computergeek1507/PB_16/Pi_Zero_24_Diff_SMD/README.md

# Copyright and Disclaimer
Copyright: Scott Hanson

This documentation describes Open Hardware and is licensed under the CERN Open Hardware Licence Version 2 - Strongly Reciprocal. (CERN-OHL-S)

You may redistribute and modify this documentation under the terms of the CERN OHL-S-v2 (https://ohwr.org/cern_ohl_s_v2.txt). This documentation is distributed WITHOUT ANY EXPRESS OR IMPLIED WARRANTY, INCLUDING OF MERCHANTABILITY, SATISFACTORY QUALITY AND FITNESS FOR A PARTICULAR PURPOSE. Please see the CERN OHL v2-S for applicable conditions

**Under CERN OHL-S-v2, derivative work must be publicy released as defined in subsection 3.3**

# Pi Zero 24 Diff

**Never Built or tested**

The Pi Zero 24 Diff is a surface mount(SMD) controller with 6 remote receiver port. A total of 24 pixel outputs. All the design files are open source and available on github.

## [Interactive BOM](https://computergeek1507.github.io/PB_16/Pi_Zero_24_Diff_SMD/bom/ibom)

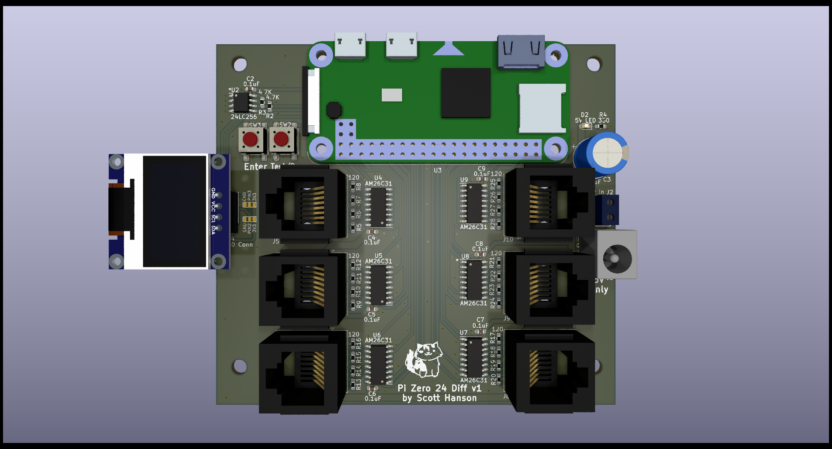
[picture p17: Pi_Zero_24_Diff_SMD/Pi_Zero_24_Diff.png]
Image of Pi Zero 24 Diff
