computergeek1507/PB_16/Pi_CM4_16_SMD/README.md

# Copyright and Disclaimer
Copyright: Scott Hanson

This documentation describes Open Hardware and is licensed under the CERN Open Hardware Licence Version 2 - Strongly Reciprocal. (CERN-OHL-S)

You may redistribute and modify this documentation under the terms of the CERN OHL-S-v2 (https://ohwr.org/cern_ohl_s_v2.txt). This documentation is distributed WITHOUT ANY EXPRESS OR IMPLIED WARRANTY, INCLUDING OF MERCHANTABILITY, SATISFACTORY QUALITY AND FITNESS FOR A PARTICULAR PURPOSE. Please see the CERN OHL v2-S for applicable conditions

**Under CERN OHL-S-v2, derivative work must be publicy released as defined in subsection 3.3**

# Pi CM4 16

**Never Built or tested**

The Pi CM4 16 is a surface mount(SMD) controller with 16 local pixel ports and one remote receiver port(4 remote ports). A total of 20 pixel outputs. All the design files are open source and available on github.

## [Interactive BOM](https://computergeek1507.github.io/PB_16/Pi_CM4_16_SMD/bom/ibom)

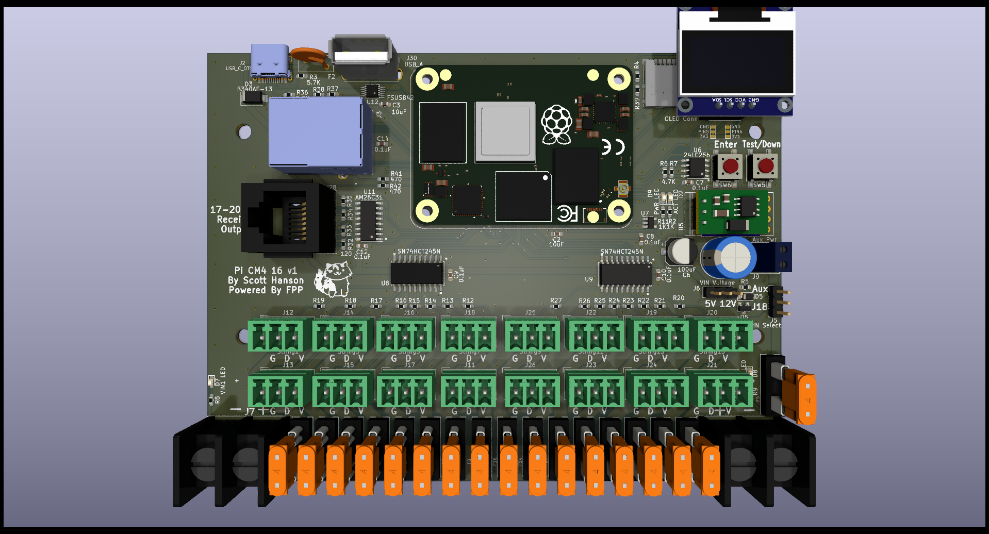
[picture p18: Pi_CM4_16_SMD/Pi_CM4_16.png]
Image of PB Pi Zero W 16
