computergeek1507/PB_16/Pi_Adapter/README.md

# Copyright and Disclaimer
Copyright: Scott Hanson

This documentation describes Open Hardware and is licensed under the CERN OHL v. 1.2.

You may redistribute and modify this documentation under the terms of the CERN OHL v.1.2. (http://ohwr.org/cernohl). This documentation is distributed WITHOUT ANY EXPRESS OR IMPLIED WARRANTY, INCLUDING OF MERCHANTABILITY, SATISFACTORY QUALITY AND FITNESS FOR A PARTICULAR PURPOSE. Please see the CERN OHL v.1.2 for applicable conditions

# Pi Expansion

Expansion breakout for a Raspberry Pi. Open source applications were used to create this PCB. [KiCad](http://kicad.org/) was used for the PCB design, and [LibreOffice](https://www.libreoffice.org/) for the documentation.

To order your own PCB upload the gerber.zip file to your favorite PCB manufacture of choice, I personally use [jlcpcb.com](https://jlcpcb.com/).

### Features
* 16 Port Expansion
* OLED Display header
* 2 pin GPIO Header for Push Button or Relay Support
* 5v Header

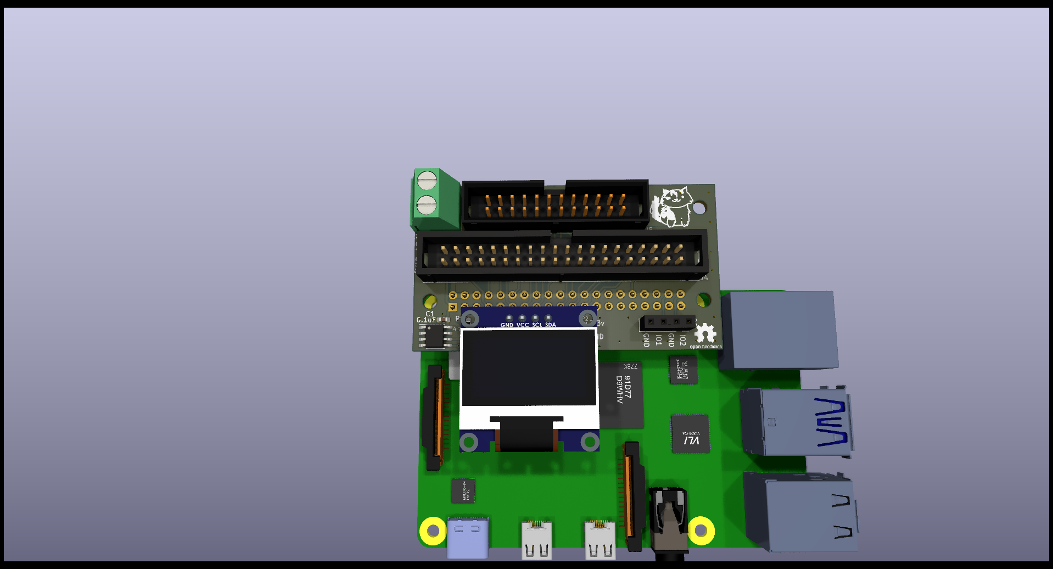
[picture p21: Pi_Adapter/Pi_Adapter.png]
Image of PI Adapter
