computergeek1507/PB_16/16_Expansion_SMD/README.md

# Copyright and Disclaimer
Copyright: Scott Hanson

This documentation describes Open Hardware and is licensed under the CERN Open Hardware License Version 2 - Strongly Reciprocal. (CERN-OHL-S)

You may redistribute and modify this documentation under the terms of the CERN OHL-S-v2 (https://ohwr.org/cern_ohl_s_v2.txt). This documentation is distributed WITHOUT ANY EXPRESS OR IMPLIED WARRANTY, INCLUDING OF MERCHANTABILITY, SATISFACTORY QUALITY AND FITNESS FOR A PARTICULAR PURPOSE. Please see the CERN OHL v2-S for applicable conditions

**Under CERN OHL-S-v2, derivative work must be publicly released as defined in subsection 3.3**

# 16 Expansion SMD

The "16 Expansion SMD" is a 16 port output board for the PB16.  All the design files are open source and available on github.

To order PCBs upload the "GERBER-PB_16.zip" file in the "jlcpcb\gerber" folder. Enable the SMD service, 'BOM-PB_16.csv' is the SMD BOM and 'POS-PB_16.csv' is the SMD CPL position file.

## [Part BOM](https://github.com/computergeek1507/PB_16/raw/master/16_Expansion_SMD/16_Expansion_BOM.ods)

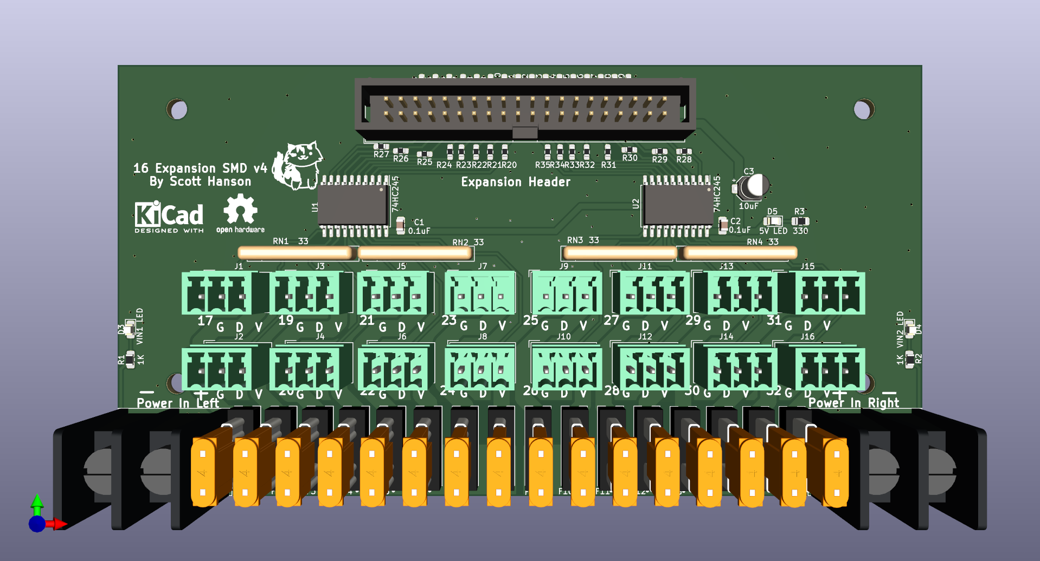
[picture p24: 16_Expansion_SMD/16_Expansion.png]
Image of 16 Expansion
