computergeek1507/PB_16/BBB_16_Expansion/README.md

# Copyright and Disclaimer
Copyright: Scott Hanson

This documentation describes Open Hardware and is licensed under the CERN Open Hardware License Version 2 - Strongly Reciprocal. (CERN-OHL-S)

You may redistribute and modify this documentation under the terms of the CERN OHL-S-v2 (https://ohwr.org/cern_ohl_s_v2.txt). This documentation is distributed WITHOUT ANY EXPRESS OR IMPLIED WARRANTY, INCLUDING OF MERCHANTABILITY, SATISFACTORY QUALITY AND FITNESS FOR A PARTICULAR PURPOSE. Please see the CERN OHL v2-S for applicable conditions

**Under CERN OHL-S-v2, derivative work must be publicly released as defined in subsection 3.3**

# BBB 16 Expansion

**This board is untested, use at your own risk**

The BBB16 Expansion is a version of the BBB16 for the Falcon v4 Expansion Boards. It can be used with three expansion boards, 48 outputs. The design is surface mount. All the design files are open source and available on github.

To order PCBs upload the "GERBER-BBB_16_Expansion.zip" file in the "jlcpcb\gerber" folder to jlcpcb.com. Enable the SMD service, 'BOM-BBB_16_Expansion.csv' is the SMD BOM and 'POS-BBB_16_Expansion.csv' is the SMD CPL position file.

## [Part BOM](https://github.com/computergeek1507/PB_16/raw/master/BBB_16_Expansion/BBB_16_Expansion_BOM.ods)

## [Interactive BOM](https://computergeek1507.github.io/PB_16/BBB_16_Expansion/bom/ibom)

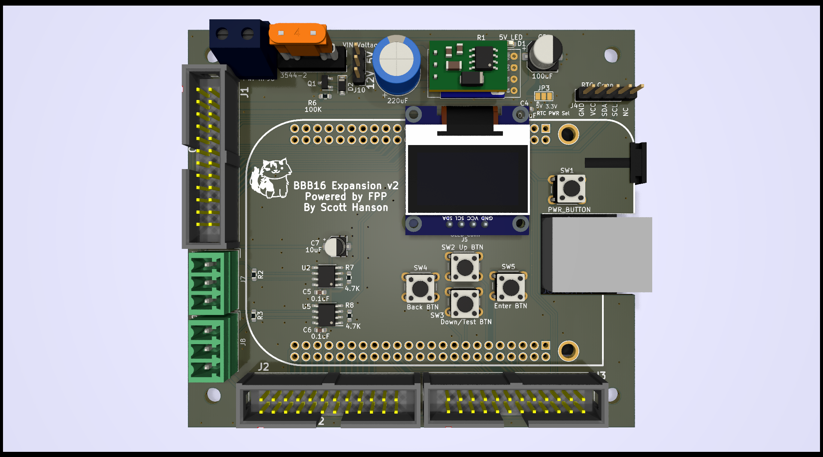
[picture p26: BBB_16_Expansion/BBB_16_Expansion.png]
Image of BBB16 Expansion Out
