computergeek1507/PB_16/BBB_16_Flex/README.md

# Copyright and Disclaimer
Copyright: Scott Hanson

This documentation describes Open Hardware and is licensed under the CERN Open Hardware License Version 2 - Strongly Reciprocal. (CERN-OHL-S)

You may redistribute and modify this documentation under the terms of the CERN OHL-S-v2 (https://ohwr.org/cern_ohl_s_v2.txt). This documentation is distributed WITHOUT ANY EXPRESS OR IMPLIED WARRANTY, INCLUDING OF MERCHANTABILITY, SATISFACTORY QUALITY AND FITNESS FOR A PARTICULAR PURPOSE. Please see the CERN OHL v2-S for applicable conditions

**Under CERN OHL-S-v2, derivative work must be publicly released as defined in subsection 3.3**

# BBB 16 Flex

The BBB16 Flex is a version of the BBB16 for the HolidayCoro Flex System. It can be used with all three flex boards, 48 outputs. The design is surface mount. All the design files are open source and available on github.

## [Part BOM](https://github.com/computergeek1507/PB_16/raw/master/BBB_16_Flex/BBB_16_Flex_BOM.ods)

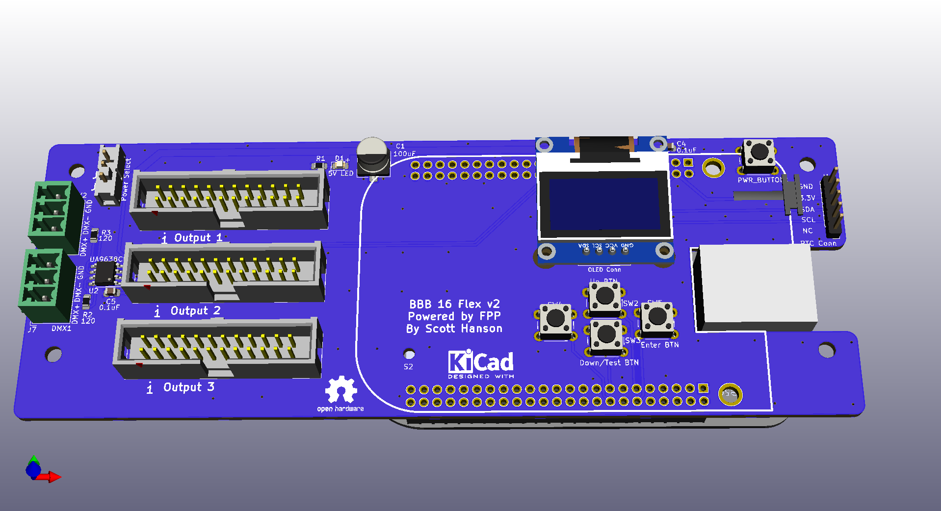
[picture p27: BBB_16_Flex/BBB_16_Flex.png]
Image of BBB16 Flex Out
