computergeek1507/PB_16/I2C_Breakout/README.md

# Copyright and Disclaimer
Copyright: Scott Hanson

This documentation describes Open Hardware and is licensed under the CERN Open Hardware License Version 2 - Strongly Reciprocal. (CERN-OHL-S)

You may redistribute and modify this documentation under the terms of the CERN OHL-S-v2 (https://ohwr.org/cern_ohl_s_v2.txt). This documentation is distributed WITHOUT ANY EXPRESS OR IMPLIED WARRANTY, INCLUDING OF MERCHANTABILITY, SATISFACTORY QUALITY AND FITNESS FOR A PARTICULAR PURPOSE. Please see the CERN OHL v2-S for applicable conditions

**Under CERN OHL-S-v2, derivative work must be publicly released as defined in subsection 3.3**

# PB 16 1.0e EEPROM Breakout

The PB16 EEPROM Breakout adds an EEPROM ship to the older PB16 version 1.0e controllers.  All the design files are open source and available on github.

## [Part BOM](https://github.com/computergeek1507/PB_16/raw/master/I2C_Breakout/I2C_Breakout_BOM.ods)

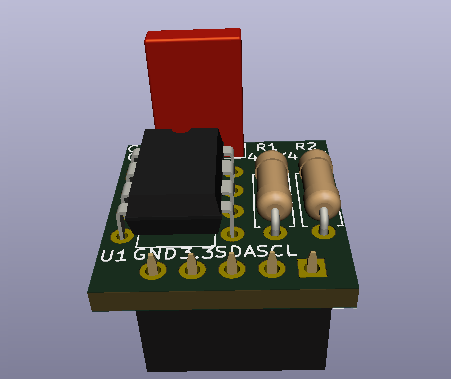
[picture p28: I2C_Breakout/I2C_Breakout.png]
Image of I2C Breakout
