computergeek1507/PB_16/PB_16_E682/README.md

# Copyright and Disclaimer
Copyright: Scott Hanson

This documentation describes Open Hardware and is licensed under the CERN Open Hardware License Version 2 - Strongly Reciprocal. (CERN-OHL-S)

You may redistribute and modify this documentation under the terms of the CERN OHL-S-v2 (https://ohwr.org/cern_ohl_s_v2.txt). This documentation is distributed WITHOUT ANY EXPRESS OR IMPLIED WARRANTY, INCLUDING OF MERCHANTABILITY, SATISFACTORY QUALITY AND FITNESS FOR A PARTICULAR PURPOSE. Please see the CERN OHL v2-S for applicable conditions

**Under CERN OHL-S-v2, derivative work must be publicly released as defined in subsection 3.3**

# PB 16 E682

**This is a proof of concept, not designed for extended use**

The PB16 E682 is an "Upgrade" for the Sandevice E682. The E682's Parallax Propeller microcontroller is replaced with a PocketBeagle runnig FPP. It runs a full Linux operating system with ethernet, WIFI and audio supported over the USB port. The PCB is powered by the Aux Power Connector J17 5V out from the E682. It can run in standalone, or be used with other controllers/devices. There is also an optional [serial breakout board](../PB_16_E682_Serial/README.md) for DMX capability. All the design files are open source and available on github.

## [Part BOM](https://github.com/computergeek1507/PB_16/raw/master/PB_16_E682/PB_16_E682_BOM.ods)

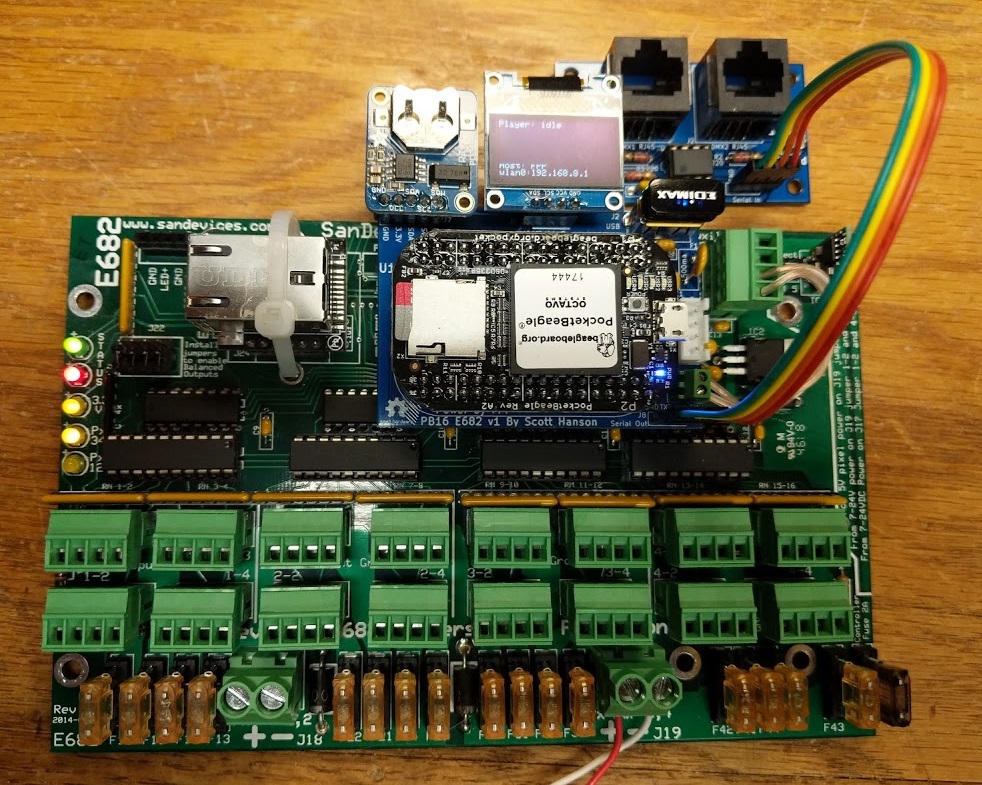
[picture p29: PB_16_E682/IMG_20190930_213630.jpg]
Image of E682 with PB16
