computergeek1507/PB_16/Pwr_Diff_Breakout/README.md

# Copyright and Disclaimer
Copyright: Scott Hanson

This documentation describes Open Hardware and is licensed under the CERN Open Hardware License Version 2 - Strongly Reciprocal. (CERN-OHL-S)

You may redistribute and modify this documentation under the terms of the CERN OHL-S-v2 (https://ohwr.org/cern_ohl_s_v2.txt). This documentation is distributed WITHOUT ANY EXPRESS OR IMPLIED WARRANTY, INCLUDING OF MERCHANTABILITY, SATISFACTORY QUALITY AND FITNESS FOR A PARTICULAR PURPOSE. Please see the CERN OHL v2-S for applicable conditions

**Under CERN OHL-S-v2, derivative work must be publicly released as defined in subsection 3.3**

# Pwr Diff Breakout

The "Pwr Diff Breakout" board has four single Differental Reciever outputs with power on two CAT5 pins. It pugs in to a 4 output differental output. It works with the "Single_Receiver_Out". All the design files are open source and available on github.

## [Part BOM](https://github.com/computergeek1507/PB_16/raw/master/Pwr_Diff_Breakout/Pwr_Diff_Breakout_BOM.ods)

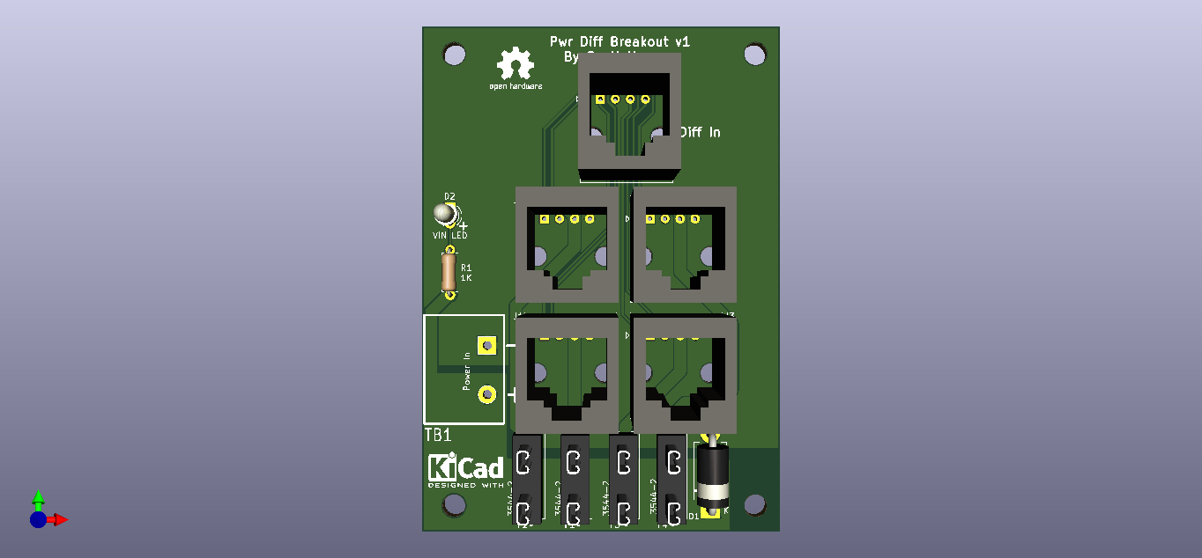
[picture p30: Pwr_Diff_Breakout/Pwr_Diff_Breakout.png]
Image of Pwr_Diff_Breakout
