computergeek1507/PB_16/SM_Receiver_Out_SMD/README.md

# Copyright and Disclaimer
Copyright: Scott Hanson

This documentation describes Open Hardware and is licensed under the CERN Open Hardware License Version 2 - Strongly Reciprocal. (CERN-OHL-S)

You may redistribute and modify this documentation under the terms of the CERN OHL-S-v2 (https://ohwr.org/cern_ohl_s_v2.txt). This documentation is distributed WITHOUT ANY EXPRESS OR IMPLIED WARRANTY, INCLUDING OF MERCHANTABILITY, SATISFACTORY QUALITY AND FITNESS FOR A PARTICULAR PURPOSE. Please see the CERN OHL v2-S for applicable conditions

**Under CERN OHL-S-v2, derivative work must be publicly released as defined in subsection 3.3**

# Receiver Out SMD

The "SM Receiver Out SMD" is a 4 port "Smart" Differential Receiver output board for the PB16. The Firmware is a work in progress and only works in "Dumb" mode. This design is surface mount based and is harder to solder. All the design files are open source and available on github.

**WIP** Work in progress, firmware and PCB may change.

<!---To order PCBs upload the gerber.zip file to jlcpcb.com. Enable the SMD service, 'Receiver_Out_SMD.csv' is the SMD BOM and 'Receiver_Out-all-pos.csv' is the SMD CPL position file.
--->
## [Part BOM](https://github.com/computergeek1507/PB_16/raw/master/SM_Receiver_Out_SMD/Receiver_Out_BOM.ods)

## [Interactive BOM](https://computergeek1507.github.io/PB_16/SM_Receiver_Out_SMD/bom/ibom)

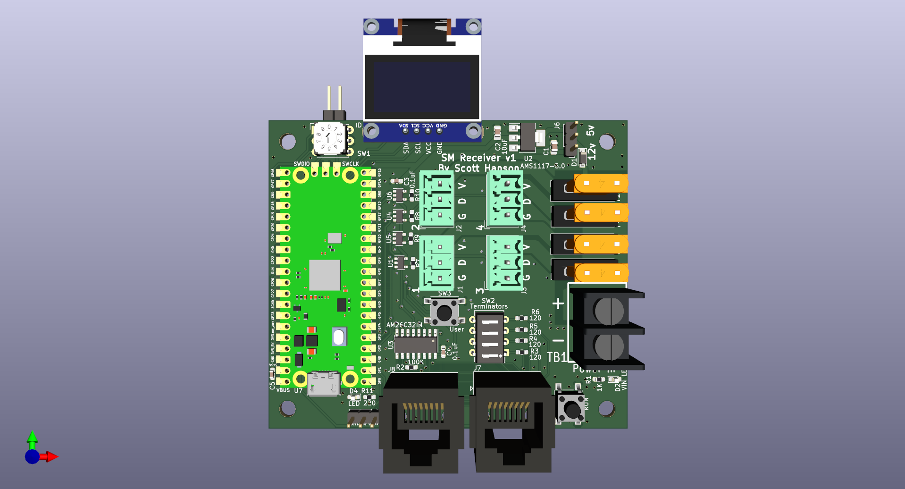
[picture p33: SM_Receiver_Out_SMD/Receiver_Out.png]
Image of Receiver Out
--->
