computergeek1507/PB_16/16_Expansion_24pin/README.md

# Copyright and Disclaimer
Copyright: Scott Hanson

This documentation describes Open Hardware and is licensed under the CERN Open Hardware License Version 2 - Strongly Reciprocal. (CERN-OHL-S)

You may redistribute and modify this documentation under the terms of the CERN OHL-S-v2 (https://ohwr.org/cern_ohl_s_v2.txt). This documentation is distributed WITHOUT ANY EXPRESS OR IMPLIED WARRANTY, INCLUDING OF MERCHANTABILITY, SATISFACTORY QUALITY AND FITNESS FOR A PARTICULAR PURPOSE. Please see the CERN OHL v2-S for applicable conditions

**Under CERN OHL-S-v2, derivative work must be publicly released as defined in subsection 3.3**

# 16 Expansion 24pin

The "16 Expansion 24pin" is a 16 port output board for the BBB16v2.  All the design files are open source and available on github.

## [Part BOM](https://github.com/computergeek1507/PB_16/raw/master/16_Expansion_24pin/16_Expansion_BOM.ods)

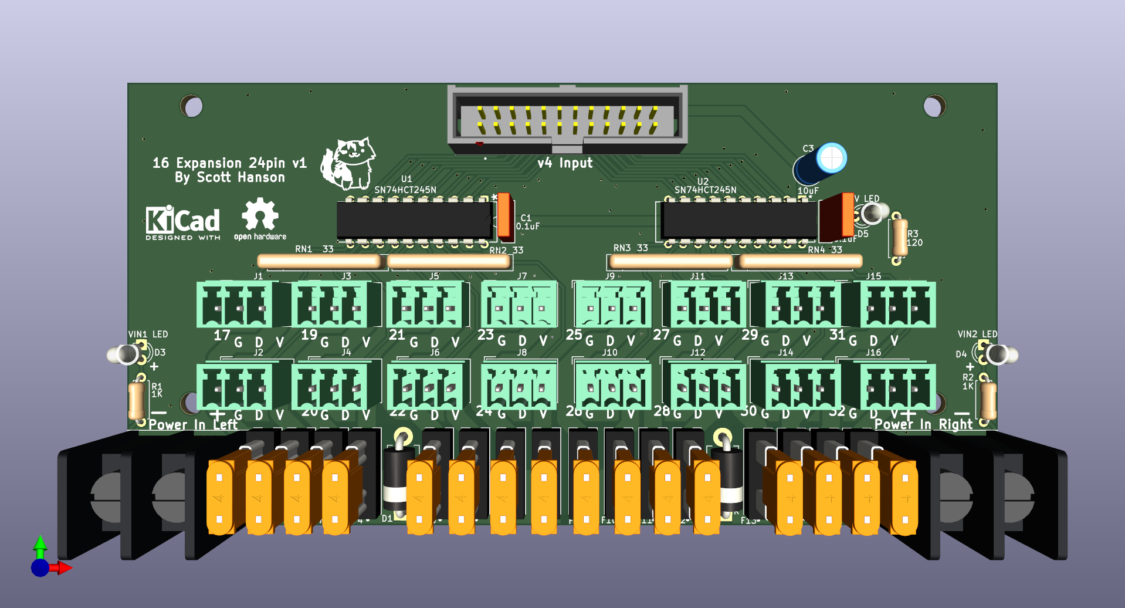
[picture p44: 16_Expansion_24pin/16_Expansion.png]
Image of 16 Expansion
