computergeek1507/PB_16/Multi_Expansion/README.md

# Copyright and Disclaimer
Copyright: Scott Hanson

This documentation describes Open Hardware and is licensed under the CERN Open Hardware License Version 2 - Strongly Reciprocal. (CERN-OHL-S)

You may redistribute and modify this documentation under the terms of the CERN OHL-S-v2 (https://ohwr.org/cern_ohl_s_v2.txt). This documentation is distributed WITHOUT ANY EXPRESS OR IMPLIED WARRANTY, INCLUDING OF MERCHANTABILITY, SATISFACTORY QUALITY AND FITNESS FOR A PARTICULAR PURPOSE. Please see the CERN OHL v2-S for applicable conditions

**Under CERN OHL-S-v2, derivative work must be publicly released as defined in subsection 3.3**

# Multi Expansion

The Multi Expansion is a dual Differental Reciever output board with eight local pixel outputs for the PB16. It works with Smart and Dumb Differental Recievers. All the design files are open source and available on github.

## [Part BOM](https://github.com/computergeek1507/PB_16/raw/master/Multi_Expansion/Multi_Expansion.ods)

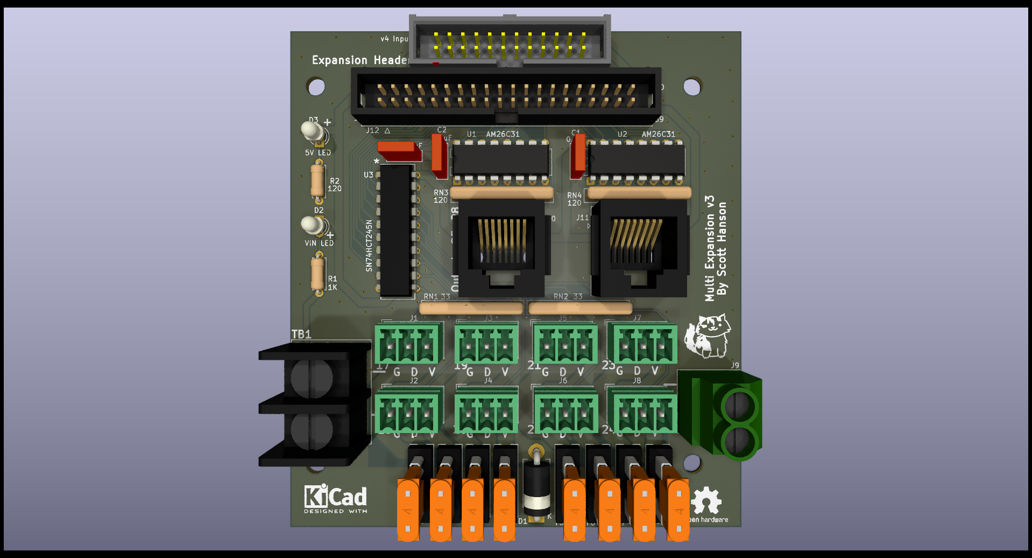
[picture p46: Multi_Expansion/Multi_Expansion.png]
Image of Multi Expansion


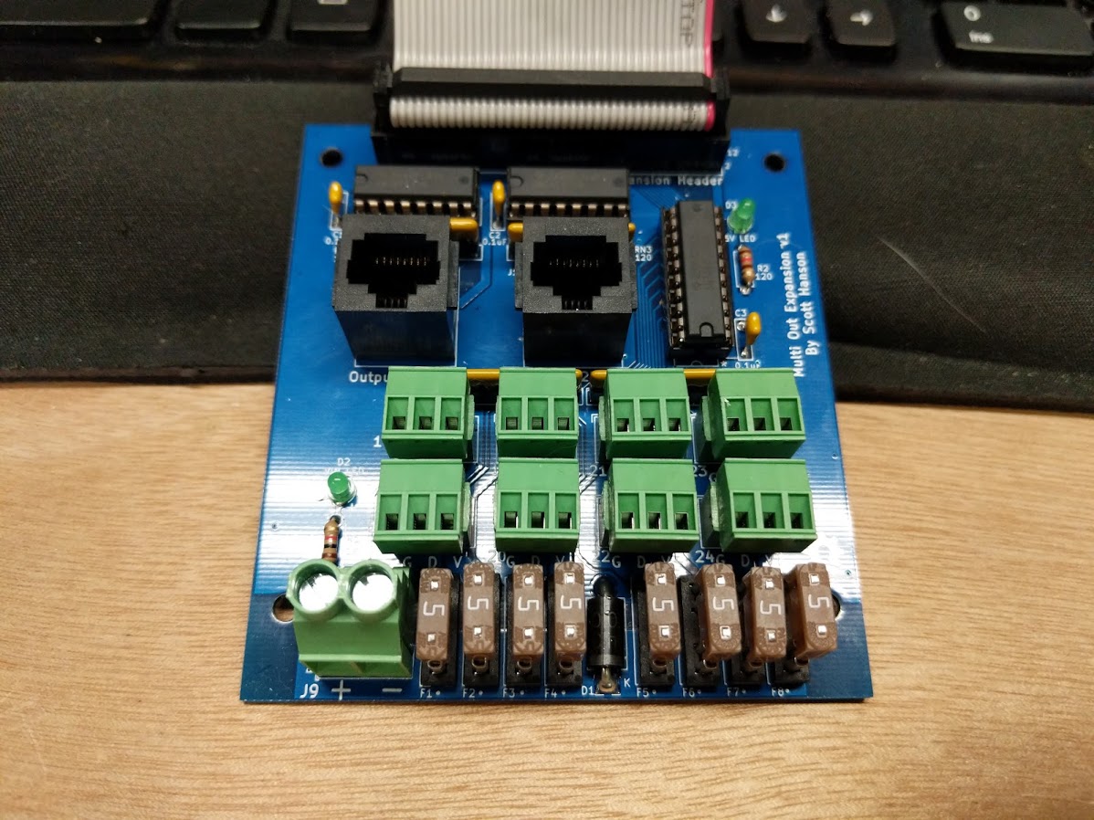
[picture p47: Multi_Expansion/IMG_20191203_202821.jpg]
Real Image of PMulti Expansion
