computergeek1507/PB_16/PB_16_E682_Serial/README.md

# Copyright and Disclaimer
Copyright: Scott Hanson

This documentation describes Open Hardware and is licensed under the CERN Open Hardware License Version 2 - Strongly Reciprocal. (CERN-OHL-S)

You may redistribute and modify this documentation under the terms of the CERN OHL-S-v2 (https://ohwr.org/cern_ohl_s_v2.txt). This documentation is distributed WITHOUT ANY EXPRESS OR IMPLIED WARRANTY, INCLUDING OF MERCHANTABILITY, SATISFACTORY QUALITY AND FITNESS FOR A PARTICULAR PURPOSE. Please see the CERN OHL v2-S for applicable conditions

**Under CERN OHL-S-v2, derivative work must be publicly released as defined in subsection 3.3**

# PB 16 E682 Serial

The PB16 E682 Serial is the Serial breakout for the PB16 E682. The serial breakout board supports DMX protocol with DMX, LOR, and Renard pinouts. All the design files are open source and available on github.

## [Part BOM](https://github.com/computergeek1507/PB_16/raw/master/PB_16_E682_Serial/PB_16_E682_Serial_BOM.ods)

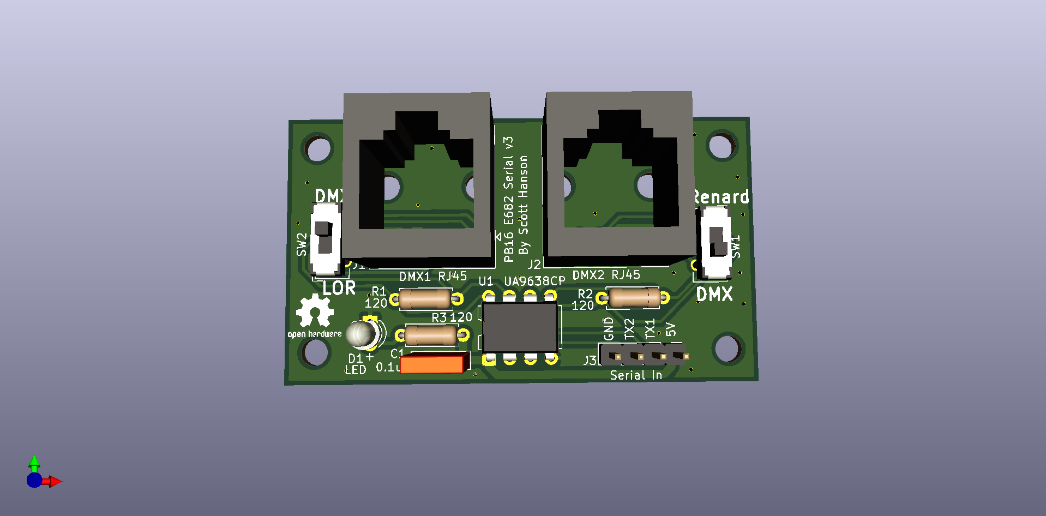
[picture p48: PB_16_E682_Serial/PB_16_E682_Serial.png]
Image of E682 with PB16
