computergeek1507/PB_16/Quad_Diff_Out/README.md

# Copyright and Disclaimer
Copyright: Scott Hanson

This documentation describes Open Hardware and is licensed under the CERN Open Hardware License Version 2 - Strongly Reciprocal. (CERN-OHL-S)

You may redistribute and modify this documentation under the terms of the CERN OHL-S-v2 (https://ohwr.org/cern_ohl_s_v2.txt). This documentation is distributed WITHOUT ANY EXPRESS OR IMPLIED WARRANTY, INCLUDING OF MERCHANTABILITY, SATISFACTORY QUALITY AND FITNESS FOR A PARTICULAR PURPOSE. Please see the CERN OHL v2-S for applicable conditions

**Under CERN OHL-S-v2, derivative work must be publicly released as defined in subsection 3.3**

# Quad Diff Out

The Quad Diff Out is a single Differental Reciever output board for the PB16. It works with Smart and Dumb Differental Recievers. All the design files are open source and available on github.

## [Part BOM](https://github.com/computergeek1507/PB_16/raw/master/Quad_Diff_Out/Quad_Diff_Out_BOM.ods)

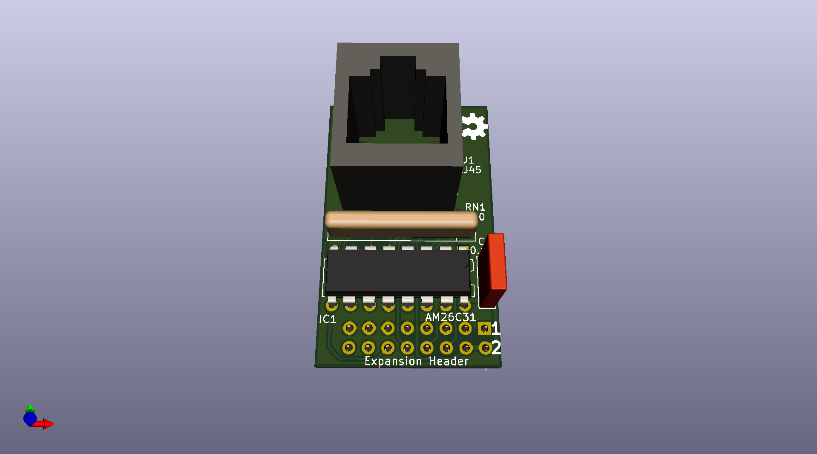
[picture p53: Quad_Diff_Out/Quad_Diff_Out.png]
Image of Quad Diff Out


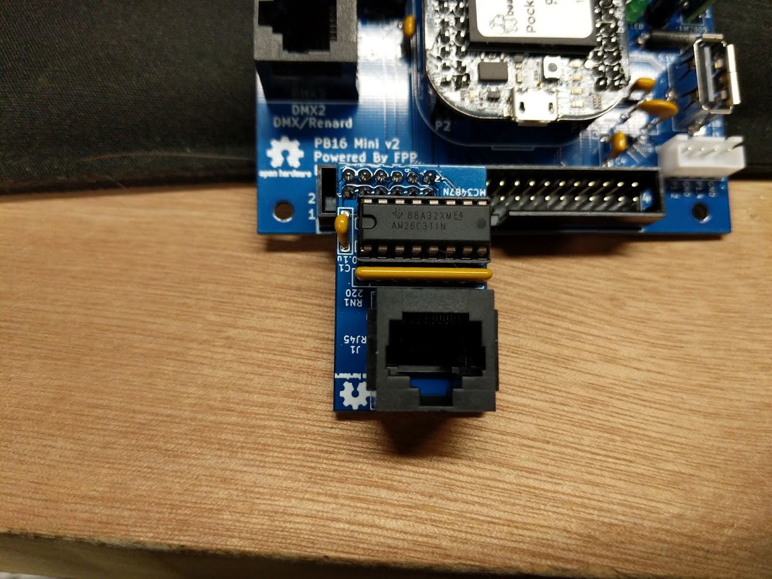
[picture p54: Quad_Diff_Out/IMG_20191203_205121.jpg]
Real Image of Quad Diff Out
