computergeek1507/PB_16/PB_16_E682/PB_16_E682.png

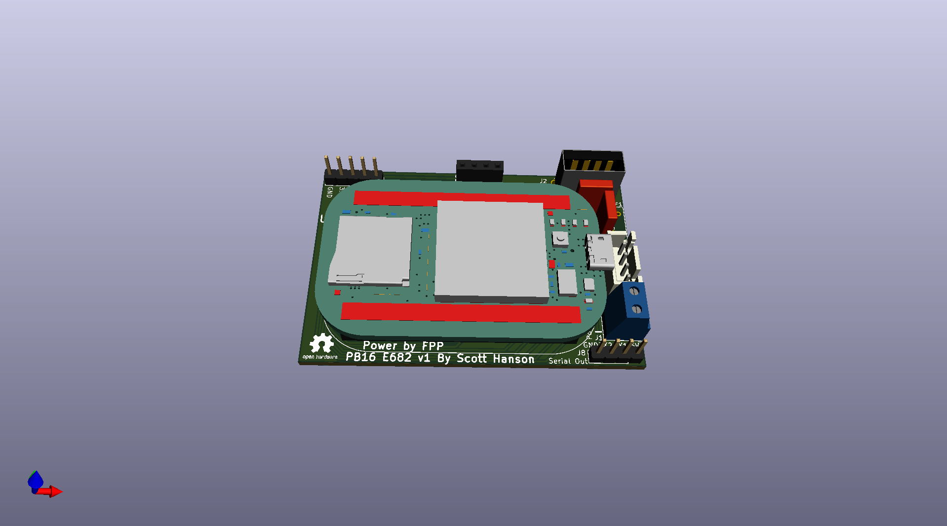
PB_16_E682/PB_16_E682.png
