computergeek1507/PB_16/PB_16v1/PB_16.png

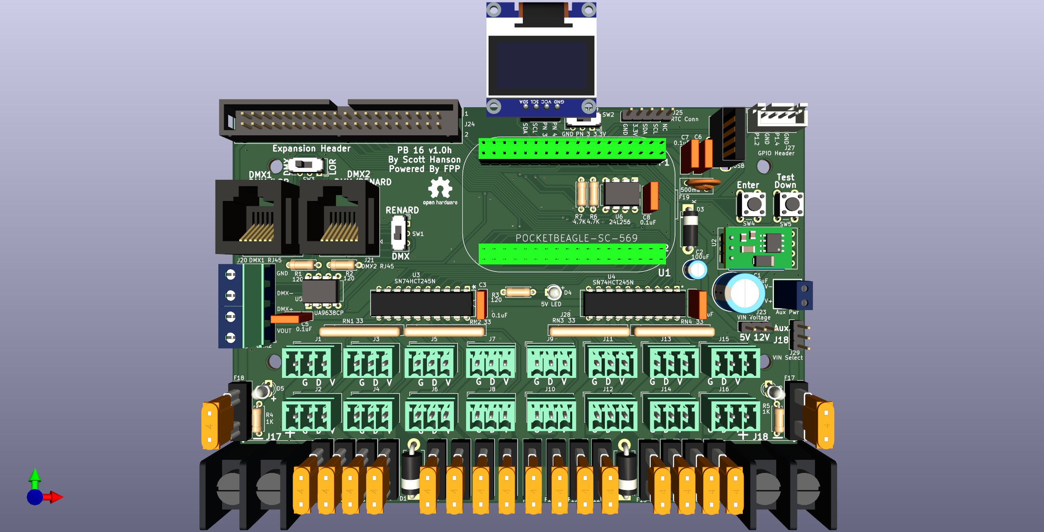
PB_16v1/PB_16.png
