computergeek1507/PB_16/PB_16v1/PB_16_labels.png

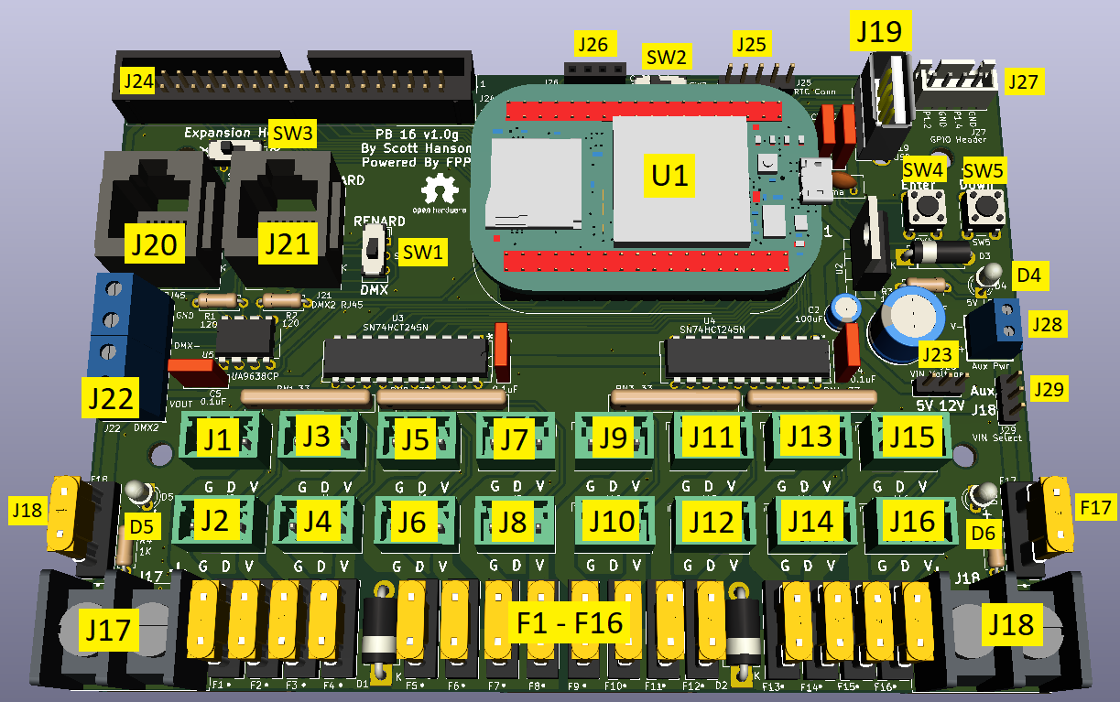
PB_16v1/PB_16_labels.png
