computergeek1507/PB_16/Receiver_Out_SMD/Receiver_Out.png

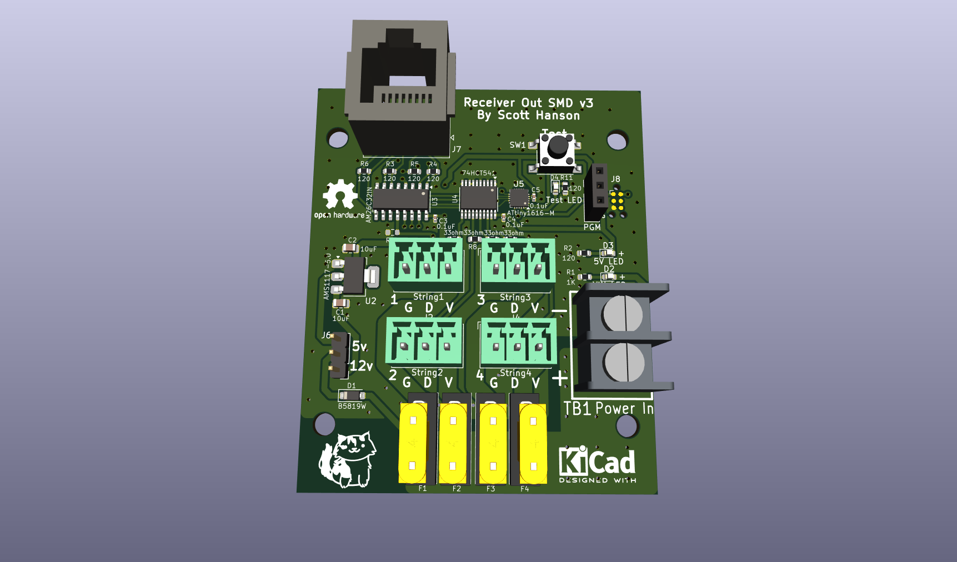
Receiver_Out_SMD/Receiver_Out.png
