computergeek1507/PB_16/WingsStation/WingsStation.png

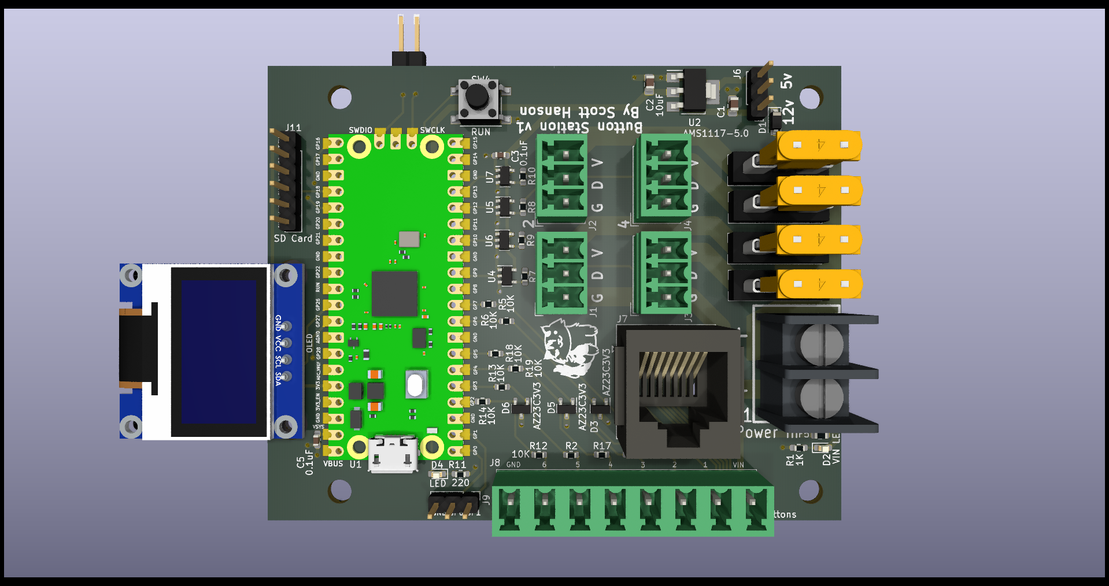
WingsStation/WingsStation.png
