computergeek1507/PB_16/Four_Out/Four_Out_BOM.ods

Qty | Reference(s) | Value | Digi-Key_PN | MPN
1 | C3 | 0.1uF | 478-7336-1-ND | SR215C104KARTR1
1 | D1 | SB5100-T | SB5100DICT-ND | SB5100-T
2 | D2, D3 | VIN LED, 5V LED | 754-1217-ND | WP3A8GD
4 | F1, F2, F3, F4 | 3544-2 | 36-3544-2-ND | 3544-2
4 | J1-J4 | String1-String8 | 277-5737-ND | 1843619
4 | J1-J4 Plugs | Pixel Plugs | ED10555-ND | OSTTJ0311530
1 | J5 | Power In | ED2675-ND | OSTT7020150
1 | J6 | Expansion Header | S9175-ND | SBH11-PBPC-D20-ST-BK
1 | J7 | V4 Expansion Header | ED10525-ND | 302-S241
1 | R1 | 1K | CF14JT1K00CT-ND | CF14JT1K00
1 | R2 | 120 | CF14JT120RCT-ND | CF14JT120R
1 | RN1 | 33 | 4608X-2-330LF-ND | 4608X-102-330LF
1 | RN1 Sockets | Socket 8POS 0.1 | 1212-1097-ND | 310-87-108-41-001101
1 | U1 | SN74AHC125N | 296-4531-5-ND | SN74AHC125N
1 | U1 Sockets | DIP Socket 14POS | AE9989-ND | A 14-LC-TT
4 | F1, F2, F3, F4 Fuses | Fuse 5A Blade Mini | F989-ND | 0297005.WXNV
1 | TP1 | Power In | A98472-ND | 4DB-P108-02
