computergeek1507/PB_16/Diff_Expansion/Diff_Expansion_BOM.ods

Qty | Reference(s) | Value | Digi-Key_PN | MPN
4 | C1, C2, C3, C4 | 0.1uF | 478-7336-1-ND | SR215C104KARTR1
1 | D1 | 5V LED | 754-1217-ND | WP3A8GD
4 | J1, J2, J3, J4 | RJ45 | AE10392-ND | A-2014-2-4-R
1 | J5 | Expansion Header | S9175-ND | SBH11-PBPC-D20-ST-BK
1 | J6 | V4 Expansion Header | ED10525-ND | 302-S241
1 | R1 | 120 | CF14JT120RCT-ND | CF14JT120R
4 | RN1, RN2, RN3, RN4 | 120 | 4608X-2-121LF-ND | 4608X-102-121LF
4 | RN1, RN2, RN3, RN4 Sockets | Socket 8POS 0.1 | 1212-1097-ND | 310-87-108-41-001101
4 | U1, U2, U3, U4 | AM26C31 | 296-6785-5-ND | AM26C31IN
4 | U1, U2, U3, U4 Sockets | DIP Socket 16POS | AE9992-ND | A 16-LC-TT
 |  |  |  |  | 1 | J9 | Power In | ED2675-ND | OSTT7020150 | 1 | J9 | Power In | ED2675-ND | OSTT7020150 | 1 | J9 | Power In | ED2675-ND | OSTT7020150 | 1 | J9 | Power In | ED2675-ND | OSTT7020150 | 1 | J9 | Power In | ED2675-ND | OSTT7020150 | 1 | J9 | Power In | ED2675-ND | OSTT7020150 | 1 | J9 | Power In | ED2675-ND | OSTT7020150
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
