computergeek1507/PB_16/BBB_16_Flex/BBB_16_Flex_BOM.ods

qty | Comment | Designator | Digi-Key_PN | MPN | LCSC
1 | 100uF | C1 | 493-2105-1-ND | UWX1C101MCL1GB | C3345
3 | 0.1uF | C3,C4,C5 | 1276-1007-1-ND | CL21F104ZBCNNNC | C49678
1 | 5V LED | D1 | 160-1423-1-ND | LTST-C171GKT | C2297
1 | Output 1 | J1 | ED10525-ND | 302-S241
1 | Output 2 | J2 | ED10525-ND | 302-S241
1 | Output 3 | J3 | ED10525-ND | 302-S241
1 | RTC Conn | J4 | 732-5318-ND | 61300511121
1 | OLED Conn | J5 | S7002-ND | PPTC041LFBN-RC
1 | DMX1 | J7 | 277-5737-ND | 1843619
1 | DMX2 | J8 | 277-5737-ND | 1843619
1 | Power Select | J9 | 732-5316-ND | 61300311121
1 | 1K | R1 | 311-1.00KCRCT-ND | RC0805FR-071KL | C17513
2 | 120 | R3,R2 | 311-120ARCT-ND | RC0805JR-07120RL | C17437
2 | 4.7K | R4,R5 | 311-4.7KARCT-ND | RC0805JR-074K7L | C17673
1 | PWR_BUTTON | SW1 | 450-1650-ND | 1825910-6
1 | Up BTN | SW2 | 450-1650-ND | 1825910-6
1 | Down/Test BTN | SW3 | 450-1650-ND | 1825910-6
1 | Left BTN | SW4 | 450-1650-ND | 1825910-6
1 | Right BTN | SW5 | 450-1650-ND | 1825910-6
2 | BEAGLEBONEBLACK | U1 | S2012EC-23-ND
1 | UA9638CP | U2 | 296-15058-1-ND | UA9638CDR | C435812
1 | 24LC256 | U3 | 24LC256T-I/SNCT-ND | 24LC256T-I/SN | C6482
