computergeek1507/PB_16/Smart_Reciever_Max_Exp_Pico/Smart_Reciever_Max_BOM.ods

Qty | Reference(s) | Value | Digi-Key_PN | MPN
1 | C1 | 100uF | 1189-1148-ND | 16ZLH100MEFC5X11
1 | C2 | 10uF | 493-1103-ND | UVR1H100MDD
6 | C3, C4, C5, C6, C7, C8 | 0.1uF | 478-7336-1-ND | SR215C104KARTR1
1 | D1, D2 | VIN LED, Stat LED | 754-1217-ND | WP3A8GD
1 | F1 | Fuse | RXEF050-2HFCT-ND | RXEF050-2
1 | J1 | Power In | 277-1236-ND | 1729018
1 | J2 | Expansion Header | S9175-ND | SBH11-PBPC-D20-ST-BK
1 | J3 | RJ45 | AE10392-ND | A-2014-2-4-R
1 | J4 | VIN_Voltage | 732-5316-ND | 61300311121
1 | R1 | 1K | CF14JT1K00CT-ND | CF14JT1K00
1 | R2 | 120 | CF14JT120RCT-ND | CF14JT120R
1 | RN1 | 120 | 4608X-2-121LF-ND | 4608X-102-121LF
1 | SW1 | USR | 450-1650-ND | 1825910-6
1 | SW2 | RUN | 450-1650-ND | 1825910-6
1 | U1 | L7805 | MC7805CTGOS-ND | MC7805CTG
1 | U2 | raspberrypi-pico-module | 2648-SC0915CT-ND | SC0915
4 | U3, U4, U5, U7 | 74LS125 | 296-4531-5-ND | SN74AHC125N
1 | U6 | AM26C32IN | 296-6789-5-ND | AM26C32IN
