computergeek1507/PB_16/Multi_Expansion/Multi_Expansion_BOM.ods

Qty | Reference(s) | Value | Digi-Key_PN | MPN
3 | C1, C2, C3 | 0.1uF | 478-7336-1-ND | SR215C104KARTR1
1 | D1 | SB5100-T | SB5100DICT-ND | SB5100-T
2 | D2, D3 | VIN LED, 5V LED | 754-1217-ND | WP3A8GD
8 | F1, F2, F3, F4, F5, F6, F7, F8 | 3544-2 | 36-3544-2-ND | 3544-2
8 | J1-J8 | String1-String8 | 277-5737-ND | 1843619
8 | J1-J8 Plugs | Pixel Plugs | ED10555-ND | OSTTJ0311530
1 | J9 | Power In | ED2675-ND | OSTT7020150
2 | J10, J11 | RJ45 | AE10392-ND | A-2014-2-4-R
1 | J12 | Expansion Header | S9175-ND | SBH11-PBPC-D20-ST-BK
1 | R1 | 1K | CF14JT1K00CT-ND | CF14JT1K00
1 | R2 | 120 | CF14JT120RCT-ND | CF14JT120R
2 | RN1, RN2 | 150 | 4608X-2-151LF-ND | 4608X-102-151LF
2 | RN3, RN4 | 33 | 4608X-2-330LF-ND | 4608X-102-330LF
4 | RN1, RN2, RN3, RN4 Sockets | Socket 8POS 0.1 | 1212-1097-ND | 310-87-108-41-001101
2 | U1, U2 | AM26C31 | 296-6785-5-ND | AM26C31IN
2 | U1, U2 Sockets | DIP Socket 16POS | AE9992-ND | A 16-LC-TT
1 | U3 | SN74HCT245N | 296-1612-5-ND | SN74HCT245N
1 | U3 Sockets | DIP Socket 20POS | AE9998-ND | A 20-LC-TT
8 | F1-F8 Fuses | Fuse 5A Blade Mini | F989-ND | 0297005.WXNV
1 | TP1 | Power In | ED2953-ND | OSTYK51102030 | 1 | J9 | Power In | ED2675-ND | OSTT7020150 | 1 | J9 | Power In | ED2675-ND | OSTT7020150 | 1 | J9 | Power In | ED2675-ND | OSTT7020150 | 1 | J9 | Power In | ED2675-ND | OSTT7020150 | 1 | J9 | Power In | ED2675-ND | OSTT7020150 | 1 | J9 | Power In | ED2675-ND | OSTT7020150 | 1 | J9 | Power In | ED2675-ND | OSTT7020150
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
