computergeek1507/PB_16/Single_Receiver_Out/Single_Receiver_Out_BOM.ods

Qty | Reference(s) | Value | Digi-Key_PN | MPN
1 | C1 | 10uF | 445-FK26X7R1E106K-ND | FK26X7R1E106K
3 | C2, C3, C4 | 0.1uF | 478-7336-1-ND | SR215C104KARTR1
1 | J1 | RJ45 | AE10392-ND | A-2014-2-4-R
1 | J2 | String1-String4 | 277-5737-ND | 1843619
1 | J2 | Pixel Plugs | ED10555-ND | OSTTJ0311530
1 | J3 | 5V JMP | 732-5315-ND | 61300211121
1 | R1 | 120 | CF14JT120RCT-ND | CF14JT120R
1 | R2 | 33 | CF14JT33R0CT-ND | CF14JT33R0
1 | U1 | SN75176AP | 296-1737-5-ND | SN75176AP
1 | U1 Sockets | DIP Socket 8POS | AE9986-ND | A 08-LC-TT
1 | U2 | L78L05_TO92 | MC78L05BP-APMSCT-ND | MC78L05BP-AP
