computergeek1507/PB_16/PB_16_Flex/PB_16_Flex_BOM.ods

Collated Components:
 | Qty | Reference(s) | Value | Digi-Key_PN | MPN
 | 1 | C1 | 100uF | 1189-1148-ND | 16ZLH100MEFC5X11
 | 4 | C2, C3, C4. C5 | 0.1uF | 478-7336-1-ND | SR215C104KARTR1
 | 1 | D1 | 5V LED | 754-1217-ND | WP3A8GD
 | 1 | F1 | 500ma | RXEF050-2HFCT-ND | RXEF050-2
 | 1 | J1 | USB | 380-1412-ND | SS-52100-001
 | 1 | J2 | OLED Conn | S7002-ND | PPTC041LFBN-RC
 | 1 | J3 | GPIO Header | 455-2249-ND | B4B-XH-A(LF)(SN)
 | 1 | J4 | RTC Conn | 732-5318-ND | 61300511121
 | 2 | J5/J6 | Output 1/Output 2 | ED10525-ND | 302-S241
 | 2 | J7, J8 | DMX1/DMX2 | 277-5737-ND | 1843619
 | 2 | J7, J8 Plugs | DMX1/DMX2 Plugs | ED10555-ND | OSTTJ0311530
 | 1 | J9 | Output Select | 732-5316-ND | 61300311121
 | 3 | R1, R2, R3 | 120 | CF14JT120RCT-ND | CF14JT120R
 | 2 | 4.7K | 4.7K | CF14JT4K70CT-ND | CF14JT4K70
 | 1 | SW1 | OLED Select | 401-2001-ND | JS202011CQN
 | 2 | SW2, SW2 | Enter BTN/Down BTN | 450-1650-ND | 1825910-6
 | 1 | U1 | POCKETBEAGLE-SC-569 | POCKETBEAGLE-SC-569-ND | POCKETBEAGLE-SC-569
 | 1 | U2 | UA9638CP | 296-15059-5-ND | UA9638CP
 | 1 | U3 | 24LC256 | 1219-1052-ND | FT24C256A-UDR-B
 | 2 | U1 P1 & P2 Headers | CONN HEADER VERT 36POS 2.54MM | 732-5309-ND | 61303621121
 | 2 | U1 P1 & P2 Sockets | CONN HDR 36POS 0.1 GOLD PCB | S7121-ND | PPPC182LFBN-RC
 | 2 | U2/U3 Socket | CONN IC DIP SOCKET 8POS TIN | AE9986-ND | A 08-LC-TT
 | 1 | J9 Power Jumper | CONN JUMPER SHORTING .100" GOLD | S9341-ND | NPC02SXON-RC
