computergeek1507/PB_16/Quad_Diff_Out/Quad_Diff_Out_BOM.ods

Individual Components:
 | Qty | Reference(s) | Value | Digikey PN
 | 1 | C1 | 0.1uF | 478-7336-1-ND
 | 1 | IC1 | AM26C31 | 296-6785-5-ND
 | 1 | J1 | RJ45 | AE10392-ND
 | 1 | J2 | Expansion Header | S7111-ND
 | 1 | RN1 | 120 | 4608X-2-121LF-ND
 | 1 | IC1 Socket | DIP SOCKET 16POS | AE9992-ND
 | 1 | RN1 Sockets | Socket 8POS 0.1 | 1212-1097-ND
