computergeek1507/PB_16/PB_16_E682/PB_16_E682_BOM.ods

Qty | Reference(s) | Value | Digi-Key_PN | MPN
3 | C1, C2, C3 | 0.1uF | 478-7336-1-ND | SR215C104KARTR1
1 | F1 | 500ma | RXEF050-2HFCT-ND | RXEF050-2
1 | J1 | Power In | 277-1947-ND | 1727010
1 | J2 | USB | WM8672-ND | 1050570001
2 | J3, J4 | E682 | 732-5329-ND | 61302011121
1 | J5 | OLED Conn | S7002-ND | PPTC041LFBN-RC
1 | J6 | GPIO Header | 455-2249-ND | B4B-XH-A(LF)(SN)
1 | J7 | RTC Conn | 732-5318-ND | 61300511121
1 | J8 | Serial Out | 732-5317-ND | 61300411121
1 | U1 | POCKETBEAGLE-SC-569 | POCKETBEAGLE-SC-569-ND | POCKETBEAGLE-SC-569
2 | R1, R2 | 4.7K | CF14JT4K70CT-ND | CF14JT4K70
1 | U2 | 24LC256 | 1219-1052-ND | FT24C256A-UDR-B
1 | U2 Socket | CONN IC DIP SOCKET 8POS TIN | AE9986-ND | A 08-LC-TT
2 | U1 P1 & P2 Headers | CONN HEADER VERT 36POS 2.54MM | 732-5309-ND | 61303621121
2 | U1 P1 & P2 Sockets | CONN HDR 36POS 0.1 GOLD PCB | S7121-ND | PPPC182LFBN-RC
