computergeek1507/PB_16/I2C_Breakout/I2C_Breakout_BOM.ods

Qty | Reference(s) | Value | Digi-Key_PN | MPN
1 | C1 | 0.1uF | 478-7336-1-ND | SR215C104KARTR1
2 | R1, R2 | 4.7K | CF14JT4K70CT-ND | CF14JT4K70
1 | U1 | 24LC256 | 1219-1052-ND | FT24C256A-UDR-B
1 | U1 Socket | CONN IC DIP SOCKET 8POS TIN | AE9986-ND | A 08-LC-TT
