computergeek1507/PB_16/Exp_Filter/jlcpcb/assembly/BOM-Exp_Filter.csv

Comment | Designator | Footprint | LCSC
10K | R1,R10,R11,R12,R13,R14,R15,R16,R2,R3,R4,R5,R6,R7,R8,R9 | R_0603_1608Metric_Pad0.98x0.95mm_HandSolder | C25804
Expansion Header | J1 | PinSocket_2x20_P2.54mm_Vertical | C50982
