computergeek1507/PB_16/PB_16_E682_Serial/PB_16_E682_Serial_BOM.ods

Collated Components:
 | Qty | Reference(s) | Value | Digi-Key_PN | MPN
 | 1 | C1 | 0.1uF | 478-7336-1-ND | SR215C104KARTR1
 | 1 | D1 | LED | 732-5008-ND | 151031VS06000
 | 2 | J1, J2 | DMX1/DMX2 RJ45 | AE10392-ND | A-2014-2-4-R
 | 1 | J3 | Serial In | 732-5317-ND | 61300411121
 | 3 | R1, R2, R3 | 120 | CF14JT120RCT-ND | CF14JT120R
 | 2 | SW1, SW2 | LOR DMX Renard Select | 401-2001-ND | JS202011CQN
 | 1 | U1 | UA9638CP | 296-15059-5-ND | UA9638CP
