computergeek1507/PB_16/Wally_Tree_SMD/Wally_Tree.pdf

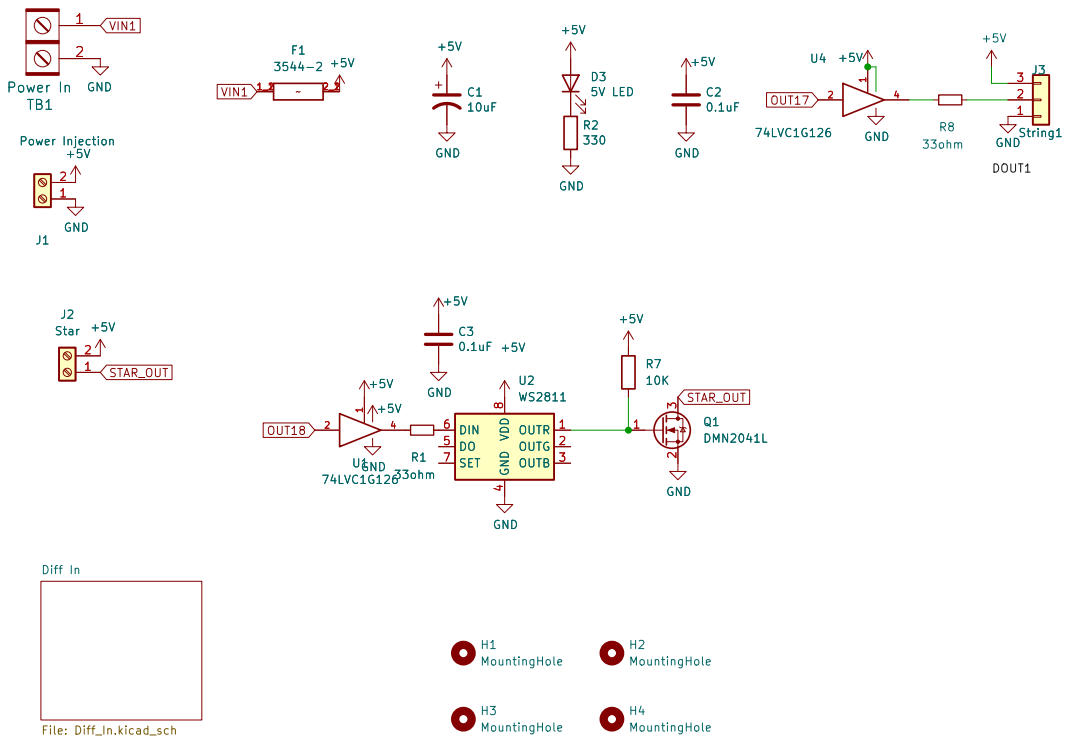
[picture p110: page 1]

4 DO 5 DIN 6 SET 7 VDD

Id: 1/2 Title: Wally Tree Driver

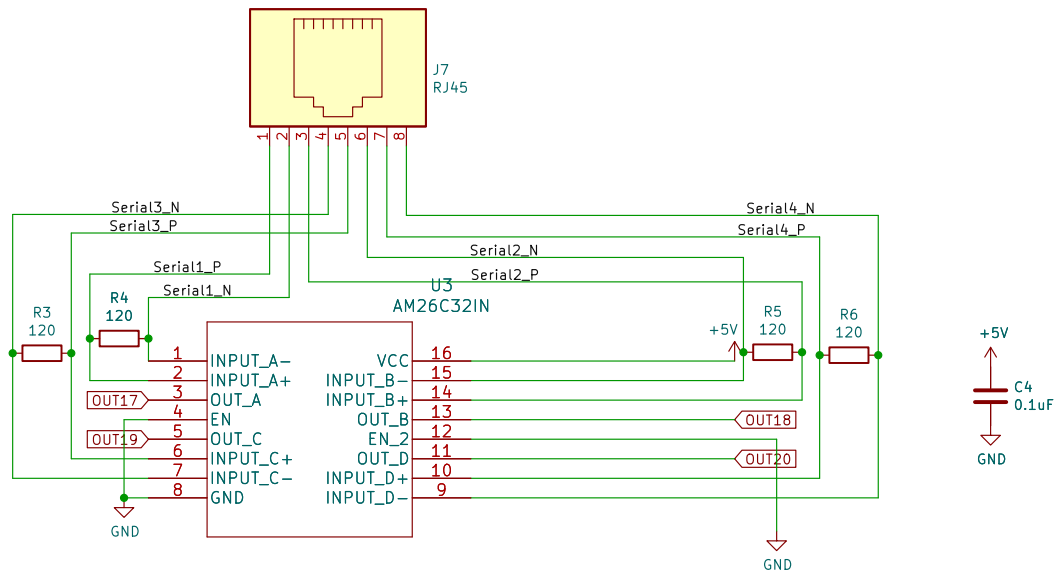
[picture p111: page 2]

File: Diff_In.kicad_sch Sheet: /Diff In/ Scott Hanson R5

Serial3_P | Serial4_P

Serial1_P

Id: 2/2 Title: Wally Tree Driver
