computergeek1507/PB_16/Input_Adapter/Input_Adapter.pdf

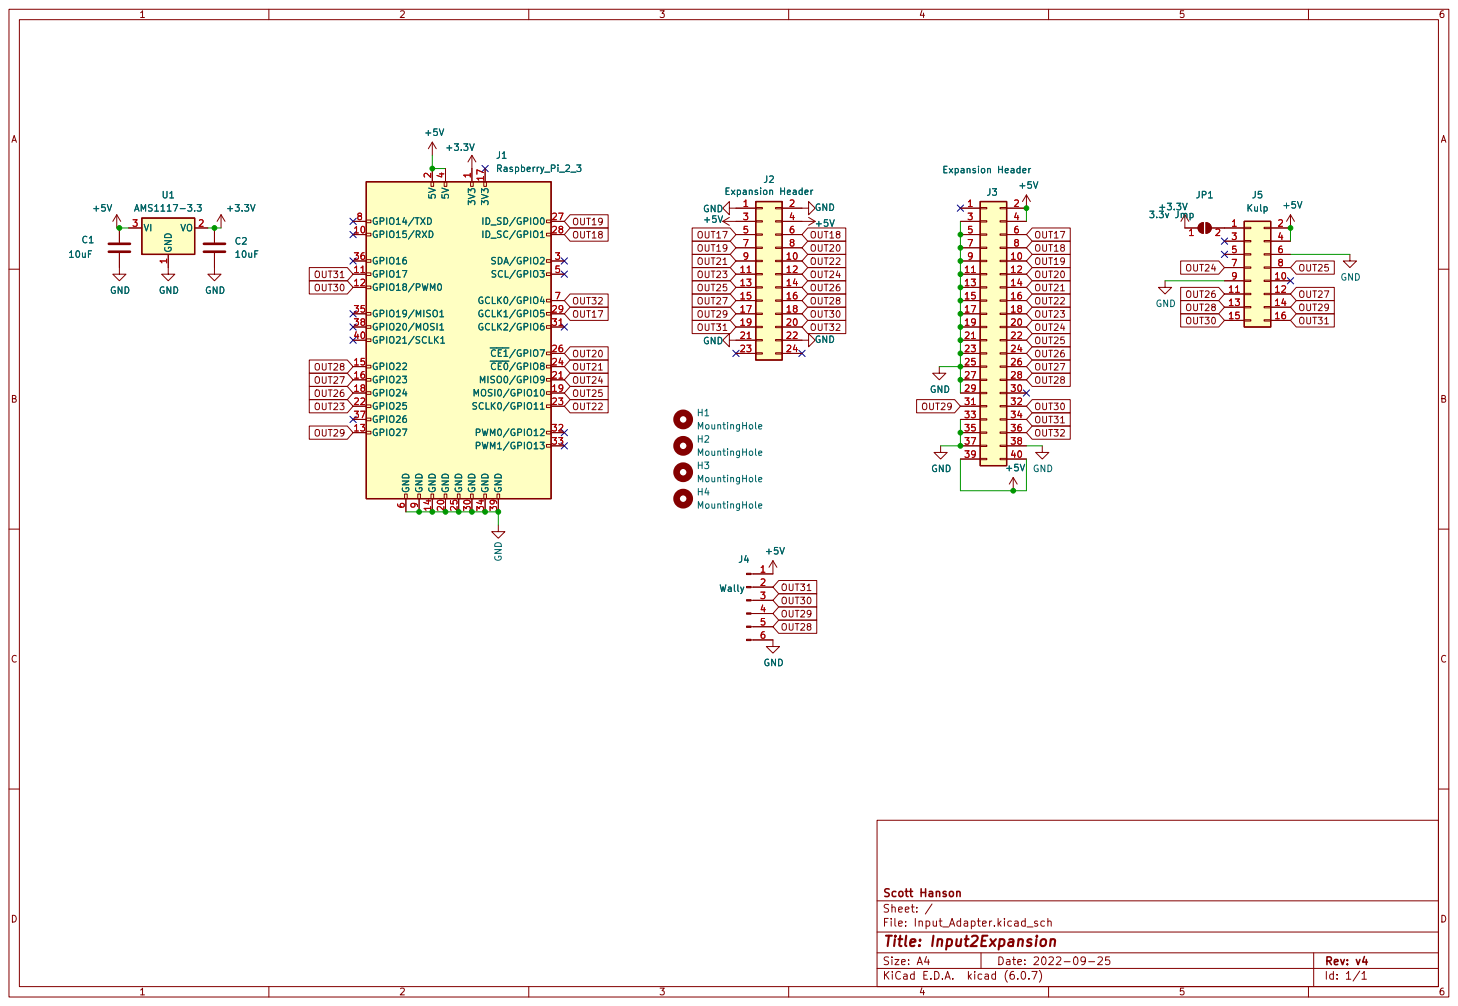
[picture p112: page 1]

J2 Expansion Header GND GND

5 5 | 6 6
7 7 | 8 8
9 | 10 10
11 11 | 12 12
13 13 | 14 14
15 15 | 16 16
17 17 | 18 18
19 19 | 20 20

File: Input_Adapter.kicad_sch Sheet: / Scott Hanson
