computergeek1507/PB_16/Pi_CM4_16_SMD/Pi_CM4_16.pdf

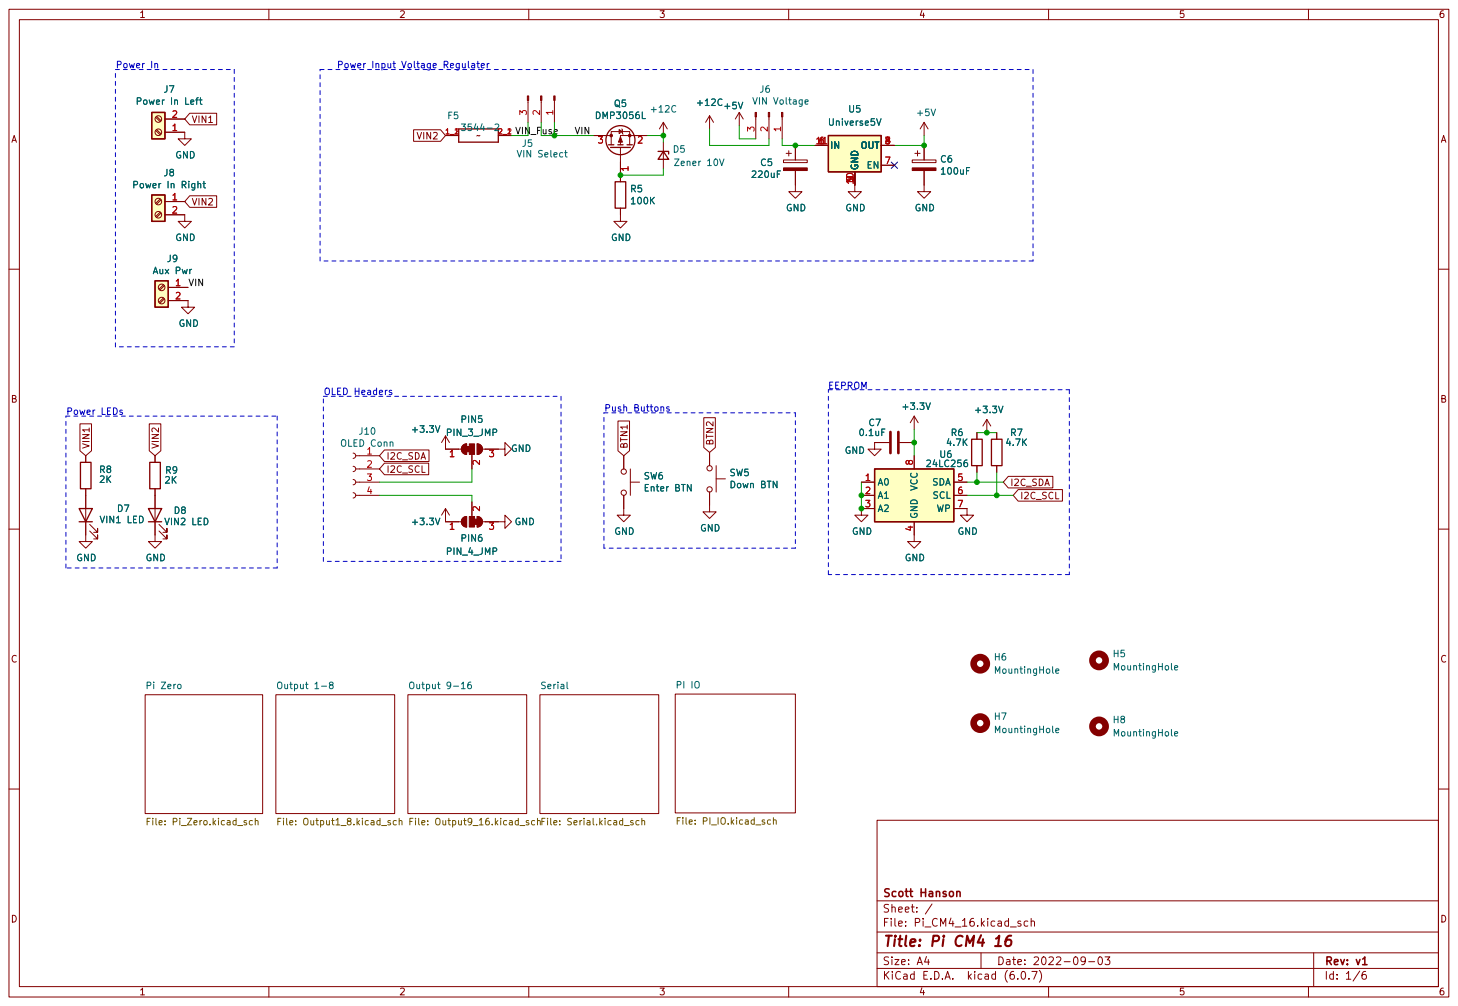
[picture p113: page 1]

J7 Power In Left GND GND GND
2GND GND GND
VIN1

4 SDA 5 SCL 6 WP 7 VCC

File: Pi_CM4_16.kicad_sch Sheet: / Scott Hanson

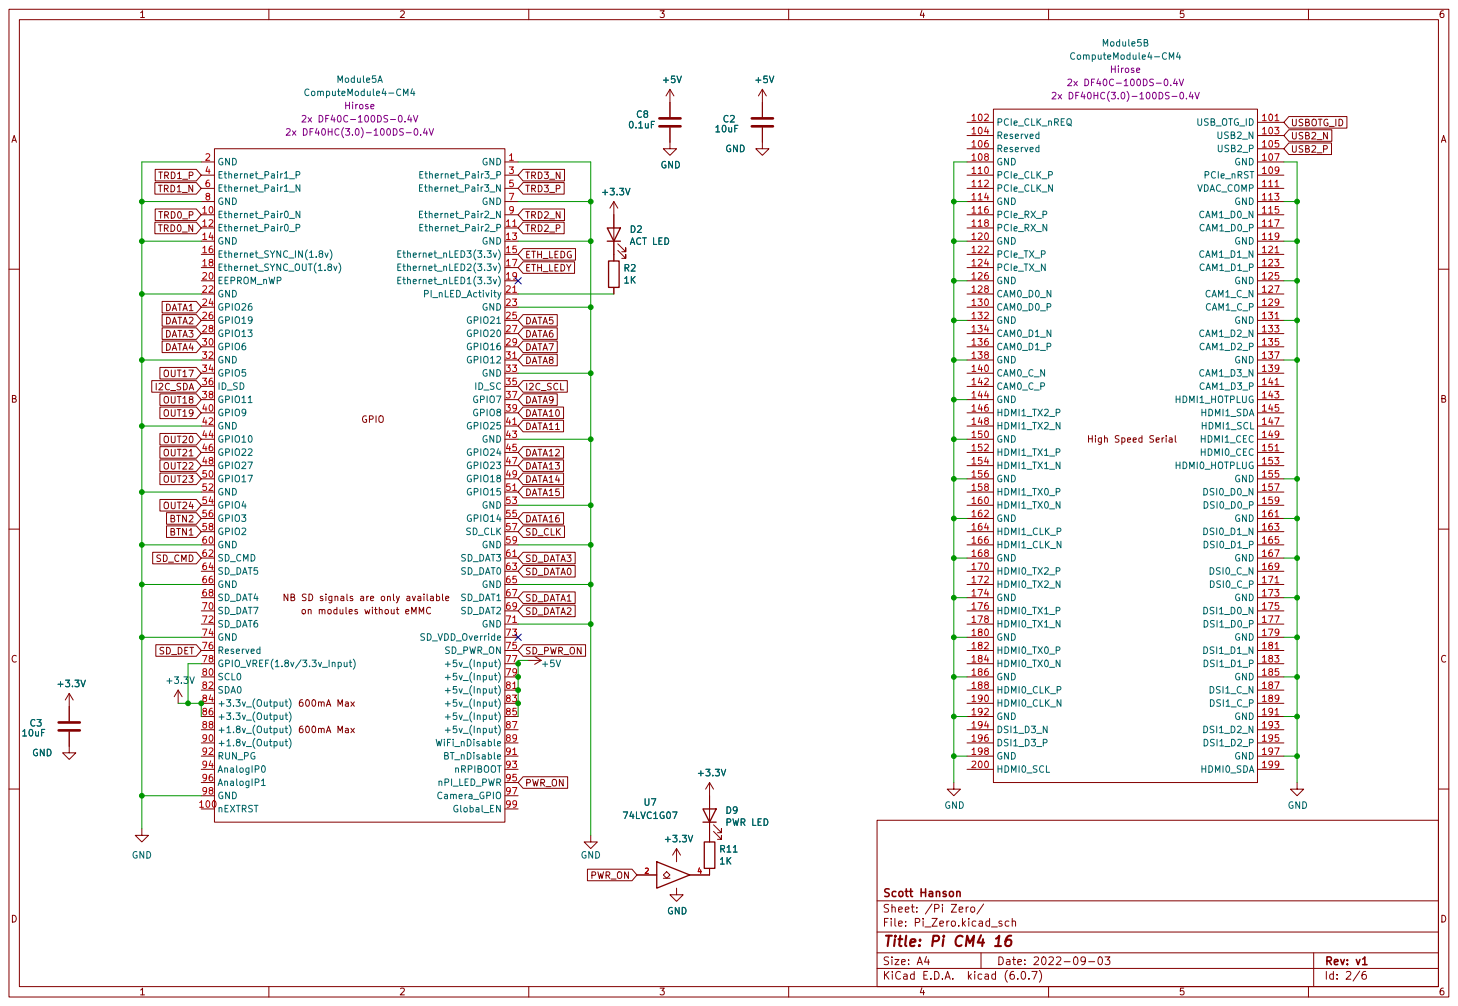
[picture p114: page 2]

TRD1_P TRD1_N | TRD3_N TRD3_P

TRD0_P | TRD2_N TRD2_P

600mA Max 600mA Max NB SD signals are only available

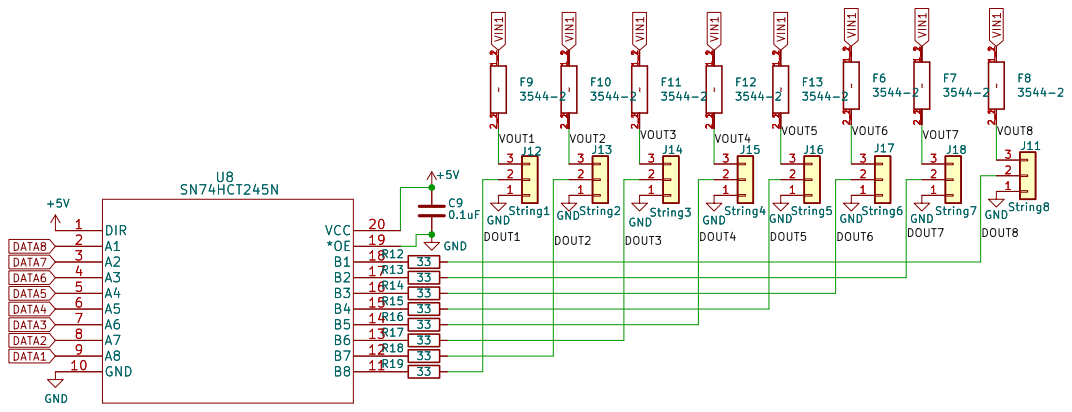
[picture p115: page 3]

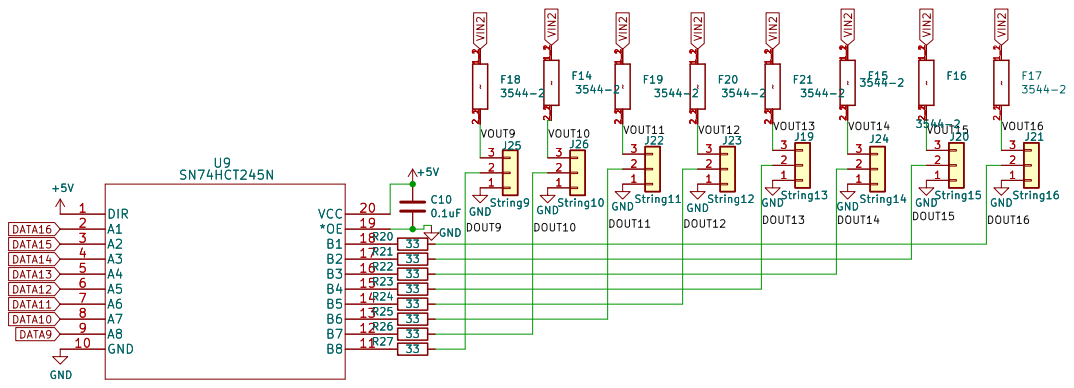
[picture p116: page 4]

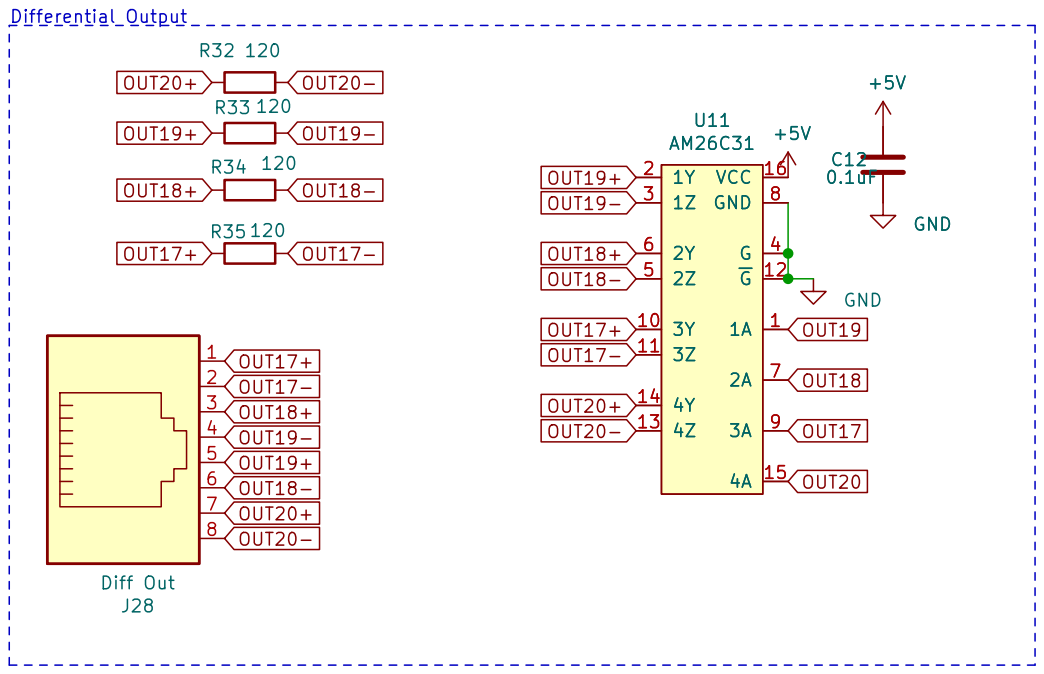
[picture p117: page 5]

File: Serial.kicad_sch Sheet: /Serial/ Scott Hanson C12

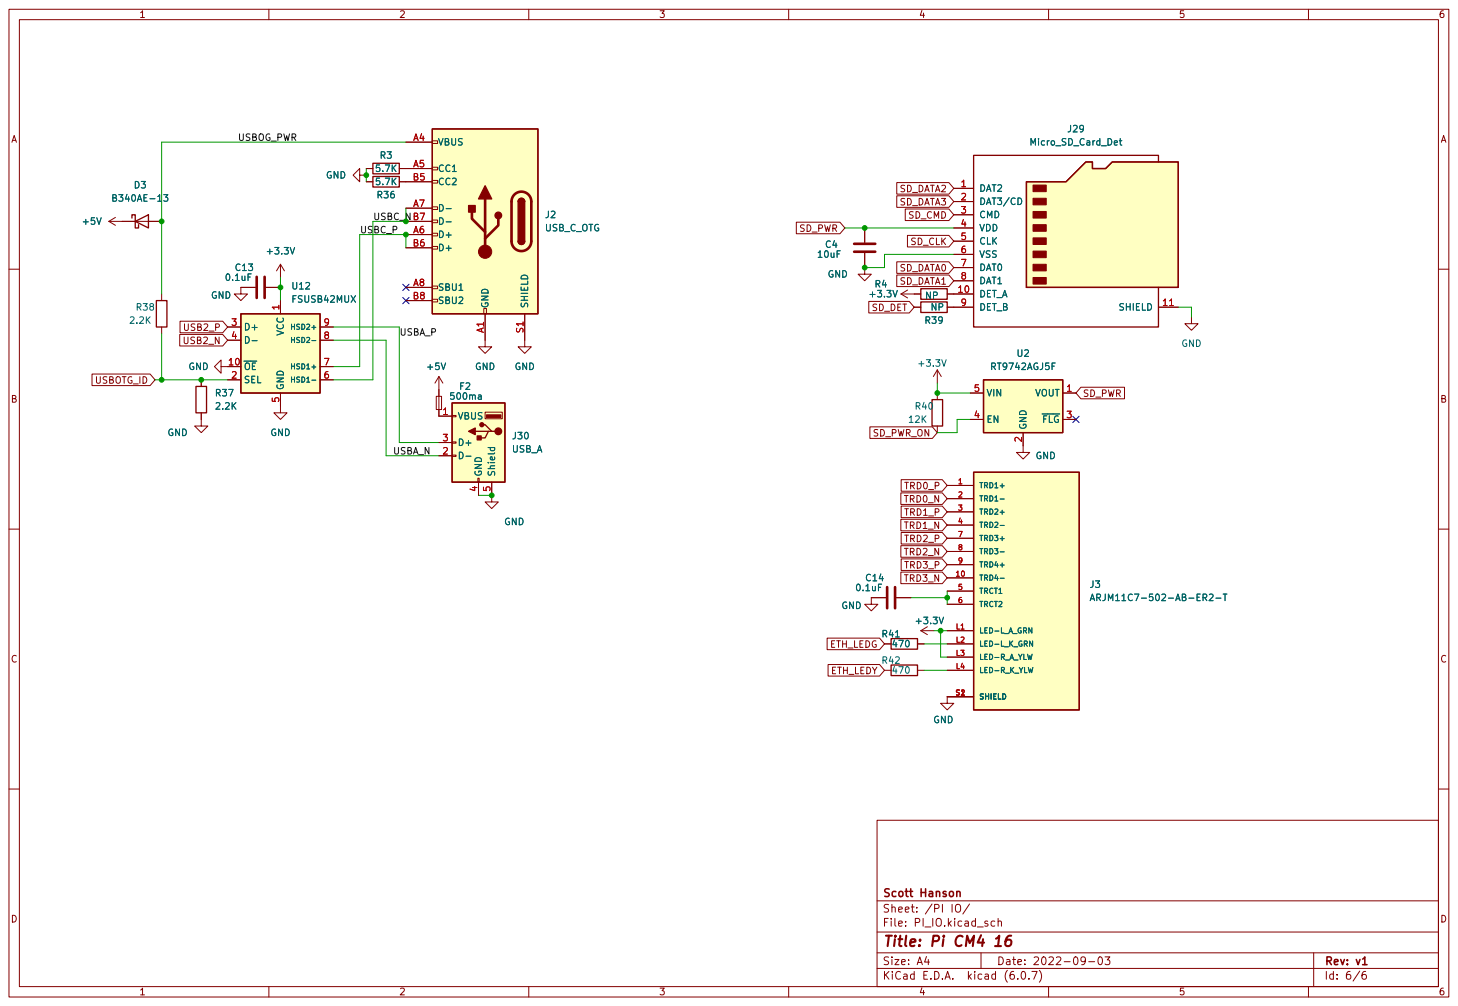
[picture p118: page 6]

File: PI_IO.kicad_sch Sheet: /PI IO/ Scott Hanson
