computergeek1507/PB_16/Pi_Zero_Expansion_SMD/Pi_Zero_Expansion.pdf

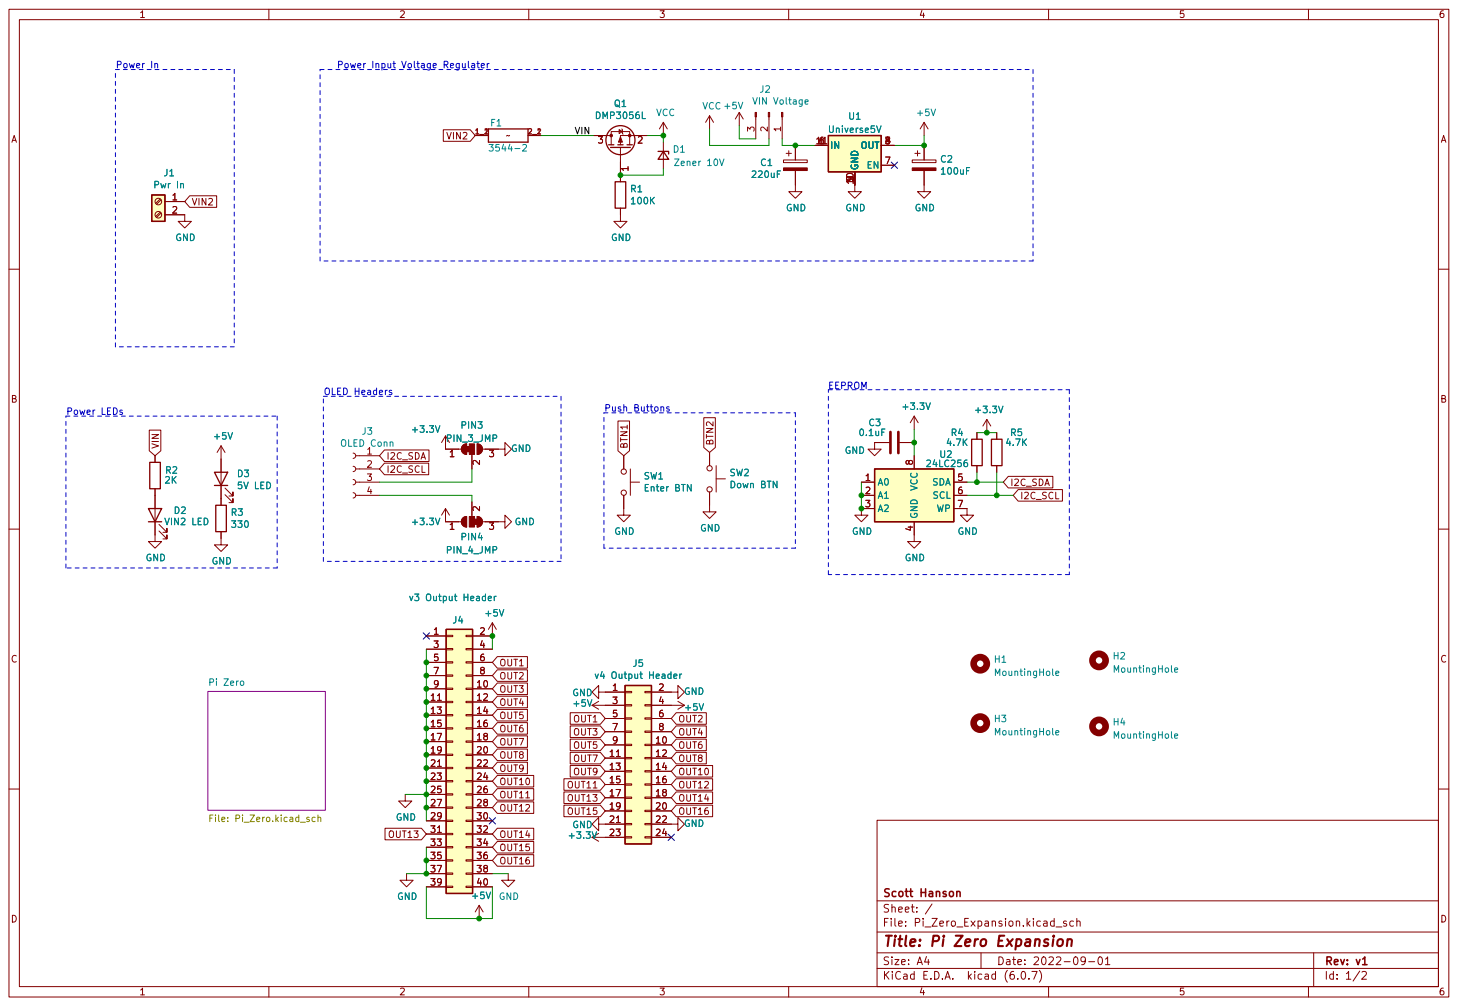
[picture p119: page 1]

4 SDA 5 SCL 6 WP 7 VCC

11 11 | 12 12
13 13 | 14 14
15 15 | 16 16

19 19 | 20 20
21 21 | 22 22
23 23 | 24 24

File: Pi_Zero_Expansion.kicad_sch Sheet: / Scott Hanson

Id: 1/2 Title: Pi Zero Expansion

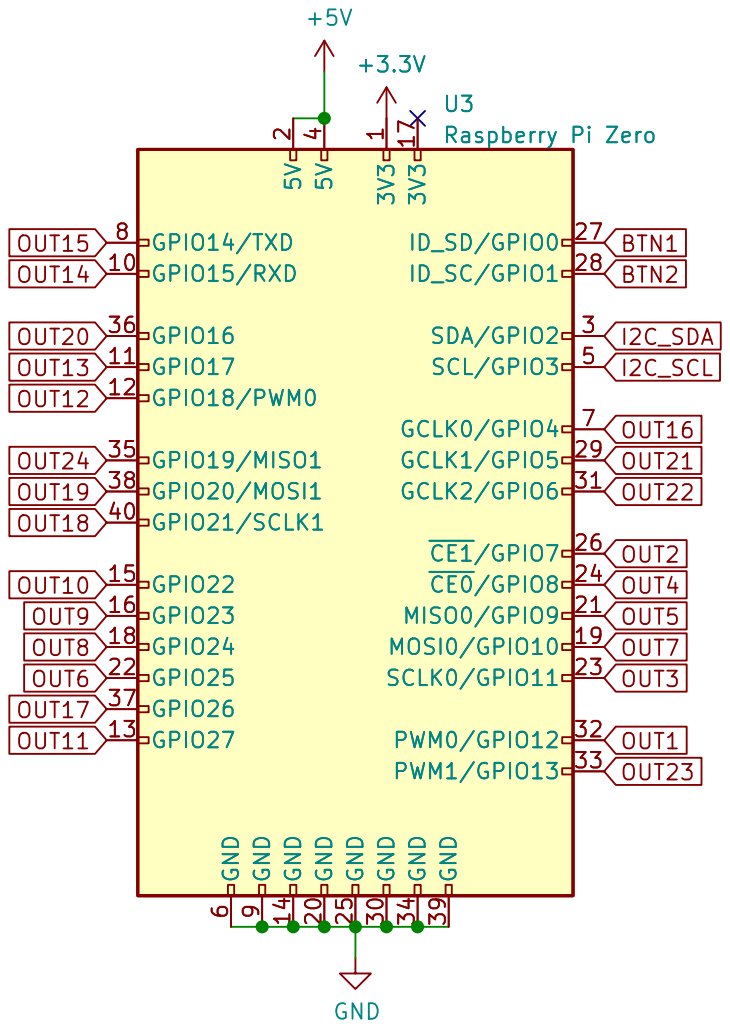
[picture p120: page 2]

Id: 2/2 Title: Pi Zero Expansion
