computergeek1507/PB_16/Pi_Zero_W_16_SMD/Pi_Zero_W_16.pdf

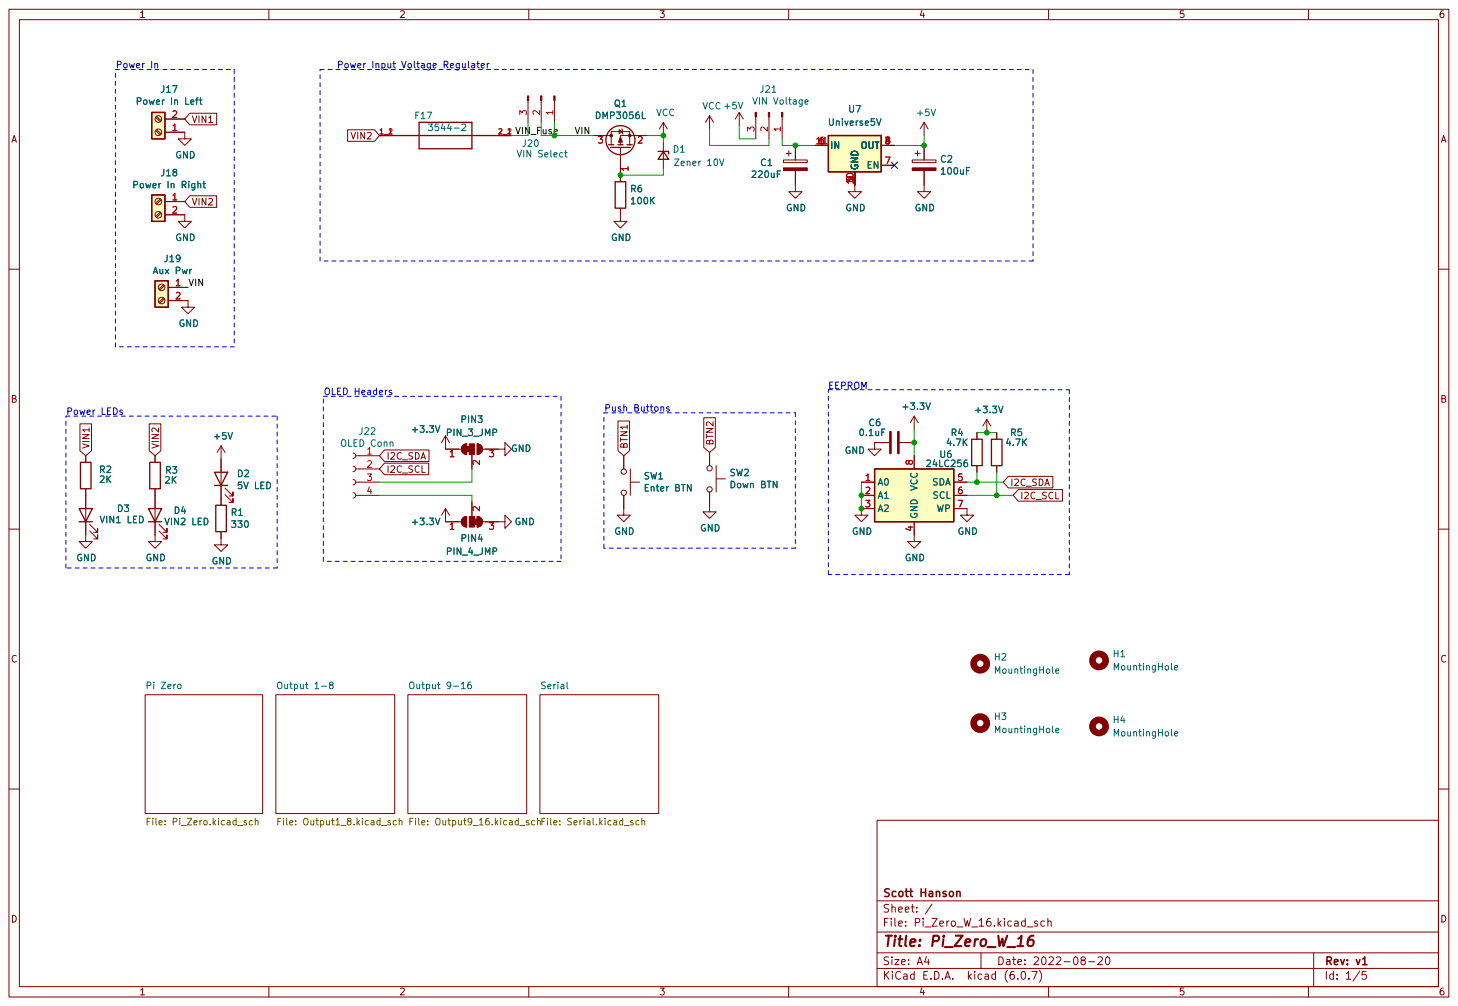
[picture p121: page 1]

Power Input Voltage Regulater D3 VIN1 LED GND

PIN3 PIN_3_JMP +3.3V 4 PIN4 PIN_4_JMP | 3 PIN4 PIN_4_JMP GND

4 SDA 5 SCL 6 WP 7 VCC

Serial File: Serial.kicad_sch Output 9-16

File: Pi_Zero_W_16.kicad_sch Sheet: / Scott Hanson

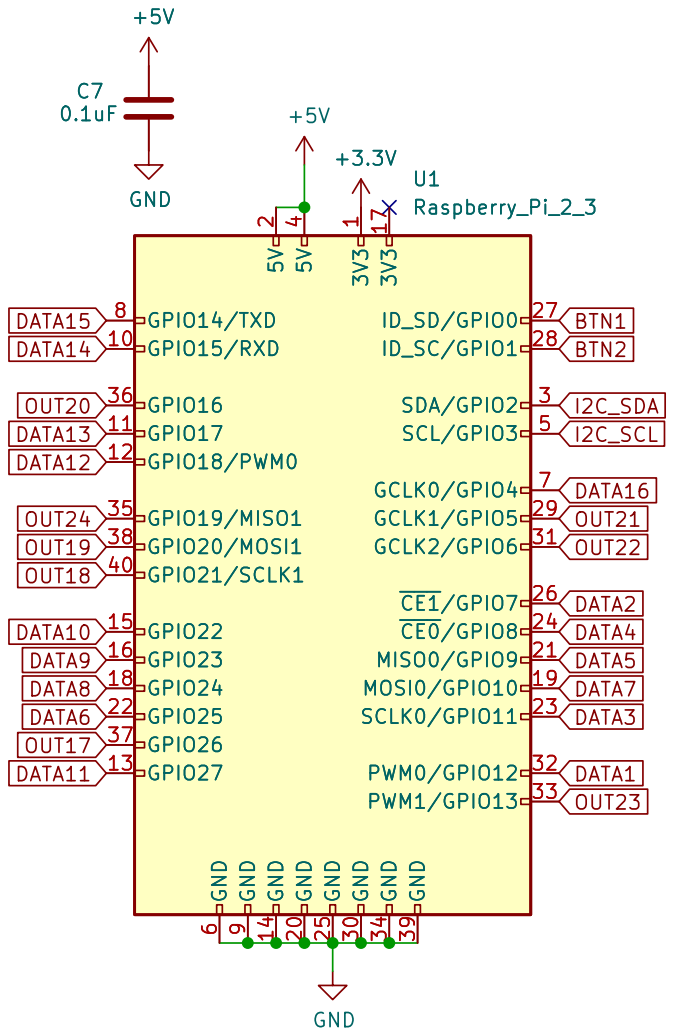
[picture p122: page 2]

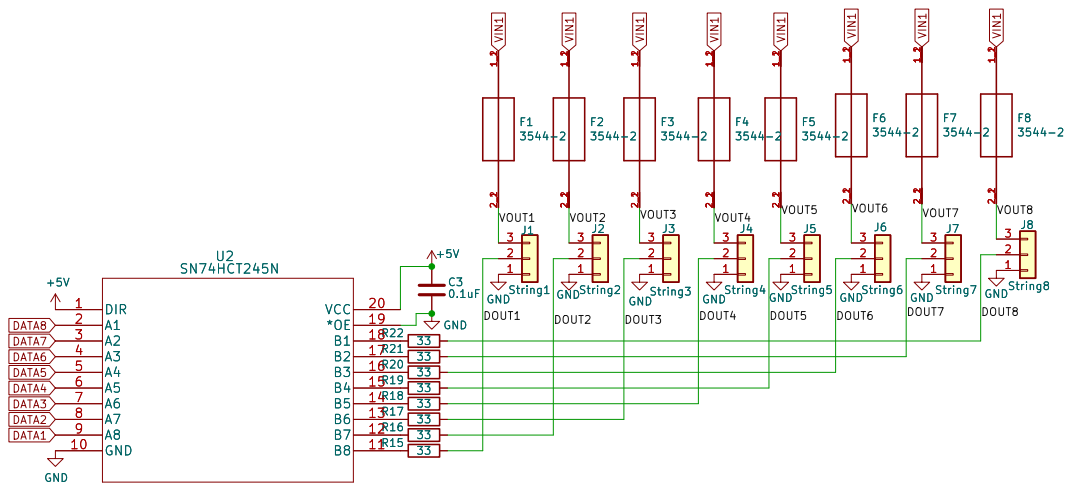
[picture p123: page 3]

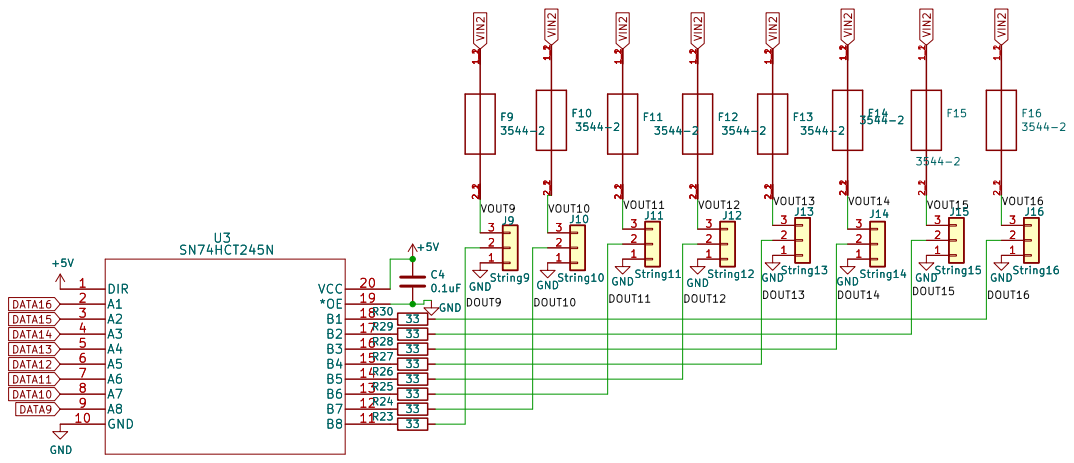
[picture p124: page 4]

Sheet: /Output 9-16/ Scott Hanson

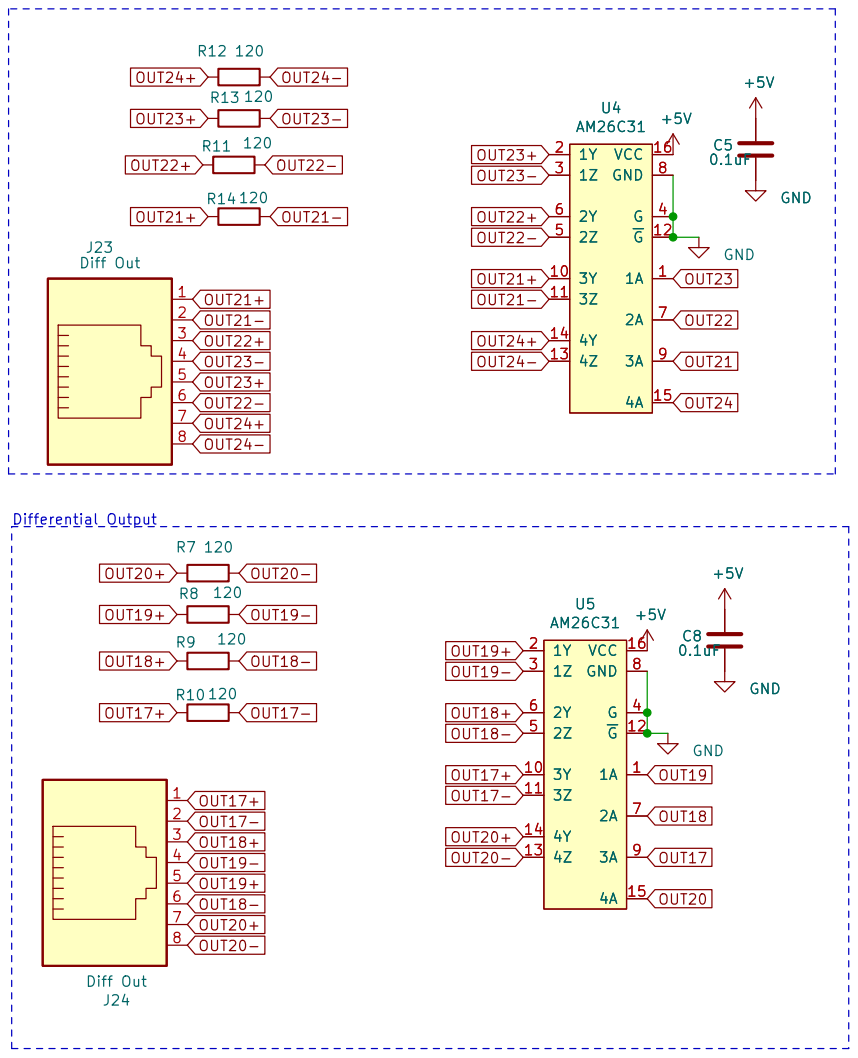
[picture p125: page 5]

File: Serial.kicad_sch Sheet: /Serial/ Scott Hanson
