computergeek1507/PB_16/BBB_16_SMD/BBB_16.pdf

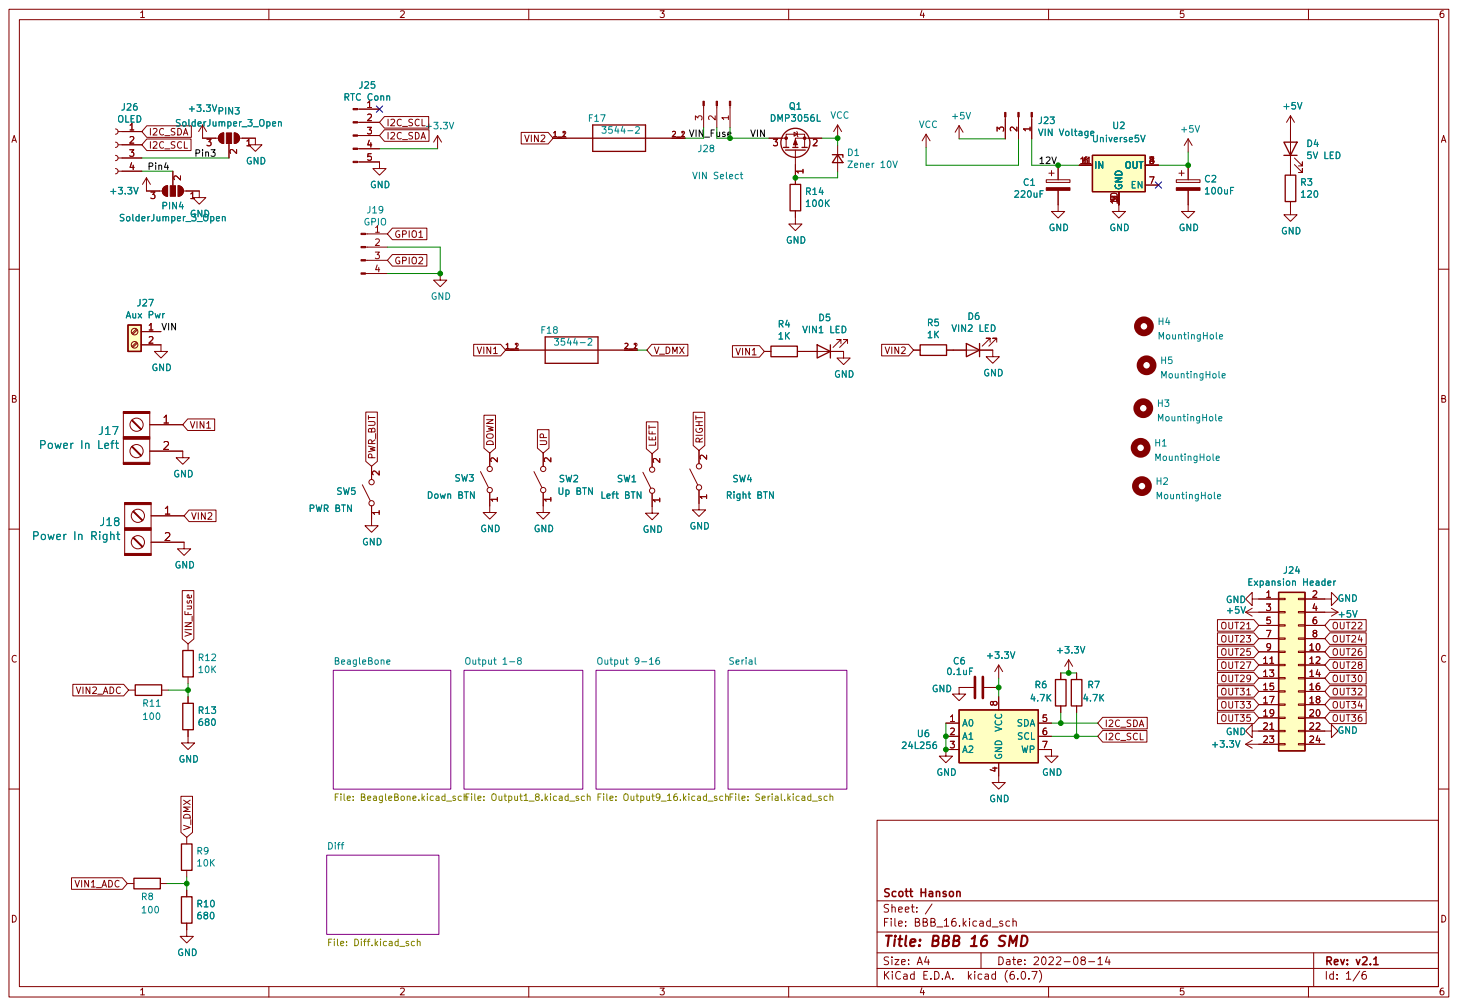
[picture p126: page 1]

4 SDA 5 SCL 6 WP 7 VCC

Id: 1/6 Title: BBB 16 SMD

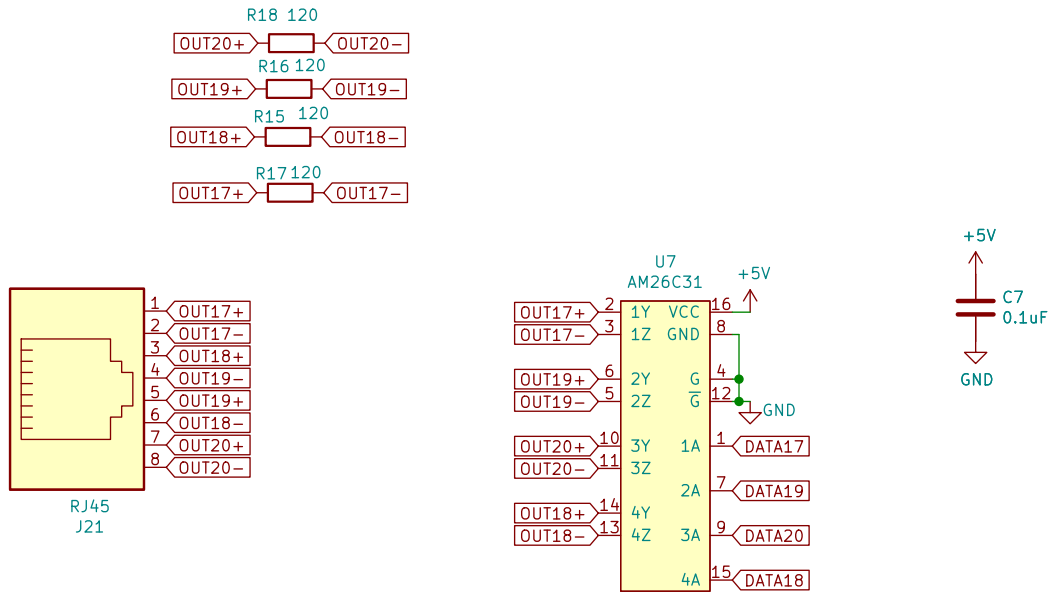
[picture p127: page 2]

File: Diff.kicad_sch Sheet: /Diff/ Scott Hanson C7
0.1uF GND

Id: 2/6 Title: BBB 16 SMD

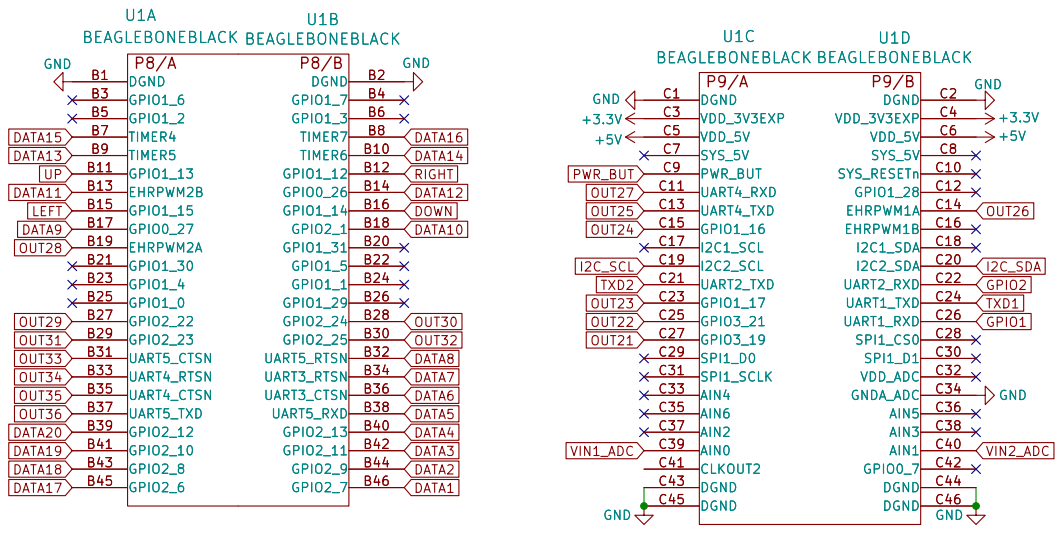
[picture p128: page 3]

Sheet: /BeagleBone/ Scott Hanson

File: BeagleBone.kicad_sch
Id: 3/6 Title: BBB 16 SMD

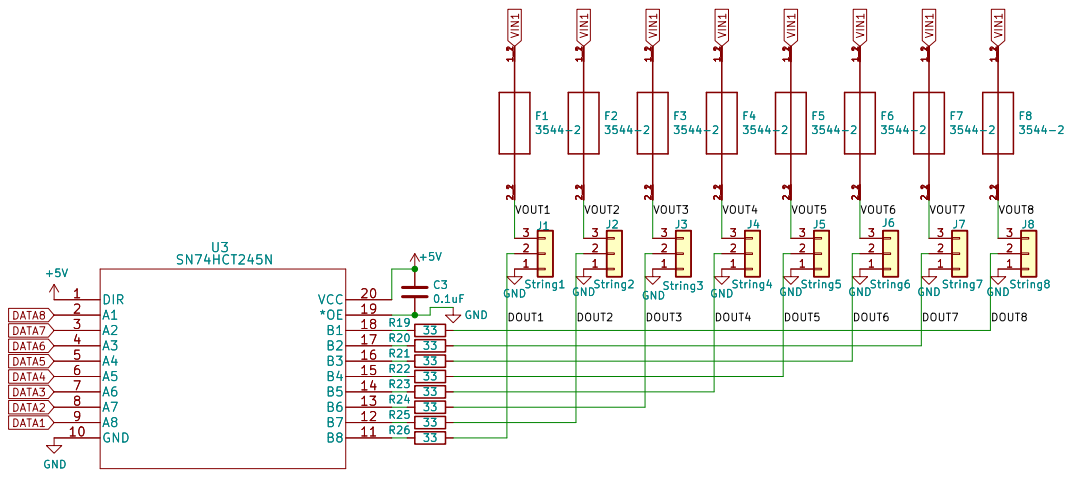
[picture p129: page 4]

File: Output1_8.kicad_sch
Id: 4/6 Title: BBB 16 SMD

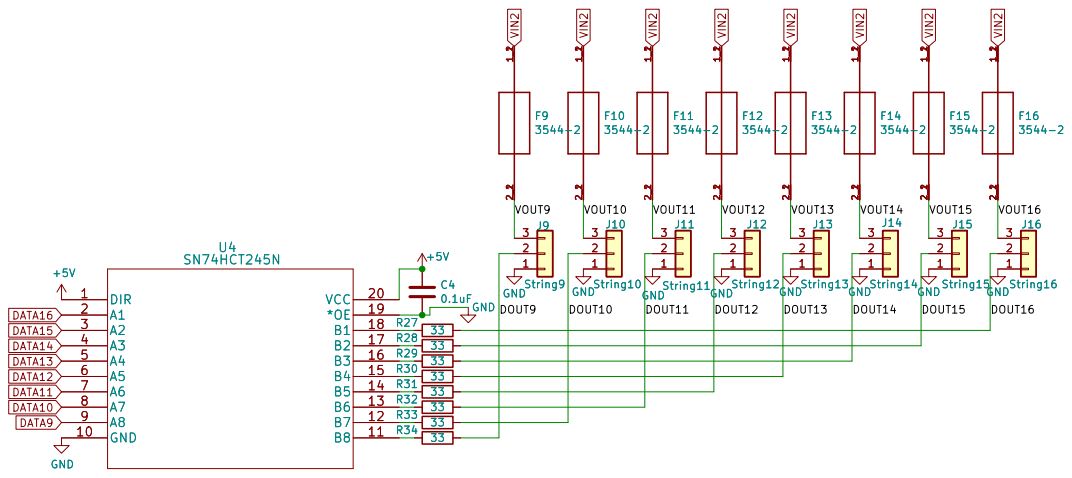
[picture p130: page 5]

File: Output9_16.kicad_sch
Id: 5/6 Title: BBB 16 SMD

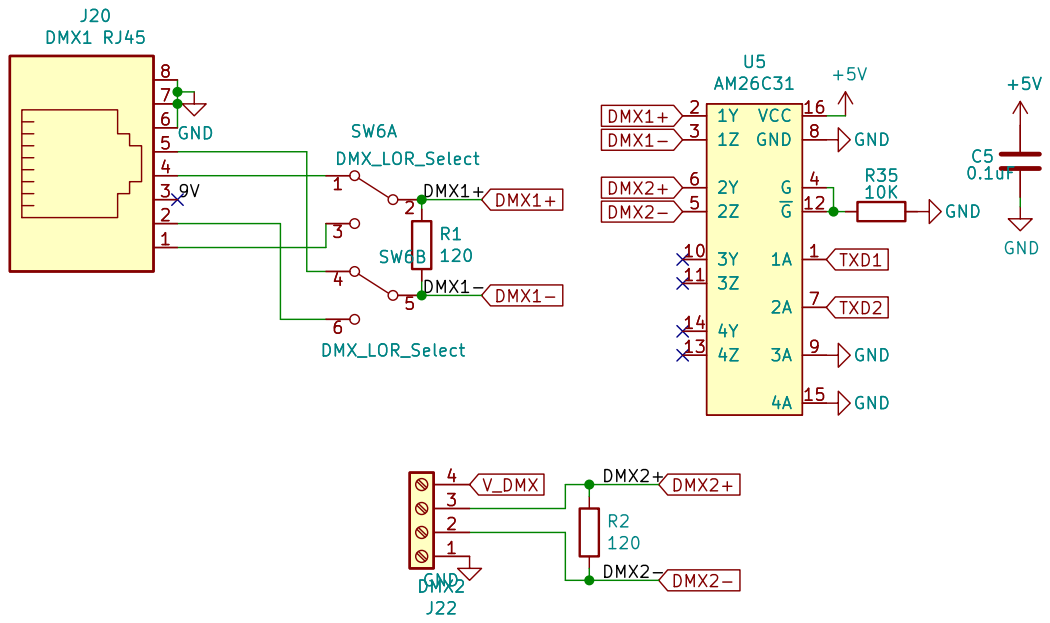
[picture p131: page 6]

File: Serial.kicad_sch Sheet: /Serial/ Scott Hanson

Id: 6/6 Title: BBB 16 SMD
