computergeek1507/PB_16/Multi_Expansion/Multi_Expansion.pdf

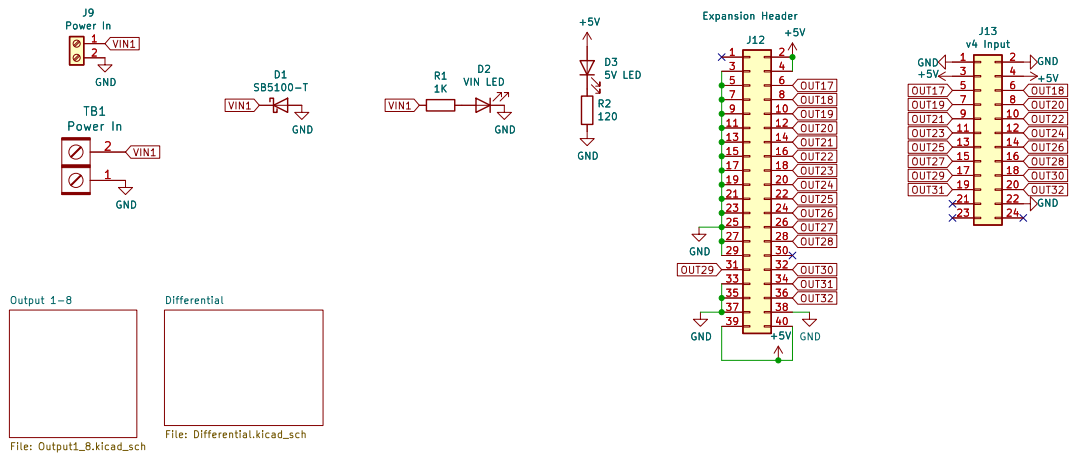
[picture p132: page 1]

5 5 | 6 6
7 7 | 8 8
9 | 10 10
11 11 | 12 12
13 13 | 14 14
15 15 | 16 16
17 17 | 18 18
19 19 | 20 20
21 21 | 22 22
23 23 | 24 24
25 25 | 26 26

120 GND GND TB1 Power In

File: Multi_Expansion.kicad_sch Sheet: / Scott Hanson Differential File: Differential.kicad_sch Output 1-8

Id: 1/3 Title: Multi Expansion

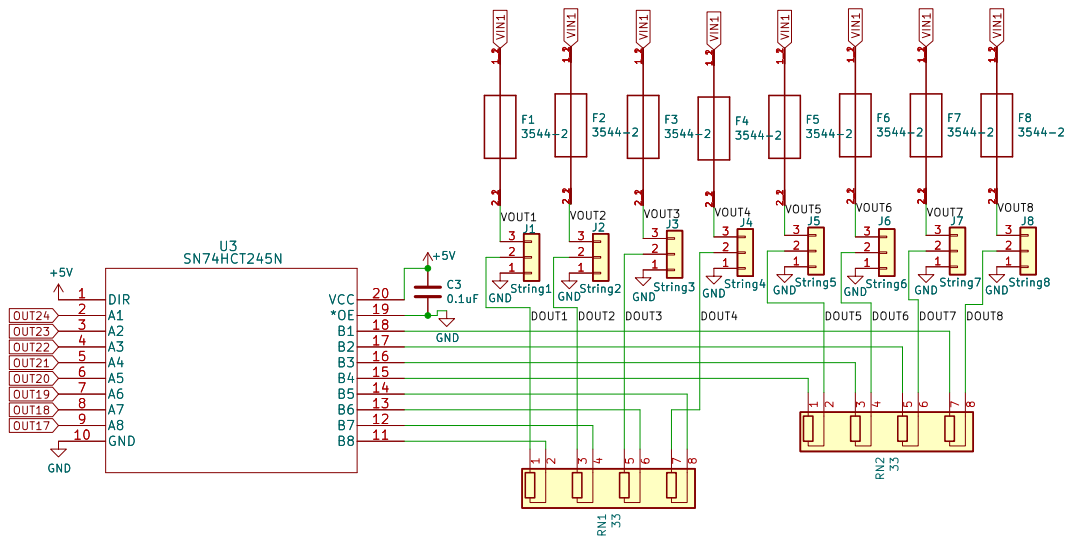
[picture p133: page 2]

Sheet: /Output 1-8/ Scott Hanson GND

File: Output1_8.kicad_sch
Id: 2/3 Title: Multi Expansion

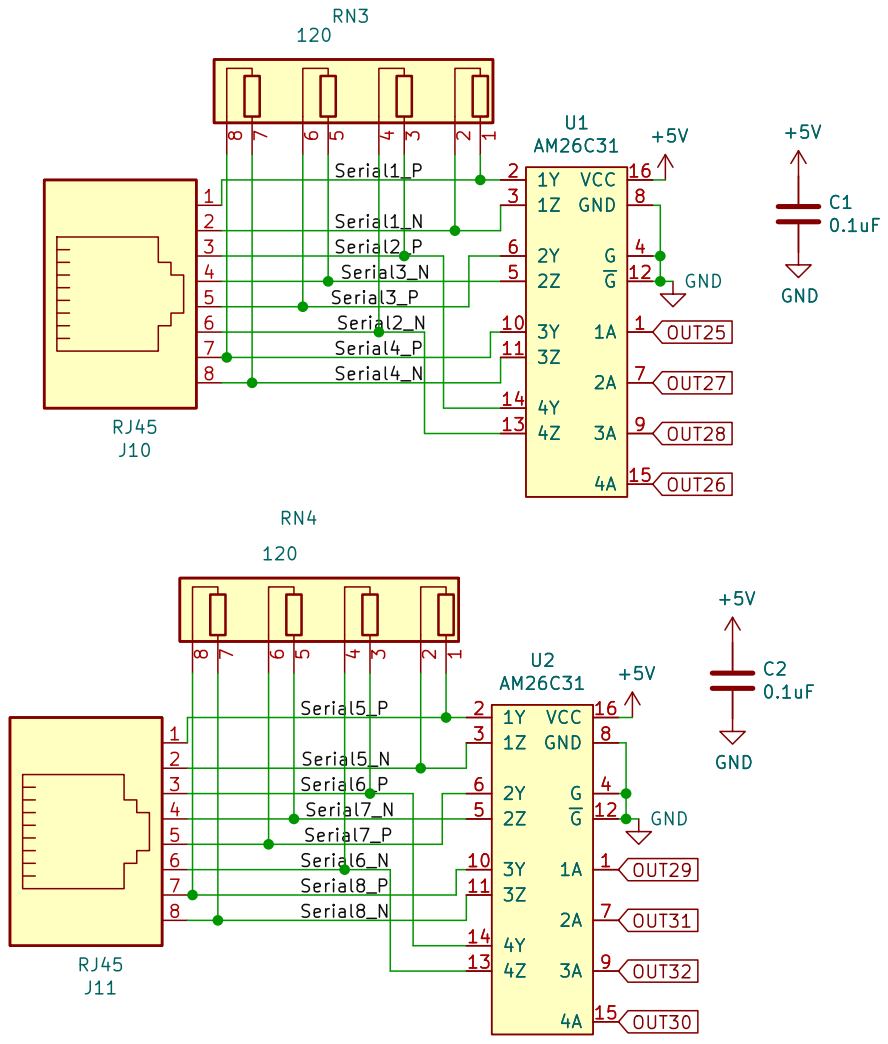
[picture p134: page 3]

Serial1_P

Serial1_N
Serial2_P

Serial3_P
Serial2_N
Serial4_P
Serial4_N

Serial5_P

Serial5_N

Serial7_P
Serial6_N
Serial8_P
Serial8_N

File: Differential.kicad_sch Sheet: /Differential/ Scott Hanson

Id: 3/3 Title: Multi Expansion
