computergeek1507/PB_16/16_Expansion_Dual_SMD/PB_16.pdf

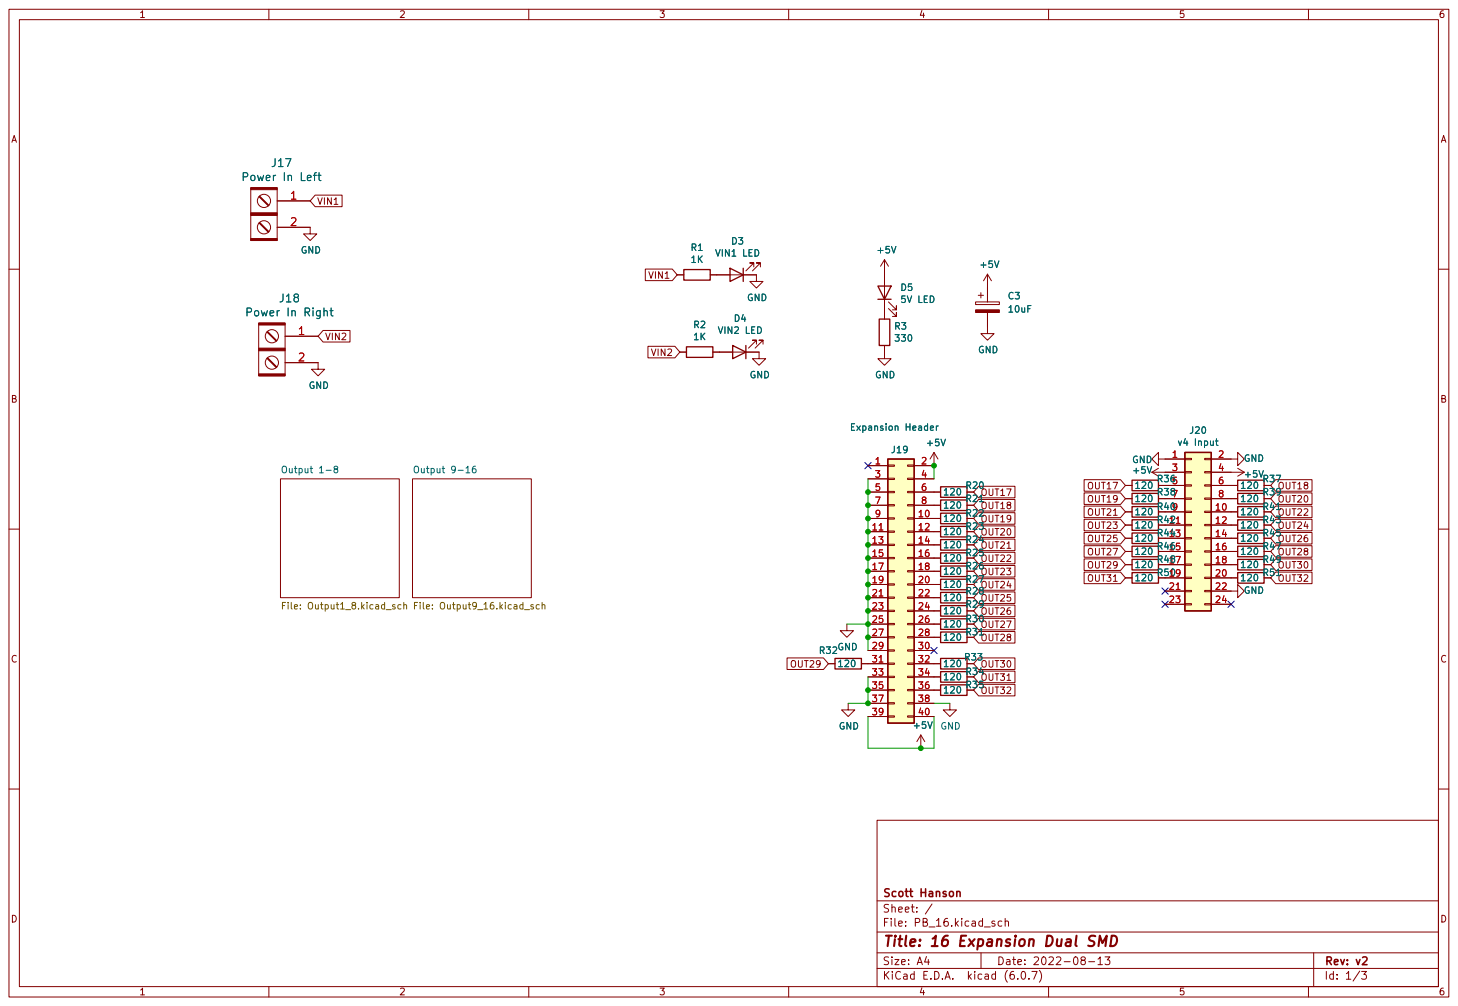
[picture p135: page 1]

File: PB_16.kicad_sch Sheet: / Scott Hanson Output 1-8

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

Id: 1/3 Title: 16 Expansion Dual SMD

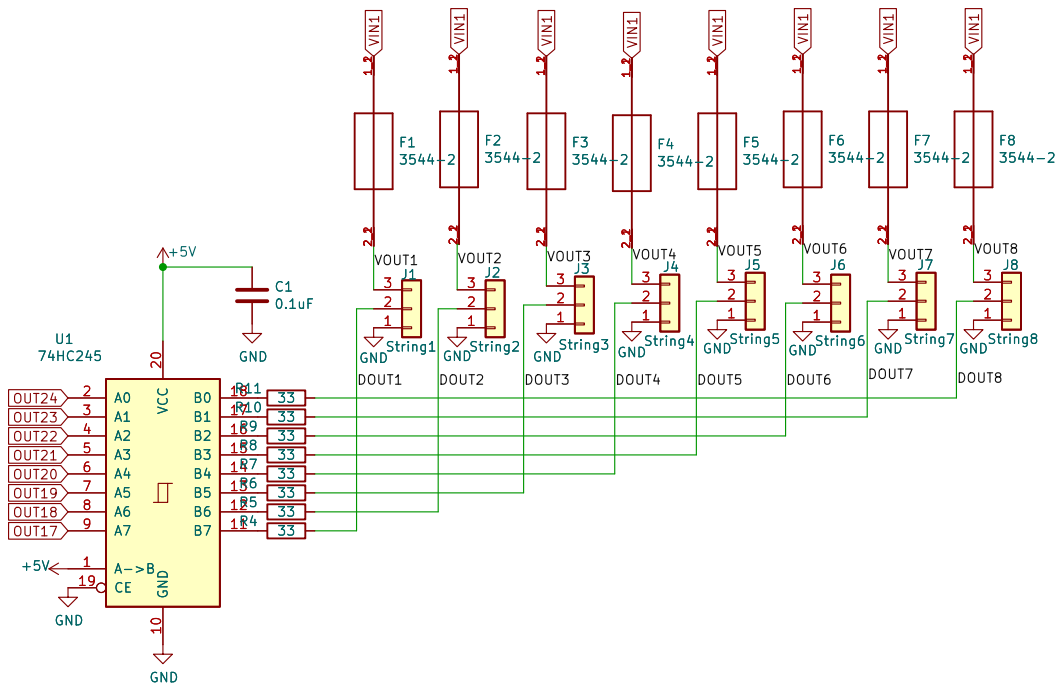
[picture p136: page 2]

File: Output1_8.kicad_sch
Id: 2/3 Title: 16 Expansion Dual SMD

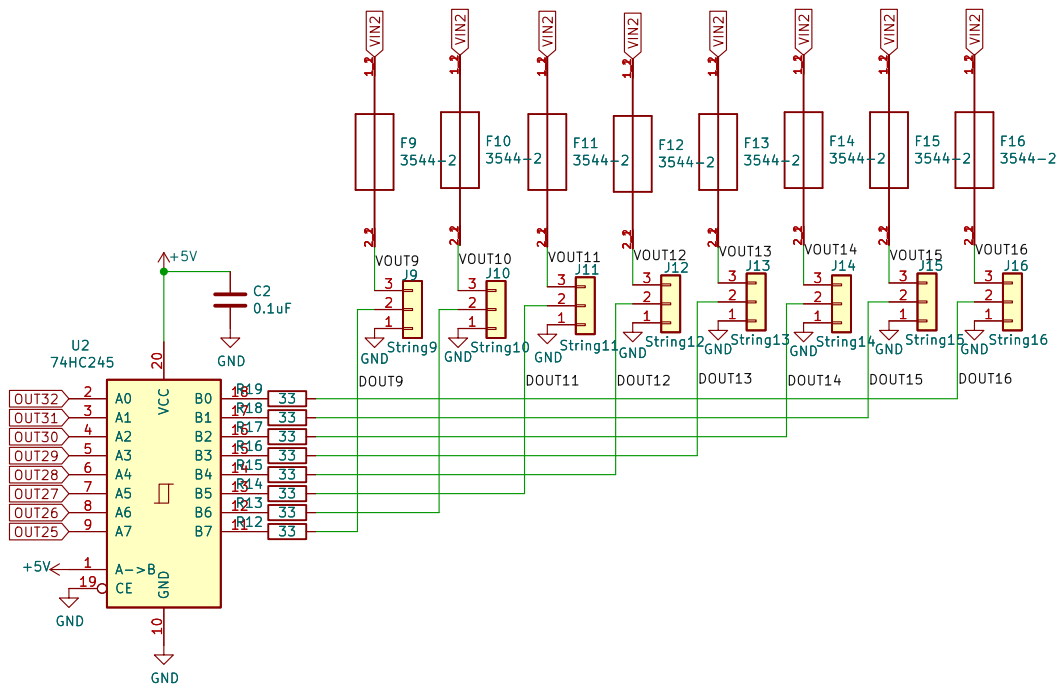
[picture p137: page 3]

File: Output9_16.kicad_sch
Id: 3/3 Title: 16 Expansion Dual SMD
