computergeek1507/PB_16/16_Expansion_24pin/PB_16.pdf

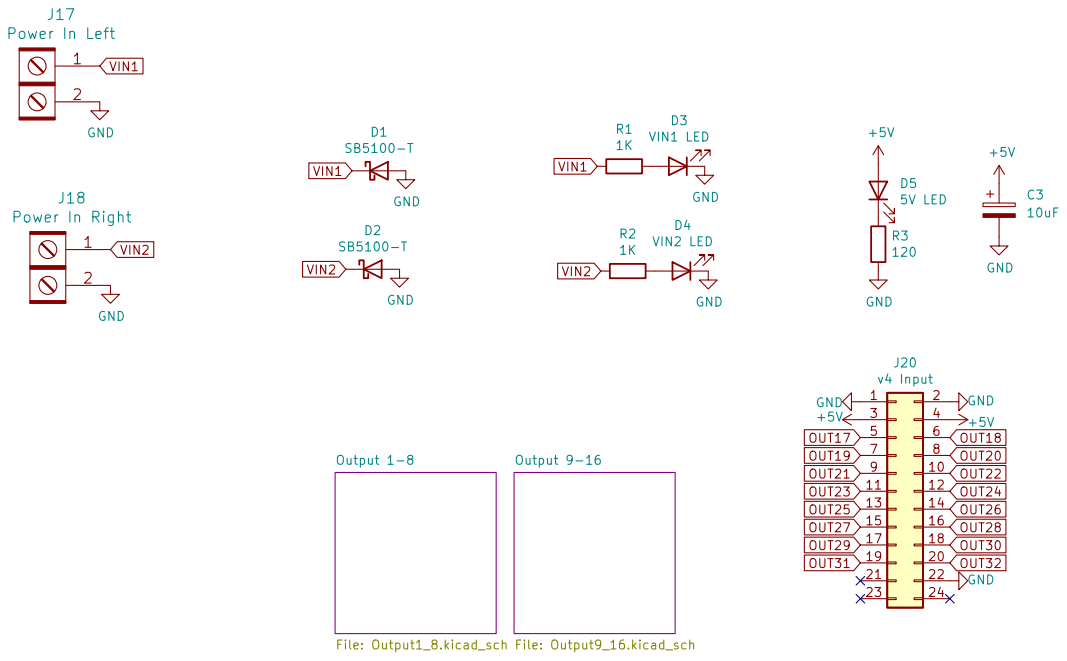
[picture p138: page 1]

File: PB_16.kicad_sch Sheet: / Scott Hanson Output 1-8

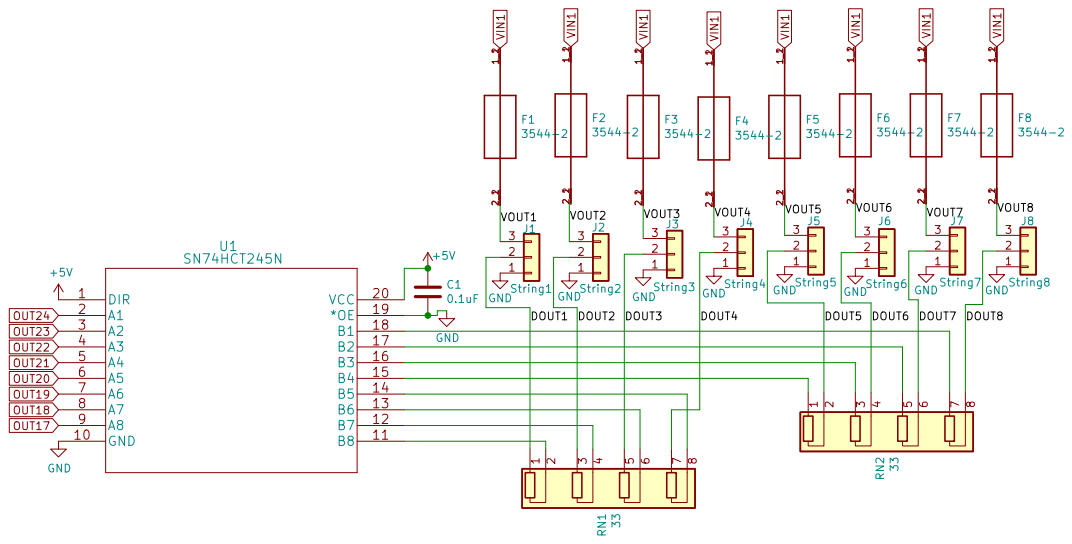
[picture p139: page 2]

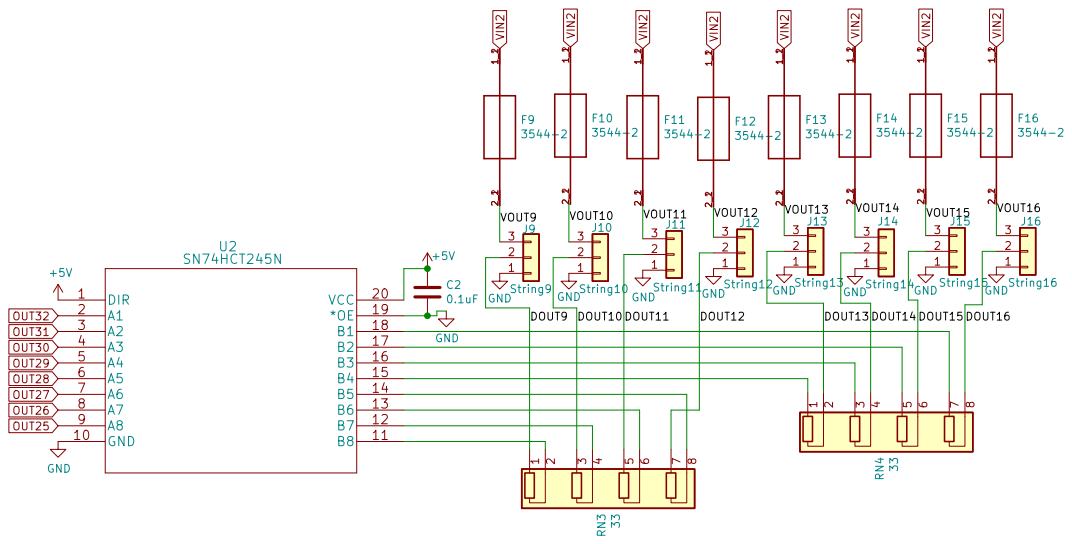
[picture p140: page 3]
