computergeek1507/PB_16/16_Expansion/PB_16.pdf

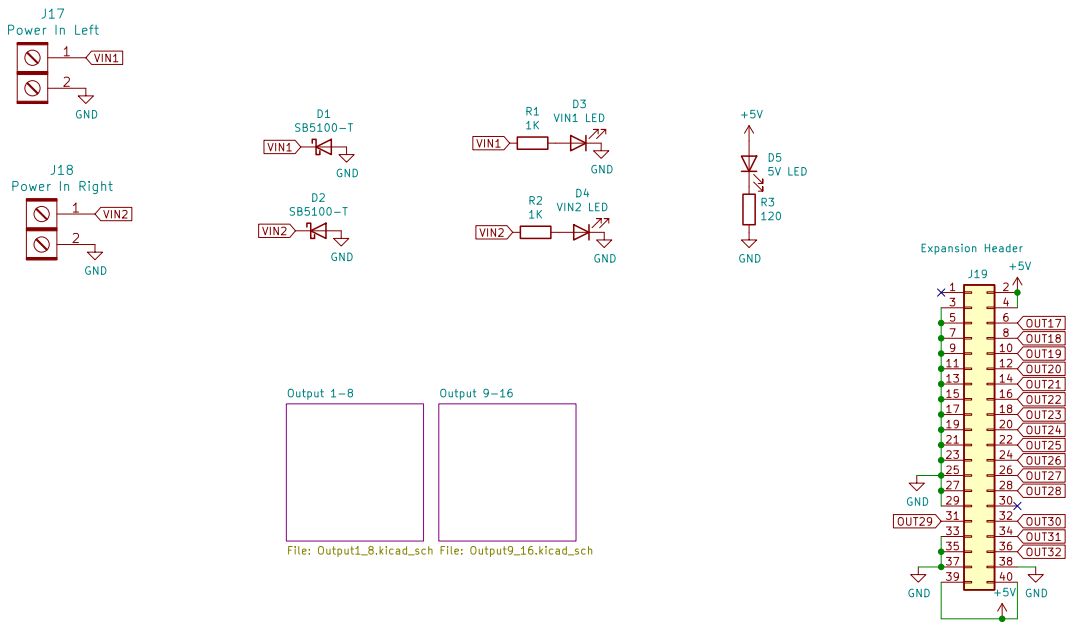
[picture p141: page 1]

File: PB_16.kicad_sch Sheet: / Scott Hanson Output 1-8

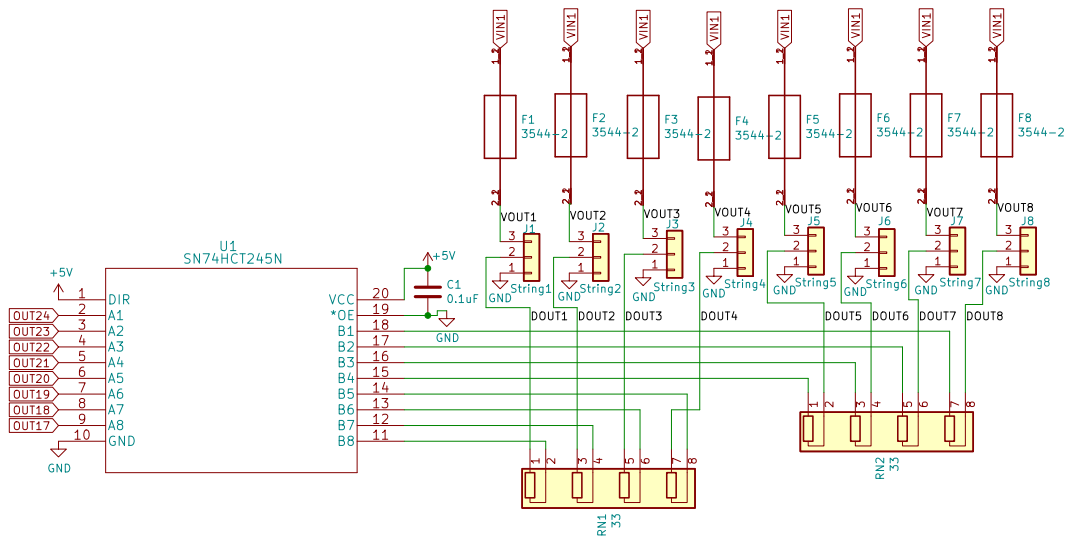
[picture p142: page 2]

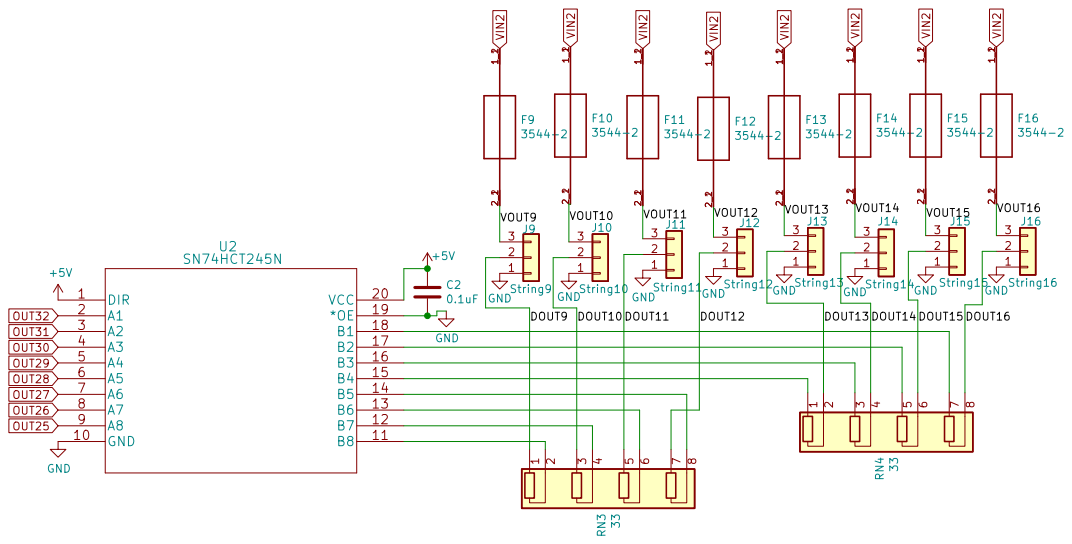
[picture p143: page 3]

Sheet: /Output 9-16/ Scott Hanson
