computergeek1507/PB_16/BBB_16_Flex/BBB_16_Flex.pdf

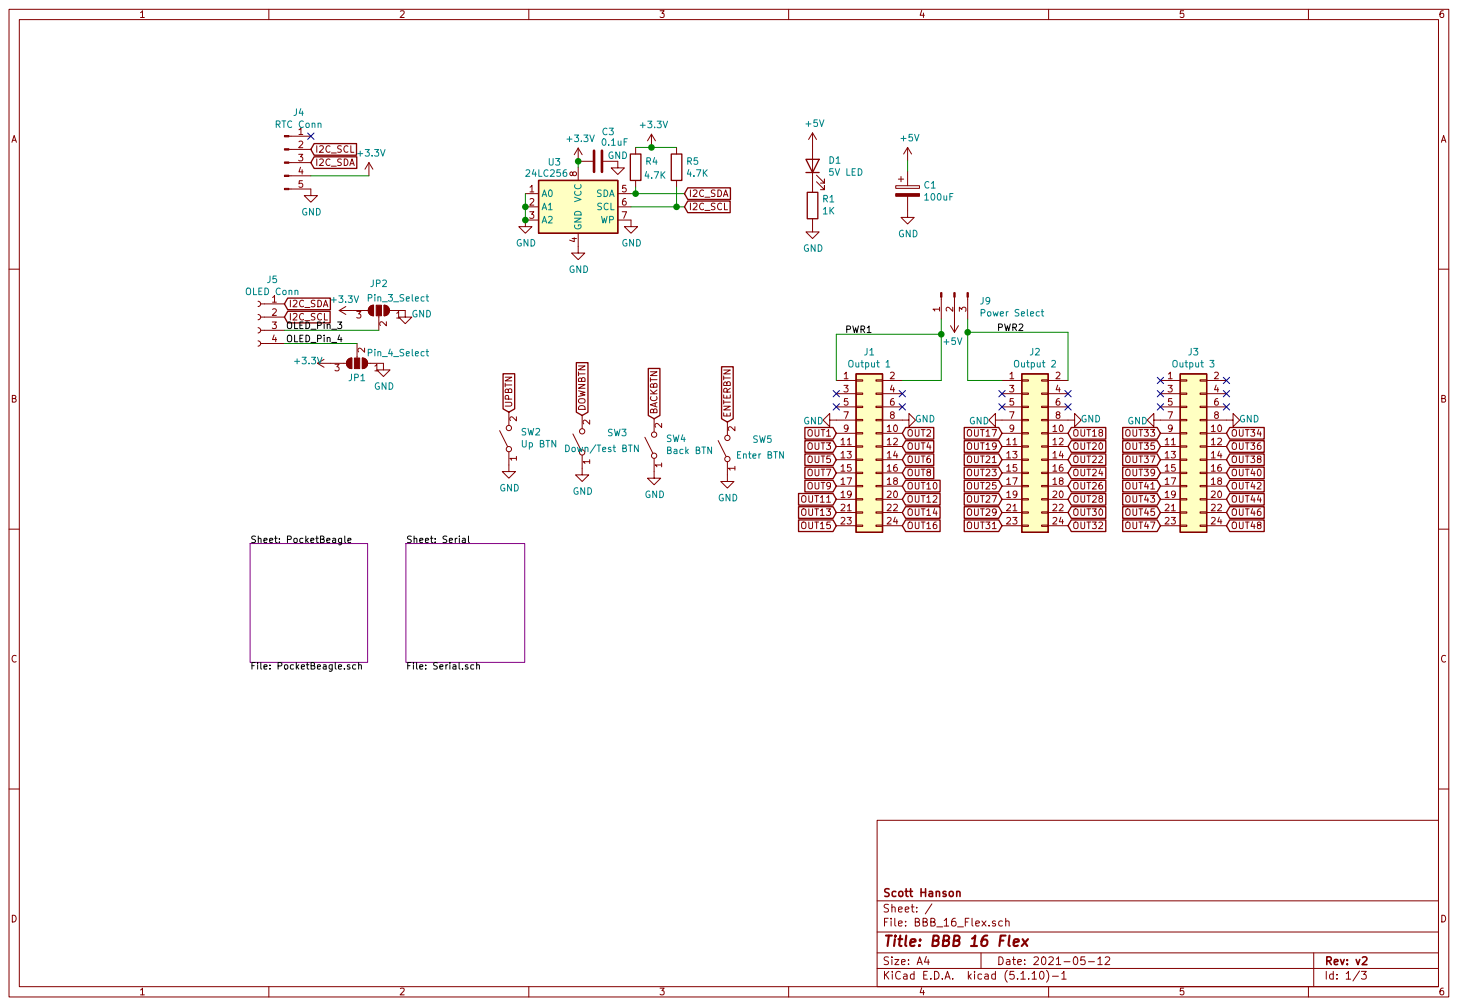
[picture p144: page 1]

4 SDA 5 SCL 6 WP 7 VCC

1 2 SW3 Down/Test BTN GND GND GND GND

File: BBB_16_Flex.sch Sheet: / Scott Hanson

Id: 1/3 Title: BBB 16 Flex

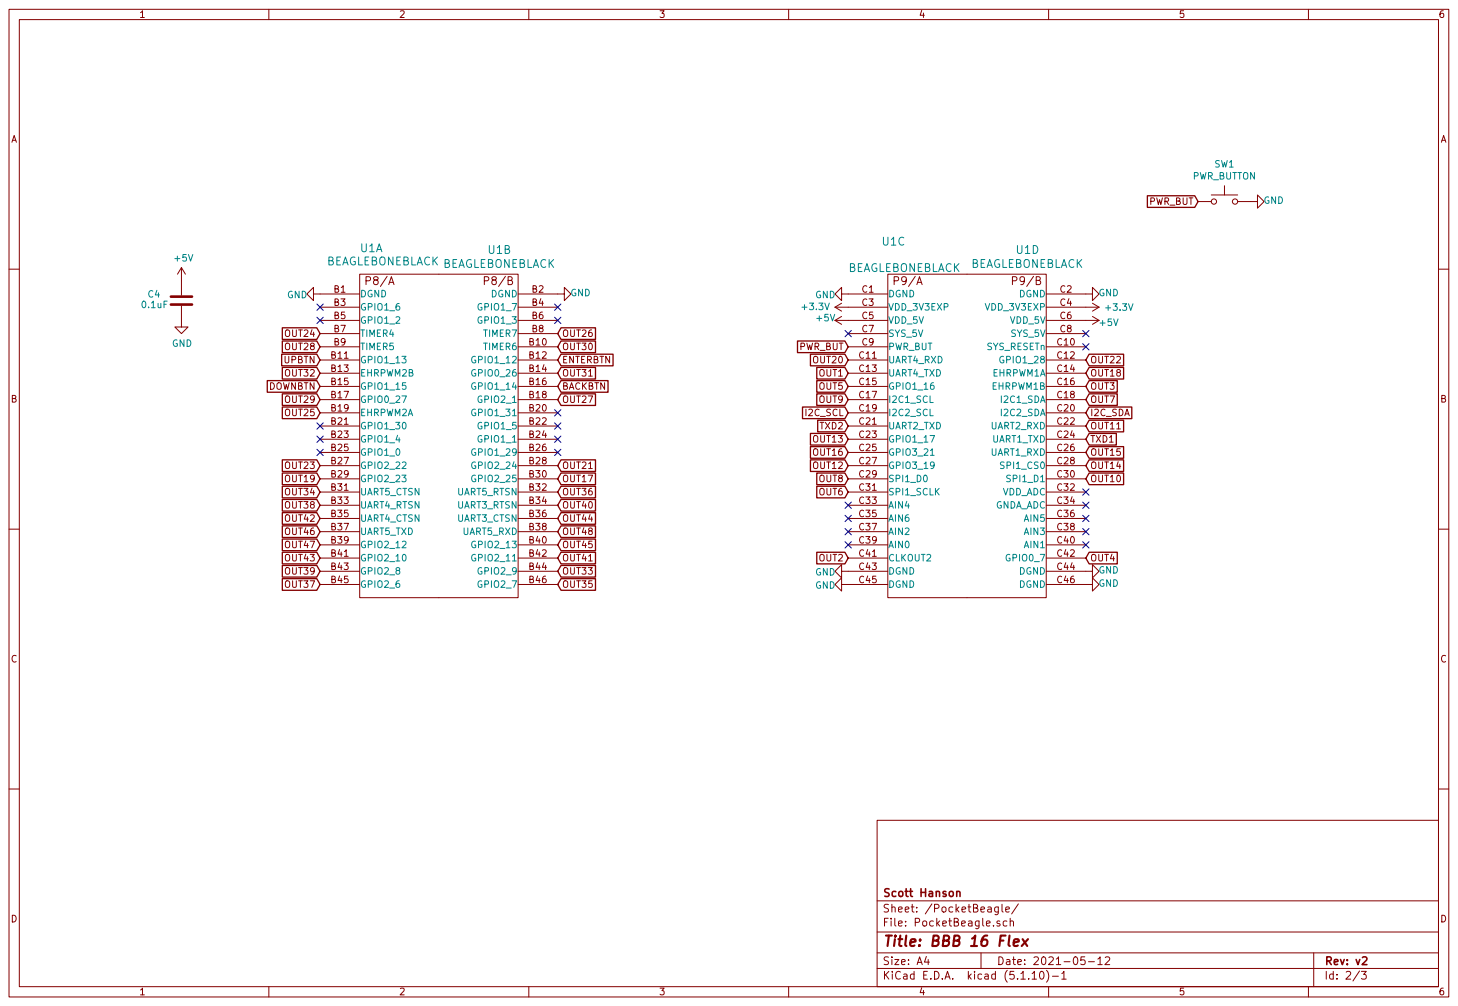
[picture p145: page 2]

File: PocketBeagle.sch
Id: 2/3 Title: BBB 16 Flex

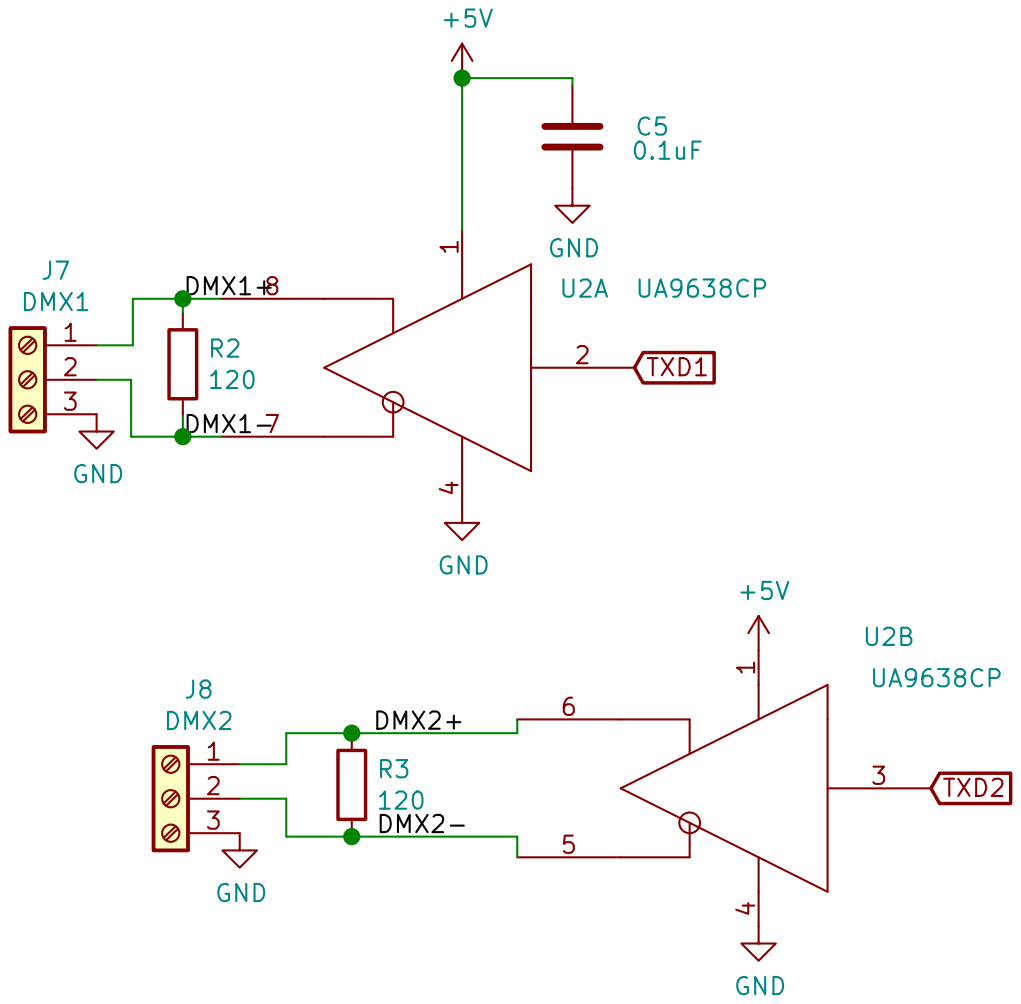
[picture p146: page 3]

File: Serial.sch Sheet: /Serial/ Scott Hanson R3

Id: 3/3 Title: BBB 16 Flex
