computergeek1507/PB_16/Smart_Reciever_Max_Exp_Pico/Smart_Reciever_Max.pdf

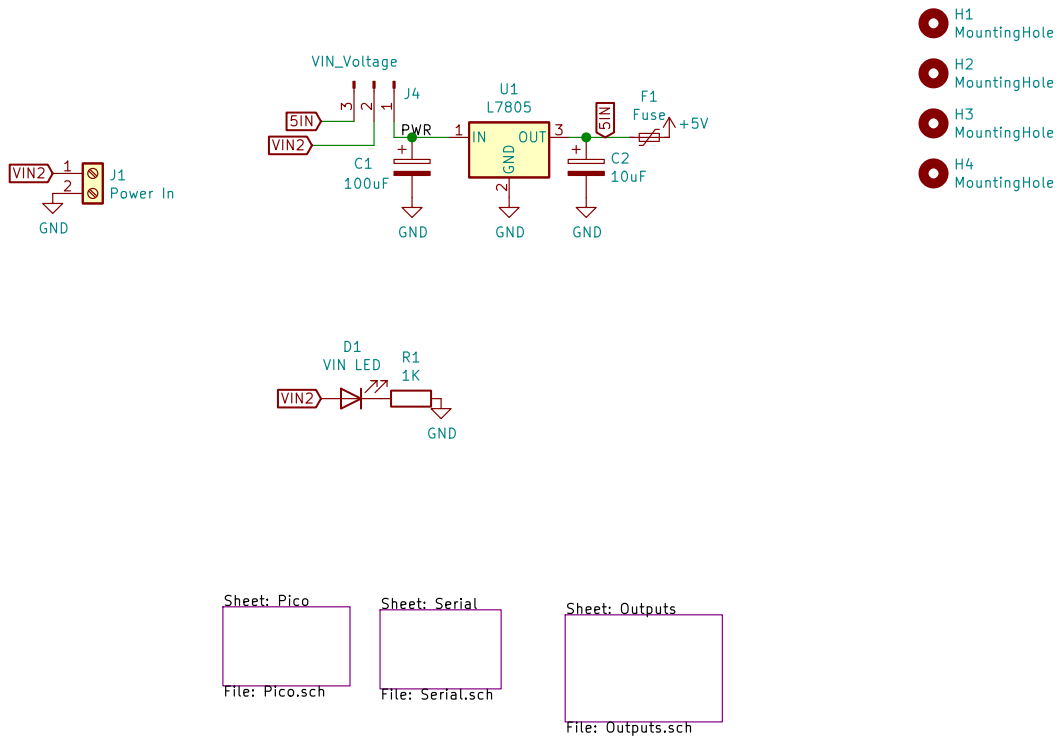
[picture p147: page 1]

File: Outputs.sch Sheet: Pico File: Pico.sch

File: Smart_Reciever_Max.sch Sheet: / Scott Hanson

Id: 1/4 Title: Smart Reciver Max Exp Pico

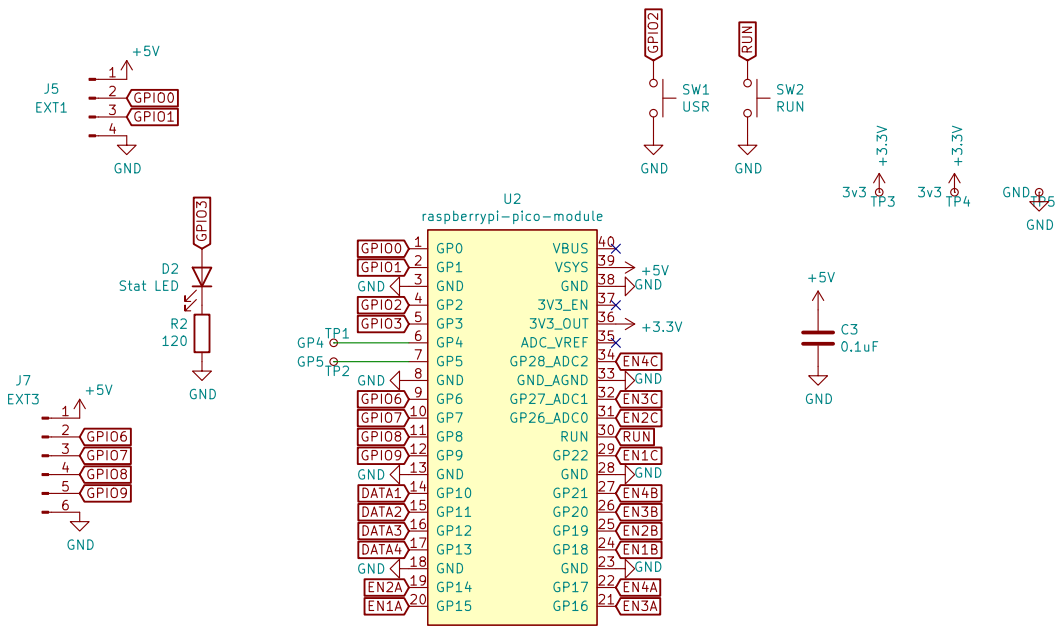
[picture p148: page 2]

File: Pico.sch Sheet: /Pico/ Scott Hanson

Id: 2/4 Title: Smart Reciver Max Exp Pico

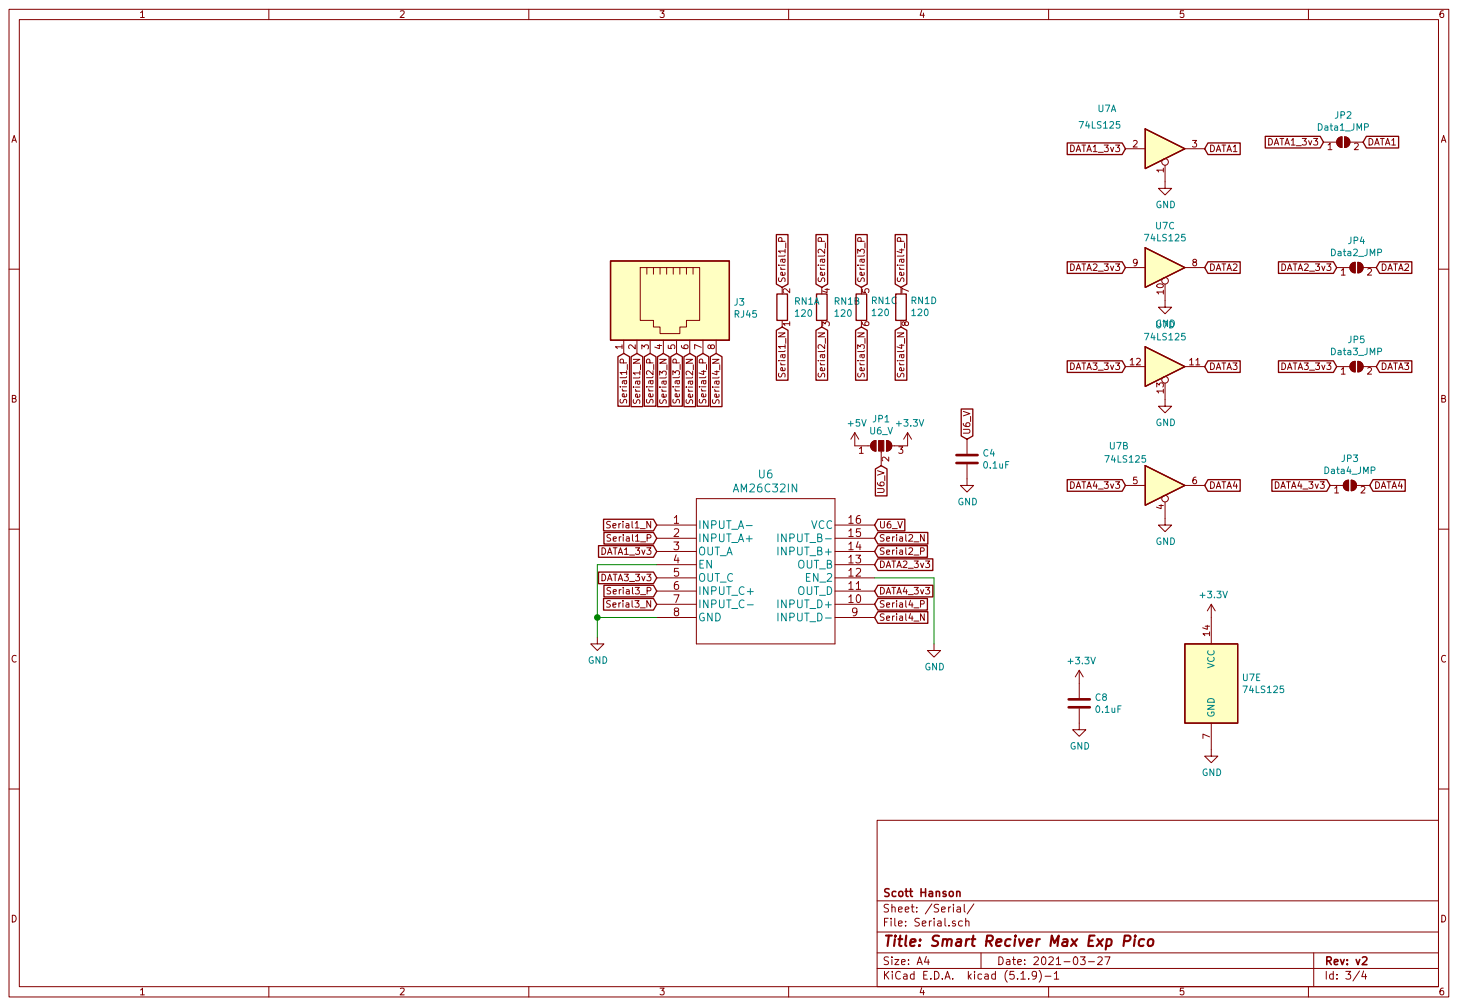
[picture p149: page 3]

+3.3V GND GND GND GND

File: Serial.sch Sheet: /Serial/ Scott Hanson

Id: 3/4 Title: Smart Reciver Max Exp Pico

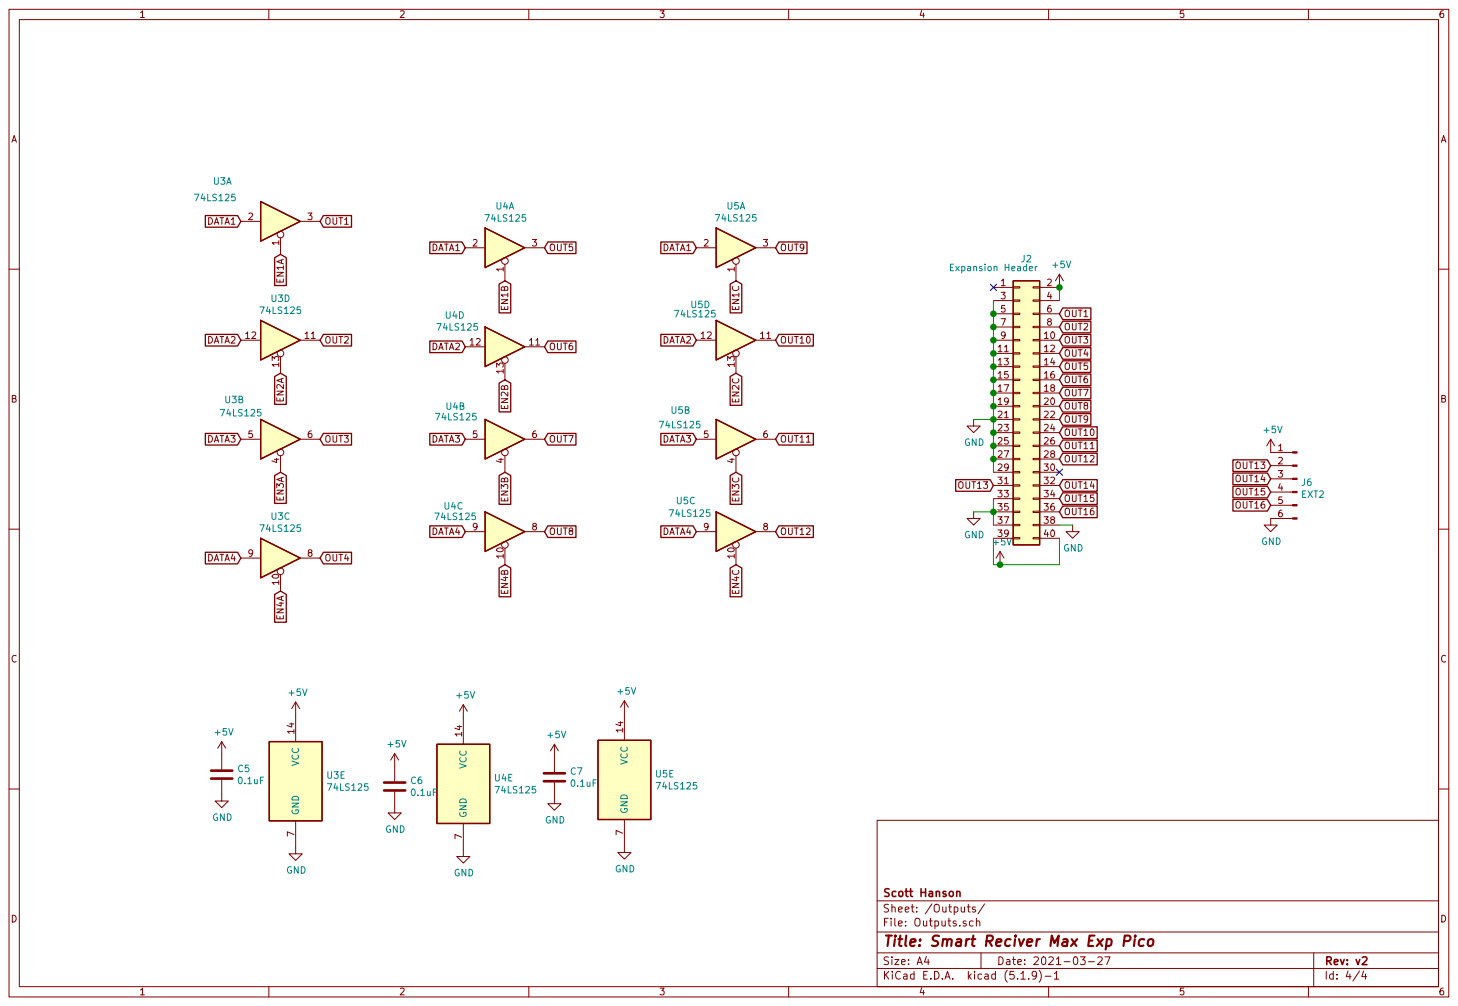
[picture p150: page 4]

File: Outputs.sch
Id: 4/4 Title: Smart Reciver Max Exp Pico
