computergeek1507/PB_16/Pwr_Diff_Breakout/Pwr_Diff_Breakout.pdf

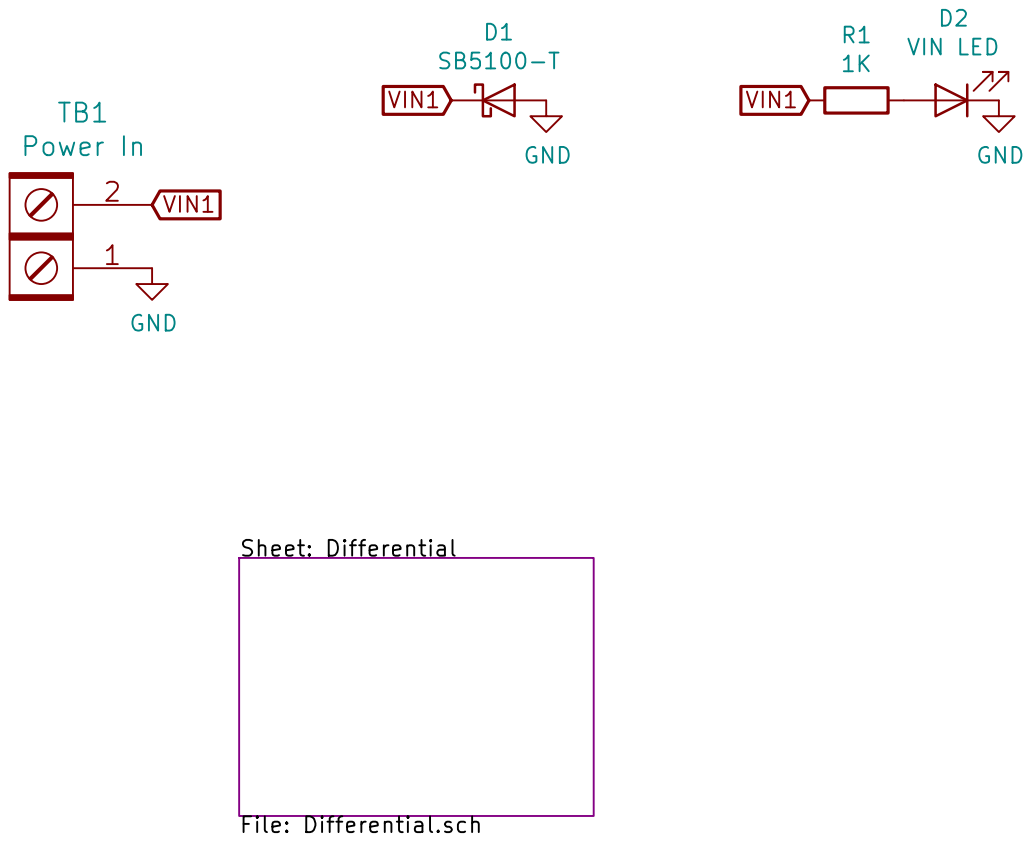
[picture p151: page 1]

Sheet: Differential File: Differential.sch GND

File: Pwr_Diff_Breakout.sch Sheet: / Scott Hanson

Id: 1/2 Title: Pwr Diff Breakout

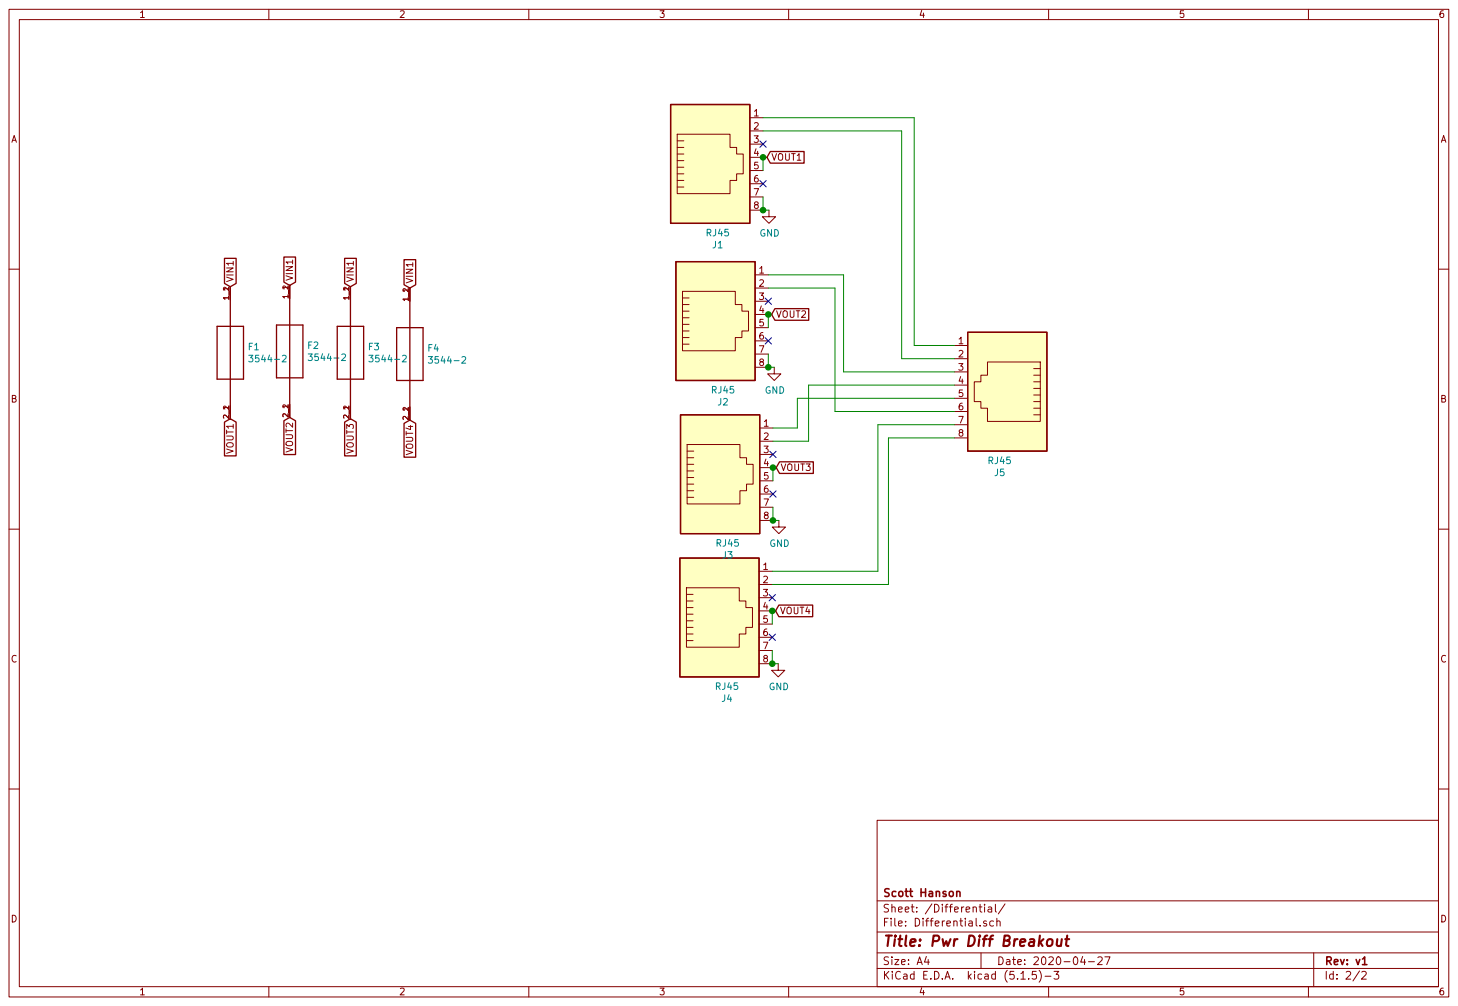
[picture p152: page 2]

Id: 2/2 Title: Pwr Diff Breakout File: Differential.sch Sheet: /Differential/ Scott Hanson 12345678
