computergeek1507/PB_16/PB_16_Flex/PB_16.pdf

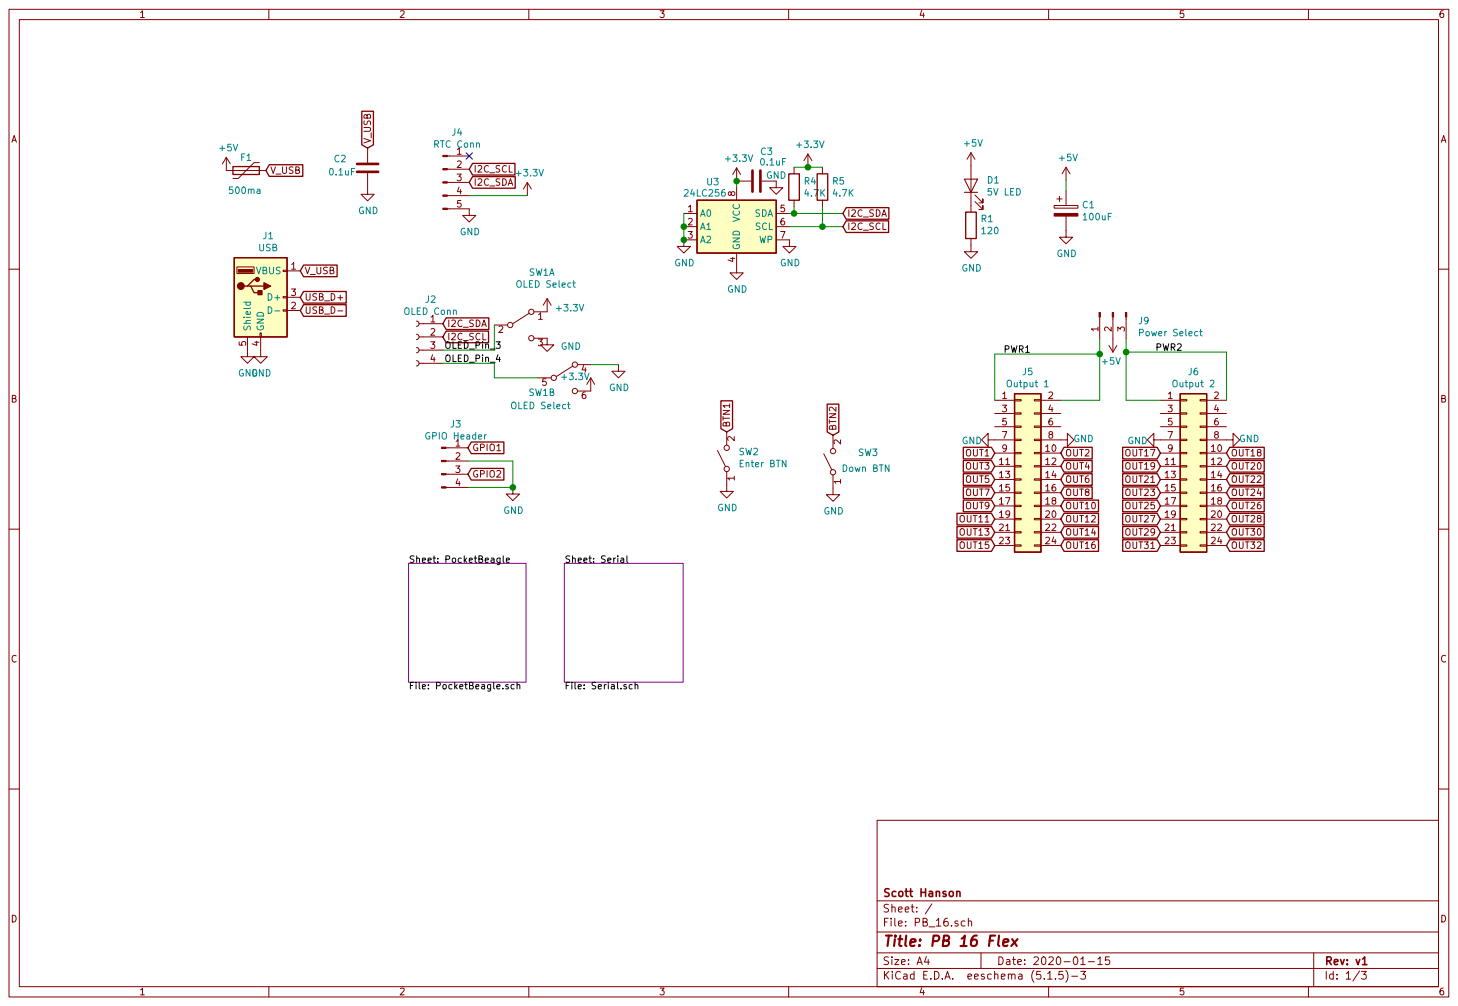
[picture p153: page 1]

4 SDA 5 SCL 6 WP 7 VCC

1 2 SW3 Down BTN GND GND

File: PB_16.sch Sheet: / Scott Hanson

Id: 1/3 Title: PB 16 Flex

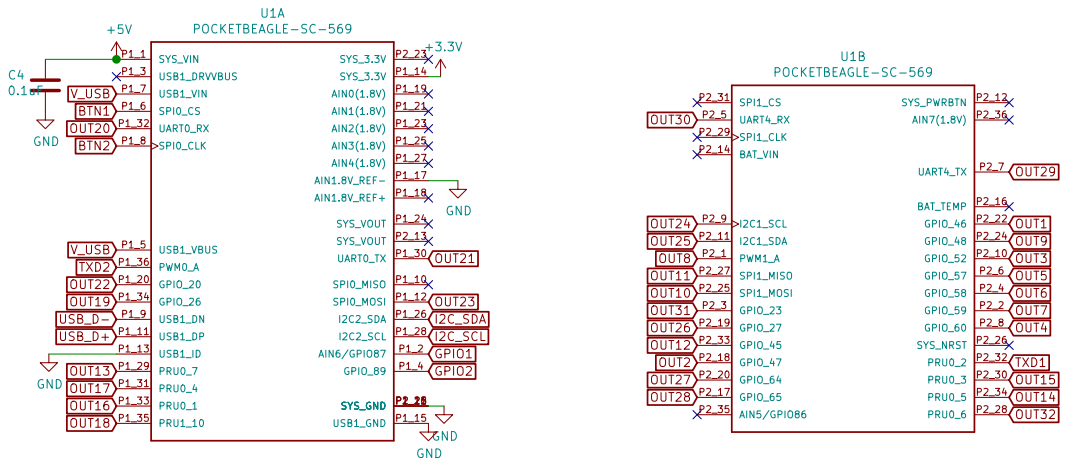
[picture p154: page 2]

Sheet: /PocketBeagle/ Scott Hanson

File: PocketBeagle.sch
Id: 2/3 Title: PB 16 Flex

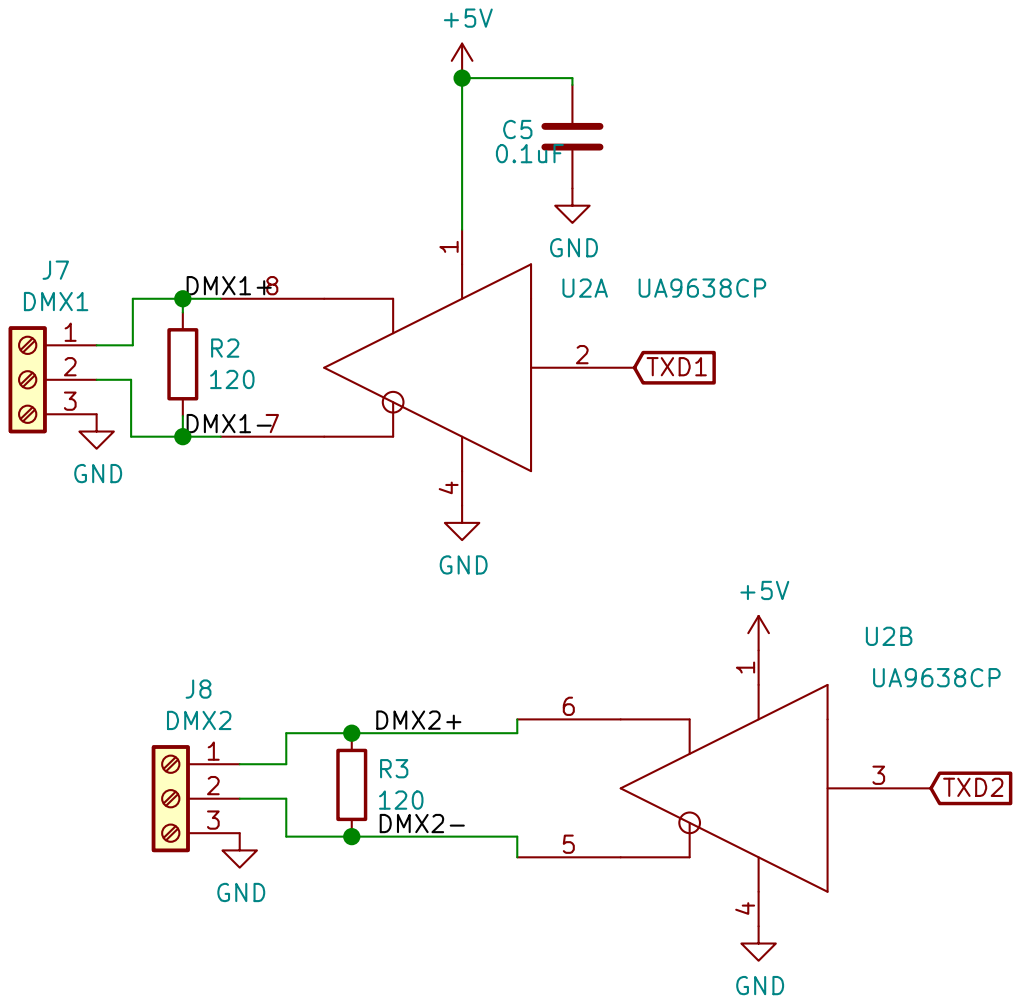
[picture p155: page 3]

File: Serial.sch Sheet: /Serial/ Scott Hanson

Id: 3/3 Title: PB 16 Flex
