computergeek1507/PB_16/Pi_Adapter/Pi_Adapter.pdf

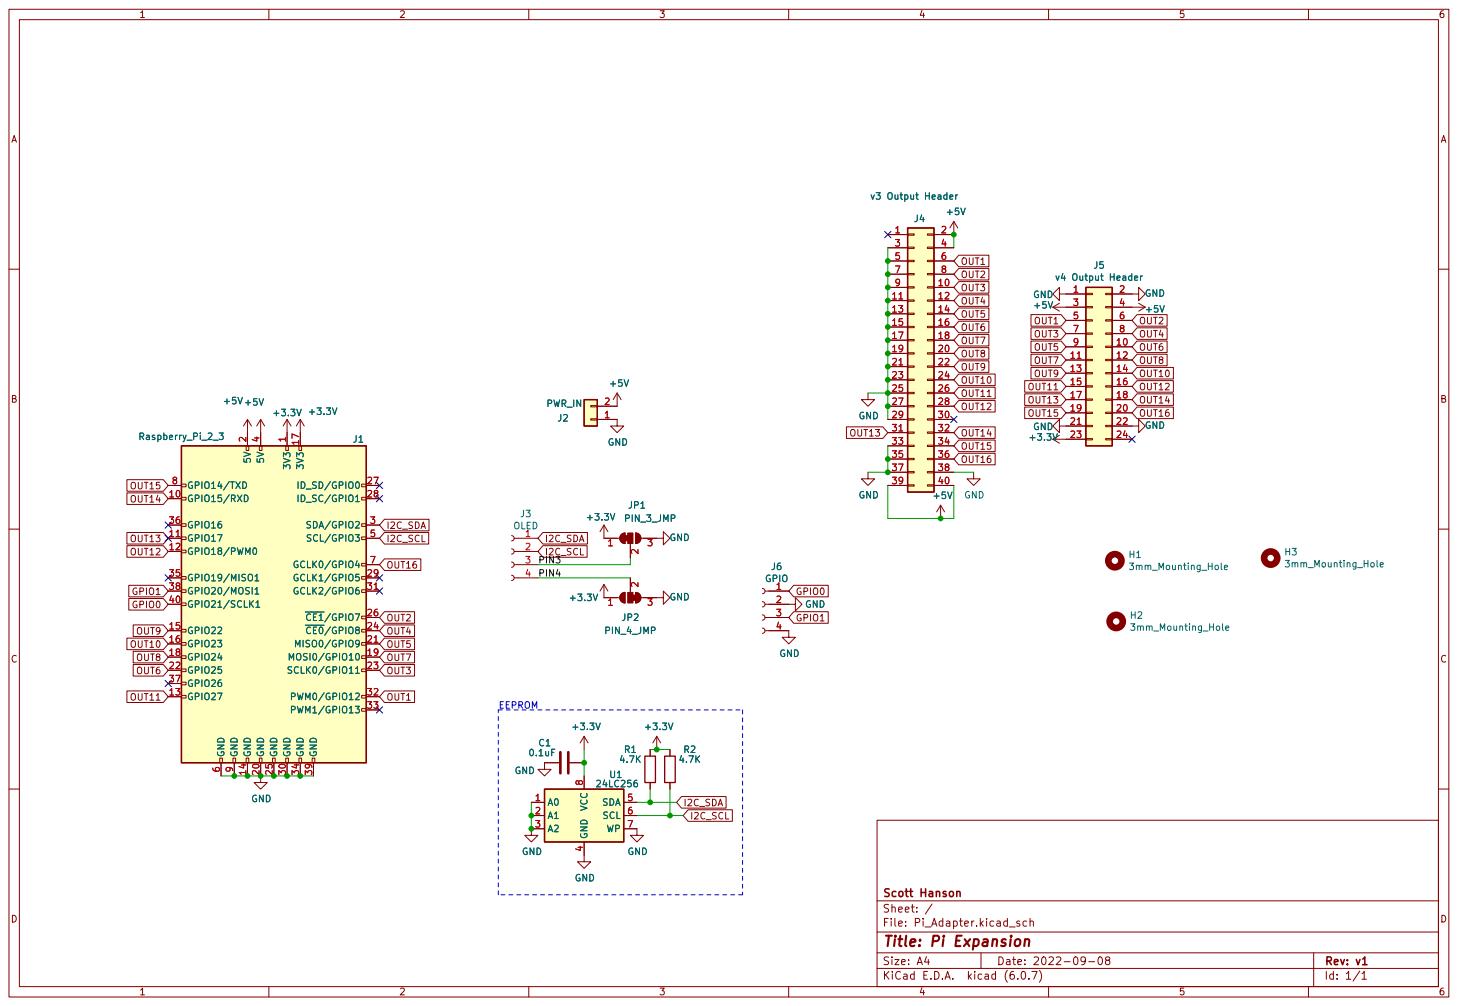
[picture p163: page 1]
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

4 SDA 5 SCL 6 WP 7 VCC

Id: 1/1 Title: Pi Expansion
