computergeek1507/PB_16/PB16_2_PI/PB16_2_PI.pdf

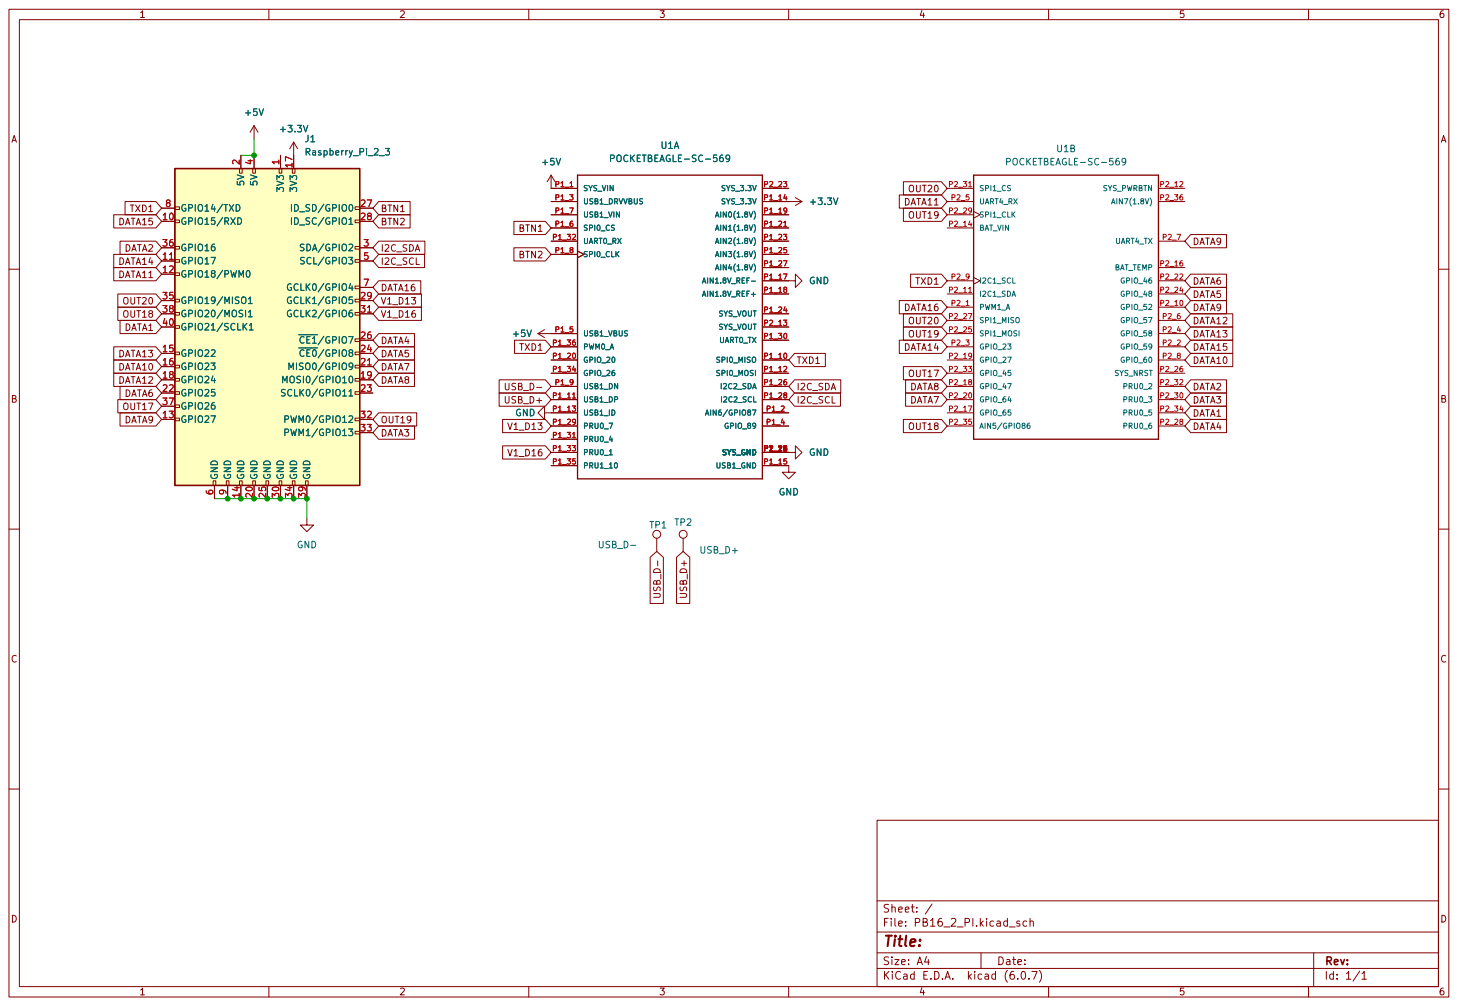
[picture p164: page 1]
