computergeek1507/PB_16/Four_Out/Four_Out.pdf

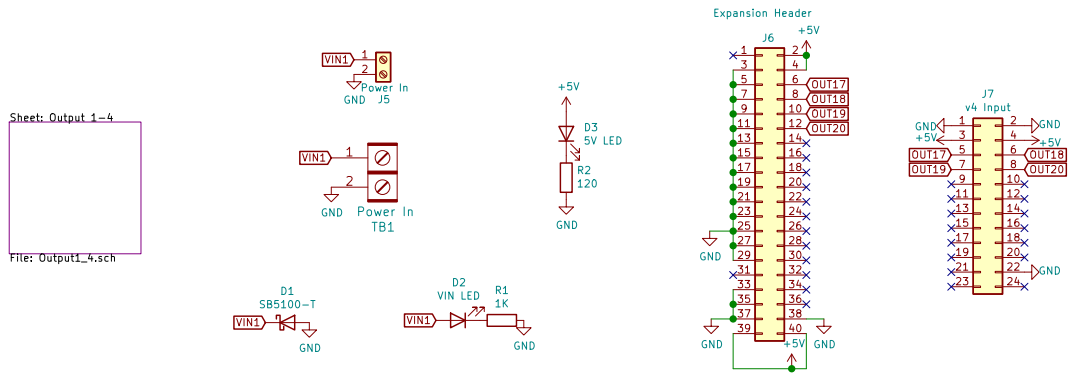
[picture p165: page 1]

11 | 12
13 | 14
15 | 16
17 | 18
19 | 20
21 | 22
23 | 24

File: Four_Out.sch Sheet: / Scott Hanson

Id: 1/2 Title: Four Out

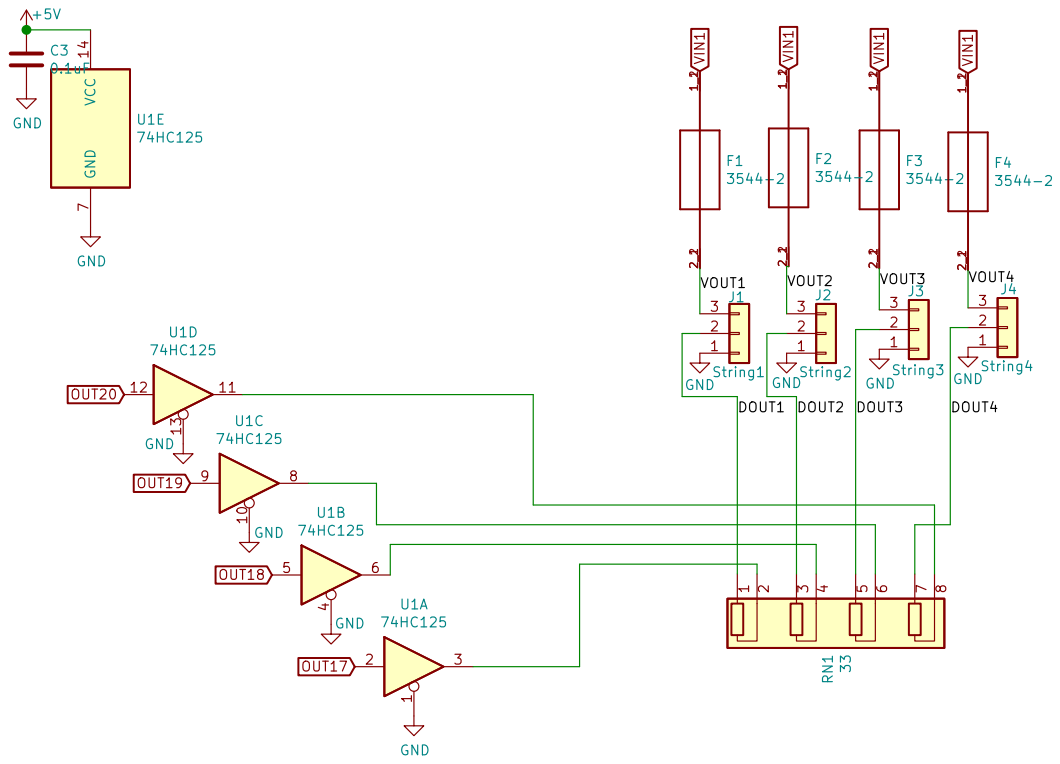
[picture p166: page 2]

Sheet: /Output 1-4/ Scott Hanson
