computergeek1507/PB_16/Diff_Expansion/Diff_Expansion.pdf

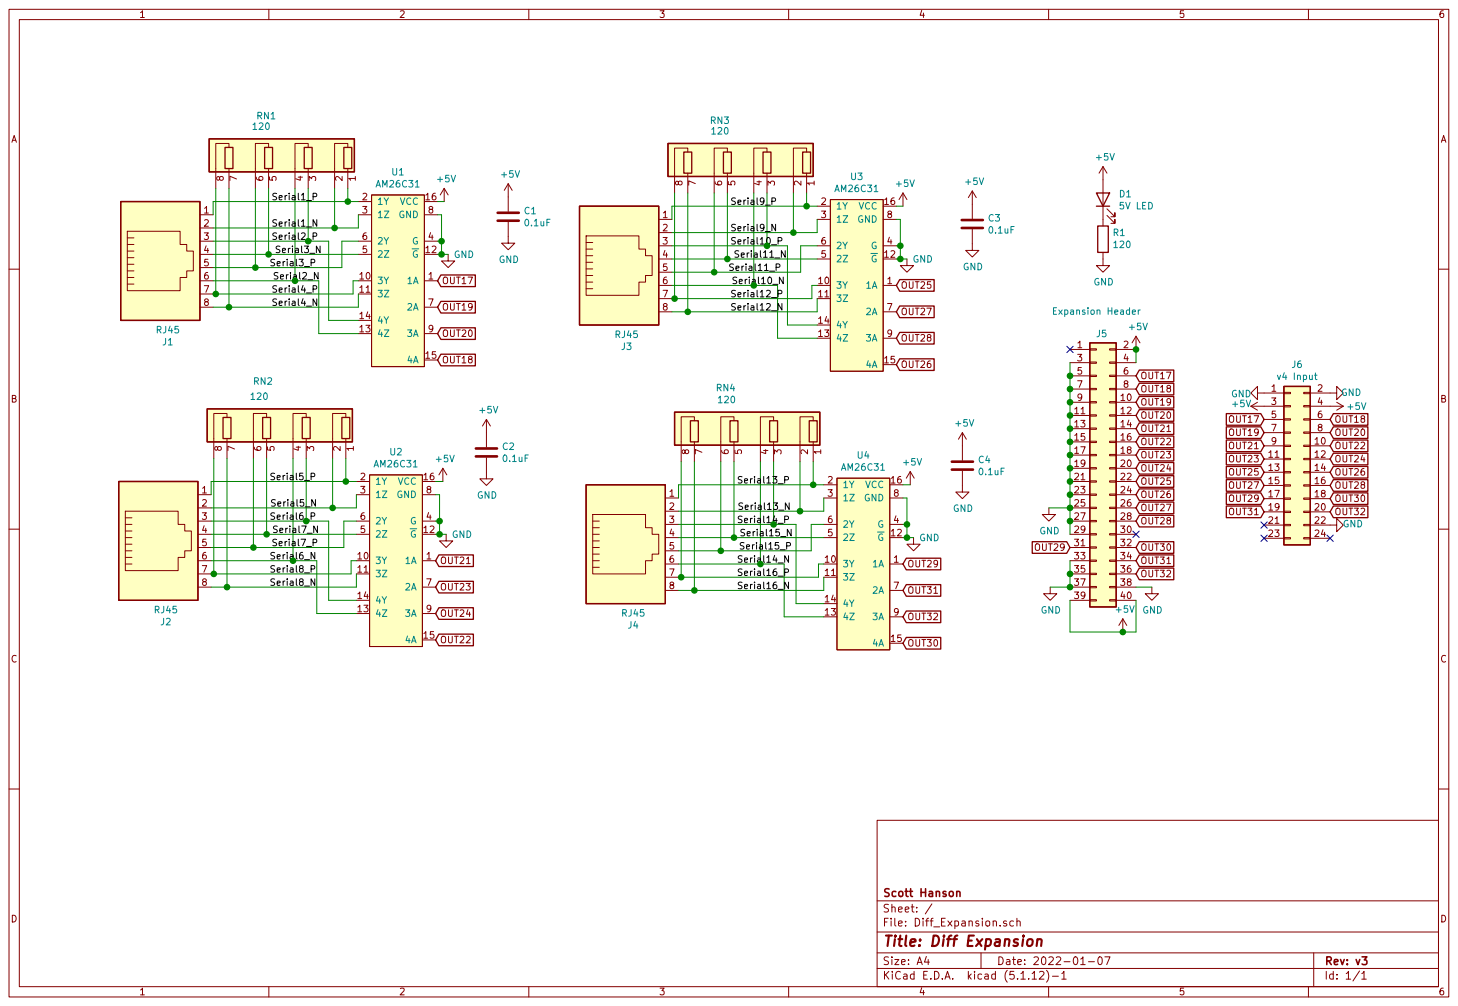
[picture p167: page 1]

3 | Serial2_P

3 | Serial10_P

8 | Serial4_N

7 | | Serial12_P
8 | Serial12_N

9 | 10
11 | 12
13 | 14
15 | 16

19 | 20
21 | 22

File: Diff_Expansion.sch Sheet: / Scott Hanson

Id: 1/1 Title: Diff Expansion
