computergeek1507/PB_16/Receiver_Out/Receiver_Out.pdf

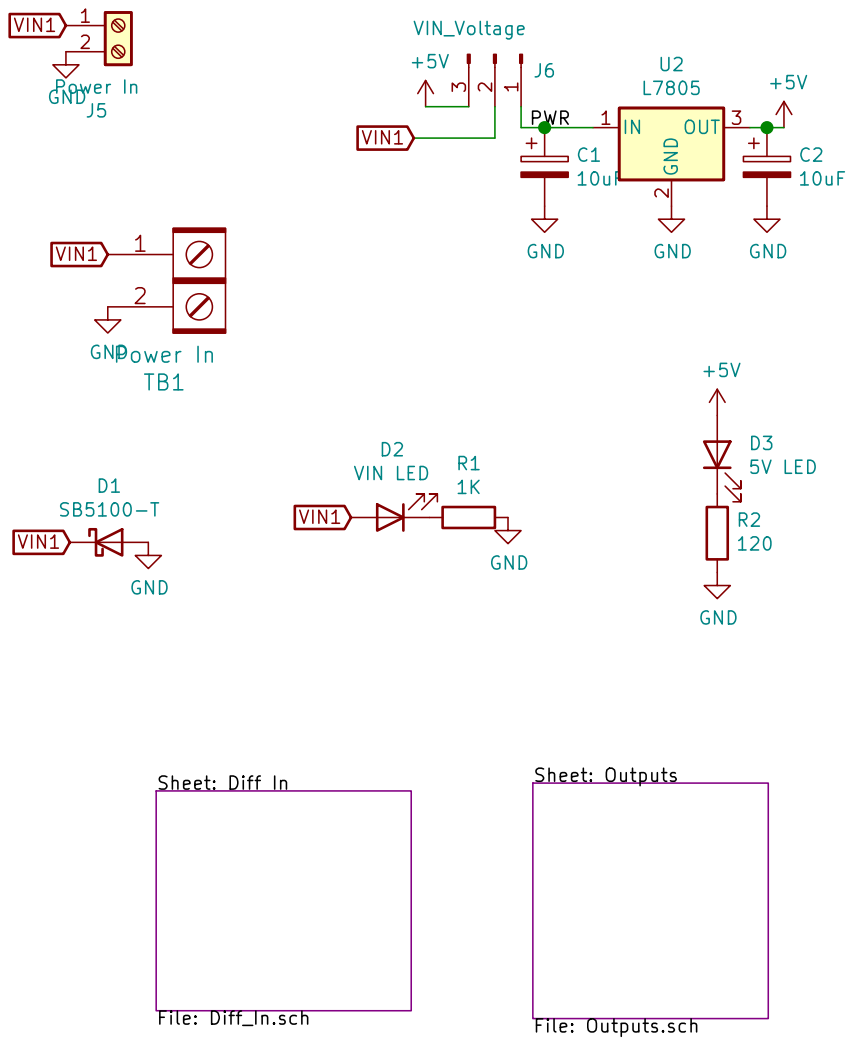
[picture p168: page 1]

File: Receiver_Out.sch Sheet: / Scott Hanson

Id: 1/3 Title: Receiver Out


Sheet: /Outputs/ Scott Hanson

File: Outputs.sch
Id: 2/3 Title: Receiver Out

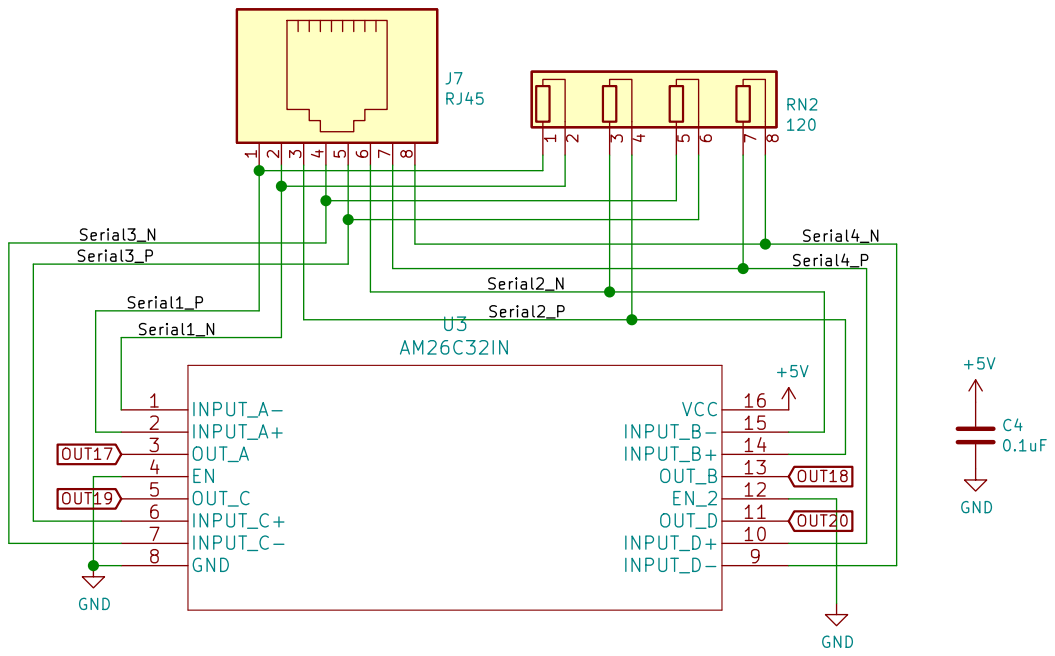
[picture p169: page 3]

Id: 3/3 Title: Receiver Out
