computergeek1507/PB_16/PWR_ADAPTER/PWR_ADAPTER.pdf

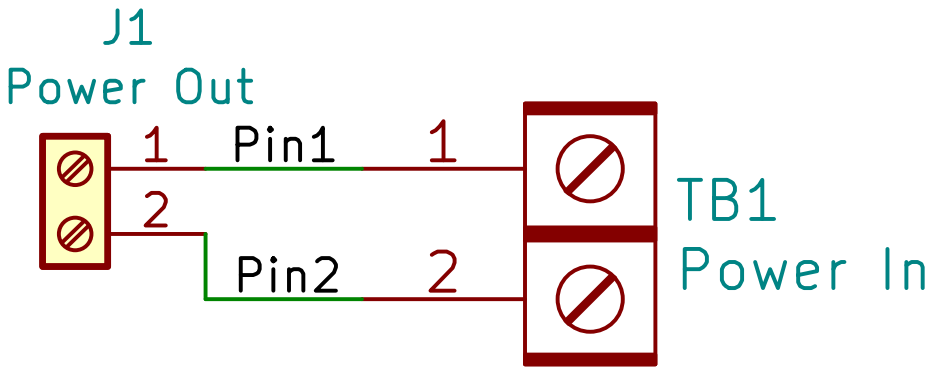
[picture p170: page 1]
