computergeek1507/PB_16/Pwr_Diff_Expansion/Pwr_Diff_Expansion.pdf

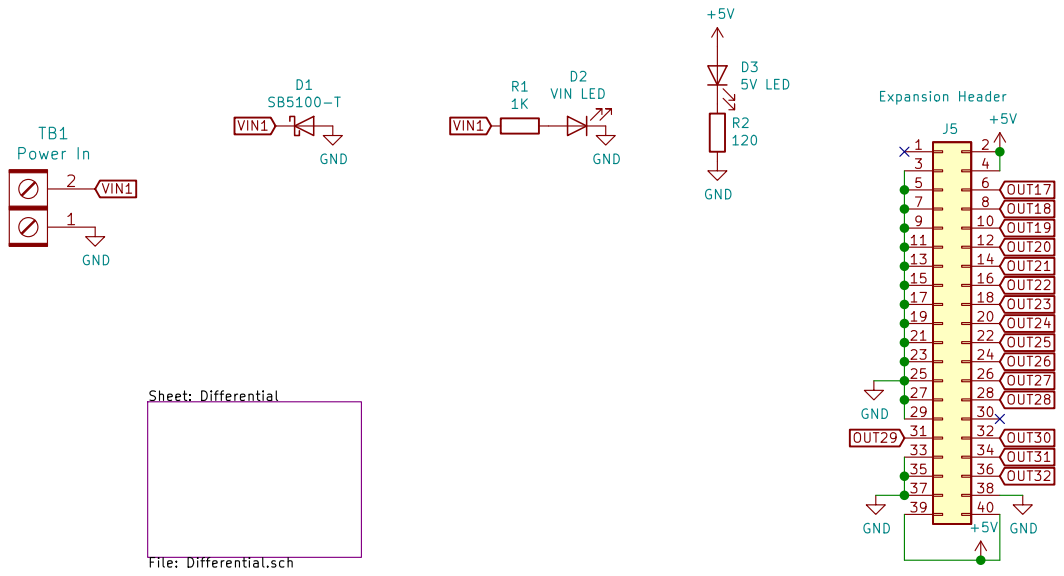
[picture p171: page 1]

File: Pwr_Diff_Expansion.sch Sheet: / Scott Hanson

Id: 1/2 Title: Pwr Diff Expansion

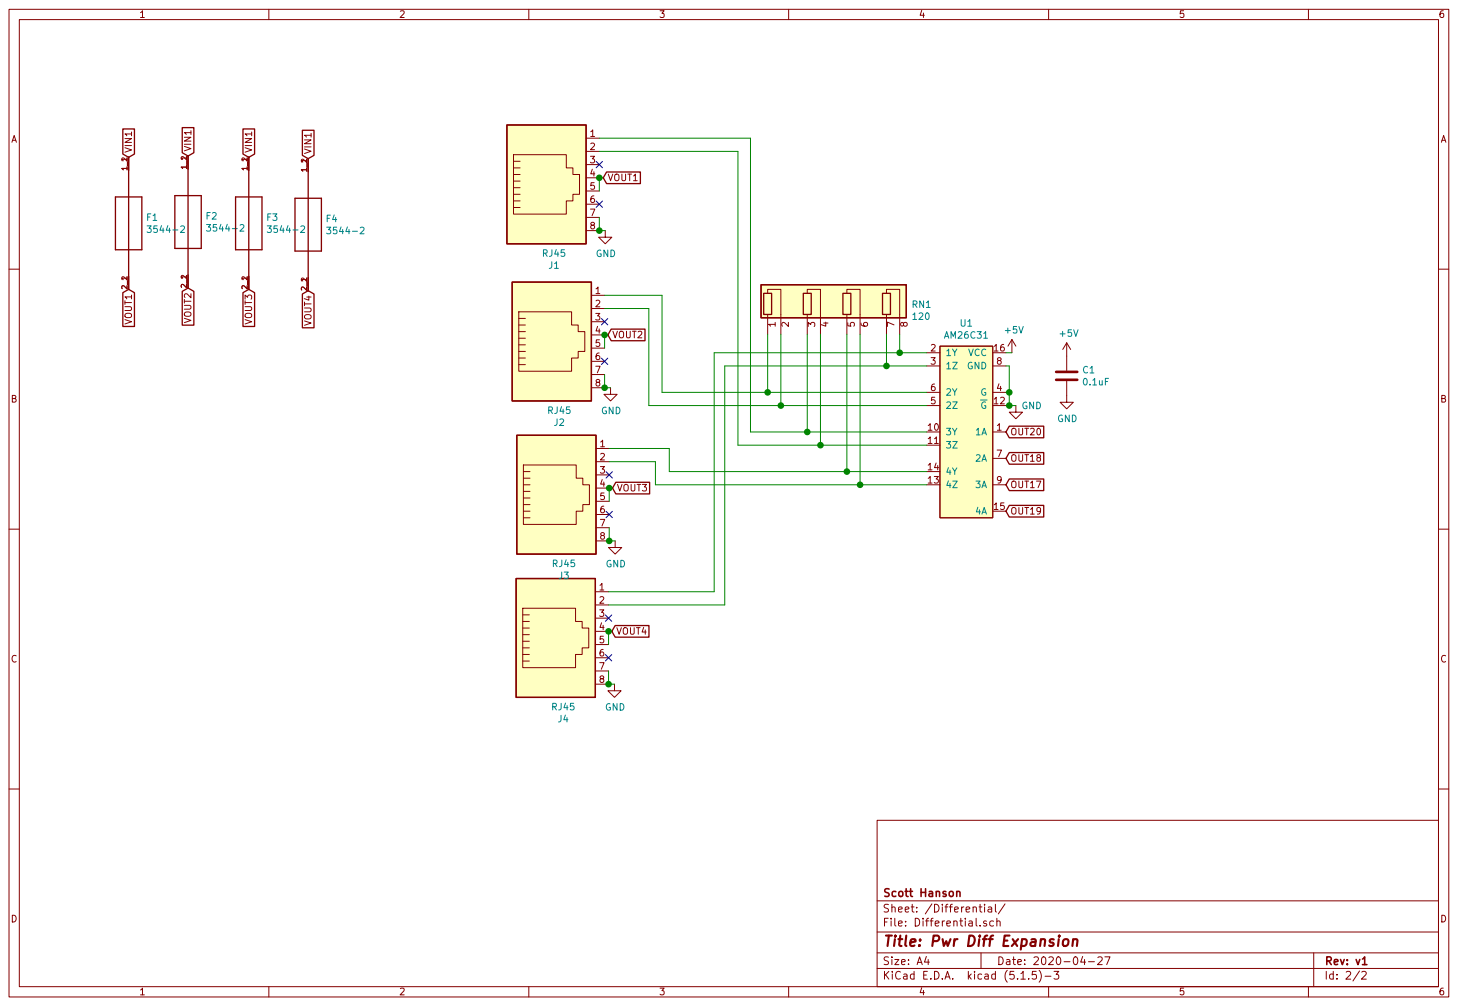
[picture p172: page 2]

File: Differential.sch Sheet: /Differential/ Scott Hanson 12345678

2Y 6
2Z 5 | 12

Id: 2/2 Title: Pwr Diff Expansion
