computergeek1507/PB_16/Single_Receiver_Out/Single_Receiver_Out.pdf

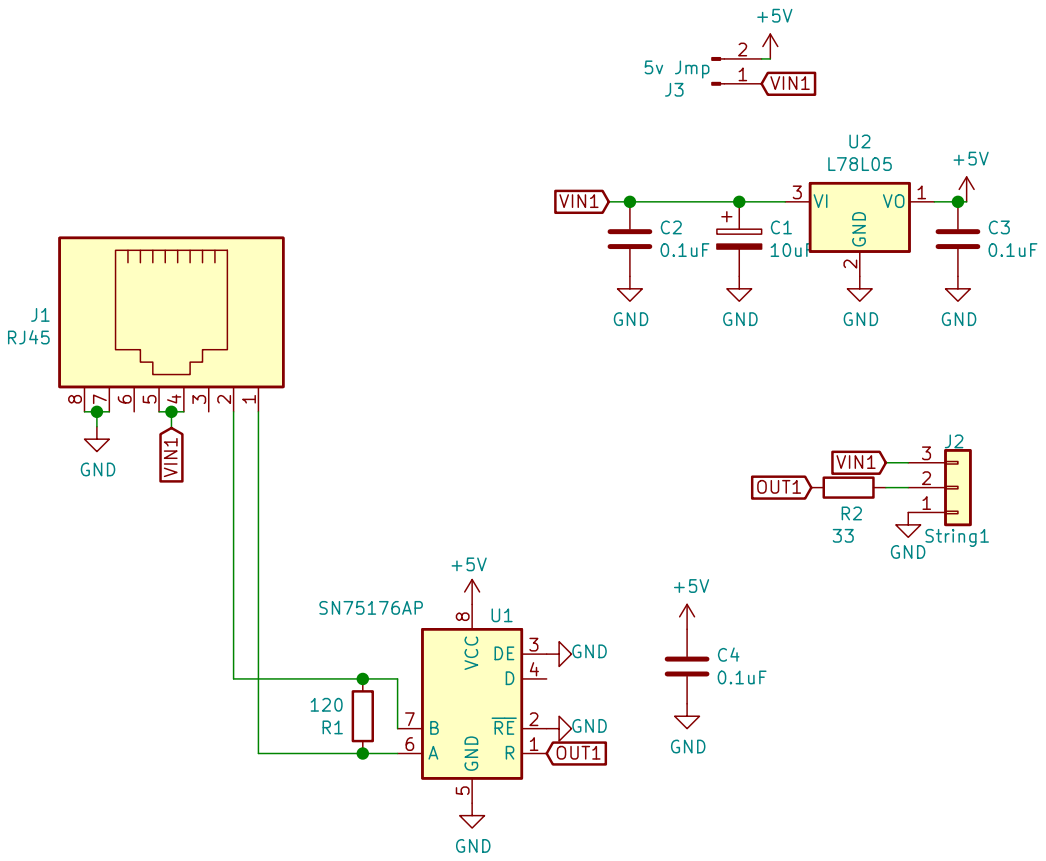
[picture p173: page 1]

File: Single_Receiver_Out.sch Sheet: / Scott Hanson

Id: 1/1 Title: Single Receiver Out
