computergeek1507/PB_16/PB_16_E682/PB_16.pdf

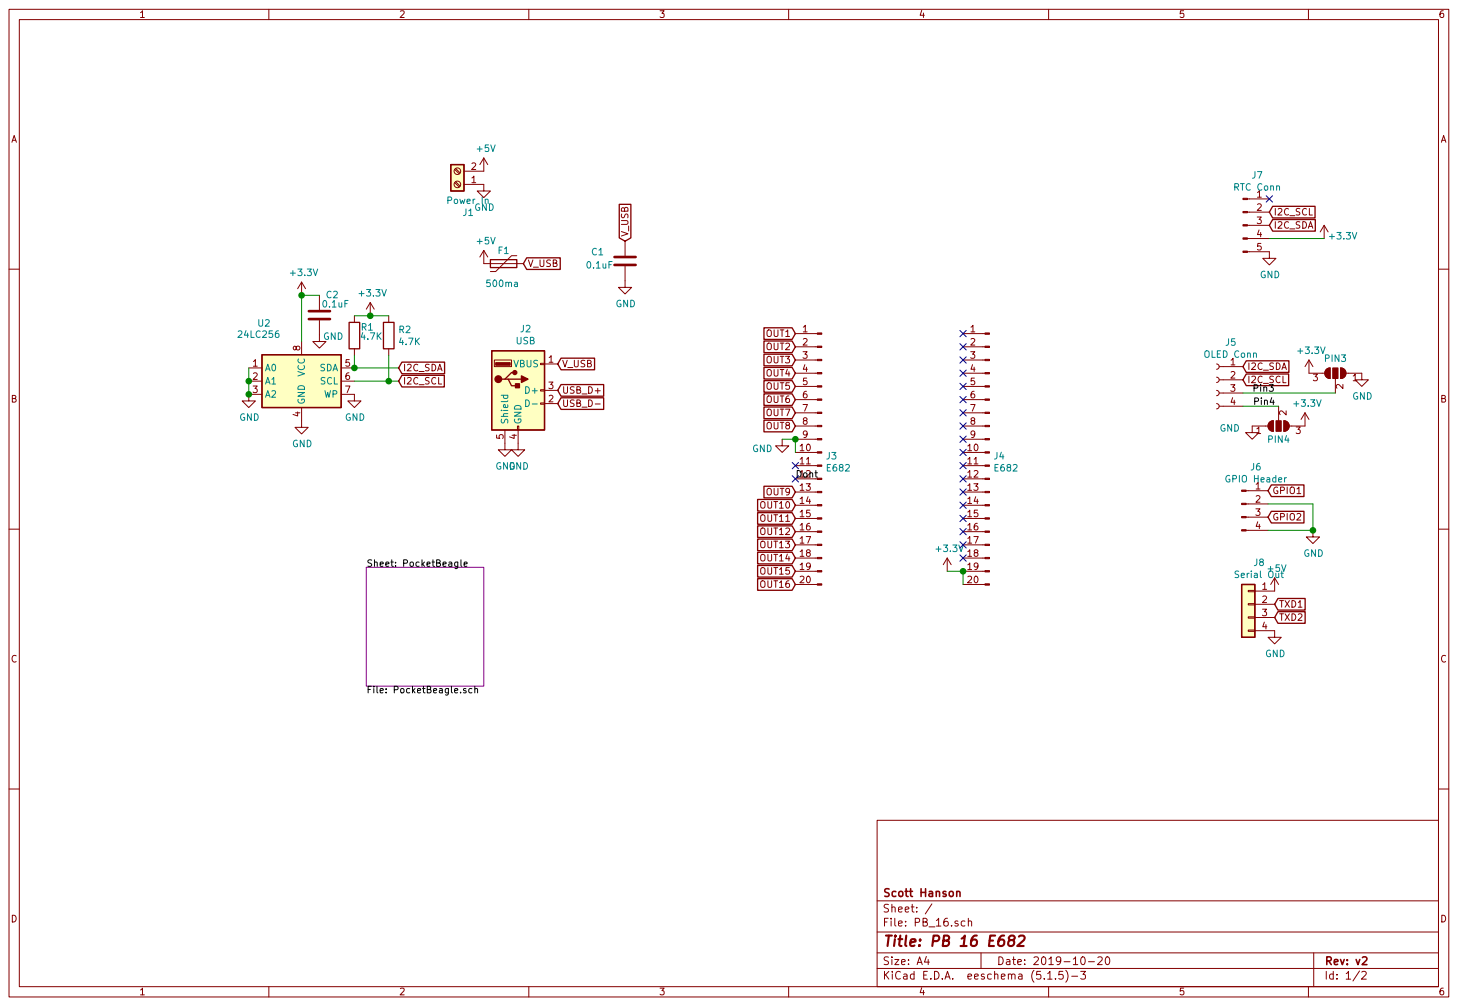
[picture p174: page 1]

4 SDA 5 SCL 6 WP 7 VCC

File: PB_16.sch Sheet: / Scott Hanson

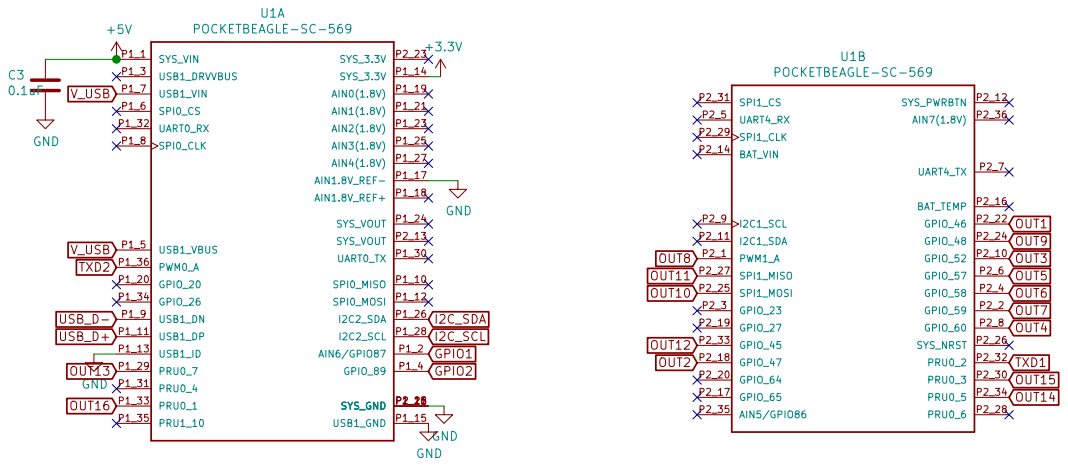
[picture p175: page 2]

Sheet: /PocketBeagle/ Scott Hanson
