computergeek1507/PB_16/PB_16_E682_Serial/PB_16.pdf

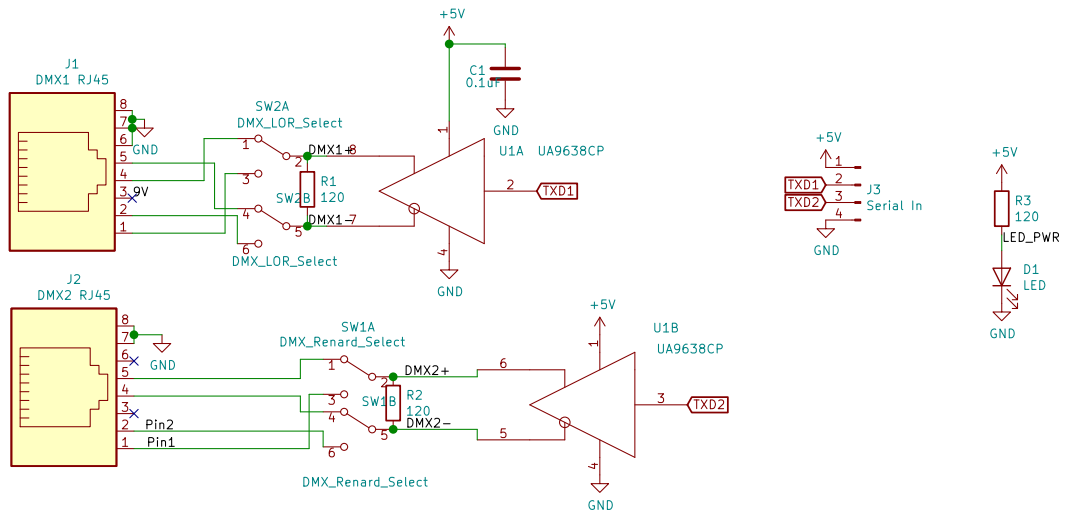
[picture p176: page 1]

File: PB_16.sch Sheet: / Scott Hanson
