computergeek1507/PB_16/Quad_Diff_Out/Quad_Diff_Out.pdf

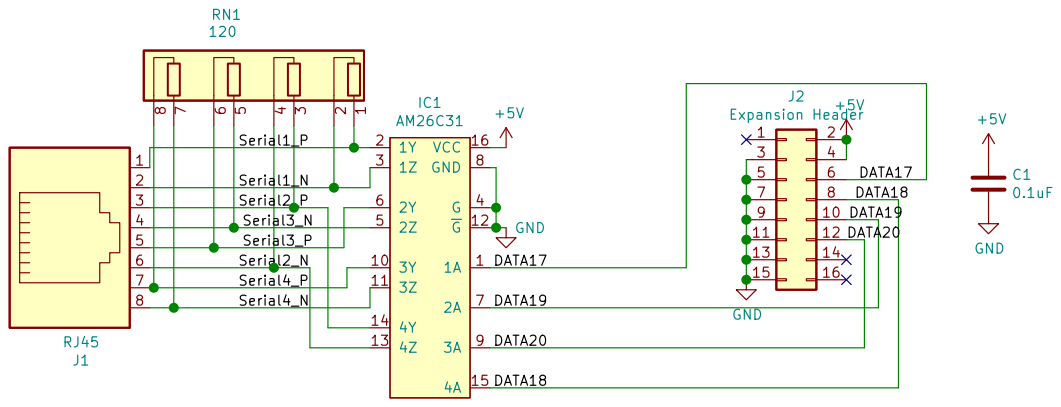
[picture p177: page 1]

9 | 10
11 | 12
13 | 14
15 | 16

File: Quad_Diff_Out.sch Sheet: / Scott Hanson

Id: 1/1 Title: Quad Diff
