computergeek1507/PB_16/Input_Adapter/Input_Adapter.kicad_pcb

## KiCad design Input_Adapter/Input_Adapter.kicad_pcb (2026-03-06)

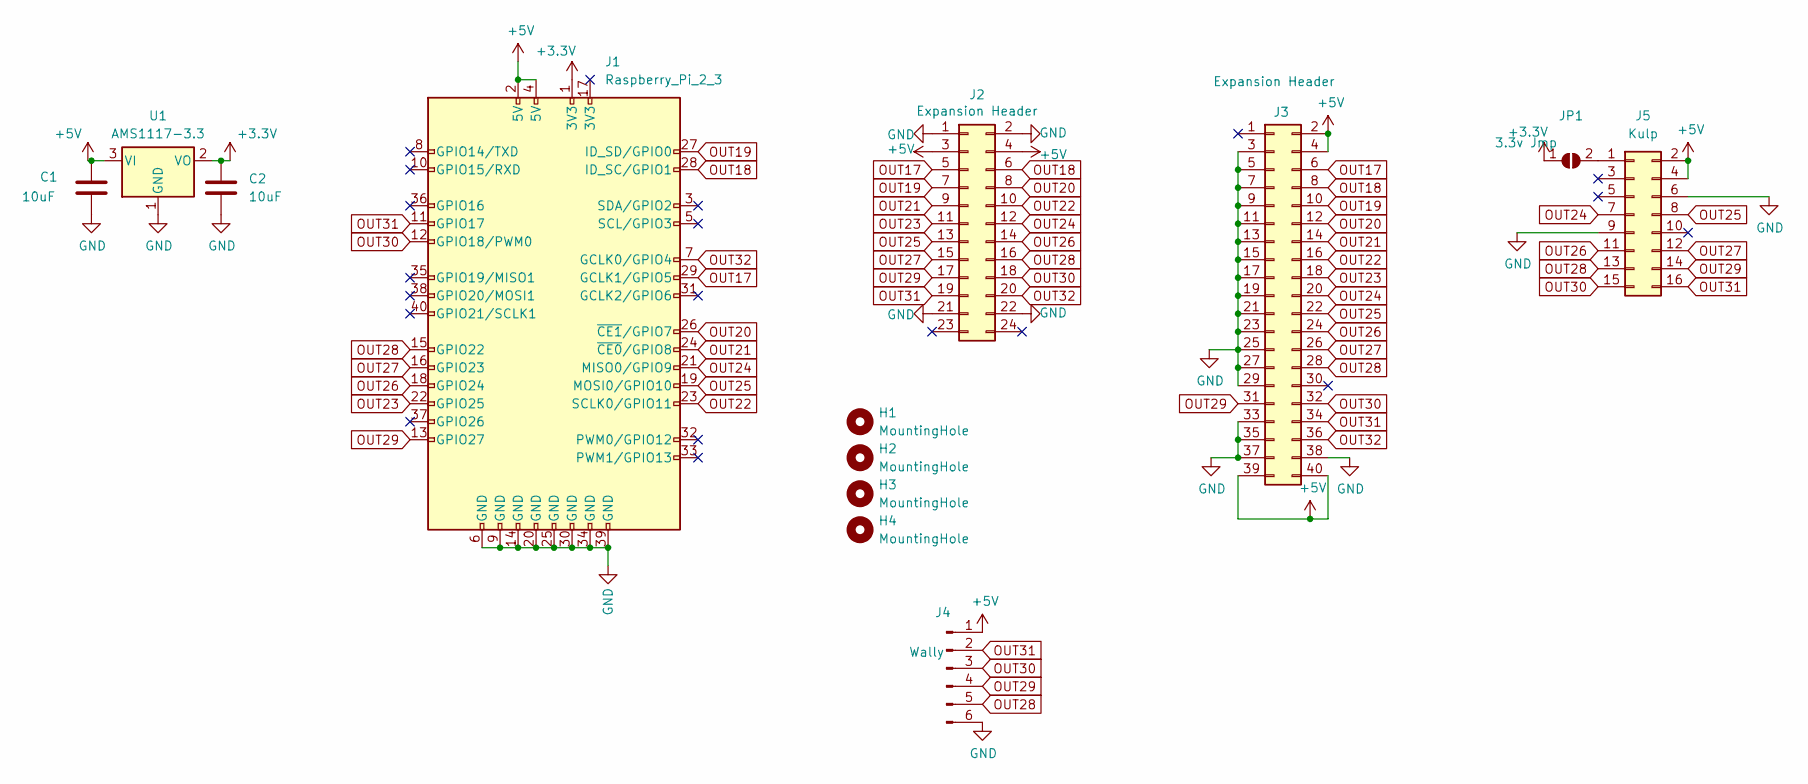
[picture p226: schematic Input_Adapter.kicad_sch, Input2Expansion]

Parts:
C1, C2: 10uF; C_0805_2012Metric_Pad1.18x1.45mm_HandSolder; LCSC C15850
H1, H2, H3, H4: MountingHole; MountingHole_3.2mm_M3
J1: Raspberry_Pi_2_3; Raspberry_Pi_Hat_Socketed_THT_FaceDown_MountingHoles; LCSC C124383
J2: Expansion Header; OST_302-S241; MPN 302-S241; Digi-Key_PN ED10525-ND
J3: Expansion Header; IDC-Header_2x20_P2.54mm_Vertical; MPN SBH11-PBPC-D20-ST-BK; Digi-Key_PN S9175-ND
J4: Wally; JST_XH_B6B-XH-A_1x06_P2.50mm_Vertical; LCSC C144397
J5: Kulp; PinHeader_2x08_P2.54mm_Vertical; LCSC C706898
JP1: 3.3v Jmp; SolderJumper-2_P1.3mm_Open_RoundedPad1.0x1.5mm
U1: AMS1117-3.3; SOT-223-3_TabPin2; LCSC C6186

Connections:
+3V3: C2.1, J1.1 (3V3), JP1.1 (A), U1.2 (VO)
+5V: C1.1, J1.2 (5V), J1.4 (5V), J2.3, J2.4, J3.2, J3.4, J3.39, J3.40, J4.1, J5.2, J5.4, U1.3 (VI)
GND: C1.2, C2.2, J1.6 (GND), J1.9 (GND), J1.14 (GND), J1.20 (GND), J1.25 (GND), J1.30 (GND), J1.34 (GND), J1.39 (GND), J2.1, J2.2, J2.21, J2.22, J3.3, J3.5, J3.7, J3.9, J3.11, J3.13, J3.15, J3.17, J3.19, J3.21, J3.23, J3.25, J3.27, J3.29, J3.33, J3.35, J3.37, J3.38, J4.6, J5.6, J5.9, U1.1 (GND)
unnamed: J5.1, JP1.2 (B)
OUT17: J1.29 (GCLK1/GPIO5), J2.5, J3.6
OUT18: J1.28 (ID_SC/GPIO1), J2.6, J3.8
OUT19: J1.27 (ID_SD/GPIO0), J2.7, J3.10
OUT20: J1.26 (~CE1/GPIO7), J2.8, J3.12
OUT21: J1.24 (~CE0/GPIO8), J2.9, J3.14
OUT22: J1.23 (SCLK0/GPIO11), J2.10, J3.16
OUT23: J1.22 (GPIO25), J2.11, J3.18
OUT24: J1.21 (MISO0/GPIO9), J2.12, J3.20, J5.7
OUT25: J1.19 (MOSI0/GPIO10), J2.13, J3.22, J5.8
OUT26: J1.18 (GPIO24), J2.14, J3.24, J5.11
OUT27: J1.16 (GPIO23), J2.15, J3.26, J5.12
OUT28: J1.15 (GPIO22), J2.16, J3.28, J4.5, J5.13
OUT29: J1.13 (GPIO27), J2.17, J3.31, J4.4, J5.14
OUT30: J1.12 (GPIO18/PWM0), J2.18, J3.32, J4.3, J5.15
OUT31: J1.11 (GPIO17), J2.19, J3.34, J4.2, J5.16
OUT32: J1.7 (GCLK0/GPIO4), J2.20, J3.36

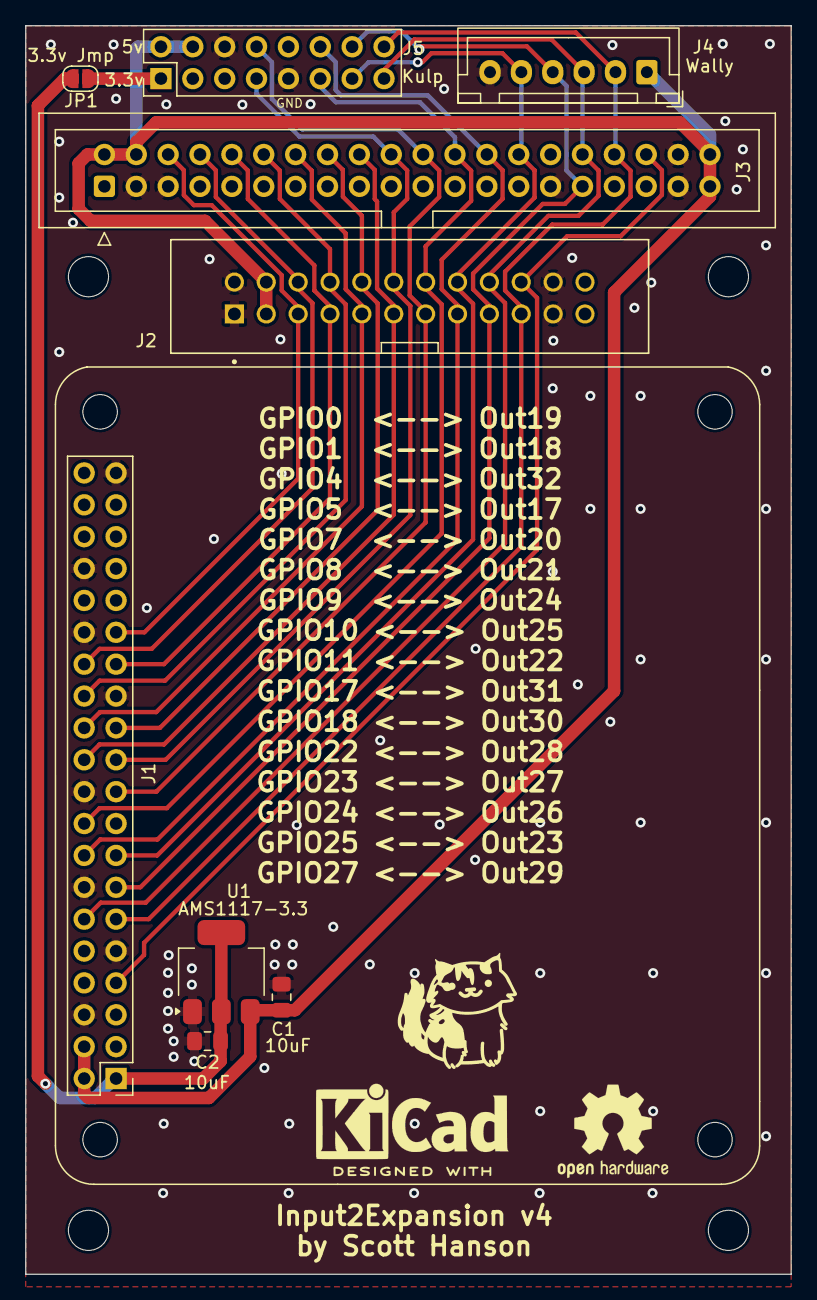
[picture p227: board Input_Adapter.kicad_pcb from above]

Board: 2 copper layers, 61.0 x 99.5 mm, 13 parts (1 on the bottom side), 20 nets.
