computergeek1507/PB_16/Multi_Expansion/Multi_Expansion.kicad_pcb

## KiCad design Multi_Expansion/Multi_Expansion.kicad_pcb (2026-03-06)

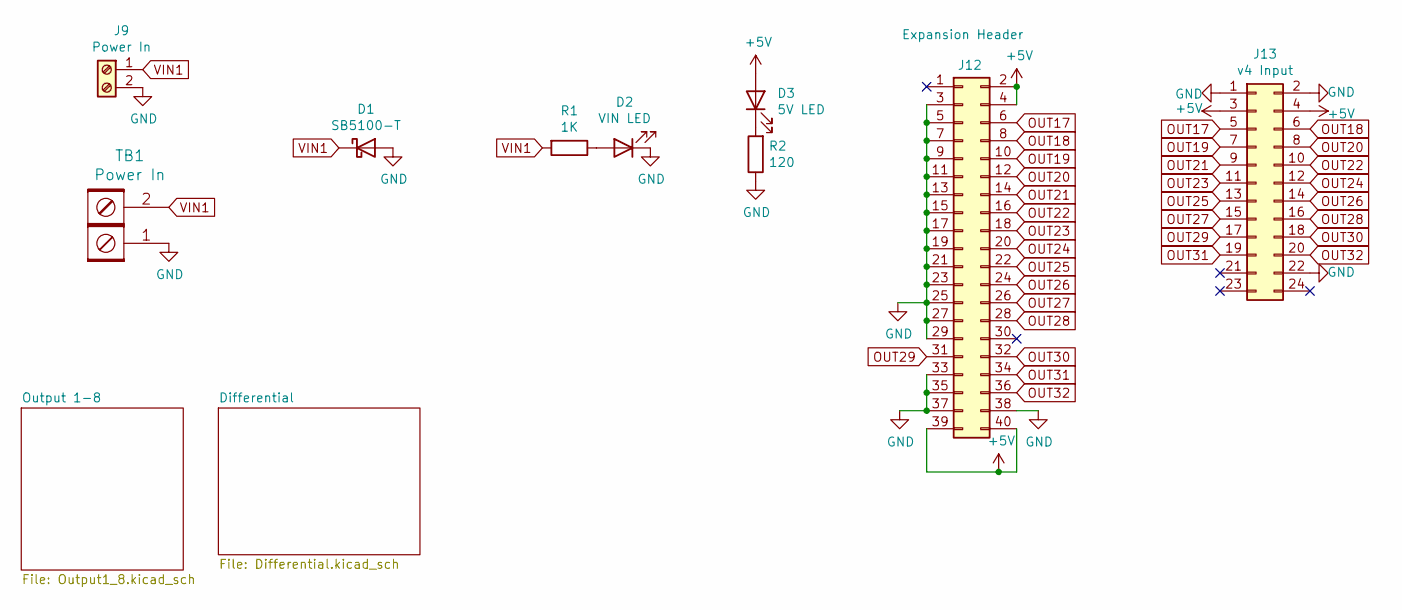
[picture p228: schematic Multi_Expansion.kicad_sch, Multi Expansion]

Parts:
D1: SB5100-T; D_DO-201AD_P12.70mm_Horizontal; MPN SB5100-T; Digi-Key_PN SB5100DICT-ND
D2: VIN LED; LED_D3.0mm_Clear; MPN WP3A8GD; Digi-Key_PN 754-1217-ND
D3: 5V LED; LED_D3.0mm_Clear; MPN WP3A8GD; Digi-Key_PN 754-1217-ND
J9: Power In; TerminalBlock_MetzConnect_Type701_RT11L02HGLU_1x02_P6.35mm_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; Digi-Key_PN ED2675-ND
J12: Expansion Header; IDC-Header_2x20_P2.54mm_Vertical; MPN SBH11-PBPC-D20-ST-BK; Digi-Key_PN S9175-ND
J13: v4 Input; OST_302-S241; MPN 302-S241; Digi-Key_PN ED10525-ND
R1: 1K; R_Axial_DIN0207_L6.3mm_D2.5mm_P7.62mm_Horizontal; MPN CF14JT1K00; Digi-Key_PN CF14JT1K00CT-ND
R2: 120; R_Axial_DIN0207_L6.3mm_D2.5mm_P7.62mm_Horizontal; MPN CF14JT120R; Digi-Key_PN CF14JT120RCT-ND
TB1: Power In; BARRIER_BLOCK_1ROW_2POS_P9.5MM; Digi-Key_PN ED2953-ND

Connections:
+5V: D3.2 (A), J12.2, J12.4, J12.39, J12.40, J13.3, J13.4; also elsewhere on the board
GND: D1.2 (A), D2.1 (K), J9.2, J12.3, J12.5, J12.7, J12.9, J12.11, J12.13, J12.15, J12.17, J12.19, J12.21, J12.23, J12.25, J12.27, J12.29, J12.33, J12.35, J12.37, J12.38, J13.1, J13.2, J13.22, R2.1, TB1.1; also elsewhere on the board
unnamed: D2.2 (A), R1.1
unnamed: D3.1 (K), R2.2
OUT17: J12.6, J13.5; also elsewhere on the board
OUT18: J12.8, J13.6; also elsewhere on the board
OUT19: J12.10, J13.7; also elsewhere on the board
OUT20: J12.12, J13.8; also elsewhere on the board
OUT21: J12.14, J13.9; also elsewhere on the board
OUT22: J12.16, J13.10; also elsewhere on the board
OUT23: J12.18, J13.11; also elsewhere on the board
OUT24: J12.20, J13.12; also elsewhere on the board
OUT25: J12.22, J13.13; also elsewhere on the board
OUT26: J12.24, J13.14; also elsewhere on the board
OUT27: J12.26, J13.15; also elsewhere on the board
OUT28: J12.28, J13.16; also elsewhere on the board
OUT29: J12.31, J13.17; also elsewhere on the board
OUT30: J12.32, J13.18; also elsewhere on the board
OUT31: J12.34, J13.19; also elsewhere on the board
OUT32: J12.36, J13.20; also elsewhere on the board
VIN1: D1.1 (K), J9.1, R1.2, TB1.2; also elsewhere on the board

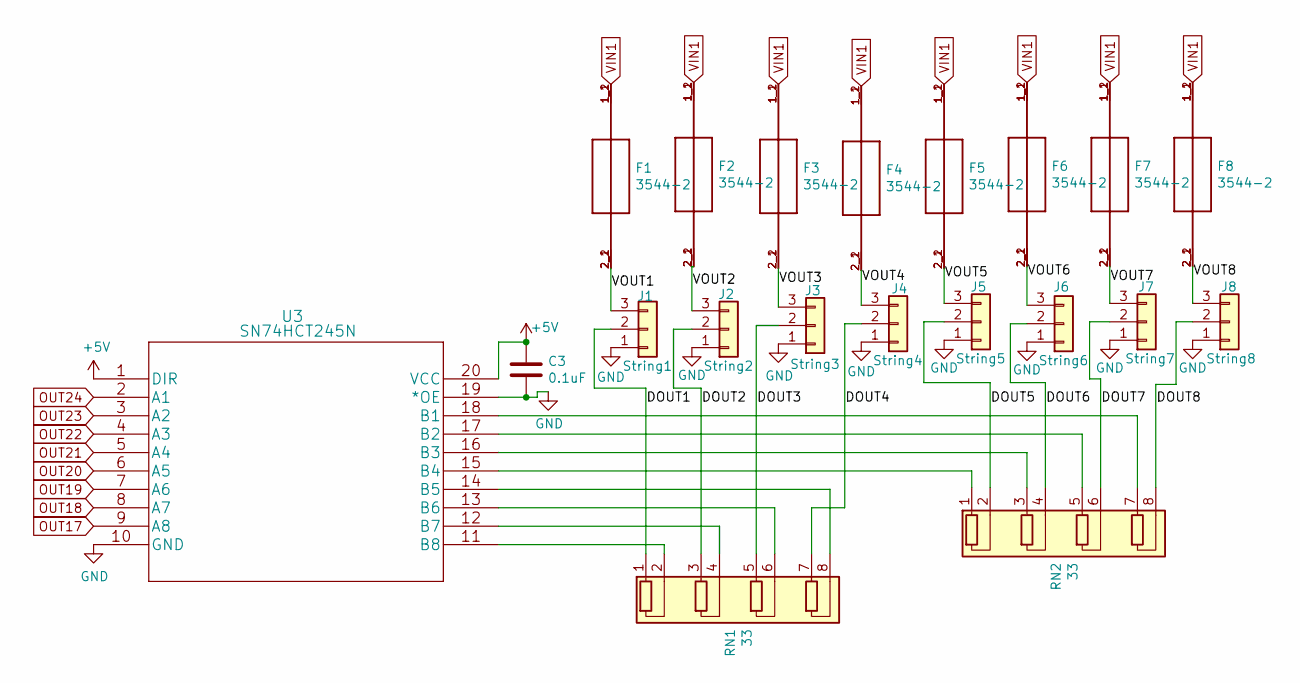
[picture p229: schematic Output1_8.kicad_sch, Multi Expansion]

Parts:
C3: 0.1uF; C_Rect_L7.0mm_W2.0mm_P5.00mm; MPN SR215C104KARTR1; Digi-Key_PN 478-7336-1-ND
F1, F2, F3, F4, F5, F6, F7, F8: 3544-2; FUSE_3544-2; MPN 3544-2; Digi-Key_PN 36-3544-2-ND
J1: String1; PhoenixContact_MCV_1,5_3-G-3.5_1x03_P3.50mm_Vertical; MPN 1843619/OSTTJ0311530; Digi-Key_PN 277-5737-ND/ED10555-ND
J2: String2; PhoenixContact_MCV_1,5_3-G-3.5_1x03_P3.50mm_Vertical; MPN 1843619/OSTTJ0311530; Digi-Key_PN 277-5737-ND/ED10555-ND
J3: String3; PhoenixContact_MCV_1,5_3-G-3.5_1x03_P3.50mm_Vertical; MPN 1843619/OSTTJ0311530; Digi-Key_PN 277-5737-ND/ED10555-ND
J4: String4; PhoenixContact_MCV_1,5_3-G-3.5_1x03_P3.50mm_Vertical; MPN 1843619/OSTTJ0311530; Digi-Key_PN 277-5737-ND/ED10555-ND
J5: String5; PhoenixContact_MCV_1,5_3-G-3.5_1x03_P3.50mm_Vertical; MPN 1843619/OSTTJ0311530; Digi-Key_PN 277-5737-ND/ED10555-ND
J6: String6; PhoenixContact_MCV_1,5_3-G-3.5_1x03_P3.50mm_Vertical; MPN 1843619/OSTTJ0311530; Digi-Key_PN 277-5737-ND/ED10555-ND
J7: String7; PhoenixContact_MCV_1,5_3-G-3.5_1x03_P3.50mm_Vertical; MPN 1843619/OSTTJ0311530; Digi-Key_PN 277-5737-ND/ED10555-ND
J8: String8; PhoenixContact_MCV_1,5_3-G-3.5_1x03_P3.50mm_Vertical; MPN 1843619/OSTTJ0311530; Digi-Key_PN 277-5737-ND/ED10555-ND
RN1, RN2: 33; R_Array_SIP8; MPN 4608X-102-330LF; Digi-Key_PN 4608X-2-330LF-ND
U3: SN74HCT245N; MPN SN74HCT245N; Digi-Key_PN 296-1612-5-ND

Connections:
+5V: C3.1, U3.1 (DIR), U3.20 (VCC); also elsewhere on the board
/Output 1-8/DOUT1: J1.2, RN1.1 (R1.1)
/Output 1-8/DOUT2: J2.2, RN1.3 (R2.1)
/Output 1-8/DOUT3: J3.2, RN1.5 (R3.1)
/Output 1-8/DOUT4: J4.2, RN1.7 (R4.1)
/Output 1-8/DOUT5: J5.2, RN2.2 (R1.2)
/Output 1-8/DOUT6: J6.2, RN2.4 (R2.2)
/Output 1-8/DOUT7: J7.2, RN2.6 (R3.2)
/Output 1-8/DOUT8: J8.2, RN2.8 (R4.2)
/Output 1-8/VOUT1: F1.2_1 (2), F1.2_2 (2), J1.3
/Output 1-8/VOUT2: F2.2_1 (2), F2.2_2 (2), J2.3
/Output 1-8/VOUT3: F3.2_1 (2), F3.2_2 (2), J3.3
/Output 1-8/VOUT4: F4.2_1 (2), F4.2_2 (2), J4.3
/Output 1-8/VOUT5: F5.2_1 (2), F5.2_2 (2), J5.3
/Output 1-8/VOUT6: F6.2_1 (2), F6.2_2 (2), J6.3
/Output 1-8/VOUT7: F7.2_1 (2), F7.2_2 (2), J7.3
/Output 1-8/VOUT8: F8.2_1 (2), F8.2_2 (2), J8.3
GND: C3.2, J1.1, J2.1, J3.1, J4.1, J5.1, J6.1, J7.1, J8.1, U3.10 (GND), U3.19 (*OE); also elsewhere on the board
unnamed: RN1.2 (R1.2), U3.11 (B8)
unnamed: RN1.4 (R2.2), U3.12 (B7)
unnamed: RN1.6 (R3.2), U3.13 (B6)
unnamed: RN1.8 (R4.2), U3.14 (B5)
unnamed: RN2.1 (R1.1), U3.15 (B4)
unnamed: RN2.3 (R2.1), U3.16 (B3)
unnamed: RN2.5 (R3.1), U3.17 (B2)
unnamed: RN2.7 (R4.1), U3.18 (B1)
OUT17: U3.9 (A8); also elsewhere on the board
OUT18: U3.8 (A7); also elsewhere on the board
OUT19: U3.7 (A6); also elsewhere on the board
OUT20: U3.6 (A5); also elsewhere on the board
OUT21: U3.5 (A4); also elsewhere on the board
OUT22: U3.4 (A3); also elsewhere on the board
OUT23: U3.3 (A2); also elsewhere on the board
OUT24: U3.2 (A1); also elsewhere on the board
VIN1: F1.1_1 (1), F1.1_2 (1), F2.1_1 (1), F2.1_2 (1), F3.1_1 (1), F3.1_2 (1), F4.1_1 (1), F4.1_2 (1), F5.1_1 (1), F5.1_2 (1), F6.1_1 (1), F6.1_2 (1), F7.1_1 (1), F7.1_2 (1), F8.1_1 (1), F8.1_2 (1); also elsewhere on the board

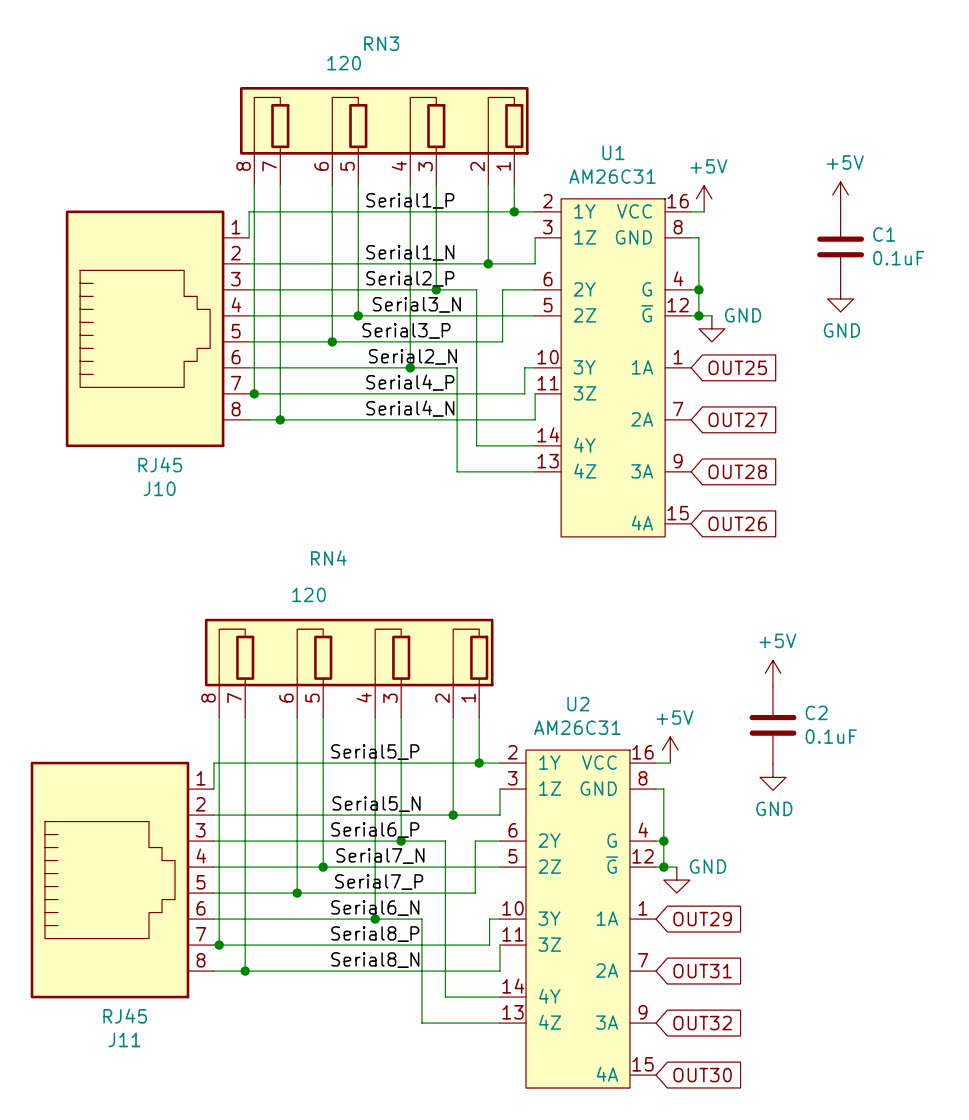
[picture p230: schematic Differential.kicad_sch, Multi Expansion]

Parts:
C1, C2: 0.1uF; C_Rect_L7.0mm_W2.0mm_P5.00mm; MPN SR215C104KARTR1; Digi-Key_PN 478-7336-1-ND
J10, J11: RJ45; RJ45_Amphenol_54602-x08_Horizontal; Digi-Key_PN AE10392-ND
RN3, RN4: 120; R_Array_SIP8; Digi-Key_PN 4608X-2-121LF-ND
U1, U2: AM26C31; DIP-16_W7.62mm; Farnell 4975637

Connections:
+5V: C1.1, C2.1, U1.16 (VCC), U2.16 (VCC); also elsewhere on the board
/Differential/Serial1_N: J10.2, RN3.2 (R1.2), U1.3 (1Z)
/Differential/Serial1_P: J10.1, RN3.1 (R1.1), U1.2 (1Y)
/Differential/Serial2_N: J10.6, RN3.4 (R2.2), U1.13 (4Z)
/Differential/Serial2_P: J10.3, RN3.3 (R2.1), U1.14 (4Y)
/Differential/Serial3_N: J10.4, RN3.5 (R3.1), U1.5 (2Z)
/Differential/Serial3_P: J10.5, RN3.6 (R3.2), U1.6 (2Y)
/Differential/Serial4_N: J10.8, RN3.7 (R4.1), U1.11 (3Z)
/Differential/Serial4_P: J10.7, RN3.8 (R4.2), U1.10 (3Y)
/Differential/Serial5_N: J11.2, RN4.2 (R1.2), U2.3 (1Z)
/Differential/Serial5_P: J11.1, RN4.1 (R1.1), U2.2 (1Y)
/Differential/Serial6_N: J11.6, RN4.4 (R2.2), U2.13 (4Z)
/Differential/Serial6_P: J11.3, RN4.3 (R2.1), U2.14 (4Y)
/Differential/Serial7_N: J11.4, RN4.5 (R3.1), U2.5 (2Z)
/Differential/Serial7_P: J11.5, RN4.6 (R3.2), U2.6 (2Y)
/Differential/Serial8_N: J11.8, RN4.7 (R4.1), U2.11 (3Z)
/Differential/Serial8_P: J11.7, RN4.8 (R4.2), U2.10 (3Y)
GND: C1.2, C2.2, U1.4 (G), U1.8 (GND), U1.12 (~G), U2.4 (G), U2.8 (GND), U2.12 (~G); also elsewhere on the board
OUT25: U1.1 (1A); also elsewhere on the board
OUT26: U1.15 (4A); also elsewhere on the board
OUT27: U1.7 (2A); also elsewhere on the board
OUT28: U1.9 (3A); also elsewhere on the board
OUT29: U2.1 (1A); also elsewhere on the board
OUT30: U2.15 (4A); also elsewhere on the board
OUT31: U2.7 (2A); also elsewhere on the board
OUT32: U2.9 (3A); also elsewhere on the board

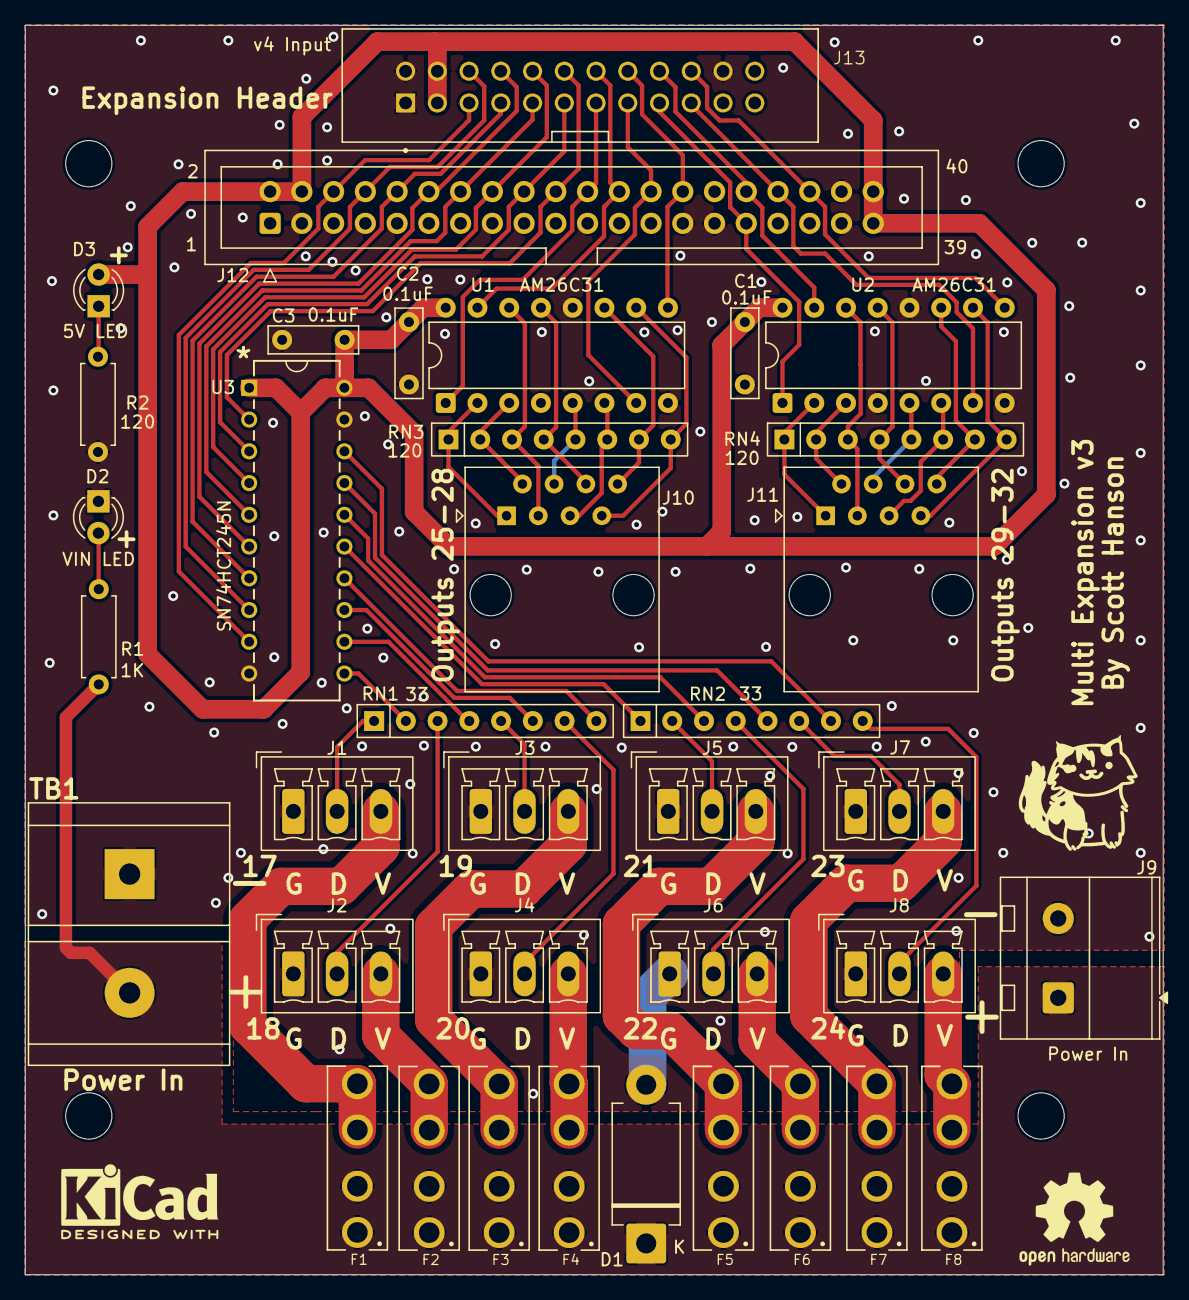
[picture p231: board Multi_Expansion.kicad_pcb from above]

Board: 2 copper layers, 91.0 x 100.0 mm, 37 parts (0 on the bottom side), 61 nets.
