computergeek1507/PB_16/16_Expansion_SMD/PB_16.kicad_pcb

## KiCad design 16_Expansion_SMD/PB_16.kicad_pcb (2026-03-06)

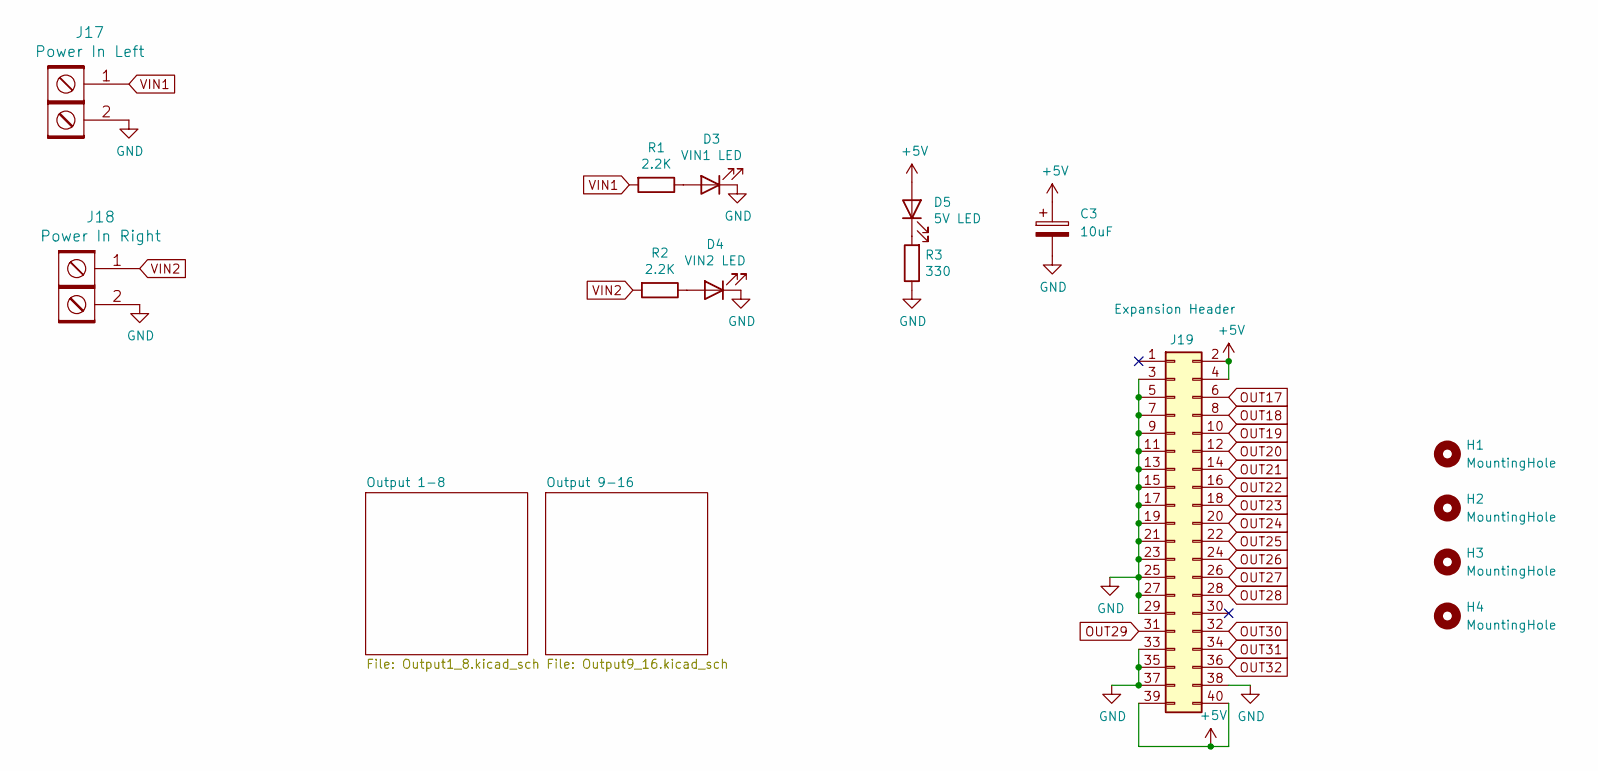
[picture p232: schematic PB_16.kicad_sch, 16 Expansion SMD]

Parts:
C3: 10uF; CP_Elec_4x5.3; MPN UWT1C100MCL1GB; LCSC C72485
D3: VIN1 LED; LED_0603_1608Metric; MPN 150080VS75000; Digi-Key_PN 732-4986-1-ND
D4: VIN2 LED; LED_0603_1608Metric; MPN 150080VS75000; Digi-Key_PN 732-4986-1-ND
D5: 5V LED; LED_0603_1608Metric; MPN 150080VS75000; Digi-Key_PN 732-4986-1-ND
H1, H2, H3, H4: MountingHole; MountingHole_3.7mm
J17: Power In Left; BARRIER_BLOCK_1ROW_2POS_P9.5MM; MPN OSTYK51102030; Digi-Key_PN ED2953-ND
J18: Power In Right; BARRIER_BLOCK_1ROW_2POS_P9.5MM; MPN OSTYK51102030; Digi-Key_PN ED2953-ND
J19: Expansion Header; IDC-Header_2x20_P2.54mm_Vertical; MPN SBH11-PBPC-D20-ST-BK; Digi-Key_PN S9175-ND
R1, R2: 2.2K; R_0603_1608Metric; MPN RC0805FR-071KL; Digi-Key_PN 311-1.00KCRCT-ND
R3: 330; R_0603_1608Metric; MPN RC0805FR-07330RL; Digi-Key_PN 311-330CRCT-ND

Connections:
+5V: C3.1, D5.2 (A), J19.2, J19.4, J19.39, J19.40; also elsewhere on the board
GND: C3.2, D3.1 (K), D4.1 (K), J17.2, J18.2, J19.3, J19.5, J19.7, J19.9, J19.11, J19.13, J19.15, J19.17, J19.19, J19.21, J19.23, J19.25, J19.27, J19.29, J19.33, J19.35, J19.37, J19.38, R3.1; also elsewhere on the board
unnamed: D3.2 (A), R1.1
unnamed: D4.2 (A), R2.1
unnamed: D5.1 (K), R3.2
OUT17: J19.6; also elsewhere on the board
OUT18: J19.8; also elsewhere on the board
OUT19: J19.10; also elsewhere on the board
OUT20: J19.12; also elsewhere on the board
OUT21: J19.14; also elsewhere on the board
OUT22: J19.16; also elsewhere on the board
OUT23: J19.18; also elsewhere on the board
OUT24: J19.20; also elsewhere on the board
OUT25: J19.22; also elsewhere on the board
OUT26: J19.24; also elsewhere on the board
OUT27: J19.26; also elsewhere on the board
OUT28: J19.28; also elsewhere on the board
OUT29: J19.31; also elsewhere on the board
OUT30: J19.32; also elsewhere on the board
OUT31: J19.34; also elsewhere on the board
OUT32: J19.36; also elsewhere on the board
VIN1: J17.1, R1.2; also elsewhere on the board
VIN2: J18.1, R2.2; also elsewhere on the board

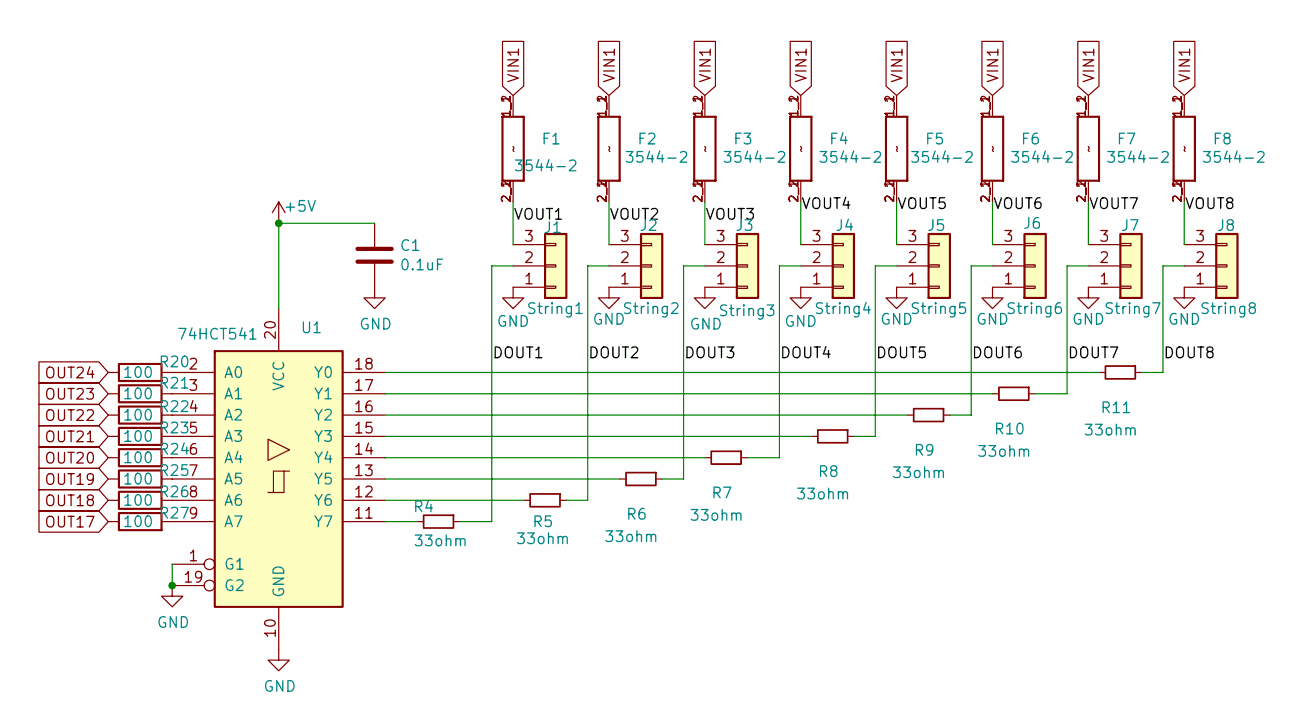
[picture p233: schematic Output1_8.kicad_sch, 16 Expansion SMD]

Parts:
C1: 0.1uF; C_0402_1005Metric; MPN 08055C104KAT2A; Digi-Key_PN 478-1395-1-ND
F1, F2, F3, F4, F5, F6, F7, F8: 3544-2; FUSE_3544-2; MPN 3544-2; Digi-Key_PN 36-3544-2-ND
J1: String1; PhoenixContact_MCV_3.81mm_3.5mm_1x03_Vertical; MPN 1843619/OSTTJ0311530; Digi-Key_PN 277-5737-ND/ED10555-ND
J2: String2; PhoenixContact_MCV_3.81mm_3.5mm_1x03_Vertical; MPN 1843619/OSTTJ0311530; Digi-Key_PN 277-5737-ND/ED10555-ND
J3: String3; PhoenixContact_MCV_3.81mm_3.5mm_1x03_Vertical; MPN 1843619/OSTTJ0311530; Digi-Key_PN 277-5737-ND/ED10555-ND
J4: String4; PhoenixContact_MCV_3.81mm_3.5mm_1x03_Vertical; MPN 1843619/OSTTJ0311530; Digi-Key_PN 277-5737-ND/ED10555-ND
J5: String5; PhoenixContact_MCV_3.81mm_3.5mm_1x03_Vertical; MPN 1843619/OSTTJ0311530; Digi-Key_PN 277-5737-ND/ED10555-ND
J6: String6; PhoenixContact_MCV_3.81mm_3.5mm_1x03_Vertical; MPN 1843619/OSTTJ0311530; Digi-Key_PN 277-5737-ND/ED10555-ND
J7: String7; PhoenixContact_MCV_3.81mm_3.5mm_1x03_Vertical; MPN 1843619/OSTTJ0311530; Digi-Key_PN 277-5737-ND/ED10555-ND
J8: String8; PhoenixContact_MCV_3.81mm_3.5mm_1x03_Vertical; MPN 1843619/OSTTJ0311530; Digi-Key_PN 277-5737-ND/ED10555-ND
R4, R5, R6, R7, R8, R9, R10, R11: 33ohm; R_0603_1608Metric; MPN RC0603JR-0733RL; LCSC_PN C23140
R20, R21, R22, R23, R24, R25, R26, R27: 100; R_0603_1608Metric
U1: 74HCT541; TSSOP-20_4.4x6.5mm_P0.65mm; LCSC C131314

Connections:
+5V: C1.1, U1.20 (VCC); also elsewhere on the board
/Output 1-8/DOUT1: J1.2, R4.1
/Output 1-8/DOUT2: J2.2, R5.1
/Output 1-8/DOUT3: J3.2, R6.1
/Output 1-8/DOUT4: J4.2, R7.1
/Output 1-8/DOUT5: J5.2, R8.1
/Output 1-8/DOUT6: J6.2, R9.1
/Output 1-8/DOUT7: J7.2, R10.1
/Output 1-8/DOUT8: J8.2, R11.1
/Output 1-8/VOUT1: F1.2_1 (2), F1.2_2 (2), J1.3
/Output 1-8/VOUT2: F2.2_1 (2), F2.2_2 (2), J2.3
/Output 1-8/VOUT3: F3.2_1 (2), F3.2_2 (2), J3.3
/Output 1-8/VOUT4: F4.2_1 (2), F4.2_2 (2), J4.3
/Output 1-8/VOUT5: F5.2_1 (2), F5.2_2 (2), J5.3
/Output 1-8/VOUT6: F6.2_1 (2), F6.2_2 (2), J6.3
/Output 1-8/VOUT7: F7.2_1 (2), F7.2_2 (2), J7.3
/Output 1-8/VOUT8: F8.2_1 (2), F8.2_2 (2), J8.3
GND: C1.2, J1.1, J2.1, J3.1, J4.1, J5.1, J6.1, J7.1, J8.1, U1.1 (G1), U1.10 (GND), U1.19 (G2); also elsewhere on the board
unnamed: R20.2, U1.2 (A0)
unnamed: R21.2, U1.3 (A1)
unnamed: R22.2, U1.4 (A2)
unnamed: R23.2, U1.5 (A3)
unnamed: R24.2, U1.6 (A4)
unnamed: R25.2, U1.7 (A5)
unnamed: R26.2, U1.8 (A6)
unnamed: R27.2, U1.9 (A7)
unnamed: R11.2, U1.18 (Y0)
unnamed: R10.2, U1.17 (Y1)
unnamed: R9.2, U1.16 (Y2)
unnamed: R8.2, U1.15 (Y3)
unnamed: R7.2, U1.14 (Y4)
unnamed: R6.2, U1.13 (Y5)
unnamed: R5.2, U1.12 (Y6)
unnamed: R4.2, U1.11 (Y7)
OUT17: R27.1; also elsewhere on the board
OUT18: R26.1; also elsewhere on the board
OUT19: R25.1; also elsewhere on the board
OUT20: R24.1; also elsewhere on the board
OUT21: R23.1; also elsewhere on the board
OUT22: R22.1; also elsewhere on the board
OUT23: R21.1; also elsewhere on the board
OUT24: R20.1; also elsewhere on the board
VIN1: F1.1_1 (1), F1.1_2 (1), F2.1_1 (1), F2.1_2 (1), F3.1_1 (1), F3.1_2 (1), F4.1_1 (1), F4.1_2 (1), F5.1_1 (1), F5.1_2 (1), F6.1_1 (1), F6.1_2 (1), F7.1_1 (1), F7.1_2 (1), F8.1_1 (1), F8.1_2 (1); also elsewhere on the board

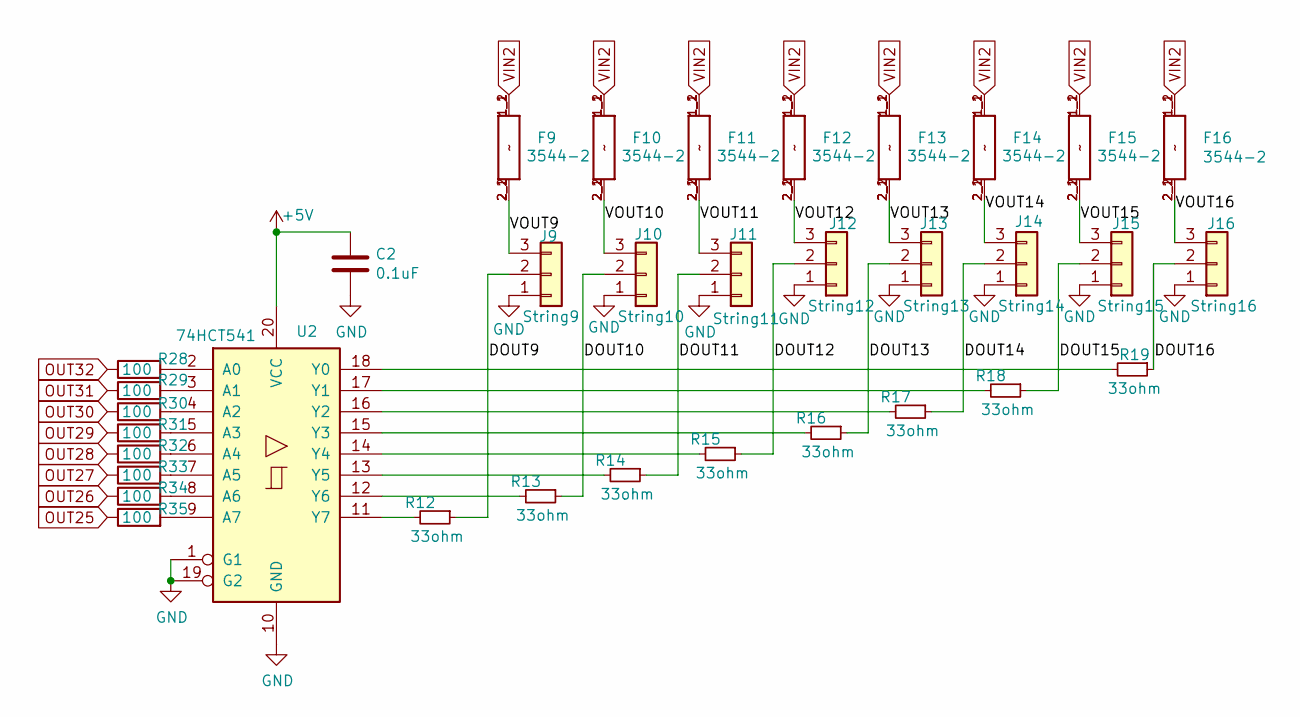
[picture p234: schematic Output9_16.kicad_sch, 16 Expansion SMD]

Parts:
C2: 0.1uF; C_0402_1005Metric; MPN 08055C104KAT2A; Digi-Key_PN 478-1395-1-ND
F9, F10, F11, F12, F13, F14, F15, F16: 3544-2; FUSE_3544-2; MPN 3544-2; Digi-Key_PN 36-3544-2-ND
J9: String9; PhoenixContact_MCV_3.81mm_3.5mm_1x03_Vertical; MPN 1843619/OSTTJ0311530; Digi-Key_PN 277-5737-ND/ED10555-ND
J10: String10; PhoenixContact_MCV_3.81mm_3.5mm_1x03_Vertical; MPN 1843619/OSTTJ0311530; Digi-Key_PN 277-5737-ND/ED10555-ND
J11: String11; PhoenixContact_MCV_3.81mm_3.5mm_1x03_Vertical; MPN 1843619/OSTTJ0311530; Digi-Key_PN 277-5737-ND/ED10555-ND
J12: String12; PhoenixContact_MCV_3.81mm_3.5mm_1x03_Vertical; MPN 1843619/OSTTJ0311530; Digi-Key_PN 277-5737-ND/ED10555-ND
J13: String13; PhoenixContact_MCV_3.81mm_3.5mm_1x03_Vertical; MPN 1843619/OSTTJ0311530; Digi-Key_PN 277-5737-ND/ED10555-ND
J14: String14; PhoenixContact_MCV_3.81mm_3.5mm_1x03_Vertical; MPN 1843619/OSTTJ0311530; Digi-Key_PN 277-5737-ND/ED10555-ND
J15: String15; PhoenixContact_MCV_3.81mm_3.5mm_1x03_Vertical; MPN 1843619/OSTTJ0311530; Digi-Key_PN 277-5737-ND/ED10555-ND
J16: String16; PhoenixContact_MCV_3.81mm_3.5mm_1x03_Vertical; MPN 1843619/OSTTJ0311530; Digi-Key_PN 277-5737-ND/ED10555-ND
R12, R13, R14, R15, R16, R17, R18, R19: 33ohm; R_0603_1608Metric; MPN RC0603JR-0733RL; LCSC_PN C23140
R28, R29, R30, R31, R32, R33, R34, R35: 100; R_0603_1608Metric
U2: 74HCT541; TSSOP-20_4.4x6.5mm_P0.65mm; LCSC C131314

Connections:
+5V: C2.1, U2.20 (VCC); also elsewhere on the board
/Output 9-16/DOUT9: J9.2, R12.1
/Output 9-16/DOUT10: J10.2, R13.1
/Output 9-16/DOUT11: J11.2, R14.1
/Output 9-16/DOUT12: J12.2, R15.1
/Output 9-16/DOUT13: J13.2, R16.1
/Output 9-16/DOUT14: J14.2, R17.1
/Output 9-16/DOUT15: J15.2, R18.1
/Output 9-16/DOUT16: J16.2, R19.1
/Output 9-16/VOUT9: F9.2_1 (2), F9.2_2 (2), J9.3
/Output 9-16/VOUT10: F10.2_1 (2), F10.2_2 (2), J10.3
/Output 9-16/VOUT11: F11.2_1 (2), F11.2_2 (2), J11.3
/Output 9-16/VOUT12: F12.2_1 (2), F12.2_2 (2), J12.3
/Output 9-16/VOUT13: F13.2_1 (2), F13.2_2 (2), J13.3
/Output 9-16/VOUT14: F14.2_1 (2), F14.2_2 (2), J14.3
/Output 9-16/VOUT15: F15.2_1 (2), F15.2_2 (2), J15.3
/Output 9-16/VOUT16: F16.2_1 (2), F16.2_2 (2), J16.3
GND: C2.2, J9.1, J10.1, J11.1, J12.1, J13.1, J14.1, J15.1, J16.1, U2.1 (G1), U2.10 (GND), U2.19 (G2); also elsewhere on the board
unnamed: R28.2, U2.2 (A0)
unnamed: R29.2, U2.3 (A1)
unnamed: R30.2, U2.4 (A2)
unnamed: R31.2, U2.5 (A3)
unnamed: R32.2, U2.6 (A4)
unnamed: R33.2, U2.7 (A5)
unnamed: R34.2, U2.8 (A6)
unnamed: R35.2, U2.9 (A7)
unnamed: R19.2, U2.18 (Y0)
unnamed: R18.2, U2.17 (Y1)
unnamed: R17.2, U2.16 (Y2)
unnamed: R16.2, U2.15 (Y3)
unnamed: R15.2, U2.14 (Y4)
unnamed: R14.2, U2.13 (Y5)
unnamed: R13.2, U2.12 (Y6)
unnamed: R12.2, U2.11 (Y7)
OUT25: R35.1; also elsewhere on the board
OUT26: R34.1; also elsewhere on the board
OUT27: R33.1; also elsewhere on the board
OUT28: R32.1; also elsewhere on the board
OUT29: R31.1; also elsewhere on the board
OUT30: R30.1; also elsewhere on the board
OUT31: R29.1; also elsewhere on the board
OUT32: R28.1; also elsewhere on the board
VIN2: F9.1_1 (1), F9.1_2 (1), F10.1_1 (1), F10.1_2 (1), F11.1_1 (1), F11.1_2 (1), F12.1_1 (1), F12.1_2 (1), F13.1_1 (1), F13.1_2 (1), F14.1_1 (1), F14.1_2 (1), F15.1_1 (1), F15.1_2 (1), F16.1_1 (1), F16.1_2 (1); also elsewhere on the board

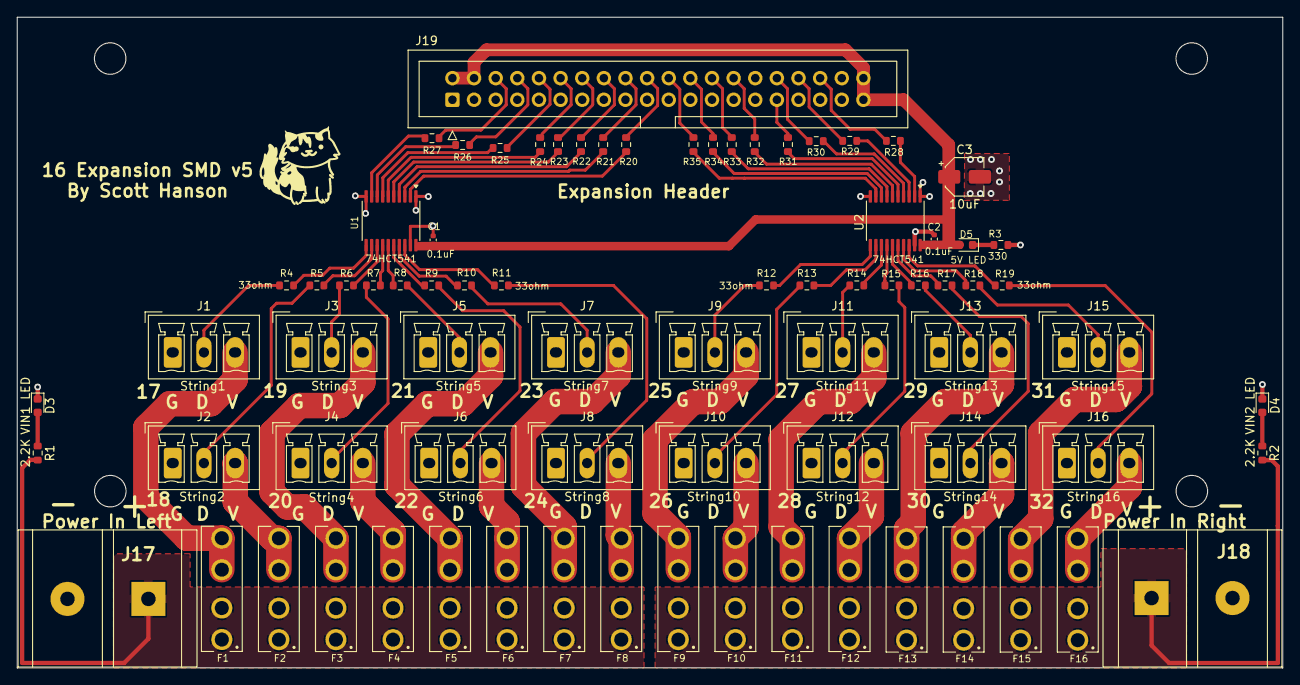
[picture p235: board 16_Expansion_SMD/PB_16.kicad_pcb from above]

Board: 2 copper layers, 148.6 x 76.4 mm, 82 parts (0 on the bottom side), 87 nets.
