computergeek1507/PB_16/Diff_Expansion/Diff_Expansion.kicad_pcb

## KiCad design Diff_Expansion/Diff_Expansion.kicad_pcb (2026-03-06)

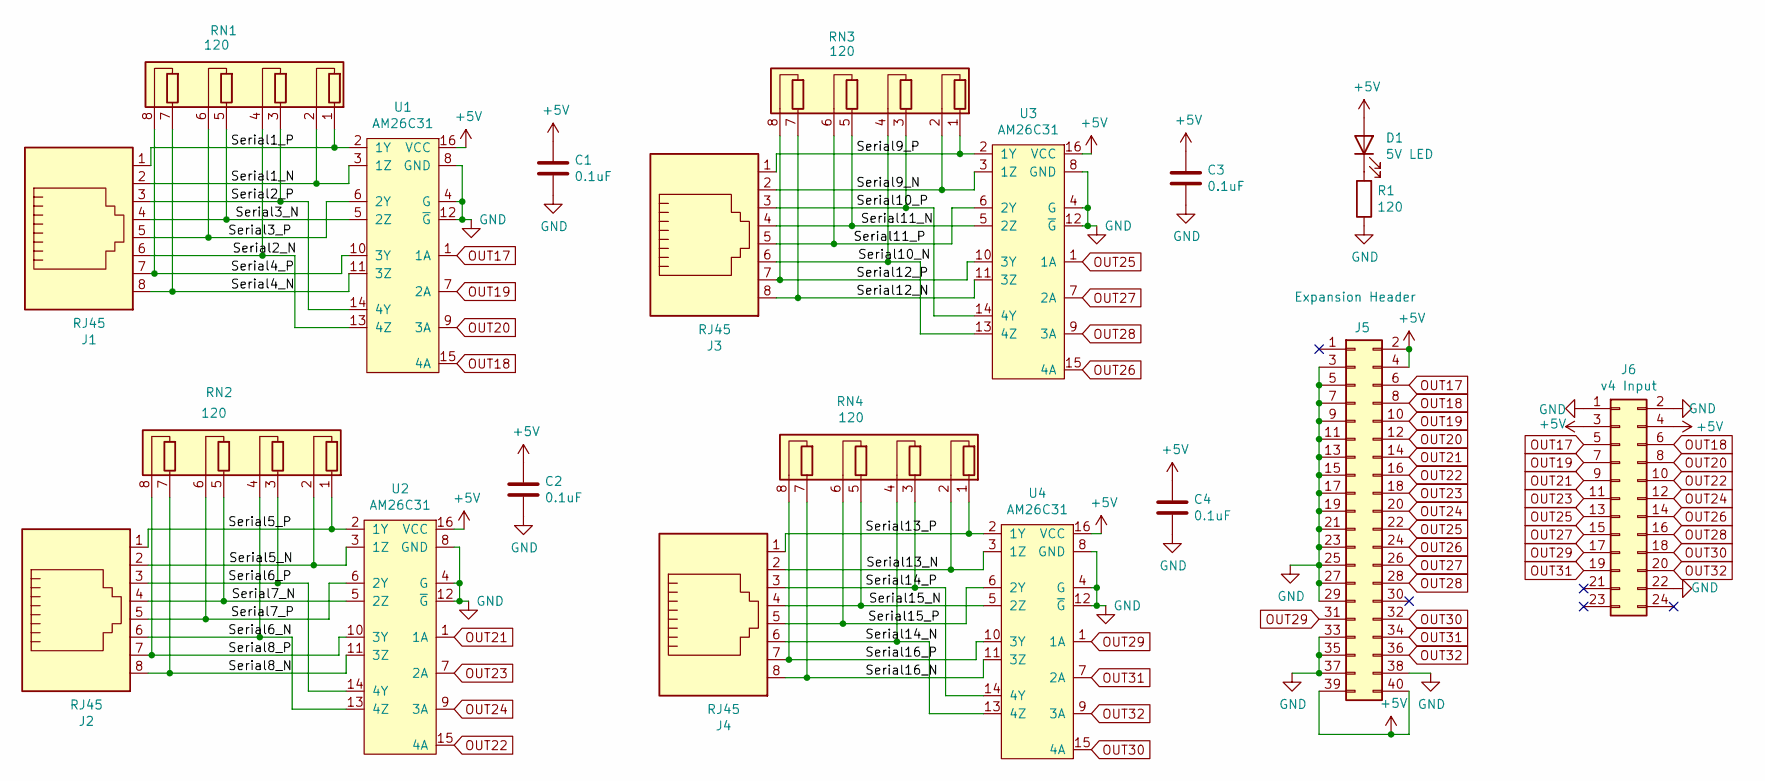
[picture p236: schematic Diff_Expansion.kicad_sch, Diff Expansion]

Parts:
C1, C2, C3, C4: 0.1uF; C_Rect_L7.0mm_W2.0mm_P5.00mm; MPN SR215C104KARTR1; Digi-Key_PN 478-7336-1-ND
D1: 5V LED; LED_D3.0mm_Clear; MPN WP3A8GD; Digi-Key_PN 754-1217-ND
J1, J2, J3, J4: RJ45; RJ45_Amphenol_54602-x08_Horizontal; MPN A-2014-2-4-R; Digi-Key_PN AE10392-ND
J5: Expansion Header; IDC-Header_2x20_P2.54mm_Vertical; MPN SBH11-PBPC-D20-ST-BK; Digi-Key_PN S9175-ND
J6: v4 Input; OST_302-S241; MPN 302-S241; Digi-Key_PN ED10525-ND
R1: 120; R_Axial_DIN0207_L6.3mm_D2.5mm_P7.62mm_Horizontal; MPN CF14JT120R; Digi-Key_PN CF14JT120RCT-ND
RN1, RN2, RN3, RN4: 120; R_Array_SIP8; MPN 4608X-102-121LF; Digi-Key_PN 4608X-2-121LF-ND
U1, U2, U3, U4: AM26C31; DIP-16_W7.62mm; MPN AM26C31IN; Farnell 4975637

Connections:
+5V: C1.1, C2.1, C3.1, C4.1, D1.2 (A), J5.2, J5.4, J5.39, J5.40, J6.3, J6.4, U1.16 (VCC), U2.16 (VCC), U3.16 (VCC), U4.16 (VCC)
/Serial1_N: J1.2, RN1.2 (R1.2), U1.3 (1Z)
/Serial1_P: J1.1, RN1.1 (R1.1), U1.2 (1Y)
/Serial2_N: J1.6, RN1.4 (R2.2), U1.13 (4Z)
/Serial2_P: J1.3, RN1.3 (R2.1), U1.14 (4Y)
/Serial3_N: J1.4, RN1.5 (R3.1), U1.5 (2Z)
/Serial3_P: J1.5, RN1.6 (R3.2), U1.6 (2Y)
/Serial4_N: J1.8, RN1.7 (R4.1), U1.11 (3Z)
/Serial4_P: J1.7, RN1.8 (R4.2), U1.10 (3Y)
/Serial5_N: J2.2, RN2.2 (R1.2), U2.3 (1Z)
/Serial5_P: J2.1, RN2.1 (R1.1), U2.2 (1Y)
/Serial6_N: J2.6, RN2.4 (R2.2), U2.13 (4Z)
/Serial6_P: J2.3, RN2.3 (R2.1), U2.14 (4Y)
/Serial7_N: J2.4, RN2.5 (R3.1), U2.5 (2Z)
/Serial7_P: J2.5, RN2.6 (R3.2), U2.6 (2Y)
/Serial8_N: J2.8, RN2.7 (R4.1), U2.11 (3Z)
/Serial8_P: J2.7, RN2.8 (R4.2), U2.10 (3Y)
/Serial9_N: J3.2, RN3.2 (R1.2), U3.3 (1Z)
/Serial9_P: J3.1, RN3.1 (R1.1), U3.2 (1Y)
/Serial10_N: J3.6, RN3.4 (R2.2), U3.13 (4Z)
/Serial10_P: J3.3, RN3.3 (R2.1), U3.14 (4Y)
/Serial11_N: J3.4, RN3.5 (R3.1), U3.5 (2Z)
/Serial11_P: J3.5, RN3.6 (R3.2), U3.6 (2Y)
/Serial12_N: J3.8, RN3.7 (R4.1), U3.11 (3Z)
/Serial12_P: J3.7, RN3.8 (R4.2), U3.10 (3Y)
/Serial13_N: J4.2, RN4.2 (R1.2), U4.3 (1Z)
/Serial13_P: J4.1, RN4.1 (R1.1), U4.2 (1Y)
/Serial14_N: J4.6, RN4.4 (R2.2), U4.13 (4Z)
/Serial14_P: J4.3, RN4.3 (R2.1), U4.14 (4Y)
/Serial15_N: J4.4, RN4.5 (R3.1), U4.5 (2Z)
/Serial15_P: J4.5, RN4.6 (R3.2), U4.6 (2Y)
/Serial16_N: J4.8, RN4.7 (R4.1), U4.11 (3Z)
/Serial16_P: J4.7, RN4.8 (R4.2), U4.10 (3Y)
GND: C1.2, C2.2, C3.2, C4.2, J5.3, J5.5, J5.7, J5.9, J5.11, J5.13, J5.15, J5.17, J5.19, J5.21, J5.23, J5.25, J5.27, J5.29, J5.33, J5.35, J5.37, J5.38, J6.1, J6.2, J6.22, R1.1, U1.4 (G), U1.8 (GND), U1.12 (~G), U2.4 (G), U2.8 (GND), U2.12 (~G), U3.4 (G), U3.8 (GND), U3.12 (~G), U4.4 (G), U4.8 (GND), U4.12 (~G)
unnamed: D1.1 (K), R1.2
OUT17: J5.6, J6.5, U1.1 (1A)
OUT18: J5.8, J6.6, U1.15 (4A)
OUT19: J5.10, J6.7, U1.7 (2A)
OUT20: J5.12, J6.8, U1.9 (3A)
OUT21: J5.14, J6.9, U2.1 (1A)
OUT22: J5.16, J6.10, U2.15 (4A)
OUT23: J5.18, J6.11, U2.7 (2A)
OUT24: J5.20, J6.12, U2.9 (3A)
OUT25: J5.22, J6.13, U3.1 (1A)
OUT26: J5.24, J6.14, U3.15 (4A)
OUT27: J5.26, J6.15, U3.7 (2A)
OUT28: J5.28, J6.16, U3.9 (3A)
OUT29: J5.31, J6.17, U4.1 (1A)
OUT30: J5.32, J6.18, U4.15 (4A)
OUT31: J5.34, J6.19, U4.7 (2A)
OUT32: J5.36, J6.20, U4.9 (3A)

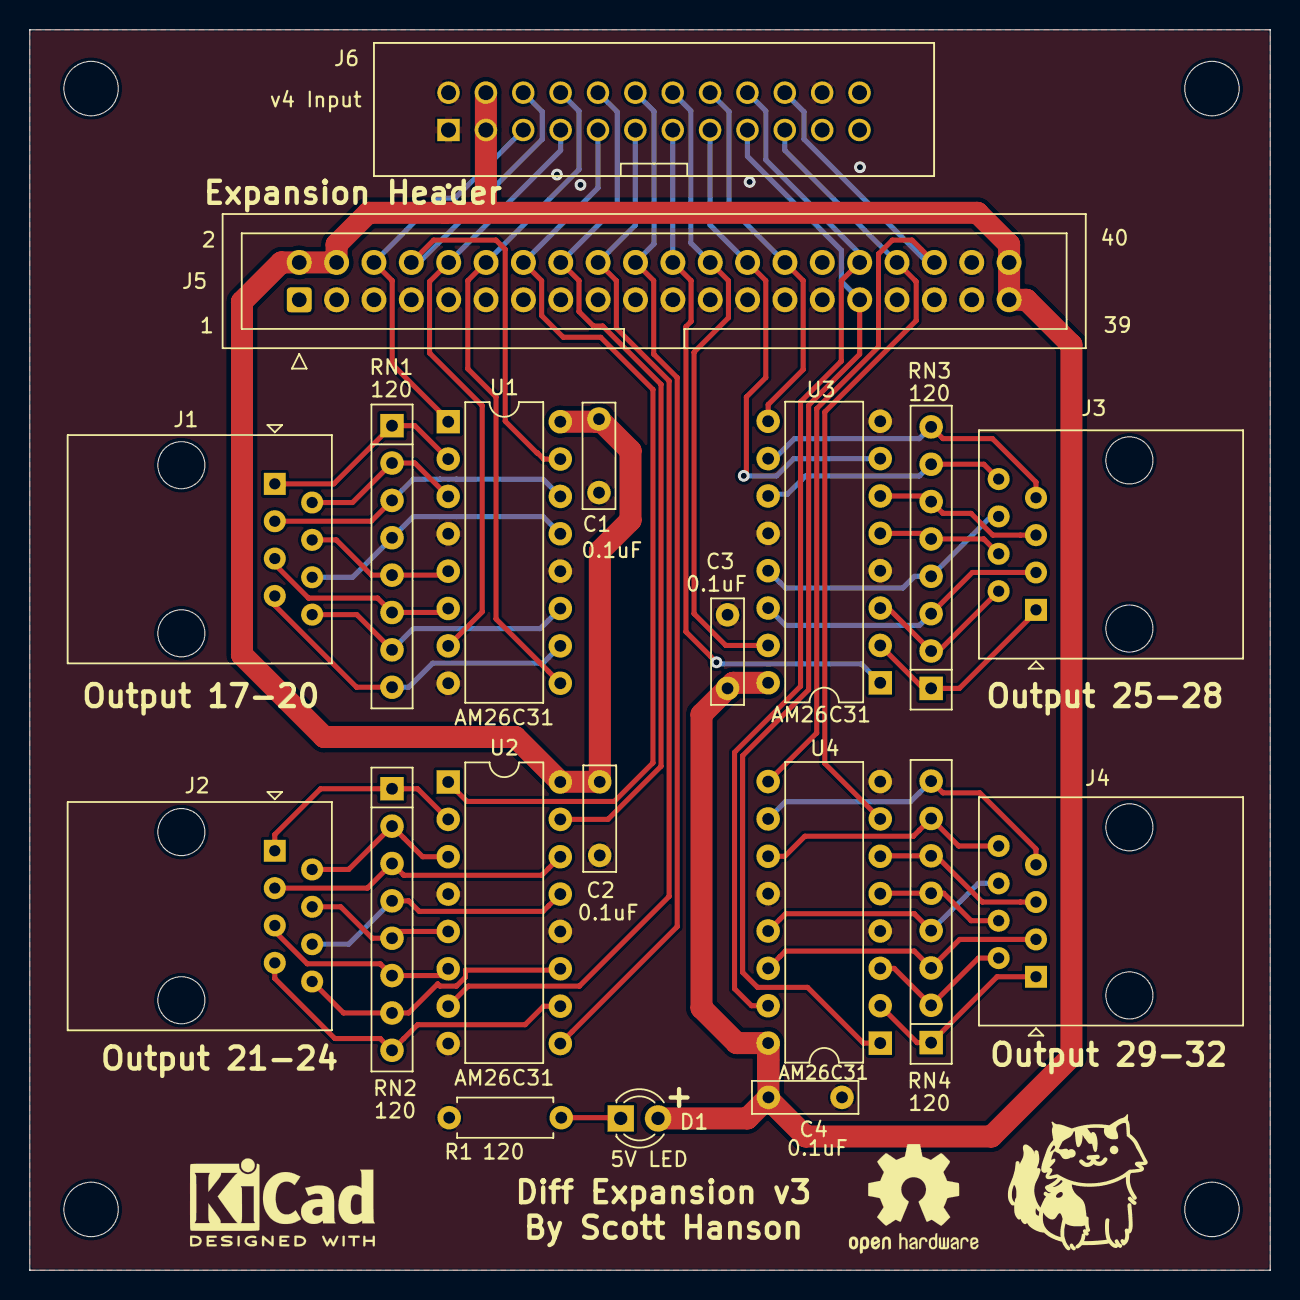
[picture p237: board Diff_Expansion.kicad_pcb from above]

Board: 2 copper layers, 84.3 x 84.3 mm, 20 parts (0 on the bottom side), 51 nets.
