computergeek1507/PB_16/PB_16_Expansion/PB_16.kicad_pcb

## KiCad design PB_16_Expansion/PB_16.kicad_pcb (2026-03-06)

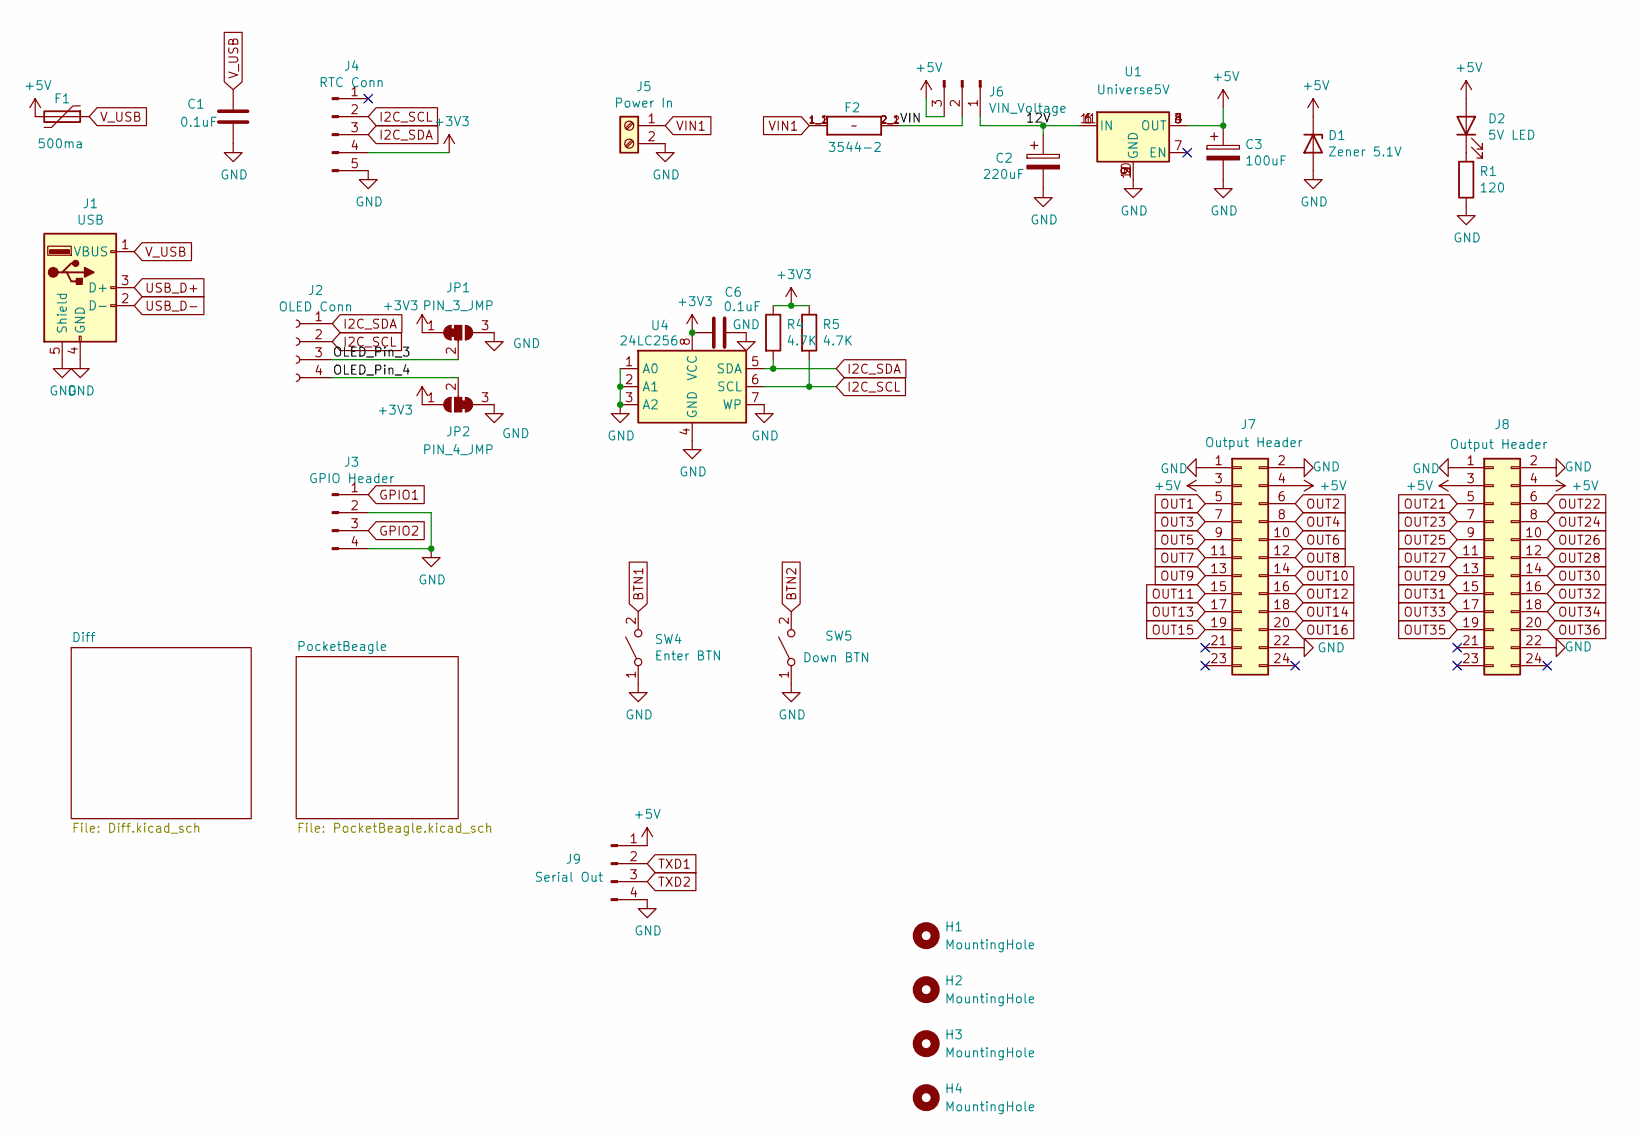
[picture p238: schematic PB_16.kicad_sch, PB 16 Expansion]

Parts:
C1, C6: 0.1uF; C_Rect_L7.0mm_W2.0mm_P5.00mm; MPN SR215C104KARTR1; Digi-Key_PN 478-7336-1-ND
C2: 220uF; CP_Radial_D10.0mm_P5.00mm; MPN ECA-1HM221; Digi-Key_PN P5183-ND
C3: 100uF; CP_Radial_D5.0mm_P2.00mm; MPN 16ZLH100MEFC5X11; Digi-Key_PN 1189-1148-ND
D1: Zener 5.1V; D_5W_P10.16mm_Horizontal; MPN 1N5338BRLG; Digi-Key_PN 1N5338BRLGOSCT-ND
D2: 5V LED; LED_D3.0mm; MPN WP3A8GD; Digi-Key_PN 754-1217-ND
F1: 500ma; Fuse_BelFuse_0ZRE0005FF_L8.3mm_W3.8mm; MPN RXEF050-2; Digi-Key_PN RXEF050-2HFCT-ND
F2: 3544-2; FUSE_3544-2; MPN 3544-2; Digi-Key_PN 36-3544-2-ND
H1, H2, H3, H4: MountingHole; MountingHole_3.7mm
J1: USB; USB_A_Molex_105057_Vertical; MPN 1050570001; Digi-Key_PN WM8672-ND
J2: OLED Conn; PinSocket_1x04_P2.54mm_Vertical; MPN PPTC041LFBN-RC; Digi-Key_PN S7002-ND
J3: GPIO Header; JST_XH_B4B-XH-A_1x04_P2.50mm_Vertical; MPN B4B-XH-A(LF)(SN); Digi-Key_PN 455-2249-ND
J4: RTC Conn; PinHeader_1x05_P2.54mm_Vertical; MPN 61300511121; Digi-Key_PN 732-5318-ND
J5: Power In; PHOENIX_MKDS1_2-3.81; MPN 1727010; Digi-Key_PN 277-1947-ND
J6: VIN_Voltage; PinHeader_1x03_P2.54mm_Vertical; MPN 61300311121; Digi-Key_PN 732-5316-ND
J7, J8: Output Header; IDC-Header_2x12_P2.54mm_Vertical; MPN 61202421621; Digi-Key_PN 732-5398-ND
J9: Serial Out; PinHeader_1x04_P2.54mm_Vertical; MPN 61300411121; Digi-Key_PN 732-5317-ND
JP1: PIN_3_JMP; SolderJumper-3_P1mm_Bridged12
JP2: PIN_4_JMP; SolderJumper-3_P1mm_Bridged23
R1: 120; R_Axial_DIN0207_L6.3mm_D2.5mm_P7.62mm_Horizontal; MPN CF14JT120R; Digi-Key_PN CF14JT120RCT-ND
R4, R5: 4.7K; R_Axial_DIN0207_L6.3mm_D2.5mm_P7.62mm_Horizontal; MPN CF14JT4K70; Digi-Key_PN CF14JT4K70CT-ND
SW4: Enter BTN; SW_PUSH_6mm; MPN 1825910-6; Digi-Key_PN 450-1650-ND
SW5: Down BTN; SW_PUSH_6mm; MPN 1825910-6; Digi-Key_PN 450-1650-ND
U1: Universe5V; Universal_5V_Horizontal; MPN OKI-78SR-5/1.5-W36H-C; Digi-Key_PN 811-2692-ND
U4: 24LC256; DIP-8_W7.62mm; MPN FT24C256A-UDR-B; Digi-Key_PN 1219-1052-ND

Connections:
+3V3: C6.2, J4.4, JP1.1 (A), JP2.1 (A), R4.1, R5.1, U4.8 (VCC); also elsewhere on the board
+5V: C3.1, D1.1 (K), D2.2 (A), F1.2, J6.3, J7.3, J7.4, J8.3, J8.4, J9.1, U1.3 (OUT), U1.4 (OUT), U1.8 (OUT); also elsewhere on the board
/12V: C2.1, J6.1, U1.1 (IN), U1.6 (IN), U1.11 (IN)
/OLED_Pin_3: J2.3, JP1.2 (C)
/OLED_Pin_4: J2.4, JP2.2 (C)
/VIN: F2.2_1 (2), F2.2_2 (2), J6.2
BTN1: SW4.2 (B); also elsewhere on the board
BTN2: SW5.2 (B); also elsewhere on the board
GND: C1.2, C2.2, C3.2, C6.1, D1.2 (A), J1.4 (GND), J1.5 (Shield), J3.2, J3.4, J4.5, J5.2, J7.1, J7.2, J7.22, J8.1, J8.2, J8.22, J9.4, JP1.3 (B), JP2.3 (B), R1.1, SW4.1 (A), SW5.1 (A), U1.2 (GND), U1.5 (GND), U1.9 (GND), U1.10 (GND), U4.1 (A0), U4.2 (A1), U4.3 (A2), U4.4 (GND), U4.7 (WP); also elsewhere on the board
GPIO1: J3.1; also elsewhere on the board
GPIO2: J3.3; also elsewhere on the board
I2C_SCL: J2.2, J4.2, R5.2, U4.6 (SCL); also elsewhere on the board
I2C_SDA: J2.1, J4.3, R4.2, U4.5 (SDA); also elsewhere on the board
unnamed: D2.1 (K), R1.2
OUT1: J7.5; also elsewhere on the board
OUT2: J7.6; also elsewhere on the board
OUT3: J7.7; also elsewhere on the board
OUT4: J7.8; also elsewhere on the board
OUT5: J7.9; also elsewhere on the board
OUT6: J7.10; also elsewhere on the board
OUT7: J7.11; also elsewhere on the board
OUT8: J7.12; also elsewhere on the board
OUT9: J7.13; also elsewhere on the board
OUT10: J7.14; also elsewhere on the board
OUT11: J7.15; also elsewhere on the board
OUT12: J7.16; also elsewhere on the board
OUT13: J7.17; also elsewhere on the board
OUT14: J7.18; also elsewhere on the board
OUT15: J7.19; also elsewhere on the board
OUT16: J7.20; also elsewhere on the board
OUT21: J8.5; also elsewhere on the board
OUT22: J8.6; also elsewhere on the board
OUT23: J8.7; also elsewhere on the board
OUT24: J8.8; also elsewhere on the board
OUT25: J8.9; also elsewhere on the board
OUT26: J8.10; also elsewhere on the board
OUT27: J8.11; also elsewhere on the board
OUT28: J8.12; also elsewhere on the board
OUT29: J8.13; also elsewhere on the board
OUT30: J8.14; also elsewhere on the board
OUT31: J8.15; also elsewhere on the board
OUT32: J8.16; also elsewhere on the board
OUT33: J8.17; also elsewhere on the board
OUT34: J8.18; also elsewhere on the board
OUT35: J8.19; also elsewhere on the board
OUT36: J8.20; also elsewhere on the board
TXD1: J9.2; also elsewhere on the board
TXD2: J9.3; also elsewhere on the board
USB_D+: J1.3 (D+); also elsewhere on the board
USB_D-: J1.2 (D-); also elsewhere on the board
VIN1: F2.1_1 (1), F2.1_2 (1), J5.1
V_USB: C1.1, F1.1, J1.1 (VBUS); also elsewhere on the board

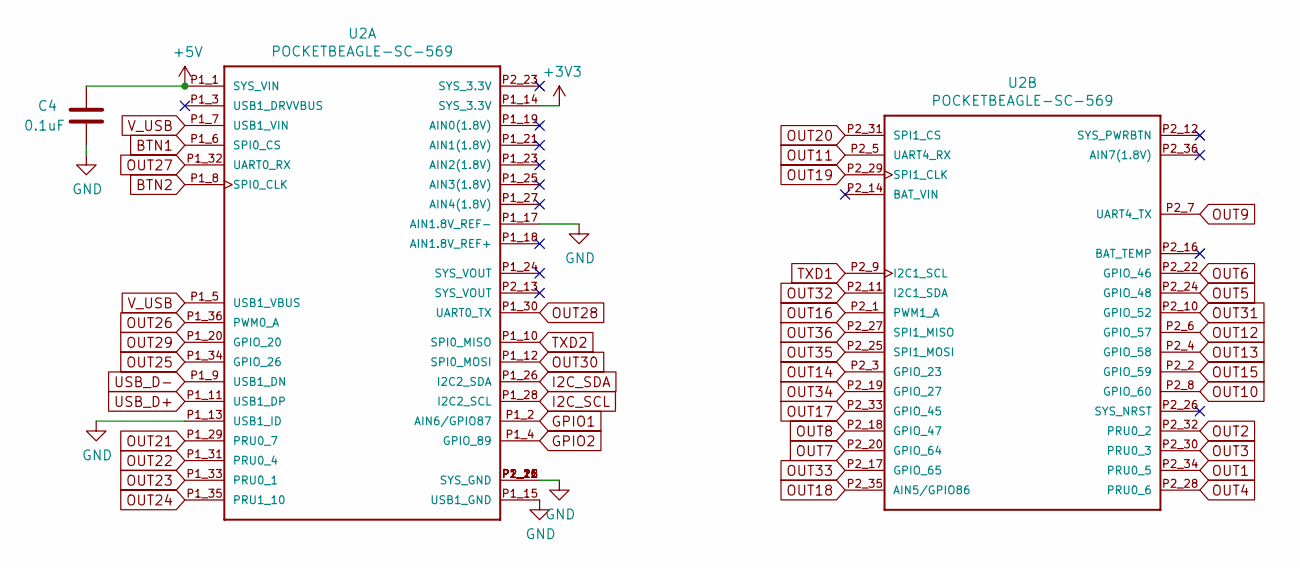
[picture p239: schematic PocketBeagle.kicad_sch, PB 16 Expansion]

Parts:
C4: 0.1uF; C_Rect_L7.0mm_W2.0mm_P5.00mm; MPN SR215C104KARTR1; Digi-Key_PN 478-7336-1-ND
U2: POCKETBEAGLE-SC-569; BEAGLE_POCKETBEAGLE-SC-569; MPN POCKETBEAGLE-SC-569; Digi-Key_PN POCKETBEAGLE-SC-569-ND

Connections:
+3V3: U2.P1_14 (SYS_3.3V); also elsewhere on the board
+5V: C4.1, U2.P1_1 (SYS_VIN); also elsewhere on the board
BTN1: U2.P1_6 (SPI0_CS); also elsewhere on the board
BTN2: U2.P1_8 (SPI0_CLK); also elsewhere on the board
GND: C4.2, U2.P1_13 (USB1_ID), U2.P1_15 (USB1_GND), U2.P1_16 (SYS_GND), U2.P1_17 (AIN1.8V_REF-), U2.P1_22 (SYS_GND), U2.P2_15 (SYS_GND), U2.P2_21 (SYS_GND); also elsewhere on the board
GPIO1: U2.P1_2 (AIN6/GPIO87); also elsewhere on the board
GPIO2: U2.P1_4 (GPIO_89); also elsewhere on the board
I2C_SCL: U2.P1_28 (I2C2_SCL); also elsewhere on the board
I2C_SDA: U2.P1_26 (I2C2_SDA); also elsewhere on the board
OUT1: U2.P2_34 (PRU0_5); also elsewhere on the board
OUT2: U2.P2_32 (PRU0_2); also elsewhere on the board
OUT3: U2.P2_30 (PRU0_3); also elsewhere on the board
OUT4: U2.P2_28 (PRU0_6); also elsewhere on the board
OUT5: U2.P2_24 (GPIO_48); also elsewhere on the board
OUT6: U2.P2_22 (GPIO_46); also elsewhere on the board
OUT7: U2.P2_20 (GPIO_64); also elsewhere on the board
OUT8: U2.P2_18 (GPIO_47); also elsewhere on the board
OUT9: U2.P2_7 (UART4_TX); also elsewhere on the board
OUT10: U2.P2_8 (GPIO_60); also elsewhere on the board
OUT11: U2.P2_5 (UART4_RX); also elsewhere on the board
OUT12: U2.P2_6 (GPIO_57); also elsewhere on the board
OUT13: U2.P2_4 (GPIO_58); also elsewhere on the board
OUT14: U2.P2_3 (GPIO_23); also elsewhere on the board
OUT15: U2.P2_2 (GPIO_59); also elsewhere on the board
OUT16: U2.P2_1 (PWM1_A); also elsewhere on the board
OUT17: U2.P2_33 (GPIO_45); also elsewhere on the board
OUT18: U2.P2_35 (AIN5/GPIO86); also elsewhere on the board
OUT19: U2.P2_29 (SPI1_CLK); also elsewhere on the board
OUT20: U2.P2_31 (SPI1_CS); also elsewhere on the board
OUT21: U2.P1_29 (PRU0_7); also elsewhere on the board
OUT22: U2.P1_31 (PRU0_4); also elsewhere on the board
OUT23: U2.P1_33 (PRU0_1); also elsewhere on the board
OUT24: U2.P1_35 (PRU1_10); also elsewhere on the board
OUT25: U2.P1_34 (GPIO_26); also elsewhere on the board
OUT26: U2.P1_36 (PWM0_A); also elsewhere on the board
OUT27: U2.P1_32 (UART0_RX); also elsewhere on the board
OUT28: U2.P1_30 (UART0_TX); also elsewhere on the board
OUT29: U2.P1_20 (GPIO_20); also elsewhere on the board
OUT30: U2.P1_12 (SPI0_MOSI); also elsewhere on the board
OUT31: U2.P2_10 (GPIO_52); also elsewhere on the board
OUT32: U2.P2_11 (I2C1_SDA); also elsewhere on the board
OUT33: U2.P2_17 (GPIO_65); also elsewhere on the board
OUT34: U2.P2_19 (GPIO_27); also elsewhere on the board
OUT35: U2.P2_25 (SPI1_MOSI); also elsewhere on the board
OUT36: U2.P2_27 (SPI1_MISO); also elsewhere on the board
TXD1: U2.P2_9 (I2C1_SCL); also elsewhere on the board
TXD2: U2.P1_10 (SPI0_MISO); also elsewhere on the board
USB_D+: U2.P1_11 (USB1_DP); also elsewhere on the board
USB_D-: U2.P1_9 (USB1_DN); also elsewhere on the board
V_USB: U2.P1_5 (USB1_VBUS), U2.P1_7 (USB1_VIN); also elsewhere on the board

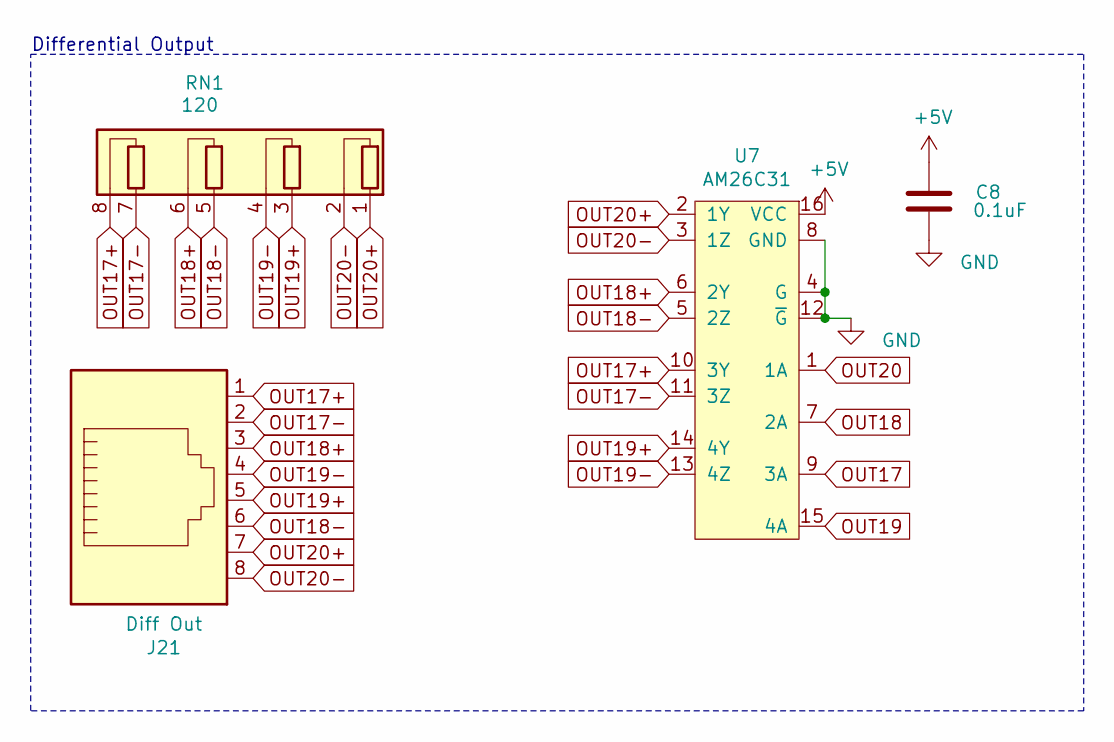
[picture p240: schematic Diff.kicad_sch, PB 16 Expansion]

Parts:
C8: 0.1uF; C_Rect_L7.0mm_W2.0mm_P5.00mm; MPN SR215C104KARTR1; Digi-Key_PN 478-7336-1-ND
J21: Diff Out; RJ45_Amphenol_54602-x08_Horizontal; MPN X05ADIWA1DY1022; Digi-Key_PN AE10392-ND
RN1: 120; R_Array_SIP8; MPN 4608X-102-121LF; Digikey PN 4608X-2-121LF-ND
U7: AM26C31; DIP-16_W7.62mm; MPN AM26C31IN; Farnell 4975637

Connections:
+5V: C8.1, U7.16 (VCC); also elsewhere on the board
GND: C8.2, U7.4 (G), U7.8 (GND), U7.12 (~G); also elsewhere on the board
OUT17: U7.9 (3A); also elsewhere on the board
OUT17+: J21.1, RN1.8 (R4.2), U7.10 (3Y)
OUT17-: J21.2, RN1.7 (R4.1), U7.11 (3Z)
OUT18: U7.7 (2A); also elsewhere on the board
OUT18+: J21.3, RN1.6 (R3.2), U7.6 (2Y)
OUT18-: J21.6, RN1.5 (R3.1), U7.5 (2Z)
OUT19: U7.15 (4A); also elsewhere on the board
OUT19+: J21.5, RN1.3 (R2.1), U7.14 (4Y)
OUT19-: J21.4, RN1.4 (R2.2), U7.13 (4Z)
OUT20: U7.1 (1A); also elsewhere on the board
OUT20+: J21.7, RN1.1 (R1.1), U7.2 (1Y)
OUT20-: J21.8, RN1.2 (R1.2), U7.3 (1Z)

Notes on the sheet:
Differential Output

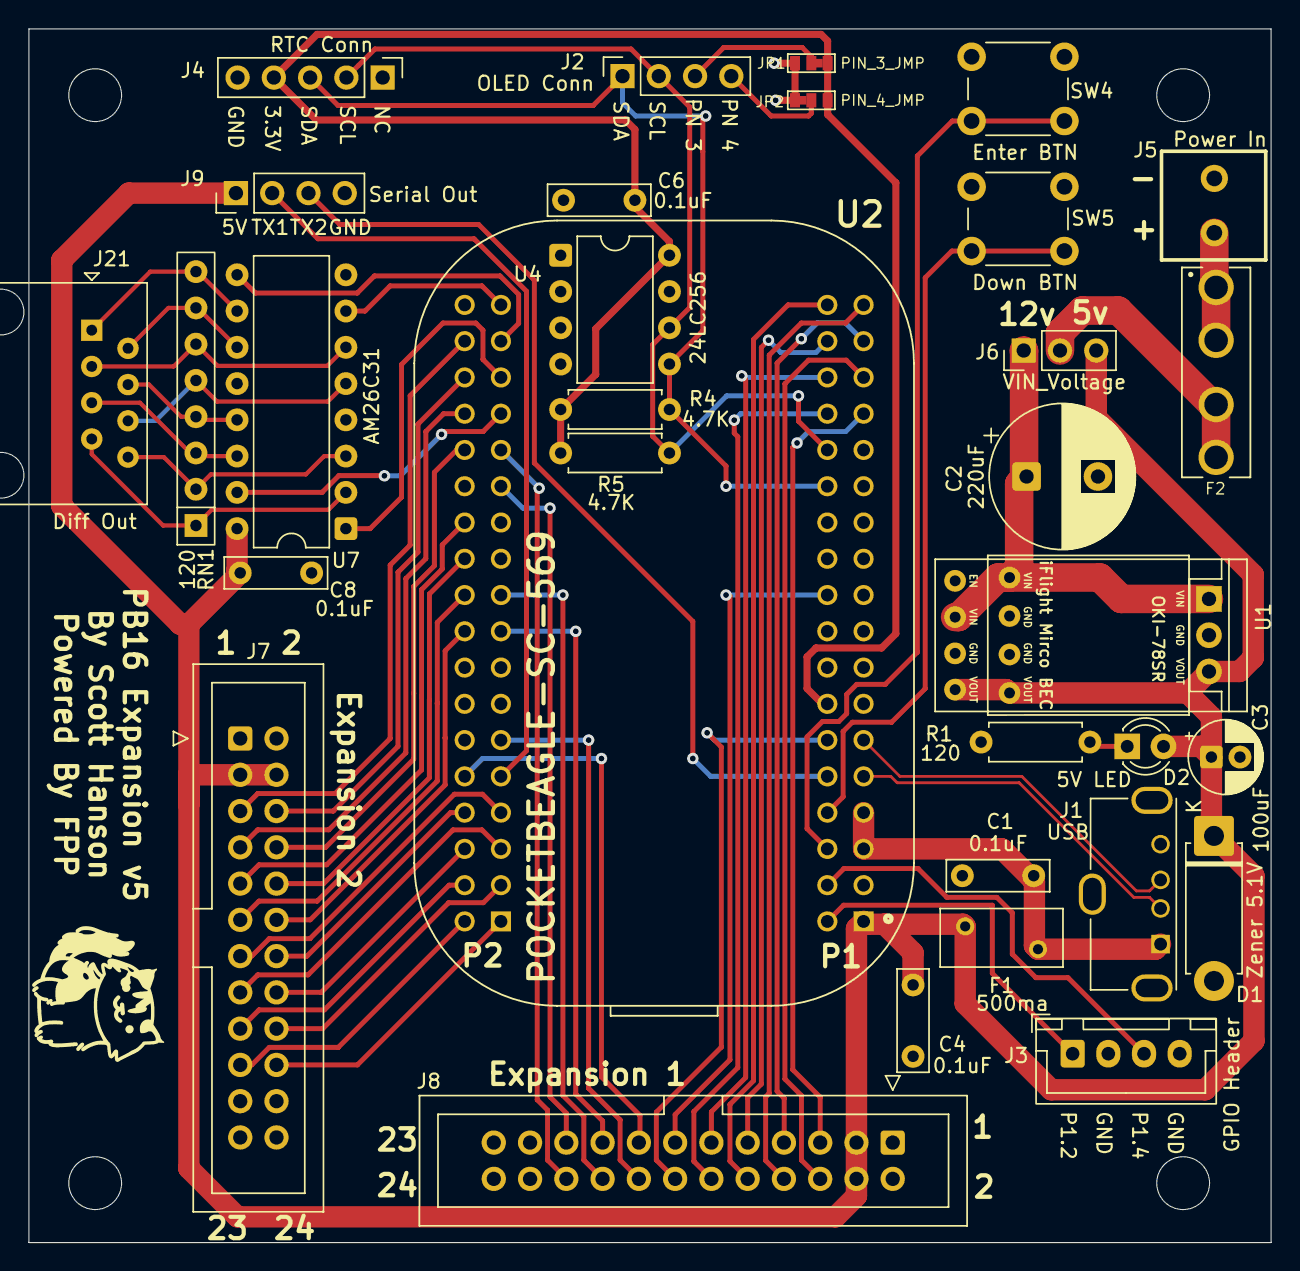
[picture p241: board PB_16_Expansion/PB_16.kicad_pcb from above]

Board: 2 copper layers, 87.0 x 85.0 mm, 36 parts (0 on the bottom side), 64 nets.
