computergeek1507/PB_16/PB_16v2_SMD/PB_16.kicad_pcb

## KiCad design PB_16v2_SMD/PB_16.kicad_pcb (2026-03-06)

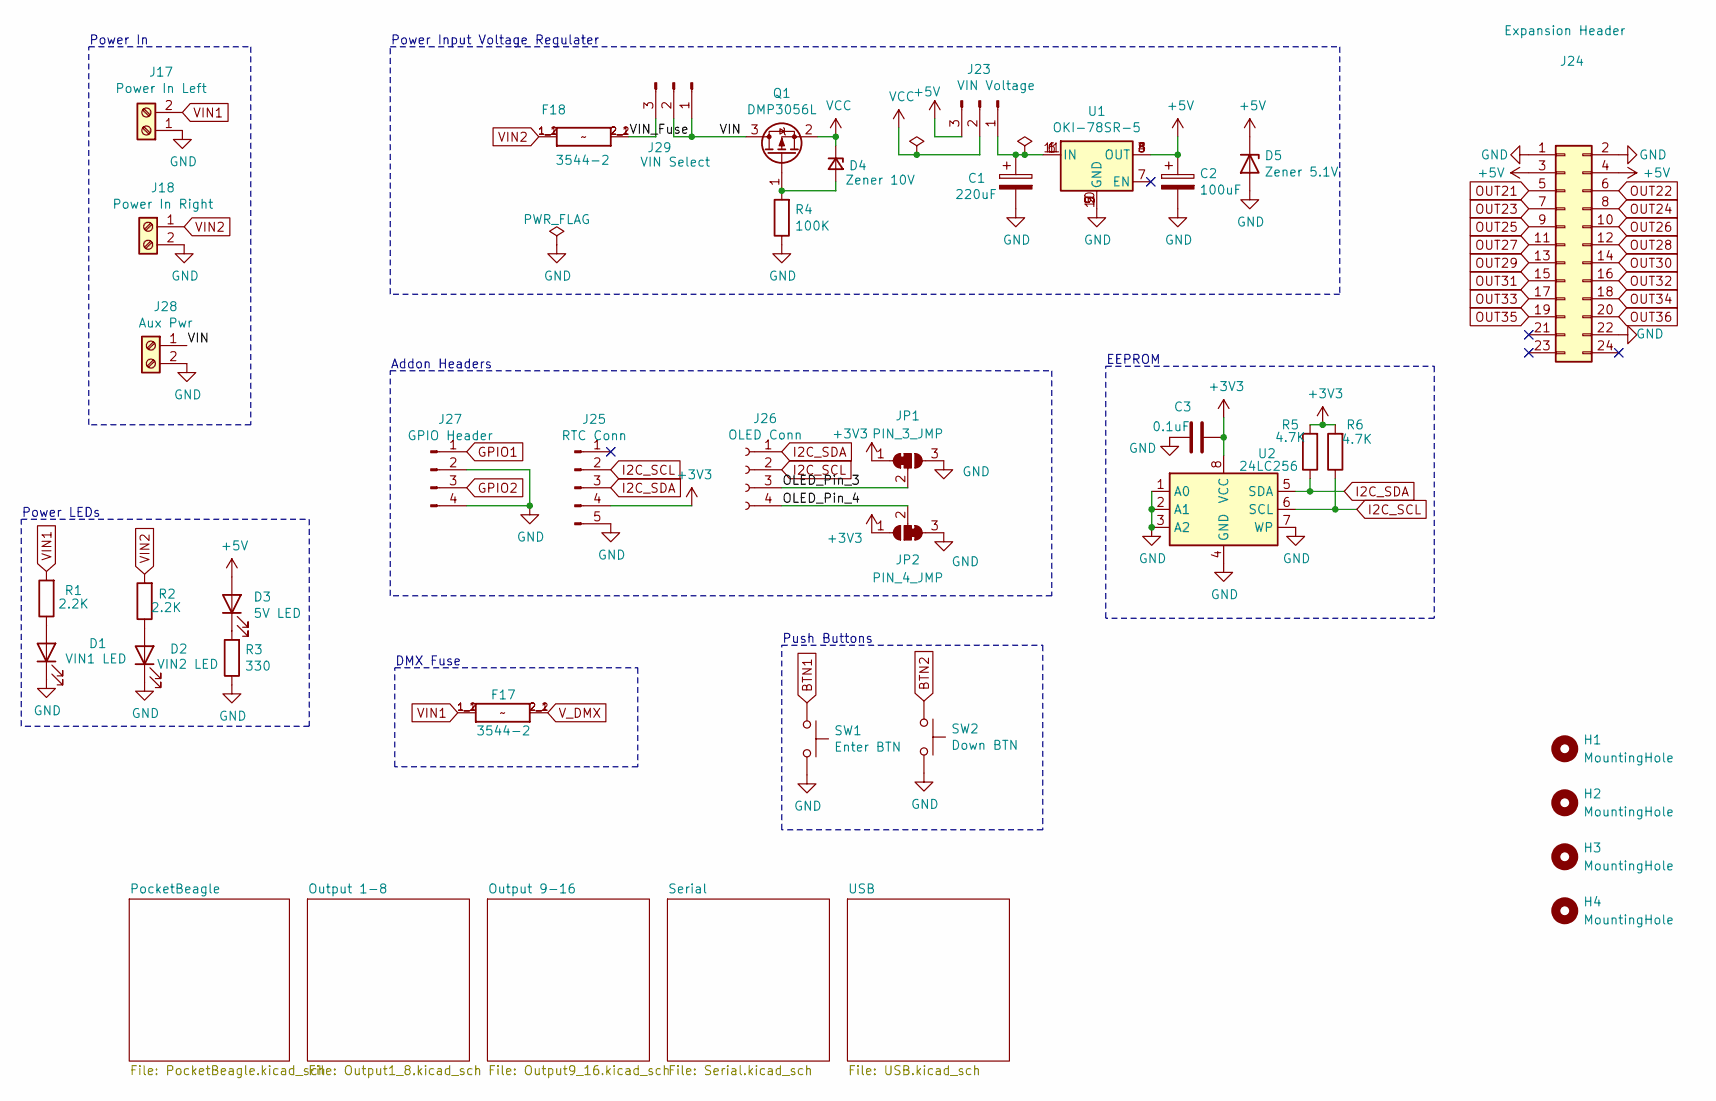
[picture p242: schematic PB_16.kicad_sch, PB 16]

Parts:
C1: 220uF; CP_Radial_D10.0mm_P5.00mm; MPN ECA-1HM221; Digi-Key_PN P5183-ND
C2: 100uF; CP_Elec_6.3x5.4_Nichicon; MPN UWX1C101MCL1GB; Digi-Key_PN 493-2105-1-ND
C3: 0.1uF; C_0603_1608Metric; MPN CL10B104KB8NNWC; Digi-Key_PN 1276-1935-2-ND
D1: VIN1 LED; LED_0603_1608Metric; MPN LTST-C190KRKT; Digi-Key_PN 160-1436-2-ND
D2: VIN2 LED; LED_0603_1608Metric; MPN LTST-C190KRKT; Digi-Key_PN 160-1436-2-ND
D3: 5V LED; LED_0603_1608Metric; MPN LTST-C190KRKT; Digi-Key_PN 160-1436-2-ND
D4: Zener 10V; D_SOD-123; MPN MMSZ5240B-7-F; Digi-Key_PN MMSZ5240B-FDICT-ND
D5: Zener 5.1V; D_SOD-123; MPN MMSZ5231B-7-F; Digi-Key_PN MMSZ5231B-FDICT-ND
F17, F18: 3544-2; FUSE_3544-2; MPN 3544-2; Digi-Key_PN 36-3544-2-ND
H1, H2, H3, H4: MountingHole; MountingHole_3.7mm
J17: Power In Left; BARRIER_BLOCK_1ROW_2POS_P9.5MM; MPN OSTYK51102030; Digi-Key_PN ED2953-ND
J18: Power In Right; BARRIER_BLOCK_1ROW_2POS_P9.5MM; MPN OSTYK51102030; Digi-Key_PN ED2953-ND
J23: VIN Voltage; PinHeader_1x03_P2.54mm_Vertical; MPN 61300311121; Digi-Key_PN 732-5316-ND
J24: Expansion Header; IDC-Header_2x12_P2.54mm_Vertical; MPN SBH11-PBPC-D20-ST-BK; Digi-Key_PN S9175-ND
J25: RTC Conn; PinHeader_1x05_P2.54mm_Vertical; MPN 61300511121; Digi-Key_PN 732-5318-ND
J26: OLED Conn; PinSocket_1x04_P2.54mm_Vertical; MPN PPTC041LFBN-RC; Digi-Key_PN S7002-ND
J27: GPIO Header; JST_XH_B4B-XH-A_1x04_P2.50mm_Vertical; MPN B4B-XH-A(LF)(SN); Digi-Key_PN 455-2249-ND
J28: Aux Pwr; PHOENIX_MKDS1_2-3.81; MPN 1727010; Digi-Key_PN 277-1947-ND
J29: VIN Select; PinHeader_1x03_P2.54mm_Vertical; MPN 61300311121; Digi-Key_PN 732-5316-ND
JP1: PIN_3_JMP; SolderJumper-3_P1mm_Bridged12
JP2: PIN_4_JMP; SolderJumper-3_P1mm_Bridged23
Q1: DMP3056L; SOT-23; MPN DMP3056L-7; Digi-Key_PN DMP3056L-7DICT-ND
R1, R2: 2.2K; R_0603_1608Metric; MPN RC0603FR-071KL; Digi-Key_PN 311-1.00KHRTR-ND
R3: 330; R_0603_1608Metric; MPN CRGCQ0603F120R; Digi-Key_PN A129677CT-ND
R4: 100K; R_0603_1608Metric; MPN RT0603BRD07100KL; Digi-Key_PN YAG1235CT-ND
R5, R6: 4.7K; R_0603_1608Metric; MPN RC0603JR-074K7L; Digi-Key_PN 311-4.7KGRCT-ND
SW1: Enter BTN; SW_Push_1P1T_NO_6x6mm_H9.5mm; MPN PTS645SL50SMTR92 LFS; Digi-Key_PN CKN9088CT-ND
SW2: Down BTN; SW_Push_1P1T_NO_6x6mm_H9.5mm; MPN PTS645SL50SMTR92 LFS; Digi-Key_PN CKN9088CT-ND
U1: OKI-78SR-5; Universal_5V_Horizontal; MPN OKI-78SR-5/1.5-W36-C; Digi-Key_PN 811-2196-5-ND
U2: 24LC256; SOIC-8_3.9x4.9mm_P1.27mm; MPN 24LC256T-I/SN; Digi-Key_PN 24LC256T-I/SNCT-ND

Connections:
+3V3: C3.1, J25.4, JP1.1 (A), JP2.1 (A), R5.2, R6.2, U2.8 (VCC); also elsewhere on the board
+5V: C2.1, D3.2 (A), D5.1 (K), J23.3, J24.3, J24.4, U1.3 (OUT), U1.4 (OUT), U1.8 (OUT); also elsewhere on the board
/OLED_Pin_3: J26.3, JP1.2 (C)
/OLED_Pin_4: J26.4, JP2.2 (C)
/VIN: J28.1, J29.1, J29.2, Q1.3 (D)
/VIN_Fuse: F18.2_1 (2), F18.2_2 (2), J29.3
BTN1: SW1.1; also elsewhere on the board
BTN2: SW2.1; also elsewhere on the board
GND: C1.2, C2.2, C3.2, D1.1 (K), D2.1 (K), D5.2 (A), J17.1, J18.2, J24.1, J24.2, J24.22, J25.5, J27.2, J27.4, J28.2, JP1.3 (B), JP2.3 (B), R3.1, R4.1, SW1.2, SW2.2, U1.2 (GND), U1.5 (GND), U1.9 (GND), U1.10 (GND), U2.1 (A0), U2.2 (A1), U2.3 (A2), U2.4 (GND), U2.7 (WP); also elsewhere on the board
GPIO1: J27.1; also elsewhere on the board
GPIO2: J27.3; also elsewhere on the board
I2C_SCL: J25.2, J26.2, R6.1, U2.6 (SCL); also elsewhere on the board
I2C_SDA: J25.3, J26.1, R5.1, U2.5 (SDA); also elsewhere on the board
unnamed: D1.2 (A), R1.1
unnamed: D2.2 (A), R2.1
unnamed: D3.1 (K), R3.2
unnamed: D4.2 (A), Q1.1 (G), R4.2
unnamed: C1.1, J23.1, U1.1 (IN), U1.6 (IN), U1.11 (IN)
OUT21: J24.5; also elsewhere on the board
OUT22: J24.6; also elsewhere on the board
OUT23: J24.7; also elsewhere on the board
OUT24: J24.8; also elsewhere on the board
OUT25: J24.9; also elsewhere on the board
OUT26: J24.10; also elsewhere on the board
OUT27: J24.11; also elsewhere on the board
OUT28: J24.12; also elsewhere on the board
OUT29: J24.13; also elsewhere on the board
OUT30: J24.14; also elsewhere on the board
OUT31: J24.15; also elsewhere on the board
OUT32: J24.16; also elsewhere on the board
OUT33: J24.17; also elsewhere on the board
OUT34: J24.18; also elsewhere on the board
OUT35: J24.19; also elsewhere on the board
OUT36: J24.20; also elsewhere on the board
VCC: D4.1 (K), J23.2, Q1.2 (S)
VIN1: F17.1_1 (1), F17.1_2 (1), J17.2, R1.2; also elsewhere on the board
VIN2: F18.1_1 (1), F18.1_2 (1), J18.1, R2.2; also elsewhere on the board
V_DMX: F17.2_1 (2), F17.2_2 (2); also elsewhere on the board

Notes on the sheet:
Power Input Voltage Regulater
Push Buttons
Power LEDs
EEPROM
Power In
Addon Headers
DMX Fuse

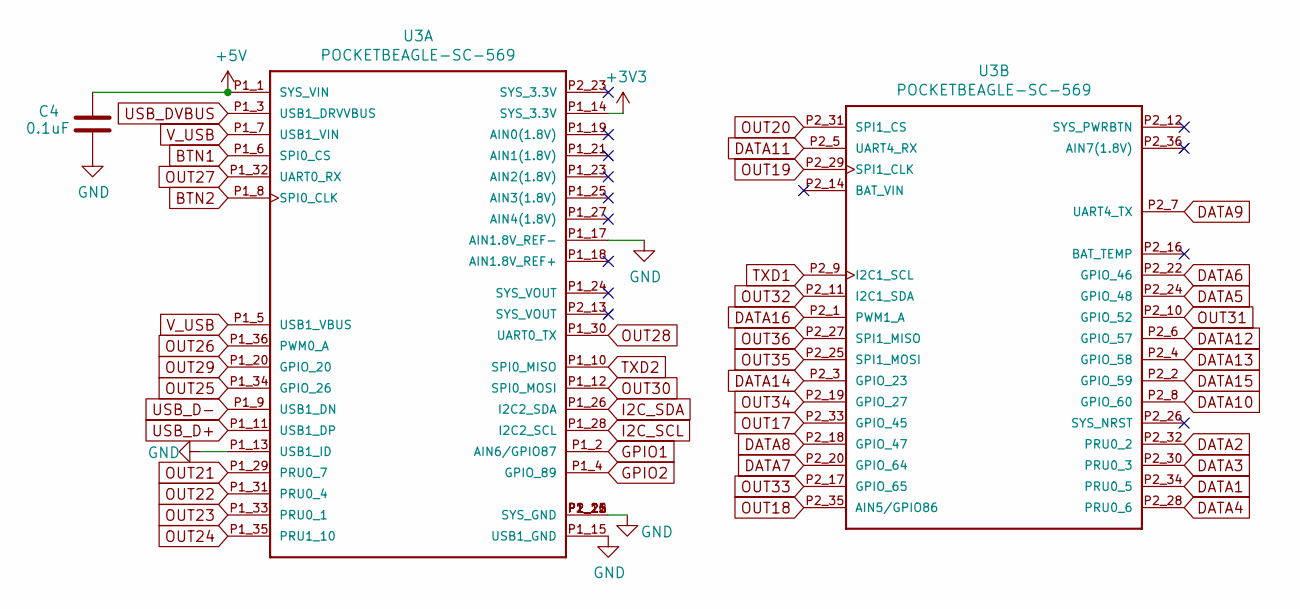
[picture p243: schematic PocketBeagle.kicad_sch, PB 16]

Parts:
C4: 0.1uF; C_0603_1608Metric; MPN CL10B104KB8NNWC; Digi-Key_PN 1276-1935-2-ND
U3: POCKETBEAGLE-SC-569; BEAGLE_POCKETBEAGLE-SC-569; MPN POCKETBEAGLE-SC-569; Digi-Key_PN POCKETBEAGLE-SC-569-ND

Connections:
+3V3: U3.P1_14 (SYS_3.3V); also elsewhere on the board
+5V: C4.1, U3.P1_1 (SYS_VIN); also elsewhere on the board
BTN1: U3.P1_6 (SPI0_CS); also elsewhere on the board
BTN2: U3.P1_8 (SPI0_CLK); also elsewhere on the board
DATA1: U3.P2_34 (PRU0_5); also elsewhere on the board
DATA2: U3.P2_32 (PRU0_2); also elsewhere on the board
DATA3: U3.P2_30 (PRU0_3); also elsewhere on the board
DATA4: U3.P2_28 (PRU0_6); also elsewhere on the board
DATA5: U3.P2_24 (GPIO_48); also elsewhere on the board
DATA6: U3.P2_22 (GPIO_46); also elsewhere on the board
DATA7: U3.P2_20 (GPIO_64); also elsewhere on the board
DATA8: U3.P2_18 (GPIO_47); also elsewhere on the board
DATA9: U3.P2_7 (UART4_TX); also elsewhere on the board
DATA10: U3.P2_8 (GPIO_60); also elsewhere on the board
DATA11: U3.P2_5 (UART4_RX); also elsewhere on the board
DATA12: U3.P2_6 (GPIO_57); also elsewhere on the board
DATA13: U3.P2_4 (GPIO_58); also elsewhere on the board
DATA14: U3.P2_3 (GPIO_23); also elsewhere on the board
DATA15: U3.P2_2 (GPIO_59); also elsewhere on the board
DATA16: U3.P2_1 (PWM1_A); also elsewhere on the board
GND: C4.2, U3.P1_13 (USB1_ID), U3.P1_15 (USB1_GND), U3.P1_16 (SYS_GND), U3.P1_17 (AIN1.8V_REF-), U3.P1_22 (SYS_GND), U3.P2_15 (SYS_GND), U3.P2_21 (SYS_GND); also elsewhere on the board
GPIO1: U3.P1_2 (AIN6/GPIO87); also elsewhere on the board
GPIO2: U3.P1_4 (GPIO_89); also elsewhere on the board
I2C_SCL: U3.P1_28 (I2C2_SCL); also elsewhere on the board
I2C_SDA: U3.P1_26 (I2C2_SDA); also elsewhere on the board
OUT17: U3.P2_33 (GPIO_45); also elsewhere on the board
OUT18: U3.P2_35 (AIN5/GPIO86); also elsewhere on the board
OUT19: U3.P2_29 (SPI1_CLK); also elsewhere on the board
OUT20: U3.P2_31 (SPI1_CS); also elsewhere on the board
OUT21: U3.P1_29 (PRU0_7); also elsewhere on the board
OUT22: U3.P1_31 (PRU0_4); also elsewhere on the board
OUT23: U3.P1_33 (PRU0_1); also elsewhere on the board
OUT24: U3.P1_35 (PRU1_10); also elsewhere on the board
OUT25: U3.P1_34 (GPIO_26); also elsewhere on the board
OUT26: U3.P1_36 (PWM0_A); also elsewhere on the board
OUT27: U3.P1_32 (UART0_RX); also elsewhere on the board
OUT28: U3.P1_30 (UART0_TX); also elsewhere on the board
OUT29: U3.P1_20 (GPIO_20); also elsewhere on the board
OUT30: U3.P1_12 (SPI0_MOSI); also elsewhere on the board
OUT31: U3.P2_10 (GPIO_52); also elsewhere on the board
OUT32: U3.P2_11 (I2C1_SDA); also elsewhere on the board
OUT33: U3.P2_17 (GPIO_65); also elsewhere on the board
OUT34: U3.P2_19 (GPIO_27); also elsewhere on the board
OUT35: U3.P2_25 (SPI1_MOSI); also elsewhere on the board
OUT36: U3.P2_27 (SPI1_MISO); also elsewhere on the board
TXD1: U3.P2_9 (I2C1_SCL); also elsewhere on the board
TXD2: U3.P1_10 (SPI0_MISO); also elsewhere on the board
USB_D+: U3.P1_11 (USB1_DP); also elsewhere on the board
USB_D-: U3.P1_9 (USB1_DN); also elsewhere on the board
USB_DVBUS: U3.P1_3 (USB1_DRVVBUS); also elsewhere on the board
V_USB: U3.P1_5 (USB1_VBUS), U3.P1_7 (USB1_VIN); also elsewhere on the board
