computergeek1507/PB_16/PB_16v2_SMD/PB_16.kicad_pcb

## KiCad design PB_16v2_SMD/PB_16.kicad_pcb (continued)

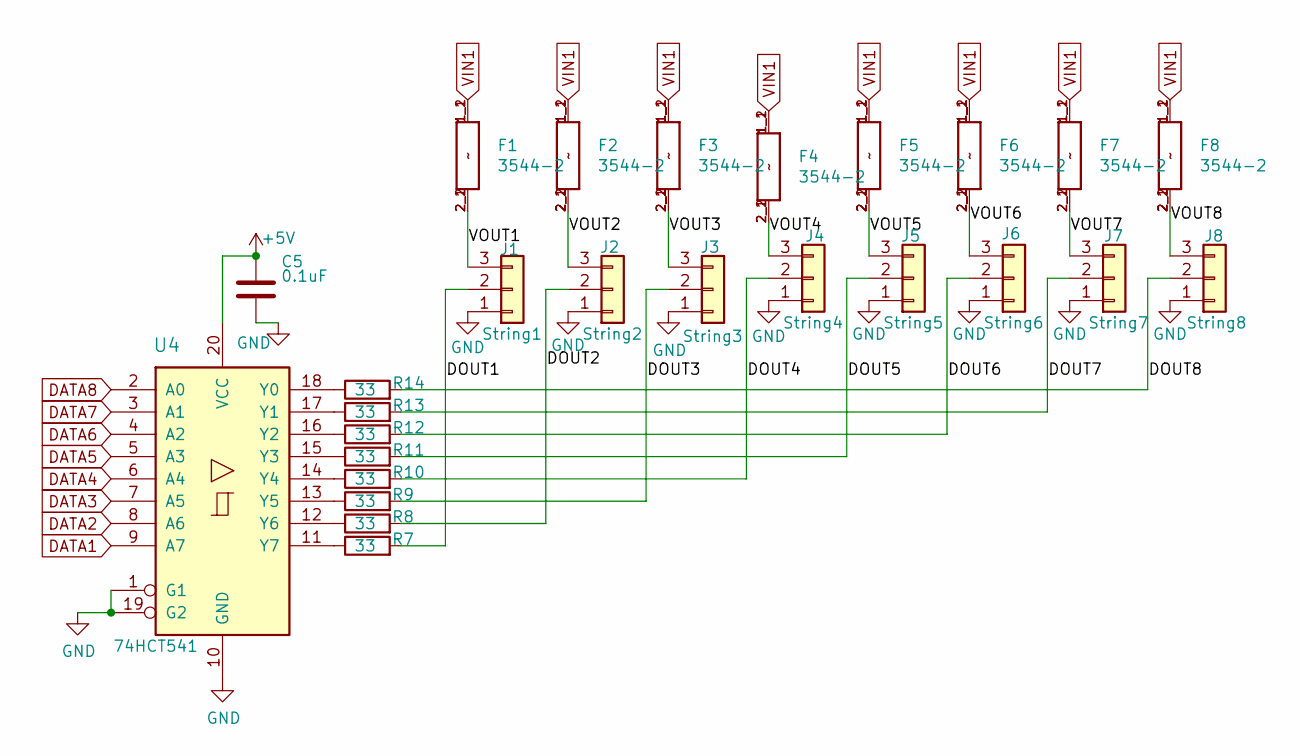
[picture p244: schematic Output1_8.kicad_sch, PB 16]

Parts:
C5: 0.1uF; C_0603_1608Metric; MPN CL10B104KB8NNWC; Digi-Key_PN 1276-1935-2-ND
F1, F2, F3, F4, F5, F6, F7, F8: 3544-2; FUSE_3544-2; MPN 3544-2; Digi-Key_PN 36-3544-2-ND
J1: String1; PhoenixContact_MCV_3.81mm_3.5mm_1x03_Vertical; MPN 1843619/OSTTJ0311530; Digi-Key_PN 277-5737-ND/ED10555-ND
J2: String2; PhoenixContact_MCV_3.81mm_3.5mm_1x03_Vertical; MPN 1843619/OSTTJ0311530; Digi-Key_PN 277-5737-ND/ED10555-ND
J3: String3; PhoenixContact_MCV_3.81mm_3.5mm_1x03_Vertical; MPN 1843619/OSTTJ0311530; Digi-Key_PN 277-5737-ND/ED10555-ND
J4: String4; PhoenixContact_MCV_3.81mm_3.5mm_1x03_Vertical; MPN 1843619/OSTTJ0311530; Digi-Key_PN 277-5737-ND/ED10555-ND
J5: String5; PhoenixContact_MCV_3.81mm_3.5mm_1x03_Vertical; MPN 1843619/OSTTJ0311530; Digi-Key_PN 277-5737-ND/ED10555-ND
J6: String6; PhoenixContact_MCV_3.81mm_3.5mm_1x03_Vertical; MPN 1843619/OSTTJ0311530; Digi-Key_PN 277-5737-ND/ED10555-ND
J7: String7; PhoenixContact_MCV_3.81mm_3.5mm_1x03_Vertical; MPN 1843619/OSTTJ0311530; Digi-Key_PN 277-5737-ND/ED10555-ND
J8: String8; PhoenixContact_MCV_3.81mm_3.5mm_1x03_Vertical; MPN 1843619/OSTTJ0311530; Digi-Key_PN 277-5737-ND/ED10555-ND
R7, R8, R9, R10, R11, R12, R13, R14: 33; R_0603_1608Metric; MPN RC0603FR-0733RL; Digi-Key_PN 311-33.0HRCT-ND
U4: 74HCT541; TSSOP-20_4.4x6.5mm_P0.65mm; MPN SN74HCT541PWR; Digi-Key_PN MC74HCT541ADTR2GOSTR-ND

Connections:
+5V: C5.1, U4.20 (VCC); also elsewhere on the board
/Output 1-8/DOUT1: J1.2, R7.2
/Output 1-8/DOUT2: J2.2, R8.2
/Output 1-8/DOUT3: J3.2, R9.2
/Output 1-8/DOUT4: J4.2, R10.2
/Output 1-8/DOUT5: J5.2, R11.2
/Output 1-8/DOUT6: J6.2, R12.2
/Output 1-8/DOUT7: J7.2, R13.2
/Output 1-8/DOUT8: J8.2, R14.2
/Output 1-8/VOUT1: F1.2_1 (2), F1.2_2 (2), J1.3
/Output 1-8/VOUT2: F2.2_1 (2), F2.2_2 (2), J2.3
/Output 1-8/VOUT3: F3.2_1 (2), F3.2_2 (2), J3.3
/Output 1-8/VOUT4: F4.2_1 (2), F4.2_2 (2), J4.3
/Output 1-8/VOUT5: F5.2_1 (2), F5.2_2 (2), J5.3
/Output 1-8/VOUT6: F6.2_1 (2), F6.2_2 (2), J6.3
/Output 1-8/VOUT7: F7.2_1 (2), F7.2_2 (2), J7.3
/Output 1-8/VOUT8: F8.2_1 (2), F8.2_2 (2), J8.3
DATA1: U4.9 (A7); also elsewhere on the board
DATA2: U4.8 (A6); also elsewhere on the board
DATA3: U4.7 (A5); also elsewhere on the board
DATA4: U4.6 (A4); also elsewhere on the board
DATA5: U4.5 (A3); also elsewhere on the board
DATA6: U4.4 (A2); also elsewhere on the board
DATA7: U4.3 (A1); also elsewhere on the board
DATA8: U4.2 (A0); also elsewhere on the board
GND: C5.2, J1.1, J2.1, J3.1, J4.1, J5.1, J6.1, J7.1, J8.1, U4.1 (G1), U4.10 (GND), U4.19 (G2); also elsewhere on the board
unnamed: R14.1, U4.18 (Y0)
unnamed: R13.1, U4.17 (Y1)
unnamed: R12.1, U4.16 (Y2)
unnamed: R11.1, U4.15 (Y3)
unnamed: R10.1, U4.14 (Y4)
unnamed: R9.1, U4.13 (Y5)
unnamed: R8.1, U4.12 (Y6)
unnamed: R7.1, U4.11 (Y7)
VIN1: F1.1_1 (1), F1.1_2 (1), F2.1_1 (1), F2.1_2 (1), F3.1_1 (1), F3.1_2 (1), F4.1_1 (1), F4.1_2 (1), F5.1_1 (1), F5.1_2 (1), F6.1_1 (1), F6.1_2 (1), F7.1_1 (1), F7.1_2 (1), F8.1_1 (1), F8.1_2 (1); also elsewhere on the board

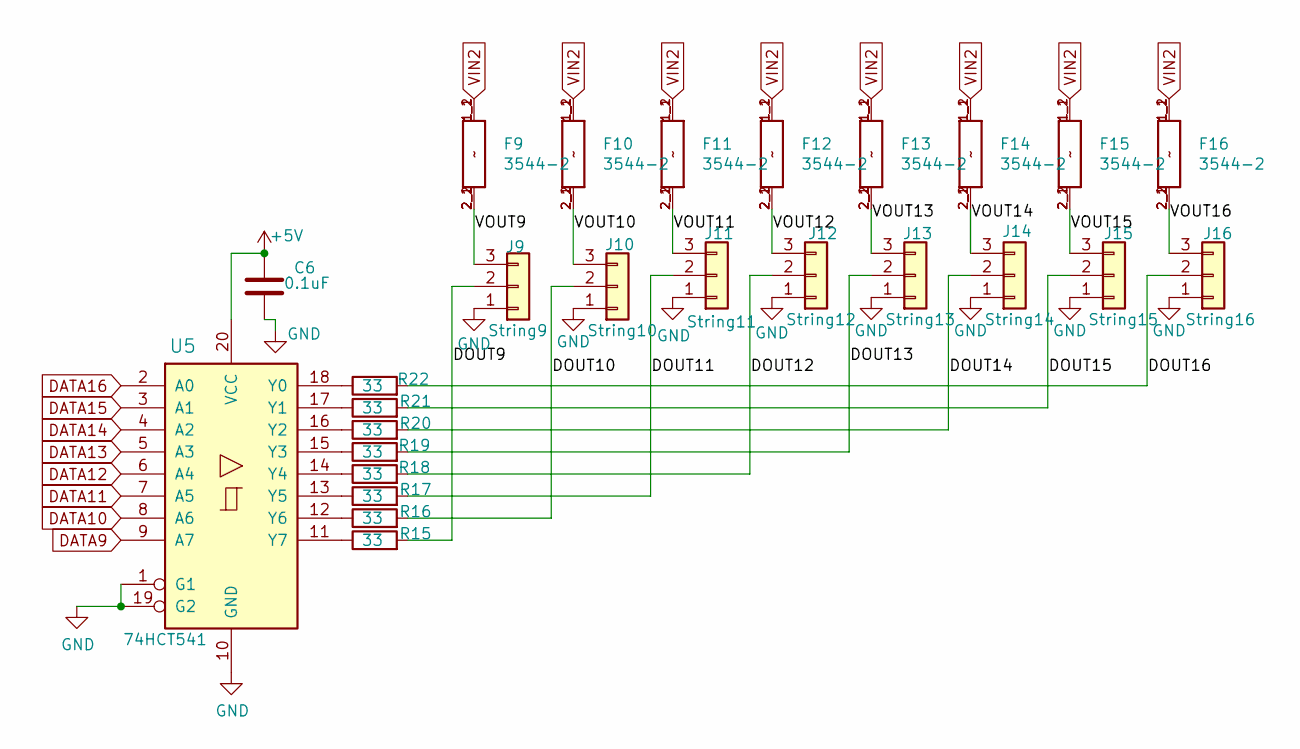
[picture p245: schematic Output9_16.kicad_sch, PB 16]

Parts:
C6: 0.1uF; C_0603_1608Metric; MPN CL10B104KB8NNWC; Digi-Key_PN 1276-1935-2-ND
F9, F10, F11, F12, F13, F14, F15, F16: 3544-2; FUSE_3544-2; MPN 3544-2; Digi-Key_PN 36-3544-2-ND
J9: String9; PhoenixContact_MCV_3.81mm_3.5mm_1x03_Vertical; MPN 1843619/OSTTJ0311530; Digi-Key_PN 277-5737-ND/ED10555-ND
J10: String10; PhoenixContact_MCV_3.81mm_3.5mm_1x03_Vertical; MPN 1843619/OSTTJ0311530; Digi-Key_PN 277-5737-ND/ED10555-ND
J11: String11; PhoenixContact_MCV_3.81mm_3.5mm_1x03_Vertical; MPN 1843619/OSTTJ0311530; Digi-Key_PN 277-5737-ND/ED10555-ND
J12: String12; PhoenixContact_MCV_3.81mm_3.5mm_1x03_Vertical; MPN 1843619/OSTTJ0311530; Digi-Key_PN 277-5737-ND/ED10555-ND
J13: String13; PhoenixContact_MCV_3.81mm_3.5mm_1x03_Vertical; MPN 1843619/OSTTJ0311530; Digi-Key_PN 277-5737-ND/ED10555-ND
J14: String14; PhoenixContact_MCV_3.81mm_3.5mm_1x03_Vertical; MPN 1843619/OSTTJ0311530; Digi-Key_PN 277-5737-ND/ED10555-ND
J15: String15; PhoenixContact_MCV_3.81mm_3.5mm_1x03_Vertical; MPN 1843619/OSTTJ0311530; Digi-Key_PN 277-5737-ND/ED10555-ND
J16: String16; PhoenixContact_MCV_3.81mm_3.5mm_1x03_Vertical; MPN 1843619/OSTTJ0311530; Digi-Key_PN 277-5737-ND/ED10555-ND
R15, R16, R17, R18, R19, R20, R21, R22: 33; R_0603_1608Metric; MPN RC0603FR-0733RL; Digi-Key_PN 311-33.0HRCT-ND
U5: 74HCT541; TSSOP-20_4.4x6.5mm_P0.65mm; MPN SN74HCT541PWR; Digi-Key_PN MC74HCT541ADTR2GOSTR-ND

Connections:
+5V: C6.1, U5.20 (VCC); also elsewhere on the board
/Output 9-16/DOUT9: J9.2, R15.2
/Output 9-16/DOUT10: J10.2, R16.2
/Output 9-16/DOUT11: J11.2, R17.2
/Output 9-16/DOUT12: J12.2, R18.2
/Output 9-16/DOUT13: J13.2, R19.2
/Output 9-16/DOUT14: J14.2, R20.2
/Output 9-16/DOUT15: J15.2, R21.2
/Output 9-16/DOUT16: J16.2, R22.2
/Output 9-16/VOUT9: F9.2_1 (2), F9.2_2 (2), J9.3
/Output 9-16/VOUT10: F10.2_1 (2), F10.2_2 (2), J10.3
/Output 9-16/VOUT11: F11.2_1 (2), F11.2_2 (2), J11.3
/Output 9-16/VOUT12: F12.2_1 (2), F12.2_2 (2), J12.3
/Output 9-16/VOUT13: F13.2_1 (2), F13.2_2 (2), J13.3
/Output 9-16/VOUT14: F14.2_1 (2), F14.2_2 (2), J14.3
/Output 9-16/VOUT15: F15.2_1 (2), F15.2_2 (2), J15.3
/Output 9-16/VOUT16: F16.2_1 (2), F16.2_2 (2), J16.3
DATA9: U5.9 (A7); also elsewhere on the board
DATA10: U5.8 (A6); also elsewhere on the board
DATA11: U5.7 (A5); also elsewhere on the board
DATA12: U5.6 (A4); also elsewhere on the board
DATA13: U5.5 (A3); also elsewhere on the board
DATA14: U5.4 (A2); also elsewhere on the board
DATA15: U5.3 (A1); also elsewhere on the board
DATA16: U5.2 (A0); also elsewhere on the board
GND: C6.2, J9.1, J10.1, J11.1, J12.1, J13.1, J14.1, J15.1, J16.1, U5.1 (G1), U5.10 (GND), U5.19 (G2); also elsewhere on the board
unnamed: R22.1, U5.18 (Y0)
unnamed: R21.1, U5.17 (Y1)
unnamed: R20.1, U5.16 (Y2)
unnamed: R19.1, U5.15 (Y3)
unnamed: R18.1, U5.14 (Y4)
unnamed: R17.1, U5.13 (Y5)
unnamed: R16.1, U5.12 (Y6)
unnamed: R15.1, U5.11 (Y7)
VIN2: F9.1_1 (1), F9.1_2 (1), F10.1_1 (1), F10.1_2 (1), F11.1_1 (1), F11.1_2 (1), F12.1_1 (1), F12.1_2 (1), F13.1_1 (1), F13.1_2 (1), F14.1_1 (1), F14.1_2 (1), F15.1_1 (1), F15.1_2 (1), F16.1_1 (1), F16.1_2 (1); also elsewhere on the board

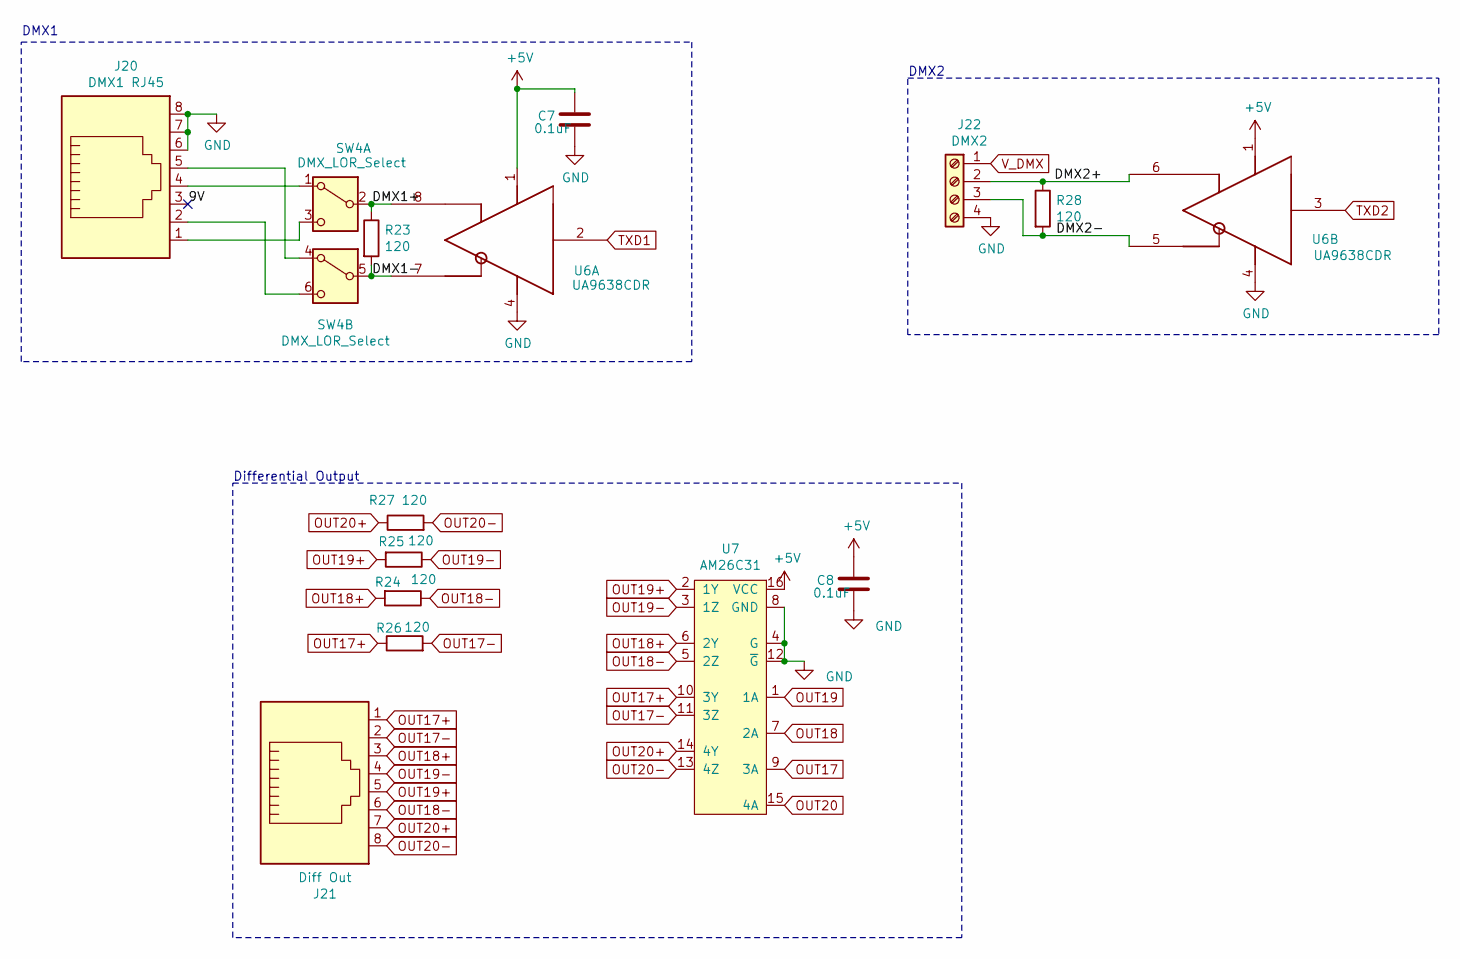
[picture p246: schematic Serial.kicad_sch, PB 16]

Parts:
C7, C8: 0.1uF; C_0603_1608Metric; MPN CL10B104KB8NNWC; Digi-Key_PN 1276-1935-2-ND
J20: DMX1 RJ45; RJ45_Amphenol_54602-x08_Horizontal; MPN X05ADIWA1DY1022; Digi-Key_PN AE10392-ND
J21: Diff Out; RJ45_Amphenol_54602-x08_Horizontal; MPN X05ADIWA1DY1022; Digi-Key_PN AE10392-ND
J22: DMX2; TerminalBlock_Phoenix_MKDS-1,5-4_1x04_P5.00mm_Horizontal; MPN 1729034; Digi-Key_PN 277-1238-ND
R23, R24, R25, R26, R27, R28: 120; R_0603_1608Metric; MPN CRGCQ0603F120R; Digi-Key_PN A129677CT-ND
SW4: DMX_LOR_Select; SW_CK_JS202011CQN_DPDT_Straight; MPN K3-2235D-F1; LCSC C189615
U6: UA9638CDR; SOIC-8_3.9x4.9mm_P1.27mm; MPN UA9638CDR; Digi-Key_PN 296-15058-1-ND
U7: AM26C31; SOIC-16_3.9x9.9mm_P1.27mm; MPN AM26C31IDR; Farnell 4975637

Connections:
+5V: C7.1, C8.1, U6.1 (VCC), U7.16 (VCC); also elsewhere on the board
/Serial/9V: J20.3
/Serial/DMX1+: R23.1, SW4.2 (B), U6.8 (OUTB)
/Serial/DMX1-: R23.2, SW4.5 (B), U6.7 (OUTA)
/Serial/DMX2+: J22.2, R28.1, U6.6 (OUTB)
/Serial/DMX2-: J22.3, R28.2, U6.5 (OUTA)
GND: C7.2, C8.2, J20.6, J20.7, J20.8, J22.4, U6.4 (GND), U7.4 (G), U7.8 (GND), U7.12 (~G); also elsewhere on the board
unnamed: J20.4, SW4.1 (A)
unnamed: J20.1, SW4.3 (C)
unnamed: J20.5, SW4.4 (A)
unnamed: J20.2, SW4.6 (C)
OUT17: U7.9 (3A); also elsewhere on the board
OUT17+: J21.1, R26.1, U7.10 (3Y)
OUT17-: J21.2, R26.2, U7.11 (3Z)
OUT18: U7.7 (2A); also elsewhere on the board
OUT18+: J21.3, R24.2, U7.6 (2Y)
OUT18-: J21.6, R24.1, U7.5 (2Z)
OUT19: U7.1 (1A); also elsewhere on the board
OUT19+: J21.5, R25.2, U7.2 (1Y)
OUT19-: J21.4, R25.1, U7.3 (1Z)
OUT20: U7.15 (4A); also elsewhere on the board
OUT20+: J21.7, R27.1, U7.14 (4Y)
OUT20-: J21.8, R27.2, U7.13 (4Z)
TXD1: U6.2 (IN); also elsewhere on the board
TXD2: U6.3 (IN); also elsewhere on the board
V_DMX: J22.1; also elsewhere on the board

Notes on the sheet:
Differential Output
DMX2
DMX1

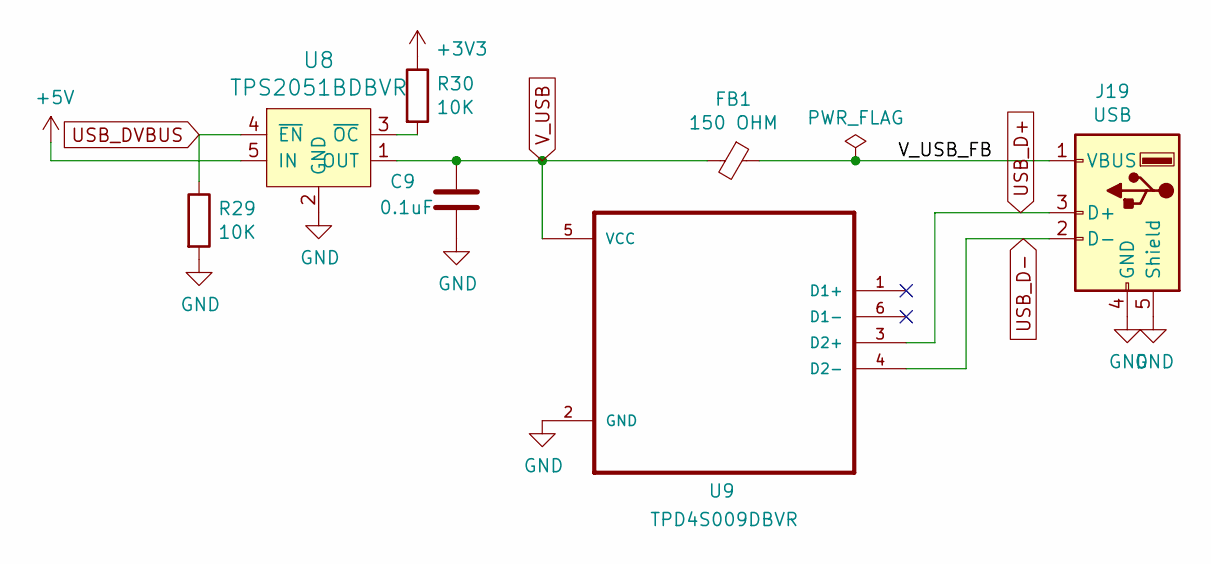
[picture p247: schematic USB.kicad_sch, PB 16]

Parts:
C9: 0.1uF; C_0603_1608Metric; MPN CL10B104KB8NNWC; Digi-Key_PN 1276-1935-2-ND
FB1: 150 OHM; L_0805_2012Metric; MPN MU2029-151Y; Digi-Key_PN MU2029-151YCT-ND
J19: USB; USB_A_Molex_105057_Vertical; MPN 1050570001; Digi-Key_PN WM8672-ND
R29, R30: 10K; R_0603_1608Metric; MPN RC0603FR-0710KL; Digi-Key_PN 311-10.0KHRCT-ND
U8: TPS2051BDBVR; SOT-753; MPN TPS2051BDBVR; Digi-Key_PN 296-21265-1-ND
U9: TPD4S009DBVR; SOT-23-6_Handsoldering; MPN TPD4S009DBVR; Digi-Key_PN 296-23749-1-ND

Connections:
+3V3: R30.1; also elsewhere on the board
+5V: U8.5 (IN); also elsewhere on the board
/USB/V_USB_FB: FB1.1, J19.1 (VBUS)
GND: C9.2, J19.4 (GND), J19.5 (Shield), R29.2, U8.2 (GND), U9.2 (GND); also elsewhere on the board
unnamed: R30.2, U8.3 (~OC)
USB_D+: J19.3 (D+), U9.3 (D2+); also elsewhere on the board
USB_D-: J19.2 (D-), U9.4 (D2-); also elsewhere on the board
USB_DVBUS: R29.1, U8.4 (~EN); also elsewhere on the board
V_USB: C9.1, FB1.2, U8.1 (OUT), U9.5 (VCC); also elsewhere on the board

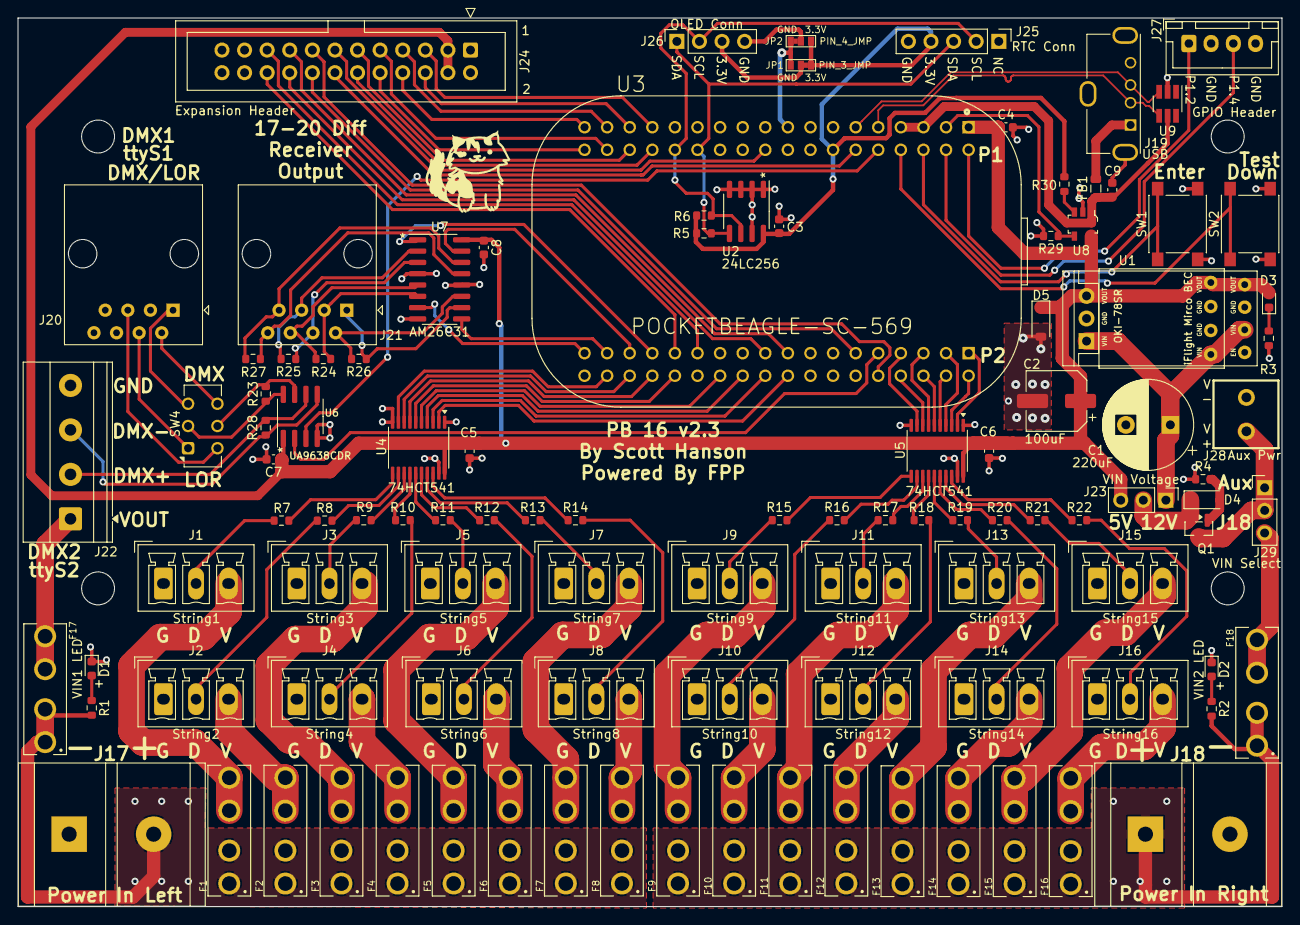
[picture p248: board PB_16v2_SMD/PB_16.kicad_pcb from above]

Board: 2 copper layers, 142.1 x 99.9 mm, 111 parts (0 on the bottom side), 130 nets.
