computergeek1507/PB_16/Exp_Filter/Exp_Filter.kicad_pcb

## KiCad design Exp_Filter/Exp_Filter.kicad_pcb (2026-03-06)

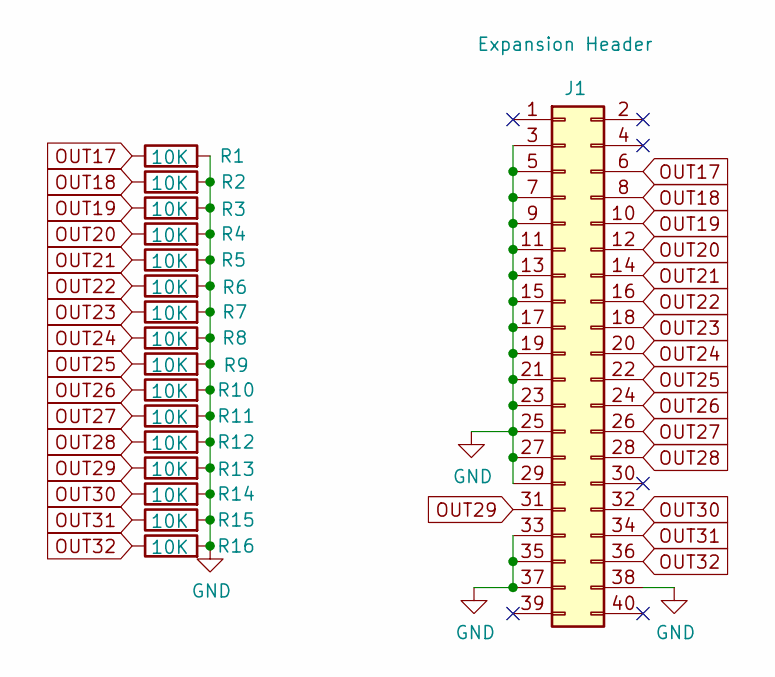
[picture p249: schematic Exp_Filter.kicad_sch]

Parts:
J1: Expansion Header; PinSocket_2x20_P2.54mm_Vertical; MPN SFH11-PBPC-D20-ST-BK; Digi-Key_PN S9200-ND
R1, R2, R3, R4, R5, R6, R7, R8, R9, R10, R11, R12, R13, R14, R15, R16: 10K; R_0603_1608Metric_Pad0.98x0.95mm_HandSolder; MPN RC0603FR-0710KL; Digi-Key_PN 311-10.0KHRCT-ND

Connections:
GND: J1.3, J1.5, J1.7, J1.9, J1.11, J1.13, J1.15, J1.17, J1.19, J1.21, J1.23, J1.25, J1.27, J1.29, J1.33, J1.35, J1.37, J1.38, R1.2, R2.2, R3.2, R4.2, R5.2, R6.2, R7.2, R8.2, R9.2, R10.2, R11.2, R12.2, R13.2, R14.2, R15.2, R16.2
OUT17: J1.6, R1.1
OUT18: J1.8, R2.1
OUT19: J1.10, R3.1
OUT20: J1.12, R4.1
OUT21: J1.14, R5.1
OUT22: J1.16, R6.1
OUT23: J1.18, R7.1
OUT24: J1.20, R8.1
OUT25: J1.22, R9.1
OUT26: J1.24, R10.1
OUT27: J1.26, R11.1
OUT28: J1.28, R12.1
OUT29: J1.31, R13.1
OUT30: J1.32, R14.1
OUT31: J1.34, R15.1
OUT32: J1.36, R16.1

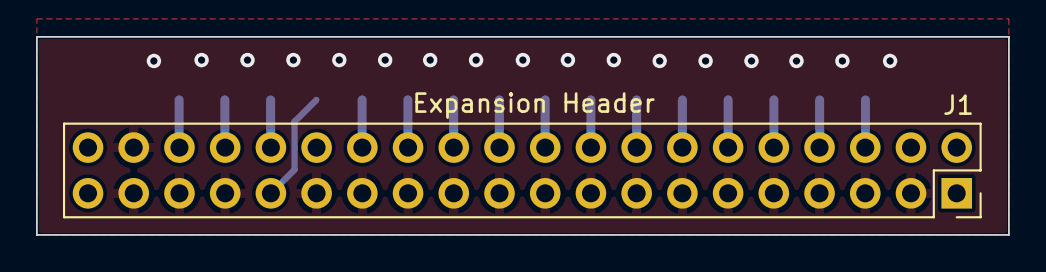
[picture p250: board Exp_Filter.kicad_pcb from above]

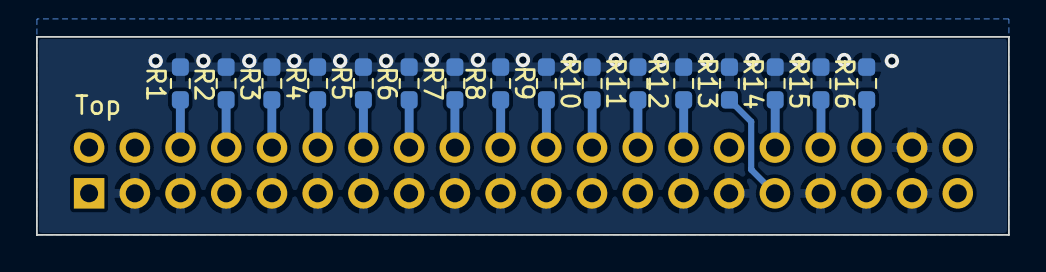
[picture p251: board Exp_Filter.kicad_pcb from below]

Board: 2 copper layers, 54.0 x 11.0 mm, 17 parts (16 on the bottom side), 17 nets.
