computergeek1507/PB_16/Single_Receiver_Out/Single_Receiver_Out.kicad_pcb

## KiCad design Single_Receiver_Out/Single_Receiver_Out.kicad_pcb (2026-03-06)

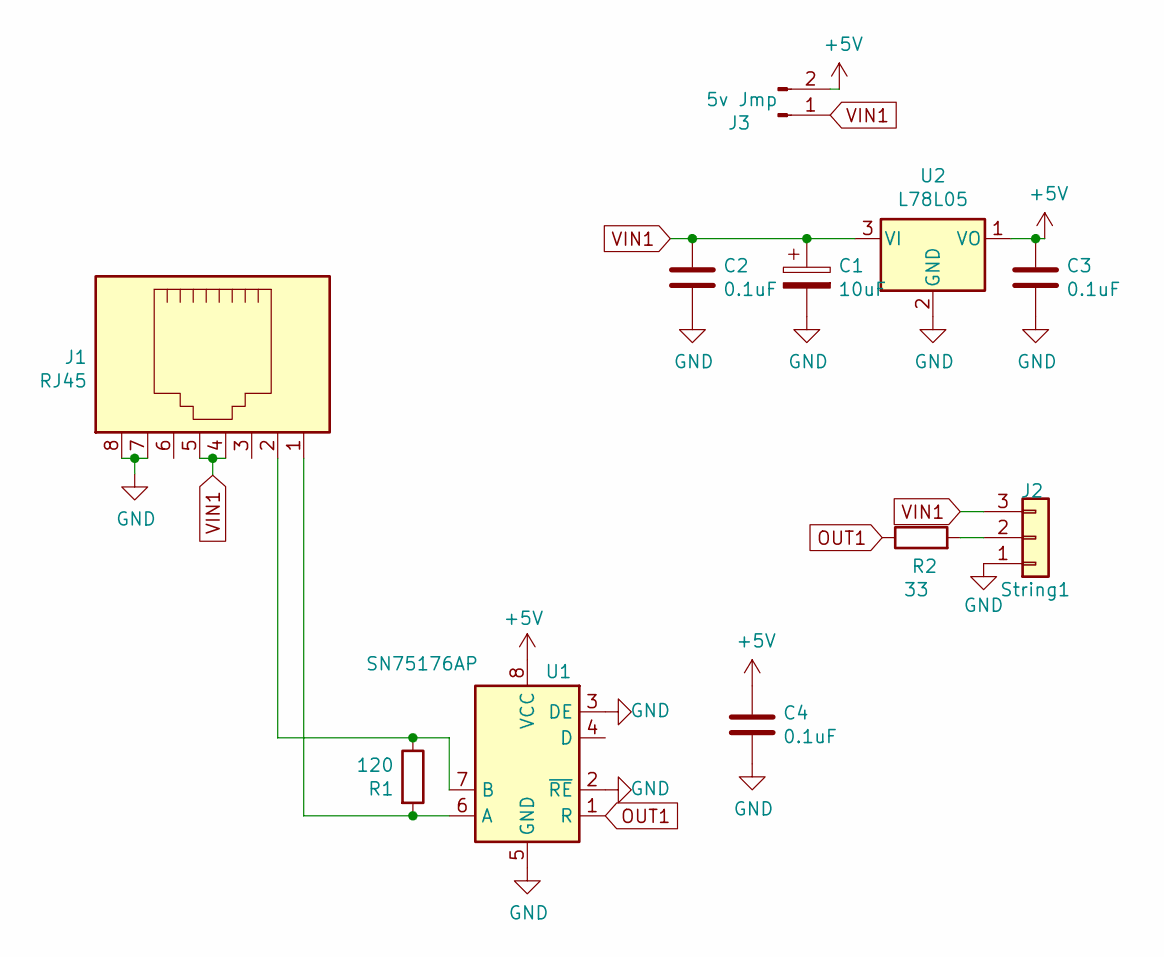
[picture p252: schematic Single_Receiver_Out.sch, Single Receiver Out]

Parts:
C1: 10uF; C_Rect_L7.0mm_W2.0mm_P5.00mm; MPN FK26X7R1E106K; Digi-Key_PN 445-FK26X7R1E106K-ND
C2, C3, C4: 0.1uF; C_Rect_L7.0mm_W2.0mm_P5.00mm; MPN SR215C104KARTR1; Digi-Key_PN 478-7336-1-ND
J1: RJ45; RJ45_Amphenol_54602-x08_Horizontal; MPN A-2014-2-4-R; Digi-Key_PN AE10392-ND
J2: String1; PhoenixContact_MCV_1,5_3-G-3.5_1x03_P3.50mm_Vertical; MPN 1843619/OSTTJ0311530; Digi-Key_PN 277-5737-ND/ED10555-ND
J3: 5v Jmp; PinHeader_1x02_P2.54mm_Vertical; MPN 61300211121; Digi-Key_PN 732-5315-ND
R1: 120; R_Axial_DIN0207_L6.3mm_D2.5mm_P7.62mm_Horizontal; MPN CF14JT120R; Digi-Key_PN CF14JT120RCT-ND
R2: 33; R_Axial_DIN0207_L6.3mm_D2.5mm_P7.62mm_Horizontal; MPN CF14JT33R0; Digi-Key_PN CF14JT33R0CT-ND
U1: SN75176AP; DIP-8_W7.62mm; MPN SN75176AP; Digi-Key_PN 296-1737-5-ND
U2: L78L05; TO-92_Inline; MPN MC78L05BP-AP; Digi-Key_PN MC78L05BP-APMSCT-ND

Connections:
+5V: C3.1, C4.1, J3.2, U1.8 (VCC), U2.1 (VO)
GND: C1.2, C2.2, C3.2, C4.2, J1.7, J1.8, J2.1, U1.2 (~RE), U1.3 (DE), U1.5 (GND), U2.2 (GND)
unnamed: J1.1, R1.2, U1.6 (A)
unnamed: J1.2, R1.1, U1.7 (B)
unnamed: J2.2, R2.2
OUT1: R2.1, U1.1 (R)
VIN1: C1.1, C2.1, J1.4, J1.5, J2.3, J3.1, U2.3 (VI)

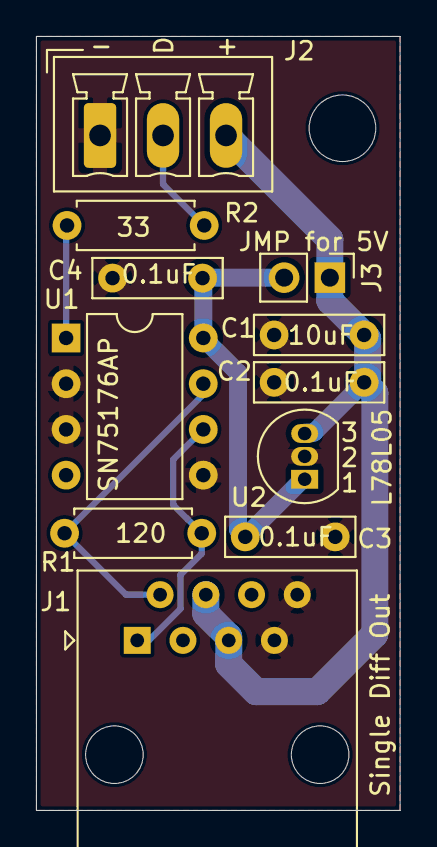
[picture p253: board Single_Receiver_Out.kicad_pcb from above]

Board: 2 copper layers, 20.2 x 43.0 mm, 11 parts (0 on the bottom side), 7 nets.
