computergeek1507/PB_16/Pwr_Diff_Expansion/Pwr_Diff_Expansion.kicad_pcb

## KiCad design Pwr_Diff_Expansion/Pwr_Diff_Expansion.kicad_pcb (2026-03-06)

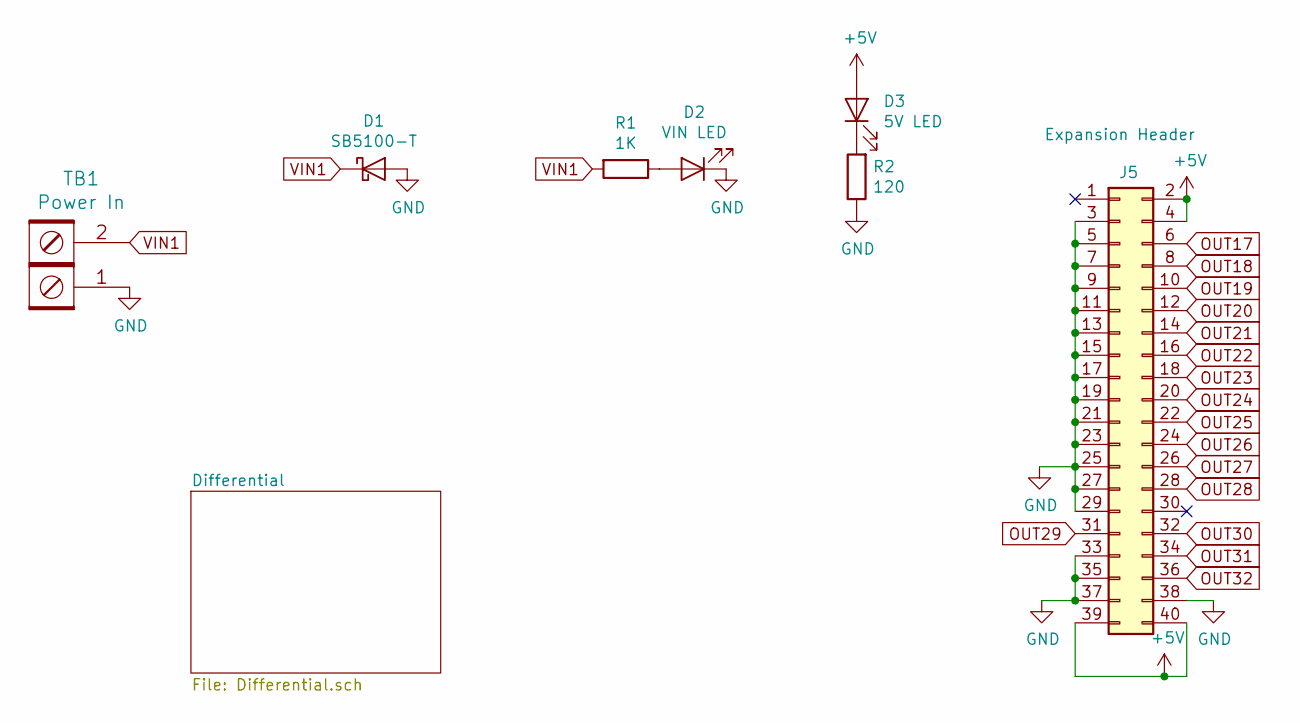
[picture p254: schematic Pwr_Diff_Expansion.sch, Pwr Diff Expansion]

Parts:
D1: SB5100-T; D_DO-201AD_P12.70mm_Horizontal; MPN SB5100-T; Digi-Key_PN SB5100DICT-ND
D2: VIN LED; LED_D3.0mm_Clear; MPN WP3A8GD; Digi-Key_PN 754-1217-ND
D3: 5V LED; LED_D3.0mm_Clear; MPN WP3A8GD; Digi-Key_PN 754-1217-ND
J5: Expansion Header; IDC-Header_2x20_P2.54mm_Vertical; MPN SBH11-PBPC-D20-ST-BK; Digi-Key_PN S9175-ND
R1: 1K; R_Axial_DIN0207_L6.3mm_D2.5mm_P7.62mm_Horizontal; MPN CF14JT1K00; Digi-Key_PN CF14JT1K00CT-ND
R2: 120; R_Axial_DIN0207_L6.3mm_D2.5mm_P7.62mm_Horizontal; MPN CF14JT120R; Digi-Key_PN CF14JT120RCT-ND
TB1: Power In; BARRIER_BLOCK_1ROW_2POS_P8.26MM; MPN 4DB-P108-02; Digi-Key_PN A98472-ND

Connections:
+5V: D3.2 (A), J5.2, J5.4, J5.39, J5.40; also elsewhere on the board
GND: D1.2 (A), D2.1 (K), J5.3, J5.5, J5.7, J5.9, J5.11, J5.13, J5.15, J5.17, J5.19, J5.21, J5.23, J5.25, J5.27, J5.29, J5.33, J5.35, J5.37, J5.38, R2.1, TB1.1; also elsewhere on the board
unnamed: D2.2 (A), R1.1
unnamed: D3.1 (K), R2.2
OUT17: J5.6; also elsewhere on the board
OUT18: J5.8; also elsewhere on the board
OUT19: J5.10; also elsewhere on the board
OUT20: J5.12; also elsewhere on the board
OUT21: J5.14
OUT22: J5.16
OUT23: J5.18
OUT24: J5.20
OUT25: J5.22
OUT26: J5.24
OUT27: J5.26
OUT28: J5.28
OUT29: J5.31
OUT30: J5.32
OUT31: J5.34
OUT32: J5.36
VIN1: D1.1 (K), R1.2, TB1.2; also elsewhere on the board

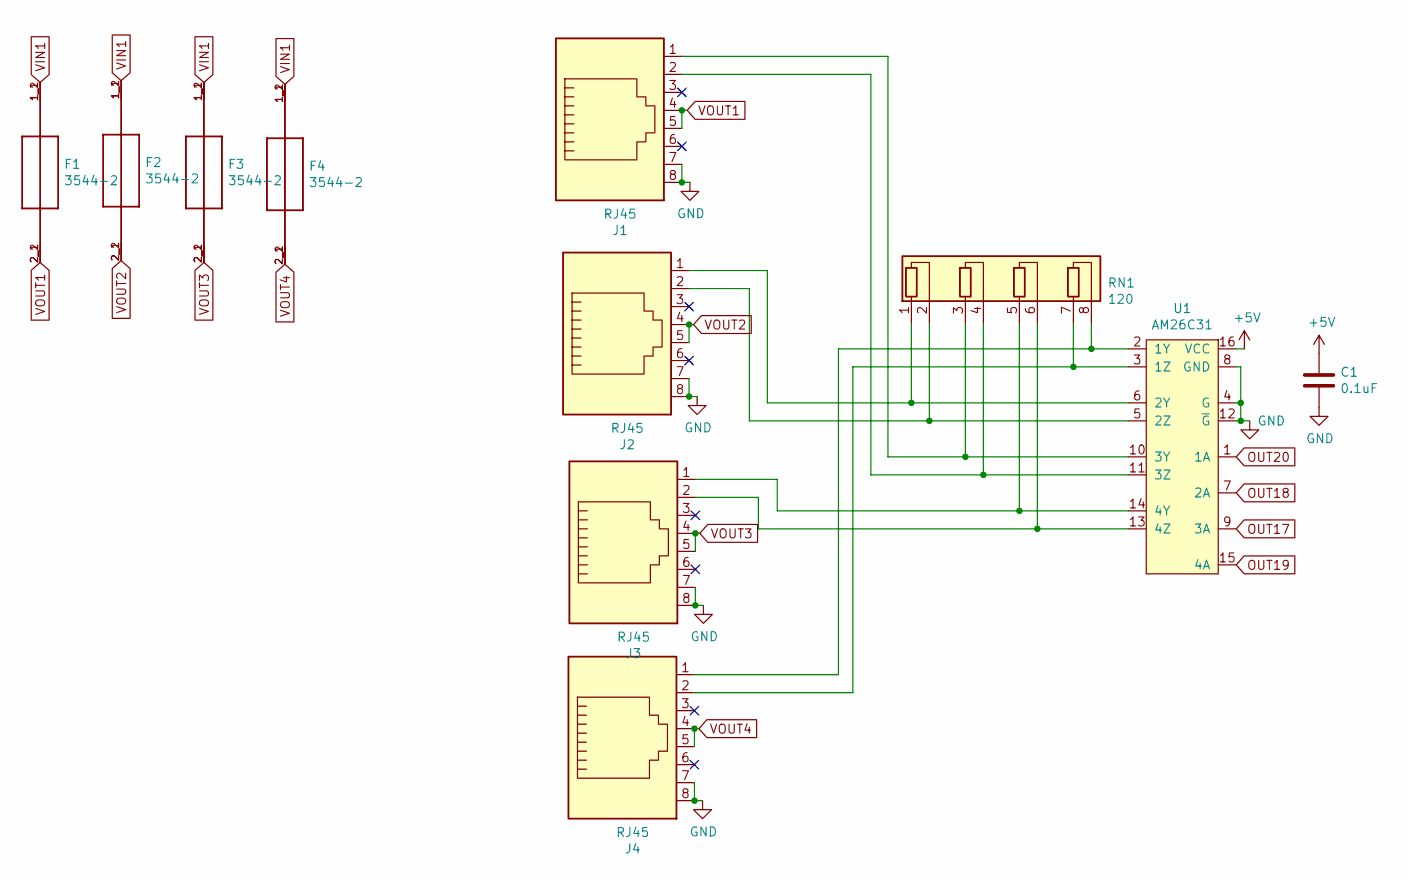
[picture p255: schematic Differential.sch, Pwr Diff Expansion]

Parts:
C1: 0.1uF; C_Rect_L7.0mm_W2.0mm_P5.00mm; MPN SR215C104KARTR1; Digi-Key_PN 478-7336-1-ND
F1, F2, F3, F4: 3544-2; FUSE_3544-2; MPN 3544-2; Digi-Key_PN 36-3544-2-ND
J1, J2, J3, J4: RJ45; RJ45_Amphenol_54602-x08_Horizontal; MPN A-2014-2-4-R; Digi-Key_PN AE10392-ND
RN1: 120; R_Array_SIP8; MPN 4608X-102-121LF; Digi-Key_PN 4608X-2-121LF-ND
U1: AM26C31; DIP-16_W7.62mm; MPN AM26C31IN; Farnell 4975637

Connections:
+5V: C1.1, U1.16 (VCC); also elsewhere on the board
GND: C1.2, J1.7, J1.8, J2.7, J2.8, J3.7, J3.8, J4.7, J4.8, U1.4 (G), U1.8 (GND), U1.12 (~G); also elsewhere on the board
unnamed: J1.1, RN1.3 (R2.1), U1.10 (3Y)
unnamed: J1.2, RN1.4 (R2.2), U1.11 (3Z)
unnamed: J2.1, RN1.1 (R1.1), U1.6 (2Y)
unnamed: J2.2, RN1.2 (R1.2), U1.5 (2Z)
unnamed: J3.1, RN1.5 (R3.1), U1.14 (4Y)
unnamed: J3.2, RN1.6 (R3.2), U1.13 (4Z)
unnamed: J4.1, RN1.8 (R4.2), U1.2 (1Y)
unnamed: J4.2, RN1.7 (R4.1), U1.3 (1Z)
OUT17: U1.9 (3A); also elsewhere on the board
OUT18: U1.7 (2A); also elsewhere on the board
OUT19: U1.15 (4A); also elsewhere on the board
OUT20: U1.1 (1A); also elsewhere on the board
VIN1: F1.1_1 (1), F1.1_2 (1), F2.1_1 (1), F2.1_2 (1), F3.1_1 (1), F3.1_2 (1), F4.1_1 (1), F4.1_2 (1); also elsewhere on the board
VOUT1: F1.2_1 (2), F1.2_2 (2), J1.4, J1.5
VOUT2: F2.2_1 (2), F2.2_2 (2), J2.4, J2.5
VOUT3: F3.2_1 (2), F3.2_2 (2), J3.4, J3.5
VOUT4: F4.2_1 (2), F4.2_2 (2), J4.4, J4.5

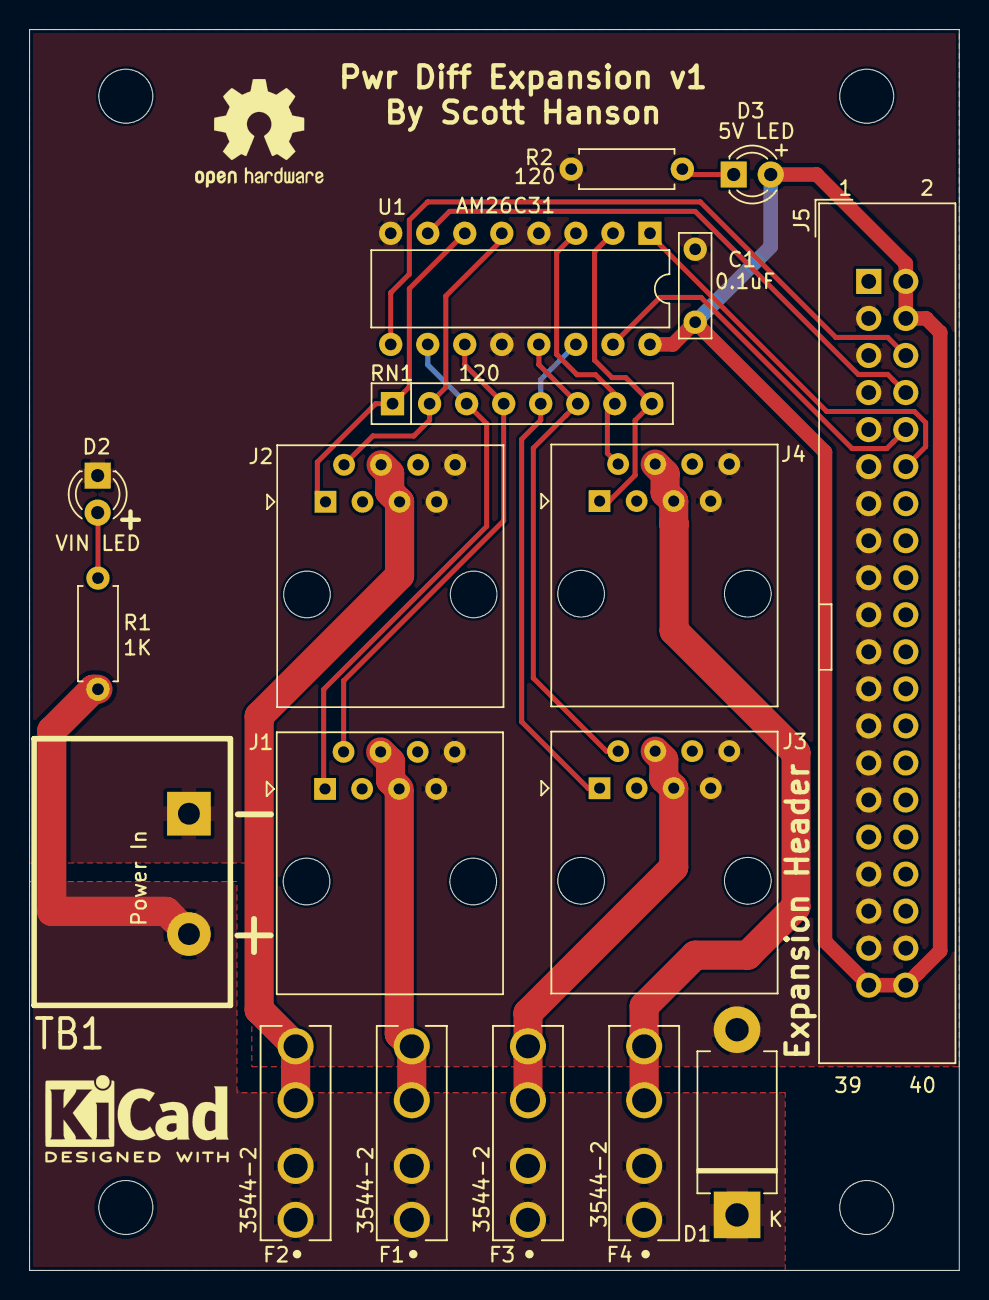
[picture p256: board Pwr_Diff_Expansion.kicad_pcb from above]

Board: 2 copper layers, 63.8 x 85.1 mm, 18 parts (0 on the bottom side), 21 nets.
