computergeek1507/PB_16/Pwr_Diff_Breakout/Pwr_Diff_Breakout.kicad_pcb

## KiCad design Pwr_Diff_Breakout/Pwr_Diff_Breakout.kicad_pcb (2026-03-06)

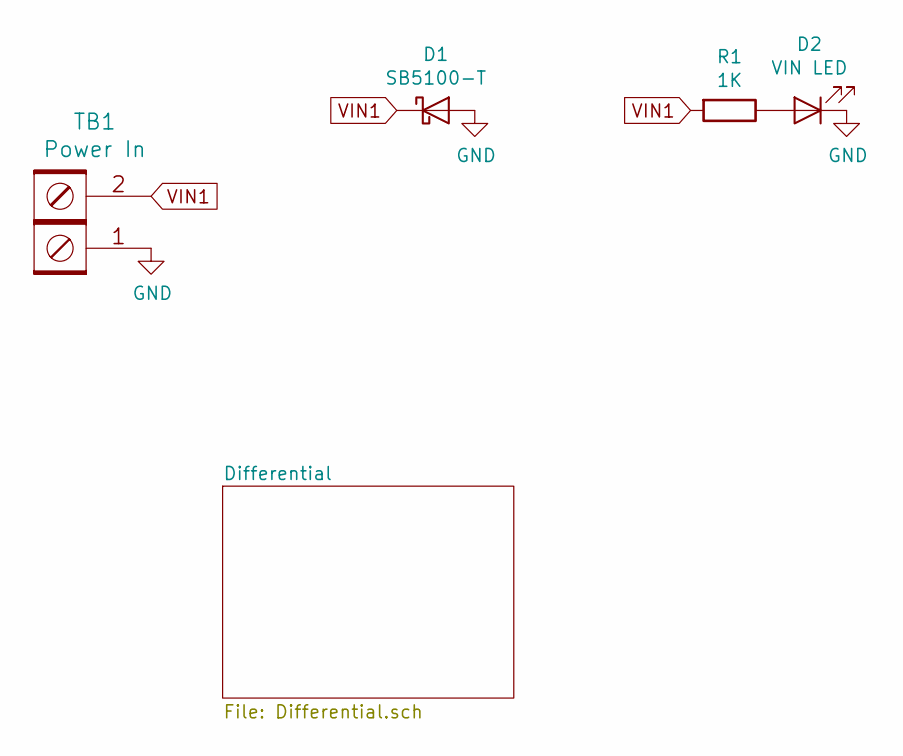
[picture p257: schematic Pwr_Diff_Breakout.sch, Pwr Diff Breakout]

Parts:
D1: SB5100-T; D_DO-201AD_P12.70mm_Horizontal; MPN SB5100-T; Digi-Key_PN SB5100DICT-ND
D2: VIN LED; LED_D3.0mm_Clear; MPN WP3A8GD; Digi-Key_PN 754-1217-ND
R1: 1K; R_Axial_DIN0207_L6.3mm_D2.5mm_P7.62mm_Horizontal; MPN CF14JT1K00; Digi-Key_PN CF14JT1K00CT-ND
TB1: Power In; BARRIER_BLOCK_1ROW_2POS_P8.26MM; MPN 4DB-P108-02; Digi-Key_PN A98472-ND

Connections:
GND: D1.2 (A), D2.1 (K), TB1.1; also elsewhere on the board
unnamed: D2.2 (A), R1.1
VIN1: D1.1 (K), R1.2, TB1.2; also elsewhere on the board

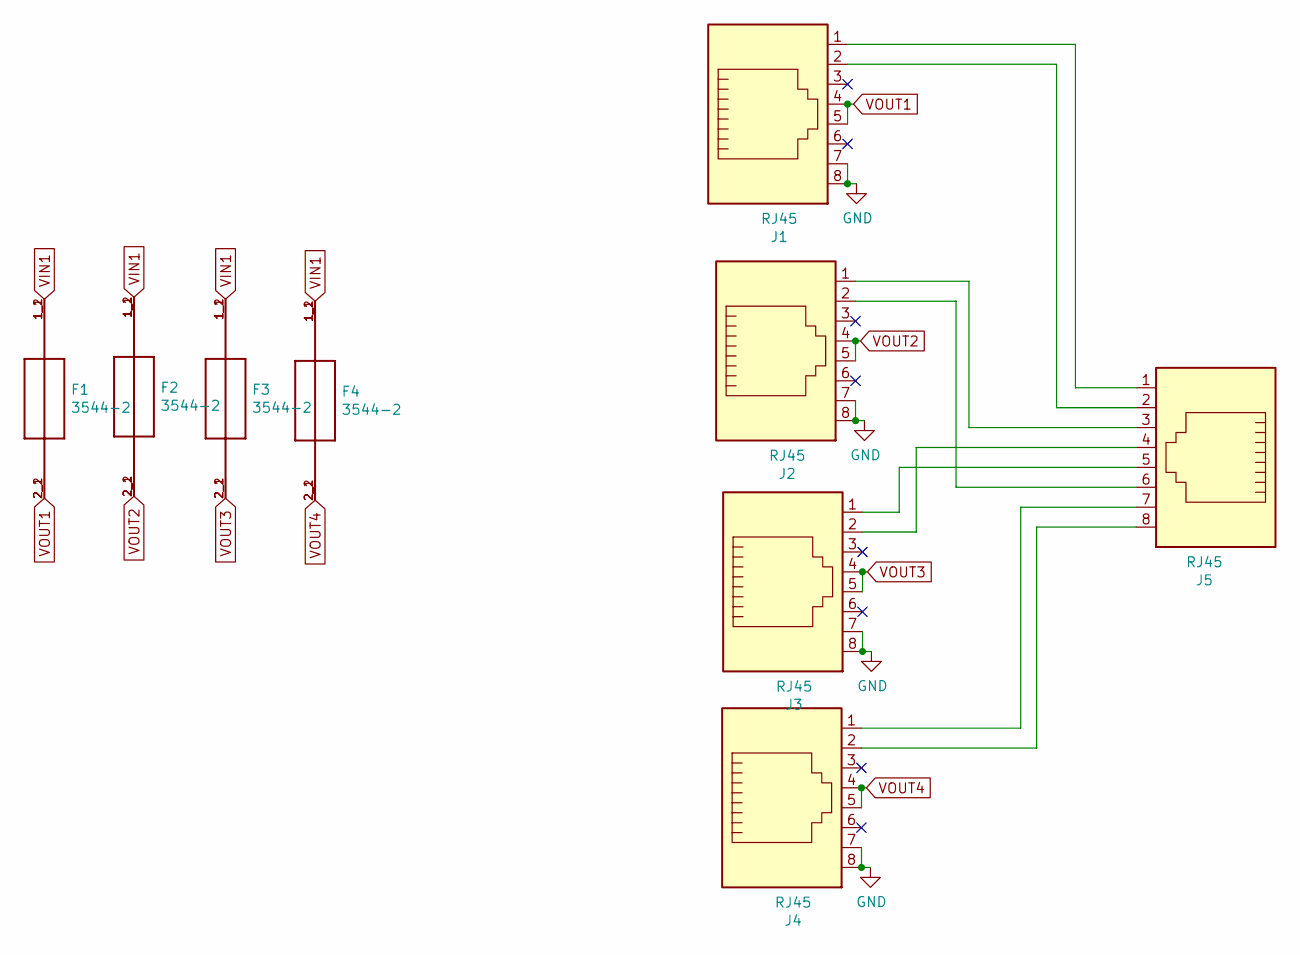
[picture p258: schematic Differential.sch, Pwr Diff Breakout]

Parts:
F1, F2, F3, F4: 3544-2; FUSE_3544-2; MPN 3544-2; Digi-Key_PN 36-3544-2-ND
J1, J2, J3, J4, J5: RJ45; RJ45_Amphenol_54602-x08_Horizontal; MPN A-2014-2-4-R; Digi-Key_PN AE10392-ND

Connections:
GND: J1.7, J1.8, J2.7, J2.8, J3.7, J3.8, J4.7, J4.8; also elsewhere on the board
unnamed: J1.1, J5.1
unnamed: J1.2, J5.2
unnamed: J2.1, J5.3
unnamed: J2.2, J5.6
unnamed: J3.1, J5.5
unnamed: J3.2, J5.4
unnamed: J4.1, J5.7
unnamed: J4.2, J5.8
VIN1: F1.1_1 (1), F1.1_2 (1), F2.1_1 (1), F2.1_2 (1), F3.1_1 (1), F3.1_2 (1), F4.1_1 (1), F4.1_2 (1); also elsewhere on the board
VOUT1: F1.2_1 (2), F1.2_2 (2), J1.4, J1.5
VOUT2: F2.2_1 (2), F2.2_2 (2), J2.4, J2.5
VOUT3: F3.2_1 (2), F3.2_2 (2), J3.4, J3.5
VOUT4: F4.2_1 (2), F4.2_2 (2), J4.4, J4.5
