computergeek1507/PB_16/Pwr_Diff_Breakout/Pwr_Diff_Breakout.kicad_pcb

## KiCad design Pwr_Diff_Breakout/Pwr_Diff_Breakout.kicad_pcb (continued)

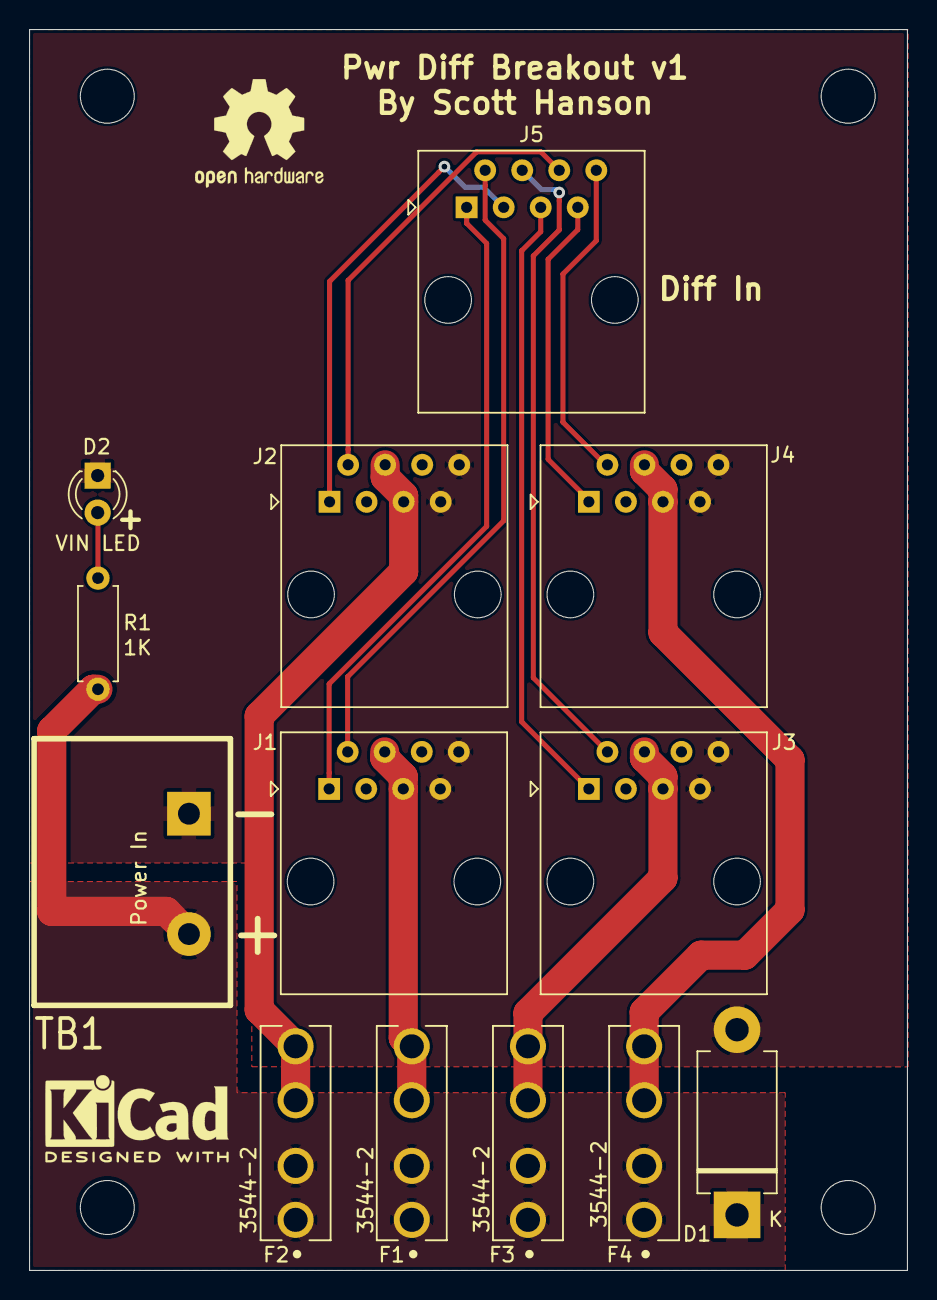
[picture p259: board Pwr_Diff_Breakout.kicad_pcb from above]

Board: 2 copper layers, 60.2 x 85.1 mm, 13 parts (0 on the bottom side), 15 nets.
