computergeek1507/PB_16/PB_16_E682/PB_16.kicad_pcb

## KiCad design PB_16_E682/PB_16.kicad_pcb (2026-03-06)

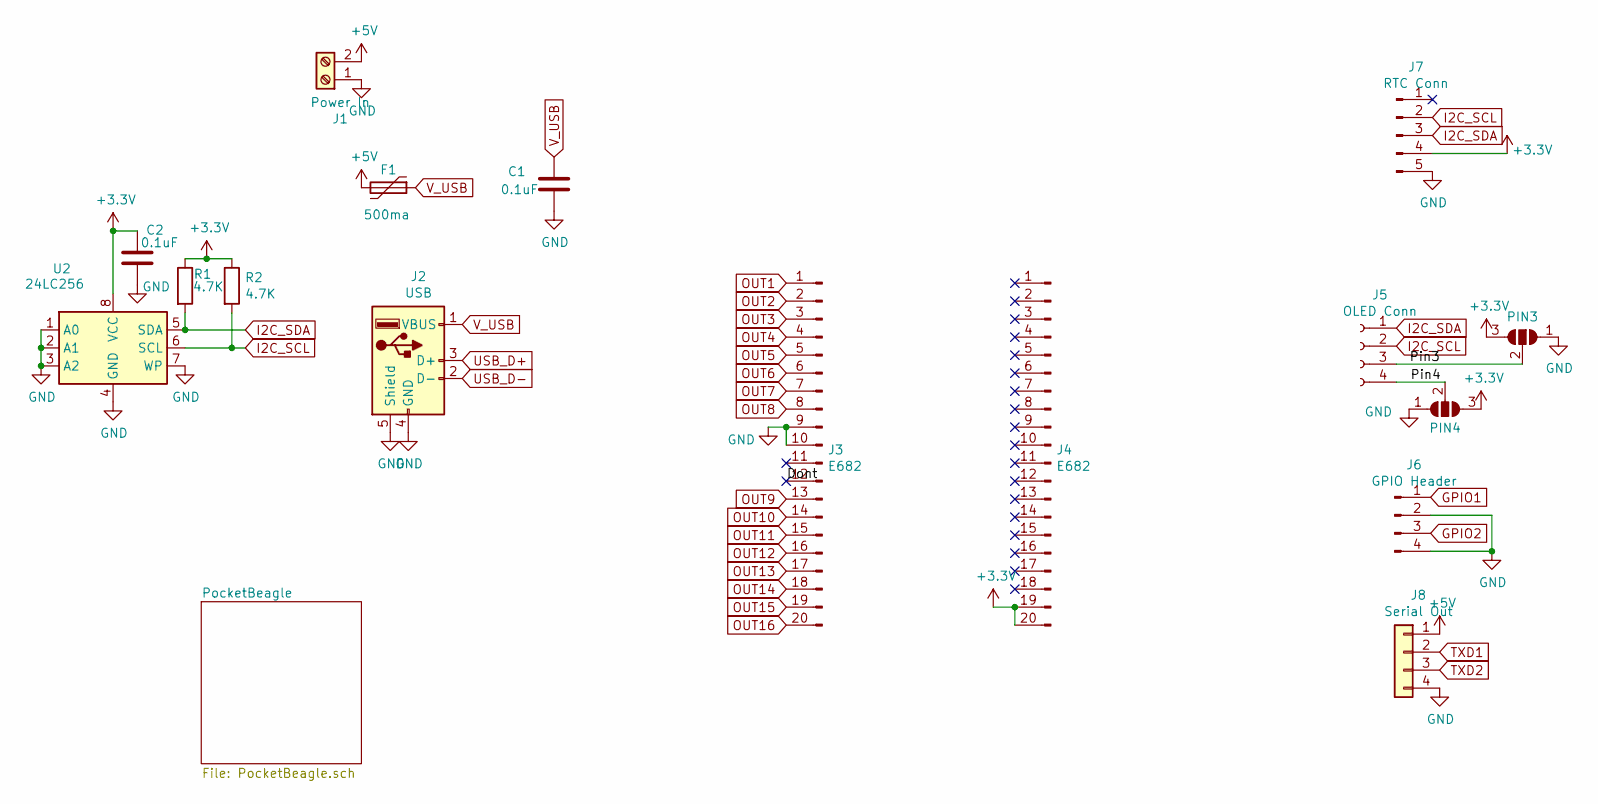
[picture p260: schematic PB_16.sch, PB 16 E682]

Parts:
C1, C2: 0.1uF; C_Rect_L7.0mm_W2.0mm_P5.00mm; MPN SR215C104KARTR1; Digi-Key_PN 478-7336-1-ND
F1: 500ma; Fuse_BelFuse_0ZRE0005FF_L8.3mm_W3.8mm; MPN RXEF050-2; Digi-Key_PN RXEF050-2HFCT-ND
J1: Power In; PHOENIX_MKDS1%2f2-3.81; MPN 1727010; Digi-Key_PN 277-1947-ND
J2: USB; USB_A_Molex_105057_Vertical; MPN 1050570001; Digi-Key_PN WM8672-ND
J3, J4: E682; PinHeader_1x20_P2.54mm_Vertical; MPN 61302011121; Digi-Key_PN 732-5329-ND
J5: OLED Conn; PinSocket_1x04_P2.54mm_Vertical; MPN PPTC041LFBN-RC; Digi-Key_PN S7002-ND
J6: GPIO Header; JST_XH_B4B-XH-A_1x04_P2.50mm_Vertical; MPN B4B-XH-A(LF)(SN); Digi-Key_PN 455-2249-ND
J7: RTC Conn; PinHeader_1x05_P2.54mm_Vertical; MPN 61300511121; Digi-Key_PN 732-5318-ND
J8: Serial Out; PinHeader_1x04_P2.54mm_Vertical; MPN 61300411121; Digi-Key_PN 732-5317-ND
PIN3, PIN4: SolderJumper_3_Open; SolderJumper-3_P1.3mm_Open_Pad1.0x1.5mm
R1, R2: 4.7K; R_Axial_DIN0207_L6.3mm_D2.5mm_P7.62mm_Horizontal; MPN CF14JT4K70; Digi-Key_PN CF14JT4K70CT-ND
U2: 24LC256; DIP-8_W7.62mm; MPN FT24C256A-UDR-B; Digi-Key_PN 1219-1052-ND

Connections:
+3V3: C2.1, J4.19, J4.20, J7.4, PIN3.3 (B), PIN4.3 (B), R1.1, R2.1, U2.8 (VCC); also elsewhere on the board
+5V: F1.2, J1.2, J8.1; also elsewhere on the board
/Dont: J3.12
/Pin3: J5.3, PIN3.2 (C)
/Pin4: J5.4, PIN4.2 (C)
GND: C1.2, C2.2, J1.1, J2.4 (GND), J2.5 (Shield), J3.9, J3.10, J6.2, J6.4, J7.5, J8.4, PIN3.1 (A), PIN4.1 (A), U2.1 (A0), U2.2 (A1), U2.3 (A2), U2.4 (GND), U2.7 (WP); also elsewhere on the board
GPIO1: J6.1; also elsewhere on the board
GPIO2: J6.3; also elsewhere on the board
I2C_SCL: J5.2, J7.2, R2.2, U2.6 (SCL); also elsewhere on the board
I2C_SDA: J5.1, J7.3, R1.2, U2.5 (SDA); also elsewhere on the board
OUT1: J3.1; also elsewhere on the board
OUT2: J3.2; also elsewhere on the board
OUT3: J3.3; also elsewhere on the board
OUT4: J3.4; also elsewhere on the board
OUT5: J3.5; also elsewhere on the board
OUT6: J3.6; also elsewhere on the board
OUT7: J3.7; also elsewhere on the board
OUT8: J3.8; also elsewhere on the board
OUT9: J3.13; also elsewhere on the board
OUT10: J3.14; also elsewhere on the board
OUT11: J3.15; also elsewhere on the board
OUT12: J3.16; also elsewhere on the board
OUT13: J3.17; also elsewhere on the board
OUT14: J3.18; also elsewhere on the board
OUT15: J3.19; also elsewhere on the board
OUT16: J3.20; also elsewhere on the board
TXD1: J8.2; also elsewhere on the board
TXD2: J8.3; also elsewhere on the board
USB_D+: J2.3 (D+); also elsewhere on the board
USB_D-: J2.2 (D-); also elsewhere on the board
V_USB: C1.1, F1.1, J2.1 (VBUS); also elsewhere on the board

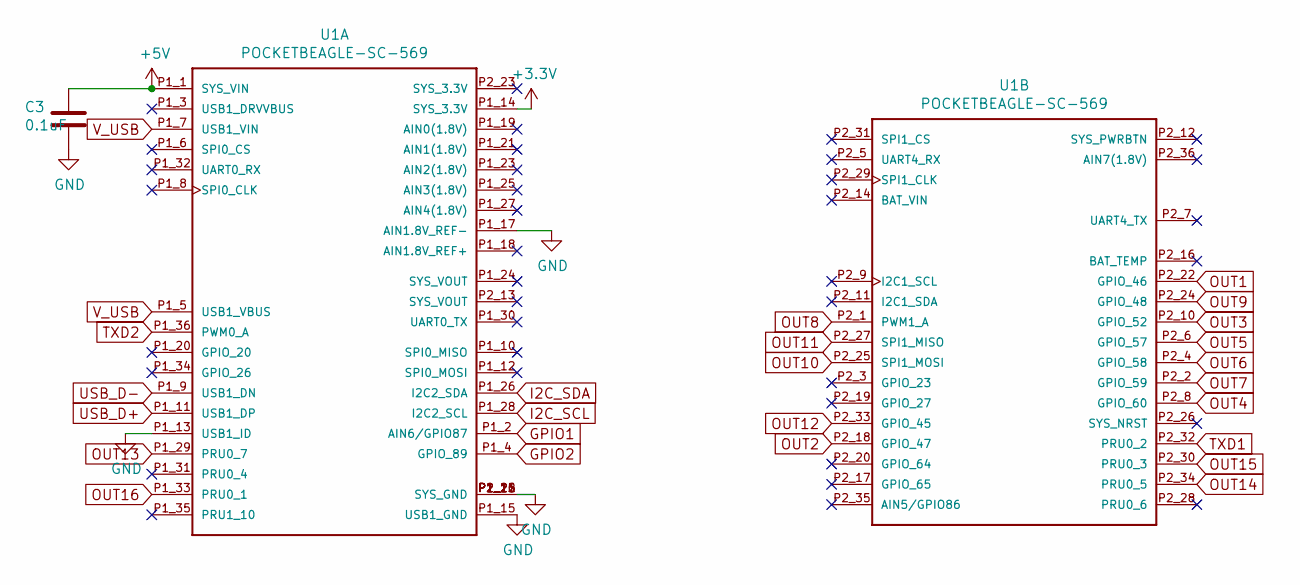
[picture p261: schematic PocketBeagle.sch, PB 16 E682]

Parts:
C3: 0.1uF; C_Rect_L7.0mm_W2.0mm_P5.00mm; MPN SR215C104KARTR1; Digi-Key_PN 478-7336-1-ND
U1: POCKETBEAGLE-SC-569; BEAGLE_POCKETBEAGLE-SC-569; MPN POCKETBEAGLE-SC-569; Digi-Key_PN POCKETBEAGLE-SC-569-ND

Connections:
+3V3: U1.P1_14 (SYS_3.3V); also elsewhere on the board
+5V: C3.1, U1.P1_1 (SYS_VIN); also elsewhere on the board
GND: C3.2, U1.P1_13 (USB1_ID), U1.P1_15 (USB1_GND), U1.P1_16 (SYS_GND), U1.P1_17 (AIN1.8V_REF-), U1.P1_22 (SYS_GND), U1.P2_15 (SYS_GND), U1.P2_21 (SYS_GND); also elsewhere on the board
GPIO1: U1.P1_2 (AIN6/GPIO87); also elsewhere on the board
GPIO2: U1.P1_4 (GPIO_89); also elsewhere on the board
I2C_SCL: U1.P1_28 (I2C2_SCL); also elsewhere on the board
I2C_SDA: U1.P1_26 (I2C2_SDA); also elsewhere on the board
OUT1: U1.P2_22 (GPIO_46); also elsewhere on the board
OUT2: U1.P2_18 (GPIO_47); also elsewhere on the board
OUT3: U1.P2_10 (GPIO_52); also elsewhere on the board
OUT4: U1.P2_8 (GPIO_60); also elsewhere on the board
OUT5: U1.P2_6 (GPIO_57); also elsewhere on the board
OUT6: U1.P2_4 (GPIO_58); also elsewhere on the board
OUT7: U1.P2_2 (GPIO_59); also elsewhere on the board
OUT8: U1.P2_1 (PWM1_A); also elsewhere on the board
OUT9: U1.P2_24 (GPIO_48); also elsewhere on the board
OUT10: U1.P2_25 (SPI1_MOSI); also elsewhere on the board
OUT11: U1.P2_27 (SPI1_MISO); also elsewhere on the board
OUT12: U1.P2_33 (GPIO_45); also elsewhere on the board
OUT13: U1.P1_29 (PRU0_7); also elsewhere on the board
OUT14: U1.P2_34 (PRU0_5); also elsewhere on the board
OUT15: U1.P2_30 (PRU0_3); also elsewhere on the board
OUT16: U1.P1_33 (PRU0_1); also elsewhere on the board
TXD1: U1.P2_32 (PRU0_2); also elsewhere on the board
TXD2: U1.P1_36 (PWM0_A); also elsewhere on the board
USB_D+: U1.P1_11 (USB1_DP); also elsewhere on the board
USB_D-: U1.P1_9 (USB1_DN); also elsewhere on the board
V_USB: U1.P1_5 (USB1_VBUS), U1.P1_7 (USB1_VIN); also elsewhere on the board

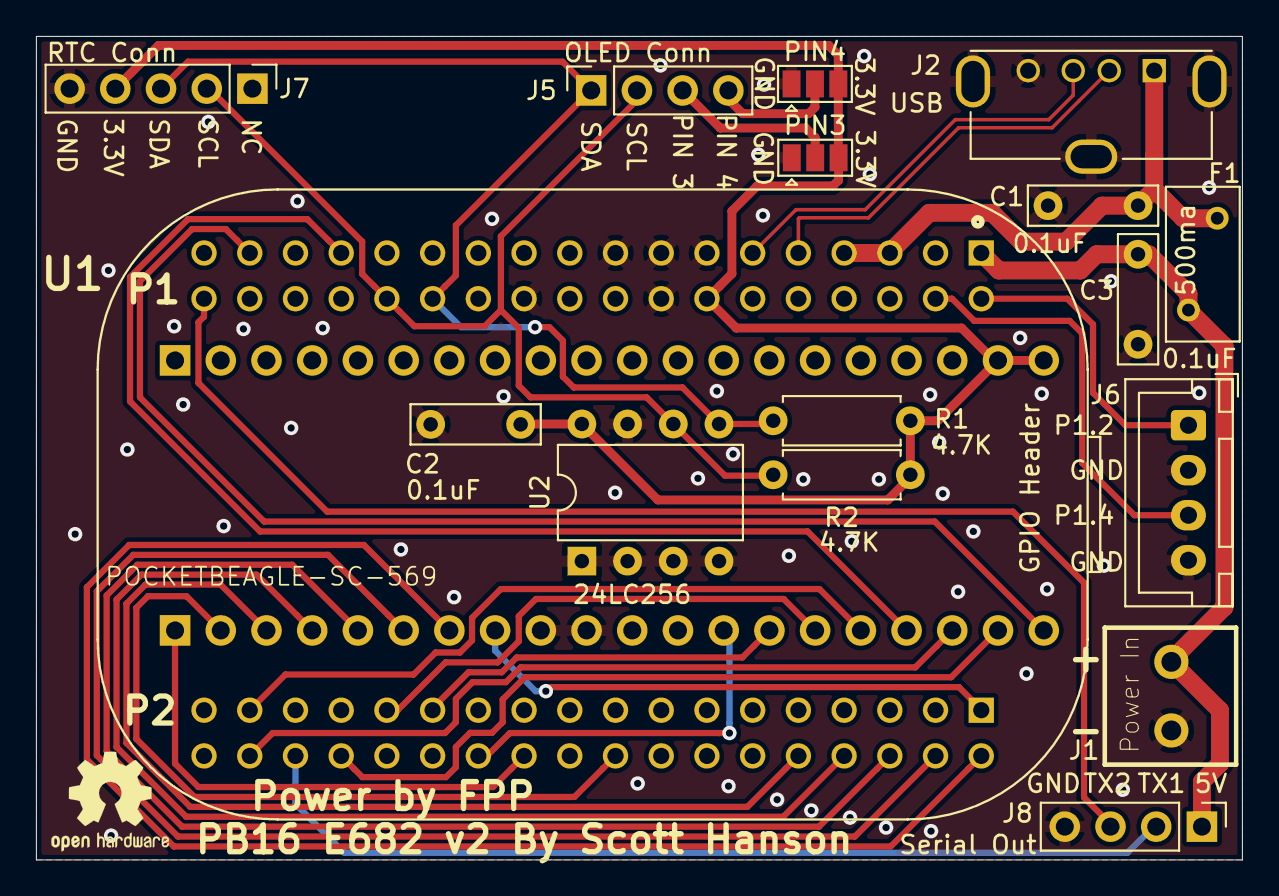
[picture p262: board PB_16_E682/PB_16.kicad_pcb from above]

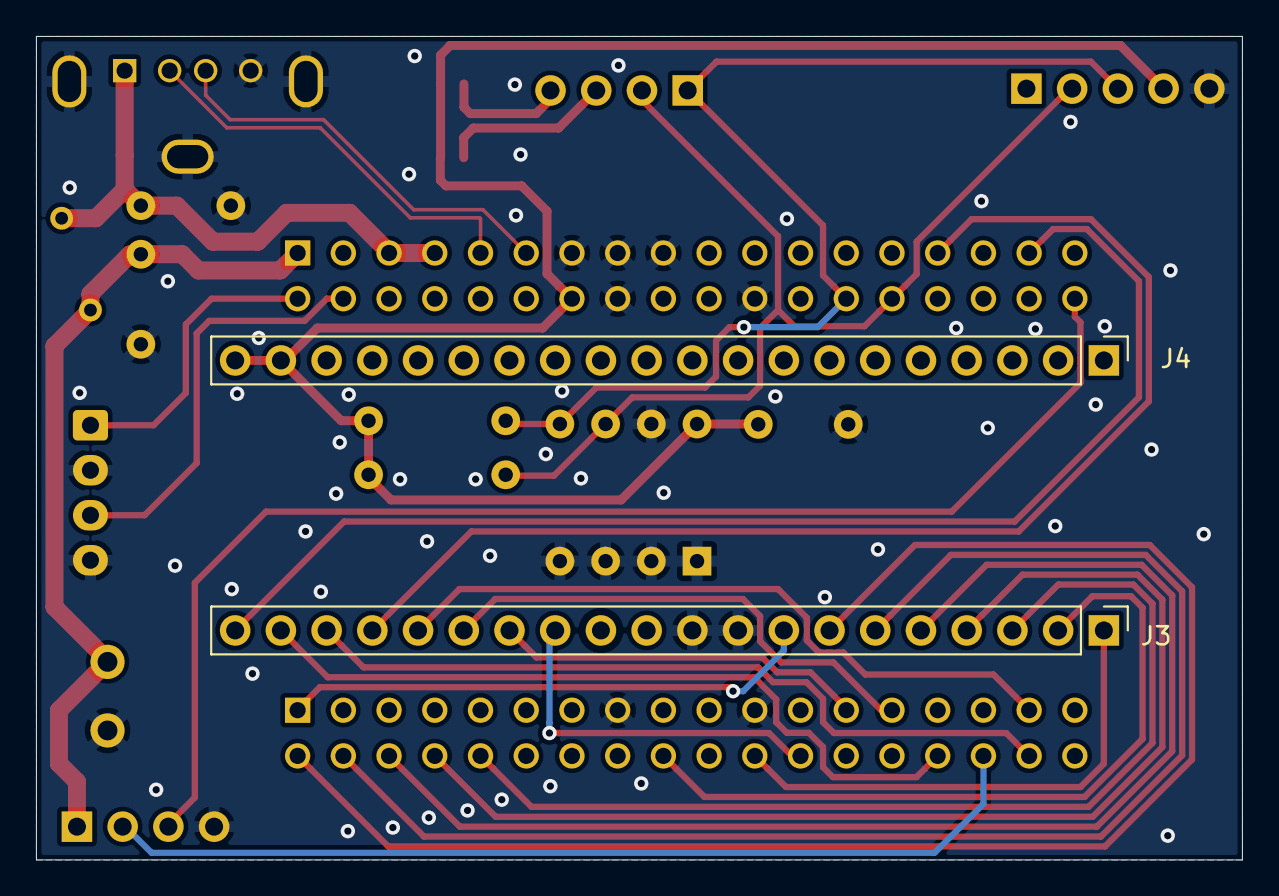
[picture p263: board PB_16_E682/PB_16.kicad_pcb from below]

Board: 2 copper layers, 67.0 x 45.8 mm, 18 parts (2 on the bottom side), 30 nets.
