computergeek1507/PB_16/I2C_Breakout/I2C_Breakout.kicad_pcb

## KiCad design I2C_Breakout/I2C_Breakout.kicad_pcb (2026-03-06)

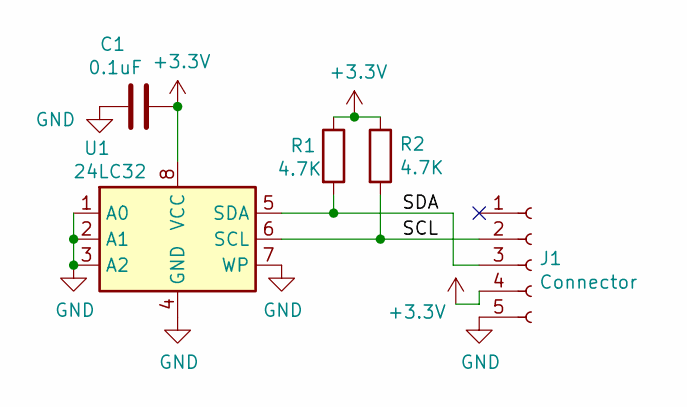
[picture p264: schematic I2C_Breakout.sch]

Parts:
C1: 0.1uF; C_Rect_L7.0mm_W2.0mm_P5.00mm
J1: Connector; PinSocket_1x05_P2.54mm_Vertical
R1, R2: 4.7K; R_Axial_DIN0207_L6.3mm_D2.5mm_P7.62mm_Horizontal
U1: 24LC32; DIP-8_W7.62mm

Connections:
+3V3: C1.1, J1.4, R1.1, R2.1, U1.8 (VCC)
/SCL: J1.2, R2.2, U1.6 (SCL)
/SDA: J1.3, R1.2, U1.5 (SDA)
GND: C1.2, J1.5, U1.1 (A0), U1.2 (A1), U1.3 (A2), U1.4 (GND), U1.7 (WP)

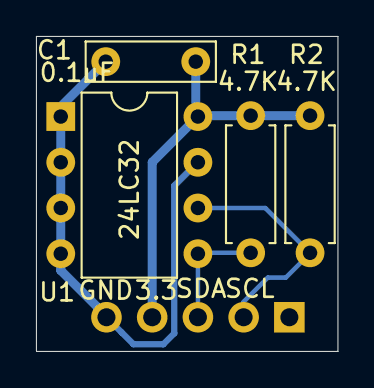
[picture p265: board I2C_Breakout.kicad_pcb from above]

Board: 2 copper layers, 16.8 x 17.5 mm, 5 parts (1 on the bottom side), 4 nets.
