computergeek1507/PB_16/Pi_CM4_16_SMD/Pi_CM4_16.kicad_pcb

## KiCad design Pi_CM4_16_SMD/Pi_CM4_16.kicad_pcb (2026-03-06)

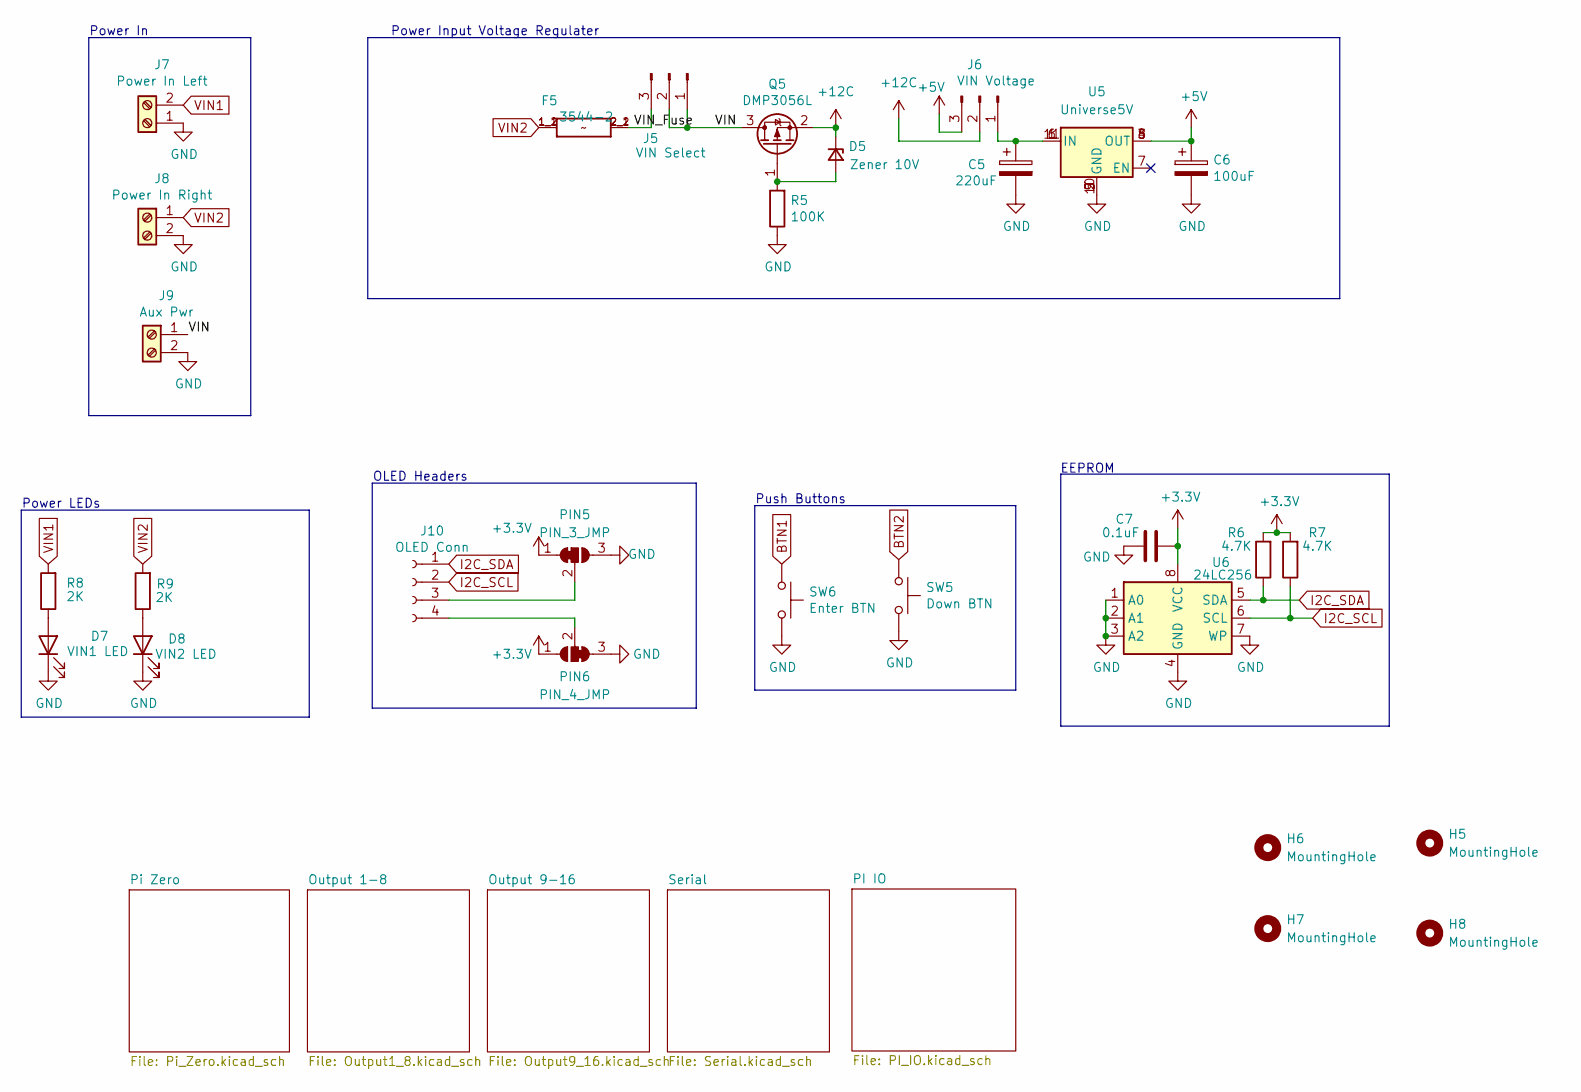
[picture p266: schematic Pi_CM4_16.kicad_sch, Pi CM4 16]

Parts:
C5: 220uF; CP_Radial_D10.0mm_P5.00mm; MPN ECA-1HM221; Digi-Key_PN P5183-ND
C6: 100uF; CP_Elec_6.3x5.4_Nichicon; MPN UWX1C101MCL1GB; Digi-Key_PN 493-2105-1-ND
C7: 0.1uF; C_0603_1608Metric_Pad1.08x0.95mm_HandSolder; MPN CL10B104KB8NNWC; Digi-Key_PN 1276-1935-2-ND
D5: Zener 10V; D_SOD-123; MPN MMSZ5240B-7-F; Digi-Key_PN MMSZ5240B-FDICT-ND
D7: VIN1 LED; LED_0603_1608Metric_Pad1.05x0.95mm_HandSolder; MPN LTST-C190KRKT; Digi-Key_PN 160-1436-2-ND
D8: VIN2 LED; LED_0603_1608Metric_Pad1.05x0.95mm_HandSolder; MPN LTST-C190KRKT; Digi-Key_PN 160-1436-2-ND
F5: 3544-2; FUSE_3544-2; MPN 3544-2; Digi-Key_PN 36-3544-2-ND
H5, H6, H7, H8: MountingHole; MountingHole_3.7mm
J5: VIN Select; PinHeader_1x03_P2.54mm_Vertical; MPN 61300311121; Digi-Key_PN 732-5316-ND
J6: VIN Voltage; PinHeader_1x03_P2.54mm_Vertical; MPN 61300311121; Digi-Key_PN 732-5316-ND
J7: Power In Left; BARRIER_BLOCK_1ROW_2POS_P9.5MM; MPN OSTYK51102030; Digi-Key_PN ED2953-ND
J8: Power In Right; BARRIER_BLOCK_1ROW_2POS_P9.5MM; MPN OSTYK51102030; Digi-Key_PN ED2953-ND
J9: Aux Pwr; PHOENIX_MKDS1_2-3.81; MPN 1727010; Digi-Key_PN 277-1947-ND
J10: OLED Conn; PinSocket_1x04_P2.54mm_Vertical; MPN PPTC041LFBN-RC; Digi-Key_PN S7002-ND
PIN5: PIN_3_JMP; SolderJumper-3_P1mm_Bridged12
PIN6: PIN_4_JMP; SolderJumper-3_P1mm_Bridged23
Q5: DMP3056L; SOT-23; MPN DMP3056L-7; Digi-Key_PN DMP3056L-7DICT-ND
R5: 100K; R_0603_1608Metric_Pad0.98x0.95mm_HandSolder; MPN RT0603BRD07100KL; Digi-Key_PN YAG1235CT-ND
R6, R7: 4.7K; R_0603_1608Metric_Pad0.98x0.95mm_HandSolder; MPN RC0603JR-074K7L; Digi-Key_PN 311-4.7KGRCT-ND
R8, R9: 2K; R_0603_1608Metric_Pad0.98x0.95mm_HandSolder
SW5: Down BTN; SW_Push_1P1T_NO_6x6mm_H9.5mm; MPN PTS645SL50SMTR92 LFS; Digi-Key_PN CKN9088CT-ND
SW6: Enter BTN; SW_Push_1P1T_NO_6x6mm_H9.5mm; MPN PTS645SL50SMTR92 LFS; Digi-Key_PN CKN9088CT-ND
U5: Universe5V; Universal_5V_Horizontal
U6: 24LC256; SOIC-8_3.9x4.9mm_P1.27mm; MPN 24LC256T-I/SN; Digi-Key_PN 24LC256T-I/SNCT-ND

Connections:
+3.3V: C7.1, PIN5.1 (A), PIN6.1 (A), R6.2, R7.2, U6.8 (VCC); also elsewhere on the board
+5V: C6.1, J6.3, U5.3 (OUT), U5.4 (OUT), U5.8 (OUT); also elsewhere on the board
+12C: D5.1 (K), J6.2, Q5.2 (S)
/VIN: J5.1, J5.2, J9.1, Q5.3 (D)
/VIN_Fuse: F5.2_1 (2), F5.2_2 (2), J5.3
BTN1: SW6.1; also elsewhere on the board
BTN2: SW5.1; also elsewhere on the board
GND: C5.2, C6.2, C7.2, D7.1 (K), D8.1 (K), J7.1, J8.2, J9.2, PIN5.3 (B), PIN6.3 (B), R5.1, SW5.2, SW6.2, U5.2 (GND), U5.5 (GND), U5.9 (GND), U5.10 (GND), U6.1 (A0), U6.2 (A1), U6.3 (A2), U6.4 (GND), U6.7 (WP); also elsewhere on the board
I2C_SCL: J10.2, R7.1, U6.6 (SCL); also elsewhere on the board
I2C_SDA: J10.1, R6.1, U6.5 (SDA); also elsewhere on the board
unnamed: C5.1, J6.1, U5.1 (IN), U5.6 (IN), U5.11 (IN)
unnamed: D5.2 (A), Q5.1 (G), R5.2
unnamed: D7.2 (A), R8.1
unnamed: D8.2 (A), R9.1
unnamed: J10.3, PIN5.2 (C)
unnamed: J10.4, PIN6.2 (C)
VIN1: J7.2, R8.2; also elsewhere on the board
VIN2: F5.1_1 (1), F5.1_2 (1), J8.1, R9.2; also elsewhere on the board

Notes on the sheet:
Power LEDs
Power In
OLED Headers
Push Buttons
Power Input Voltage Regulater
EEPROM

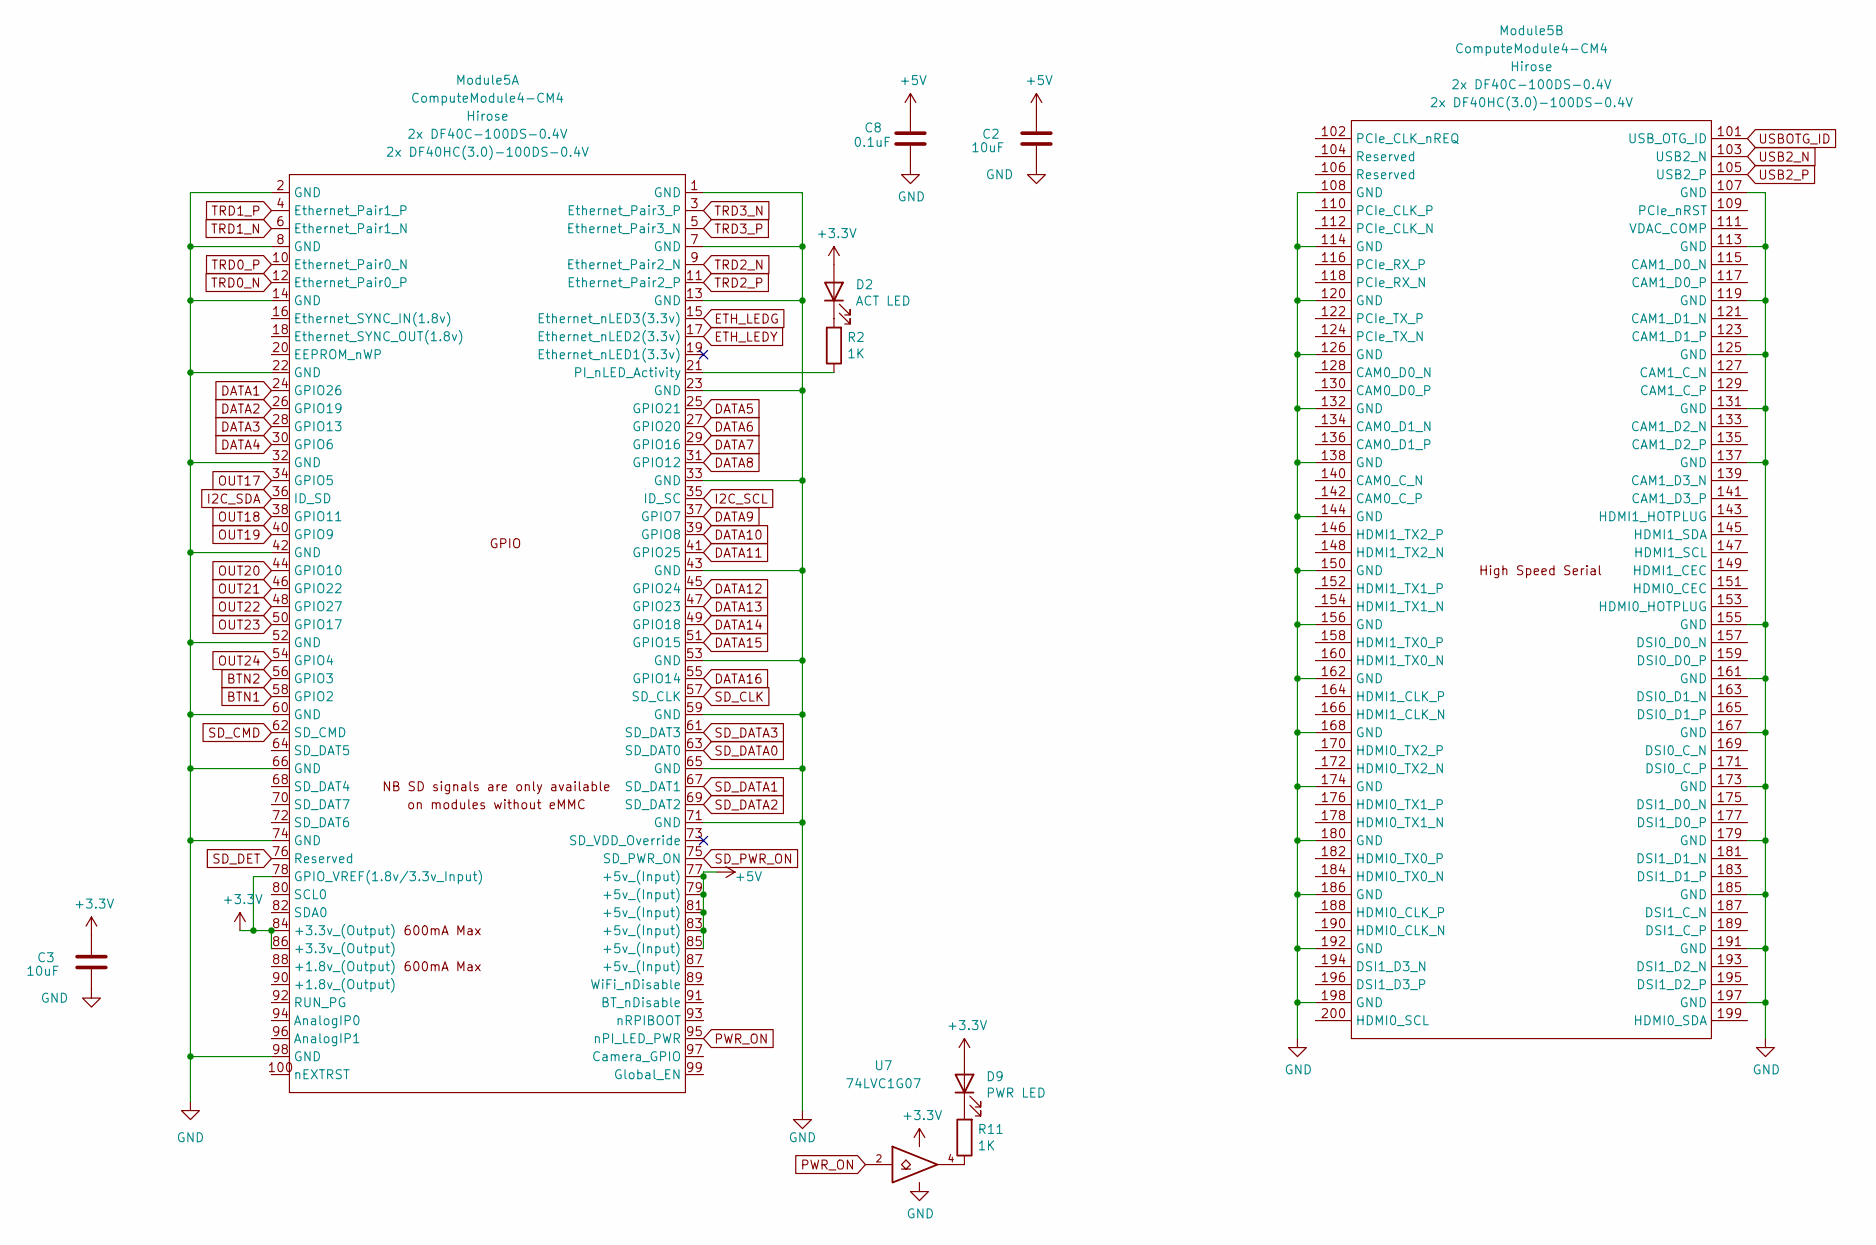
[picture p267: schematic Pi_Zero.kicad_sch, Pi CM4 16]

Parts:
C2, C3: 10uF; C_0603_1608Metric_Pad1.08x0.95mm_HandSolder
C8: 0.1uF; C_0603_1608Metric_Pad1.08x0.95mm_HandSolder; MPN CL10B104KB8NNWC; Digi-Key_PN 1276-1935-2-ND
D2: ACT LED; LED_0603_1608Metric_Pad1.05x0.95mm_HandSolder; MPN LTST-C190KRKT; Digi-Key_PN 160-1436-2-ND
D9: PWR LED; LED_0603_1608Metric_Pad1.05x0.95mm_HandSolder; MPN LTST-C190KRKT; Digi-Key_PN 160-1436-2-ND
Module5: ComputeModule4-CM4; Raspberry-Pi-4-Compute-Module; MPN 2x DF40C-100DS-0.4V; Digi-Key_PN 2x H11615CT-ND
R2, R11: 1K; R_0603_1608Metric_Pad0.98x0.95mm_HandSolder
U7: 74LVC1G07; SOT-23-5

Connections:
+3.3V: C3.2, D2.2 (A), D9.2 (A), Module5.78 (GPIO_VREF(1.8v/3.3v_Input)), Module5.84 (+3.3v_(Output)), Module5.86 (+3.3v_(Output)), U7.5 (VCC); also elsewhere on the board
+5V: C2.2, C8.1, Module5.77 (+5v_(Input)), Module5.79 (+5v_(Input)), Module5.81 (+5v_(Input)), Module5.83 (+5v_(Input)), Module5.85 (+5v_(Input)); also elsewhere on the board
BTN1: Module5.58 (GPIO2); also elsewhere on the board
BTN2: Module5.56 (GPIO3); also elsewhere on the board
DATA1: Module5.24 (GPIO26); also elsewhere on the board
DATA2: Module5.26 (GPIO19); also elsewhere on the board
DATA3: Module5.28 (GPIO13); also elsewhere on the board
DATA4: Module5.30 (GPIO6); also elsewhere on the board
DATA5: Module5.25 (GPIO21); also elsewhere on the board
DATA6: Module5.27 (GPIO20); also elsewhere on the board
DATA7: Module5.29 (GPIO16); also elsewhere on the board
DATA8: Module5.31 (GPIO12); also elsewhere on the board
DATA9: Module5.37 (GPIO7); also elsewhere on the board
DATA10: Module5.39 (GPIO8); also elsewhere on the board
DATA11: Module5.41 (GPIO25); also elsewhere on the board
DATA12: Module5.45 (GPIO24); also elsewhere on the board
DATA13: Module5.47 (GPIO23); also elsewhere on the board
DATA14: Module5.49 (GPIO18); also elsewhere on the board
DATA15: Module5.51 (GPIO15); also elsewhere on the board
DATA16: Module5.55 (GPIO14); also elsewhere on the board
ETH_LEDG: Module5.15 (Ethernet_nLED3(3.3v)); also elsewhere on the board
ETH_LEDY: Module5.17 (Ethernet_nLED2(3.3v)); also elsewhere on the board
GND: C2.1, C3.1, C8.2, Module5.1 (GND), Module5.2 (GND), Module5.7 (GND), Module5.8 (GND), Module5.13 (GND), Module5.14 (GND), Module5.22 (GND), Module5.23 (GND), Module5.32 (GND), Module5.33 (GND), Module5.42 (GND), Module5.43 (GND), Module5.52 (GND), Module5.53 (GND), Module5.59 (GND), Module5.60 (GND), Module5.65 (GND), Module5.66 (GND), Module5.71 (GND), Module5.74 (GND), Module5.98 (GND), Module5.107 (GND), Module5.108 (GND), Module5.113 (GND), Module5.114 (GND), Module5.119 (GND), Module5.120 (GND), Module5.125 (GND), Module5.126 (GND), Module5.131 (GND), Module5.132 (GND), Module5.137 (GND), Module5.138 (GND), Module5.144 (GND), Module5.150 (GND), Module5.155 (GND), Module5.156 (GND), Module5.161 (GND), Module5.162 (GND), Module5.167 (GND), Module5.168 (GND), Module5.173 (GND), Module5.174 (GND), Module5.179 (GND), Module5.180 (GND), Module5.185 (GND), Module5.186 (GND), Module5.191 (GND), Module5.192 (GND), Module5.197 (GND), Module5.198 (GND), U7.3 (GND); also elsewhere on the board
I2C_SCL: Module5.35 (ID_SC); also elsewhere on the board
I2C_SDA: Module5.36 (ID_SD); also elsewhere on the board
unnamed: D2.1 (K), R2.2
unnamed: D9.1 (K), R11.2
unnamed: Module5.21 (PI_nLED_Activity), R2.1
unnamed: R11.1, U7.4
OUT17: Module5.34 (GPIO5); also elsewhere on the board
OUT18: Module5.38 (GPIO11); also elsewhere on the board
OUT19: Module5.40 (GPIO9); also elsewhere on the board
OUT20: Module5.44 (GPIO10); also elsewhere on the board
OUT21: Module5.46 (GPIO22)
OUT22: Module5.48 (GPIO27)
OUT23: Module5.50 (GPIO17)
OUT24: Module5.54 (GPIO4)
PWR_ON: Module5.95 (nPI_LED_PWR), U7.2
SD_CLK: Module5.57 (SD_CLK); also elsewhere on the board
SD_CMD: Module5.62 (SD_CMD); also elsewhere on the board
SD_DATA0: Module5.63 (SD_DAT0); also elsewhere on the board
SD_DATA1: Module5.67 (SD_DAT1); also elsewhere on the board
SD_DATA2: Module5.69 (SD_DAT2); also elsewhere on the board
SD_DATA3: Module5.61 (SD_DAT3); also elsewhere on the board
SD_DET: Module5.76 (Reserved); also elsewhere on the board
SD_PWR_ON: Module5.75 (SD_PWR_ON); also elsewhere on the board
TRD0_N: Module5.12 (Ethernet_Pair0_P); also elsewhere on the board
TRD0_P: Module5.10 (Ethernet_Pair0_N); also elsewhere on the board
TRD1_N: Module5.6 (Ethernet_Pair1_N); also elsewhere on the board
TRD1_P: Module5.4 (Ethernet_Pair1_P); also elsewhere on the board
TRD2_N: Module5.9 (Ethernet_Pair2_N); also elsewhere on the board
TRD2_P: Module5.11 (Ethernet_Pair2_P); also elsewhere on the board
TRD3_N: Module5.3 (Ethernet_Pair3_P); also elsewhere on the board
TRD3_P: Module5.5 (Ethernet_Pair3_N); also elsewhere on the board
USB2_N: Module5.103 (USB2_N); also elsewhere on the board
USB2_P: Module5.105 (USB2_P); also elsewhere on the board
USBOTG_ID: Module5.101 (USB_OTG_ID); also elsewhere on the board

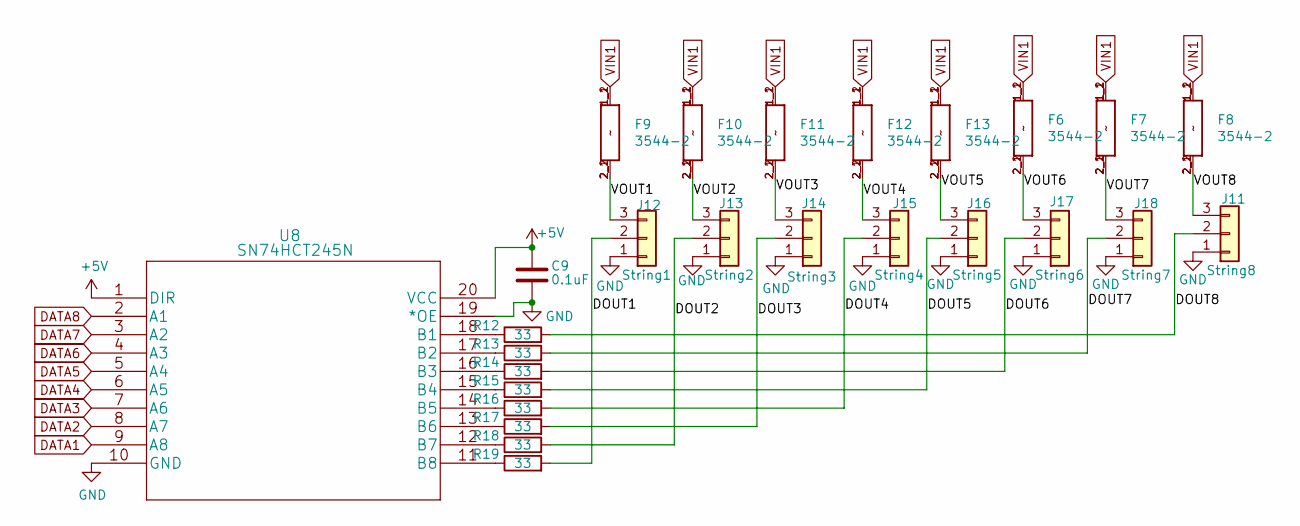
[picture p268: schematic Output1_8.kicad_sch, Pi CM4 16]

Parts:
C9: 0.1uF; C_0603_1608Metric_Pad1.08x0.95mm_HandSolder; MPN CL10B104KB8NNWC; Digi-Key_PN 1276-1935-2-ND
F6, F7, F8, F9, F10, F11, F12, F13: 3544-2; FUSE_3544-2; MPN 3544-2; Digi-Key_PN 36-3544-2-ND
J11: String8; PhoenixContact_MCV_3.81mm_3.5mm_1x03_Vertical; MPN 1843619/OSTTJ0311530; Digi-Key_PN 277-5737-ND/ED10555-ND
J12: String1; PhoenixContact_MCV_3.81mm_3.5mm_1x03_Vertical; MPN 1843619/OSTTJ0311530; Digi-Key_PN 277-5737-ND/ED10555-ND
J13: String2; PhoenixContact_MCV_3.81mm_3.5mm_1x03_Vertical; MPN 1843619/OSTTJ0311530; Digi-Key_PN 277-5737-ND/ED10555-ND
J14: String3; PhoenixContact_MCV_3.81mm_3.5mm_1x03_Vertical; MPN 1843619/OSTTJ0311530; Digi-Key_PN 277-5737-ND/ED10555-ND
J15: String4; PhoenixContact_MCV_3.81mm_3.5mm_1x03_Vertical; MPN 1843619/OSTTJ0311530; Digi-Key_PN 277-5737-ND/ED10555-ND
J16: String5; PhoenixContact_MCV_3.81mm_3.5mm_1x03_Vertical; MPN 1843619/OSTTJ0311530; Digi-Key_PN 277-5737-ND/ED10555-ND
J17: String6; PhoenixContact_MCV_3.81mm_3.5mm_1x03_Vertical; MPN 1843619/OSTTJ0311530; Digi-Key_PN 277-5737-ND/ED10555-ND
J18: String7; PhoenixContact_MCV_3.81mm_3.5mm_1x03_Vertical; MPN 1843619/OSTTJ0311530; Digi-Key_PN 277-5737-ND/ED10555-ND
R12, R13, R14, R15, R16, R17, R18, R19: 33; R_0603_1608Metric_Pad0.98x0.95mm_HandSolder; MPN RC0603FR-0733RL; LCSC C23140
U8: SN74HCT245N; SN74HCT245NSR; MPN SN74HCT245NSR; Digi-Key_PN 296-15849-1-ND

Connections:
+5V: C9.1, U8.1 (DIR), U8.20 (VCC); also elsewhere on the board
/Output 1-8/DOUT1: J12.2, R19.2
/Output 1-8/DOUT2: J13.2, R18.2
/Output 1-8/DOUT3: J14.2, R17.2
/Output 1-8/DOUT4: J15.2, R16.2
/Output 1-8/DOUT5: J16.2, R15.2
/Output 1-8/DOUT6: J17.2, R14.2
/Output 1-8/DOUT7: J18.2, R13.2
/Output 1-8/DOUT8: J11.2, R12.2
/Output 1-8/VOUT1: F9.2_1 (2), F9.2_2 (2), J12.3
/Output 1-8/VOUT2: F10.2_1 (2), F10.2_2 (2), J13.3
/Output 1-8/VOUT3: F11.2_1 (2), F11.2_2 (2), J14.3
/Output 1-8/VOUT4: F12.2_1 (2), F12.2_2 (2), J15.3
/Output 1-8/VOUT5: F13.2_1 (2), F13.2_2 (2), J16.3
/Output 1-8/VOUT6: F6.2_1 (2), F6.2_2 (2), J17.3
/Output 1-8/VOUT7: F7.2_1 (2), F7.2_2 (2), J18.3
/Output 1-8/VOUT8: F8.2_1 (2), F8.2_2 (2), J11.3
DATA1: U8.9 (A8); also elsewhere on the board
DATA2: U8.8 (A7); also elsewhere on the board
DATA3: U8.7 (A6); also elsewhere on the board
DATA4: U8.6 (A5); also elsewhere on the board
DATA5: U8.5 (A4); also elsewhere on the board
DATA6: U8.4 (A3); also elsewhere on the board
DATA7: U8.3 (A2); also elsewhere on the board
DATA8: U8.2 (A1); also elsewhere on the board
GND: C9.2, J11.1, J12.1, J13.1, J14.1, J15.1, J16.1, J17.1, J18.1, U8.10 (GND), U8.19 (*OE); also elsewhere on the board
unnamed: R12.1, U8.18 (B1)
unnamed: R13.1, U8.17 (B2)
unnamed: R14.1, U8.16 (B3)
unnamed: R15.1, U8.15 (B4)
unnamed: R16.1, U8.14 (B5)
unnamed: R17.1, U8.13 (B6)
unnamed: R18.1, U8.12 (B7)
unnamed: R19.1, U8.11 (B8)
VIN1: F6.1_1 (1), F6.1_2 (1), F7.1_1 (1), F7.1_2 (1), F8.1_1 (1), F8.1_2 (1), F9.1_1 (1), F9.1_2 (1), F10.1_1 (1), F10.1_2 (1), F11.1_1 (1), F11.1_2 (1), F12.1_1 (1), F12.1_2 (1), F13.1_1 (1), F13.1_2 (1); also elsewhere on the board
