computergeek1507/PB_16/Pi_CM4_16_SMD/Pi_CM4_16.kicad_pcb

## KiCad design Pi_CM4_16_SMD/Pi_CM4_16.kicad_pcb (continued)

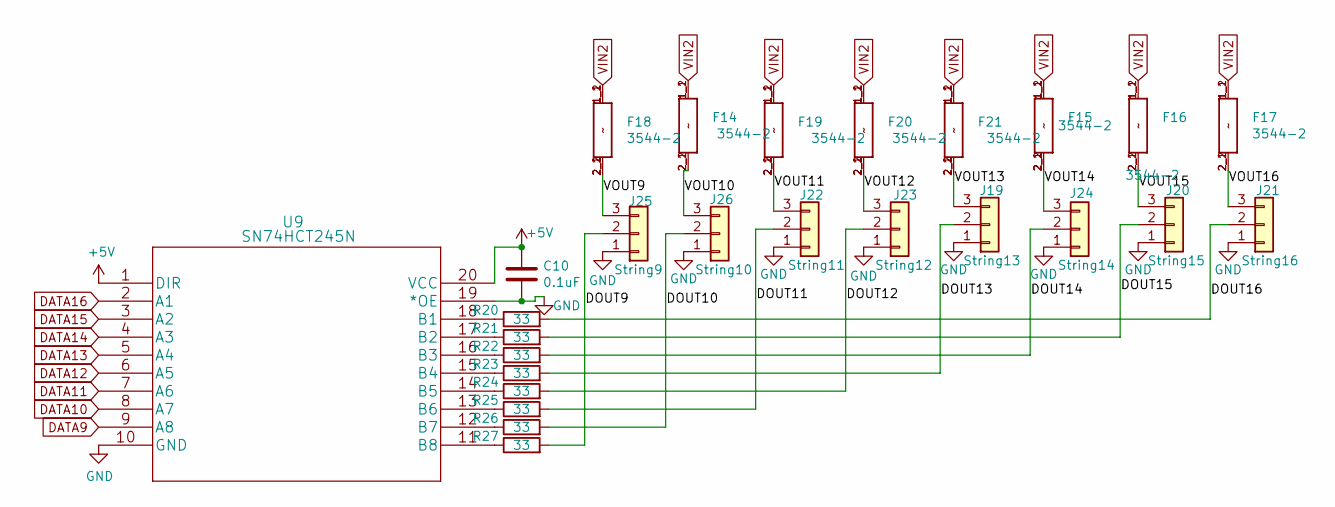
[picture p269: schematic Output9_16.kicad_sch, Pi CM4 16]

Parts:
C10: 0.1uF; C_0603_1608Metric_Pad1.08x0.95mm_HandSolder; MPN CL10B104KB8NNWC; Digi-Key_PN 1276-1935-2-ND
F14, F15, F16, F17, F18, F19, F20, F21: 3544-2; FUSE_3544-2; MPN 3544-2; Digi-Key_PN 36-3544-2-ND
J19: String13; PhoenixContact_MCV_3.81mm_3.5mm_1x03_Vertical; MPN 1843619/OSTTJ0311530; Digi-Key_PN 277-5737-ND/ED10555-ND
J20: String15; PhoenixContact_MCV_3.81mm_3.5mm_1x03_Vertical; MPN 1843619/OSTTJ0311530; Digi-Key_PN 277-5737-ND/ED10555-ND
J21: String16; PhoenixContact_MCV_3.81mm_3.5mm_1x03_Vertical; MPN 1843619/OSTTJ0311530; Digi-Key_PN 277-5737-ND/ED10555-ND
J22: String11; PhoenixContact_MCV_3.81mm_3.5mm_1x03_Vertical; MPN 1843619/OSTTJ0311530; Digi-Key_PN 277-5737-ND/ED10555-ND
J23: String12; PhoenixContact_MCV_3.81mm_3.5mm_1x03_Vertical; MPN 1843619/OSTTJ0311530; Digi-Key_PN 277-5737-ND/ED10555-ND
J24: String14; PhoenixContact_MCV_3.81mm_3.5mm_1x03_Vertical; MPN 1843619/OSTTJ0311530; Digi-Key_PN 277-5737-ND/ED10555-ND
J25: String9; PhoenixContact_MCV_3.81mm_3.5mm_1x03_Vertical; MPN 1843619/OSTTJ0311530; Digi-Key_PN 277-5737-ND/ED10555-ND
J26: String10; PhoenixContact_MCV_3.81mm_3.5mm_1x03_Vertical; MPN 1843619/OSTTJ0311530; Digi-Key_PN 277-5737-ND/ED10555-ND
R20, R21, R22, R23, R24, R25, R26, R27: 33; R_0603_1608Metric_Pad0.98x0.95mm_HandSolder; MPN RC0603FR-0733RL; LCSC C23140
U9: SN74HCT245N; SN74HCT245NSR; MPN SN74HCT245NSR; Digi-Key_PN 296-15849-1-ND

Connections:
+5V: C10.1, U9.1 (DIR), U9.20 (VCC); also elsewhere on the board
/Output 9-16/DOUT9: J25.2, R27.2
/Output 9-16/DOUT10: J26.2, R26.2
/Output 9-16/DOUT11: J22.2, R25.2
/Output 9-16/DOUT12: J23.2, R24.2
/Output 9-16/DOUT13: J19.2, R23.2
/Output 9-16/DOUT14: J24.2, R22.2
/Output 9-16/DOUT15: J20.2, R21.2
/Output 9-16/DOUT16: J21.2, R20.2
/Output 9-16/VOUT9: F18.2_1 (2), F18.2_2 (2), J25.3
/Output 9-16/VOUT10: F14.2_1 (2), F14.2_2 (2), J26.3
/Output 9-16/VOUT11: F19.2_1 (2), F19.2_2 (2), J22.3
/Output 9-16/VOUT12: F20.2_1 (2), F20.2_2 (2), J23.3
/Output 9-16/VOUT13: F21.2_1 (2), F21.2_2 (2), J19.3
/Output 9-16/VOUT14: F15.2_1 (2), F15.2_2 (2), J24.3
/Output 9-16/VOUT15: F16.2_1 (2), F16.2_2 (2), J20.3
/Output 9-16/VOUT16: F17.2_1 (2), F17.2_2 (2), J21.3
DATA9: U9.9 (A8); also elsewhere on the board
DATA10: U9.8 (A7); also elsewhere on the board
DATA11: U9.7 (A6); also elsewhere on the board
DATA12: U9.6 (A5); also elsewhere on the board
DATA13: U9.5 (A4); also elsewhere on the board
DATA14: U9.4 (A3); also elsewhere on the board
DATA15: U9.3 (A2); also elsewhere on the board
DATA16: U9.2 (A1); also elsewhere on the board
GND: C10.2, J19.1, J20.1, J21.1, J22.1, J23.1, J24.1, J25.1, J26.1, U9.10 (GND), U9.19 (*OE); also elsewhere on the board
unnamed: R20.1, U9.18 (B1)
unnamed: R21.1, U9.17 (B2)
unnamed: R22.1, U9.16 (B3)
unnamed: R23.1, U9.15 (B4)
unnamed: R24.1, U9.14 (B5)
unnamed: R25.1, U9.13 (B6)
unnamed: R26.1, U9.12 (B7)
unnamed: R27.1, U9.11 (B8)
VIN2: F14.1_1 (1), F14.1_2 (1), F15.1_1 (1), F15.1_2 (1), F16.1_1 (1), F16.1_2 (1), F17.1_1 (1), F17.1_2 (1), F18.1_1 (1), F18.1_2 (1), F19.1_1 (1), F19.1_2 (1), F20.1_1 (1), F20.1_2 (1), F21.1_1 (1), F21.1_2 (1); also elsewhere on the board

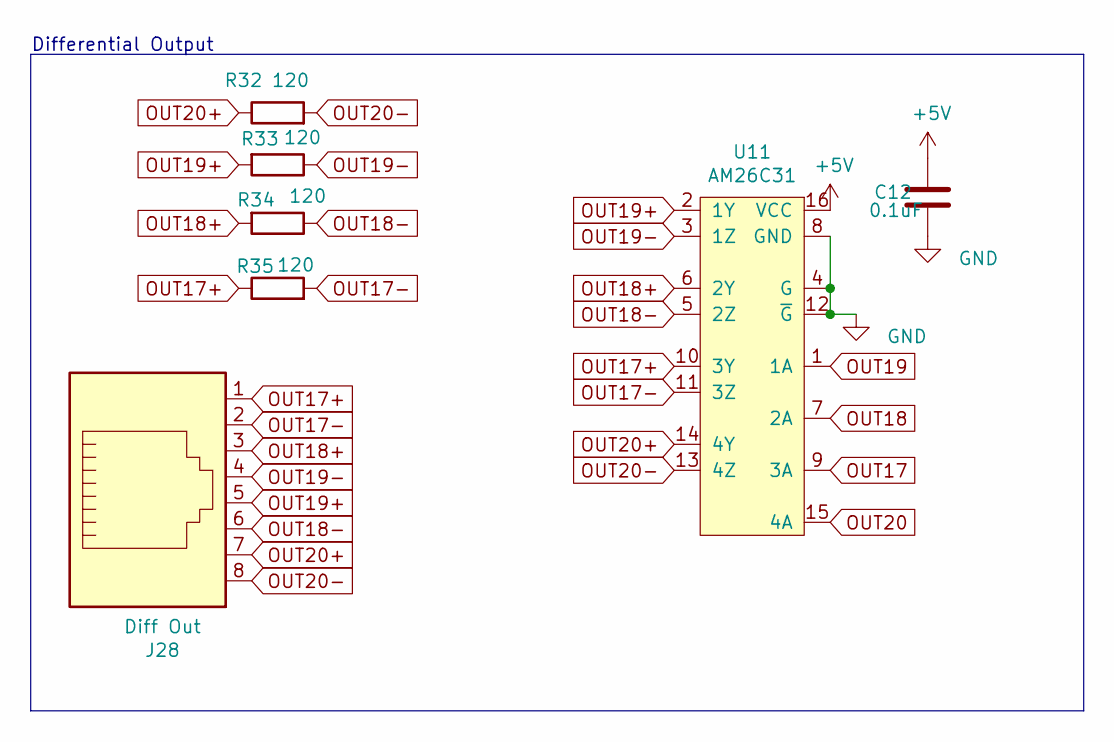
[picture p270: schematic Serial.kicad_sch, Pi CM4 16]

Parts:
C12: 0.1uF; C_0603_1608Metric_Pad1.08x0.95mm_HandSolder; MPN CL10B104KB8NNWC; Digi-Key_PN 1276-1935-2-ND
J28: Diff Out; RJ45_Amphenol_54602-x08_Horizontal; MPN X05ADIWA1DY1022; Digi-Key_PN AE10392-ND
R32, R33, R34, R35: 120; R_0603_1608Metric_Pad0.98x0.95mm_HandSolder; MPN CRGCQ0603F120R; Digi-Key_PN A129677CT-ND
U11: AM26C31; SOIC-16_3.9x9.9mm_P1.27mm; MPN AM26C31IDR; Farnell 4975637

Connections:
+5V: C12.1, U11.16 (VCC); also elsewhere on the board
GND: C12.2, U11.4 (G), U11.8 (GND), U11.12 (~G); also elsewhere on the board
OUT17: U11.9 (3A); also elsewhere on the board
OUT17+: J28.1, R35.1, U11.10 (3Y)
OUT17-: J28.2, R35.2, U11.11 (3Z)
OUT18: U11.7 (2A); also elsewhere on the board
OUT18+: J28.3, R34.2, U11.6 (2Y)
OUT18-: J28.6, R34.1, U11.5 (2Z)
OUT19: U11.1 (1A); also elsewhere on the board
OUT19+: J28.5, R33.2, U11.2 (1Y)
OUT19-: J28.4, R33.1, U11.3 (1Z)
OUT20: U11.15 (4A); also elsewhere on the board
OUT20+: J28.7, R32.1, U11.14 (4Y)
OUT20-: J28.8, R32.2, U11.13 (4Z)

Notes on the sheet:
Differential Output

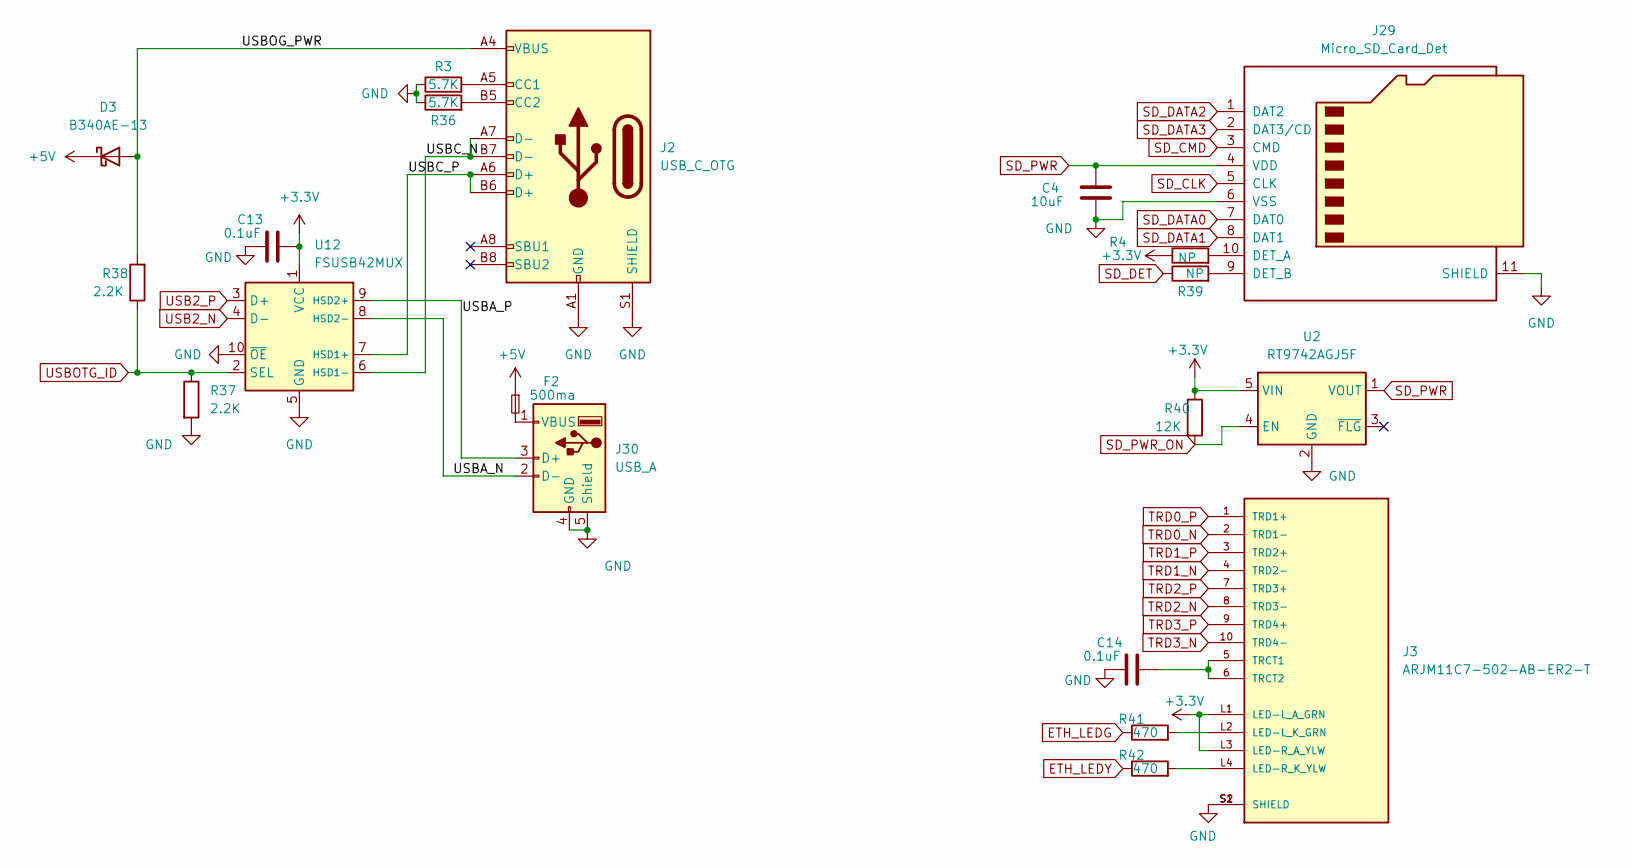
[picture p271: schematic PI_IO.kicad_sch, Pi CM4 16]

Parts:
C4: 10uF; C_0603_1608Metric_Pad1.08x0.95mm_HandSolder
C13, C14: 0.1uF; C_0603_1608Metric_Pad1.08x0.95mm_HandSolder; MPN CL10B104KB8NNWC; Digi-Key_PN 1276-1935-2-ND
D3: B340AE-13; D_SMA
F2: 500ma; Fuse_BelFuse_0ZRE0005FF_L8.3mm_W3.8mm
J2: USB_C_OTG; TYPE-C-31-M-12
J3: ARJM11C7-502-AB-ER2-T; ABRACON_ARJM11C7-502-AB-ER2-T; PARTREV 04.22.2019
J29: Micro_SD_Card_Det; microSD_HC_Molex_104031-0811
J30: USB_A; USB_A_Molex_105057_Vertical
R3, R36: 5.7K; R_0603_1608Metric_Pad0.98x0.95mm_HandSolder
R4, R39: NP; R_0603_1608Metric_Pad0.98x0.95mm_HandSolder
R37, R38: 2.2K; R_0603_1608Metric_Pad0.98x0.95mm_HandSolder
R40: 12K; R_0603_1608Metric_Pad0.98x0.95mm_HandSolder
R41, R42: 470; R_0603_1608Metric_Pad0.98x0.95mm_HandSolder
U2: RT9742AGJ5F; TSOT-23-5
U12: FSUSB42MUX; MSOP-10_3x3mm_P0.5mm

Connections:
+3.3V: C13.1, J3.L1 (LED-L_A_GRN), J3.L3 (LED-R_A_YLW), R4.1, R40.1, U2.5 (VIN), U12.1 (VCC); also elsewhere on the board
+5V: D3.1 (K), F2.1; also elsewhere on the board
/PI IO/USBA_N: J30.2 (D-), U12.8 (HSD2-)
/PI IO/USBA_P: J30.3 (D+), U12.9 (HSD2+)
/PI IO/USBC_N: J2.A7 (D-), J2.B7 (D-), U12.6 (HSD1-)
/PI IO/USBC_P: J2.A6 (D+), J2.B6 (D+), U12.7 (HSD1+)
/PI IO/USBOG_PWR: D3.2 (A), J2.A4 (VBUS), J2.A9 (VBUS), J2.B4 (VBUS), J2.B9 (VBUS), R38.2
ETH_LEDG: R41.1; also elsewhere on the board
ETH_LEDY: R42.1; also elsewhere on the board
GND: C4.1, C13.2, C14.2, J2.A1 (GND), J2.A12 (GND), J2.B1 (GND), J2.B12 (GND), J2.S1 (SHIELD), J3.S1 (SHIELD), J3.S2 (SHIELD), J29.6 (VSS), J29.11 (SHIELD), J30.4 (GND), J30.5 (Shield), R3.1, R36.1, R37.2, U2.2 (GND), U12.5 (GND), U12.10 (~OE); also elsewhere on the board
unnamed: C14.1, J3.5 (TRCT1), J3.6 (TRCT2)
unnamed: F2.2, J30.1 (VBUS)
unnamed: J2.A5 (CC1), R3.2
unnamed: J2.B5 (CC2), R36.2
unnamed: J3.L2 (LED-L_K_GRN), R41.2
unnamed: J3.L4 (LED-R_K_YLW), R42.2
unnamed: J29.9 (DET_B), R39.2
unnamed: J29.10 (DET_A), R4.2
SD_CLK: J29.5 (CLK); also elsewhere on the board
SD_CMD: J29.3 (CMD); also elsewhere on the board
SD_DATA0: J29.7 (DAT0); also elsewhere on the board
SD_DATA1: J29.8 (DAT1); also elsewhere on the board
SD_DATA2: J29.1 (DAT2); also elsewhere on the board
SD_DATA3: J29.2 (DAT3/CD); also elsewhere on the board
SD_DET: R39.1; also elsewhere on the board
SD_PWR: C4.2, J29.4 (VDD), U2.1 (VOUT)
SD_PWR_ON: R40.2, U2.4 (EN); also elsewhere on the board
TRD0_N: J3.2 (TRD1-); also elsewhere on the board
TRD0_P: J3.1 (TRD1+); also elsewhere on the board
TRD1_N: J3.4 (TRD2-); also elsewhere on the board
TRD1_P: J3.3 (TRD2+); also elsewhere on the board
TRD2_N: J3.8 (TRD3-); also elsewhere on the board
TRD2_P: J3.7 (TRD3+); also elsewhere on the board
TRD3_N: J3.10 (TRD4-); also elsewhere on the board
TRD3_P: J3.9 (TRD4+); also elsewhere on the board
USB2_N: U12.4 (D-); also elsewhere on the board
USB2_P: U12.3 (D+); also elsewhere on the board
USBOTG_ID: R37.1, R38.1, U12.2 (SEL); also elsewhere on the board

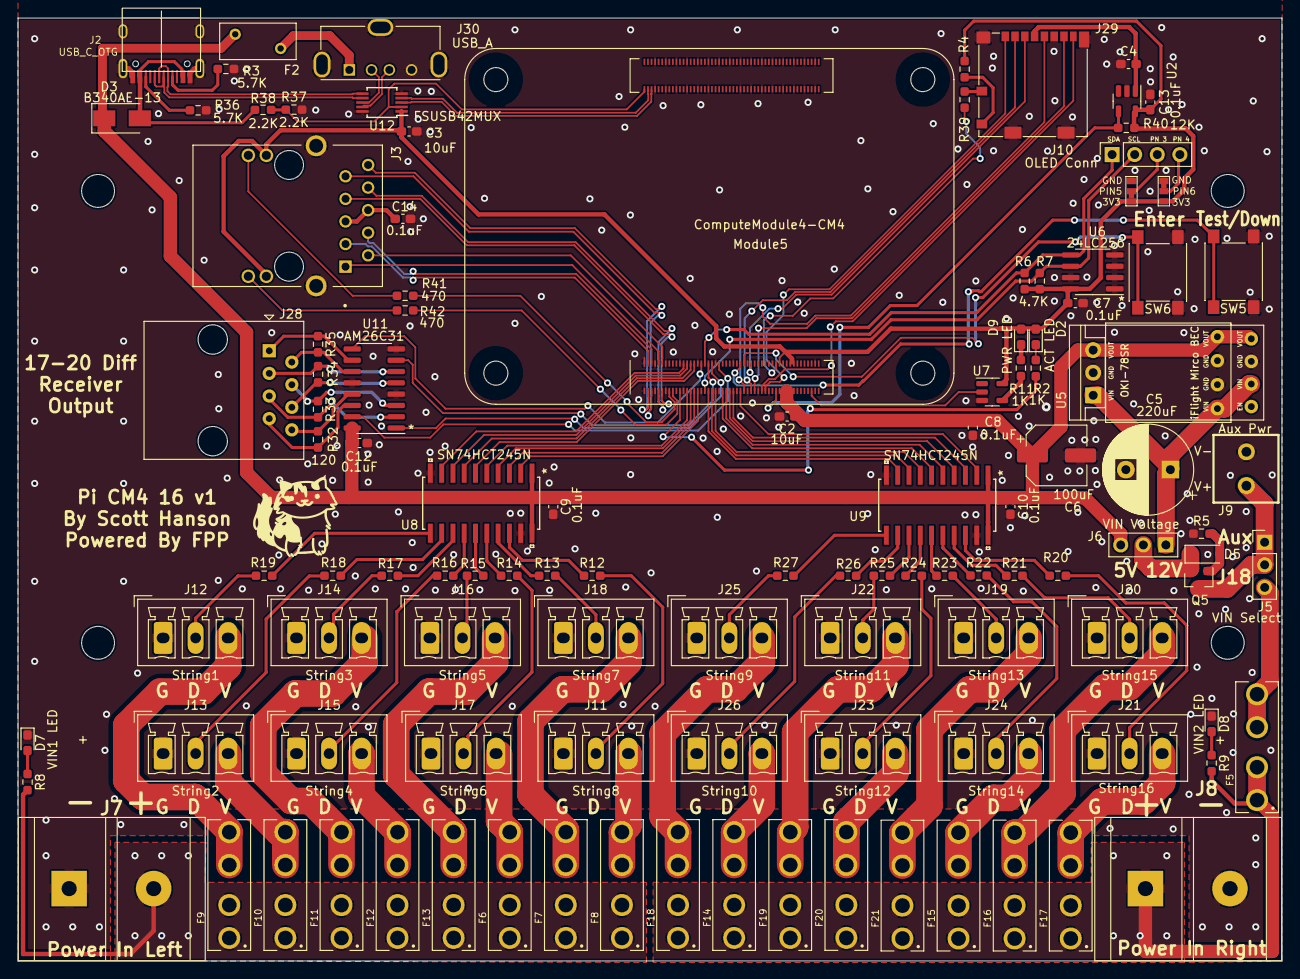
[picture p272: board Pi_CM4_16.kicad_pcb from above]

Board: 2 copper layers, 142.1 x 106.0 mm, 117 parts (0 on the bottom side), 134 nets.
