computergeek1507/PB_16/Input_Pico_SMD/Input_Pico.kicad_pcb

## KiCad design Input_Pico_SMD/Input_Pico.kicad_pcb (2026-03-06)

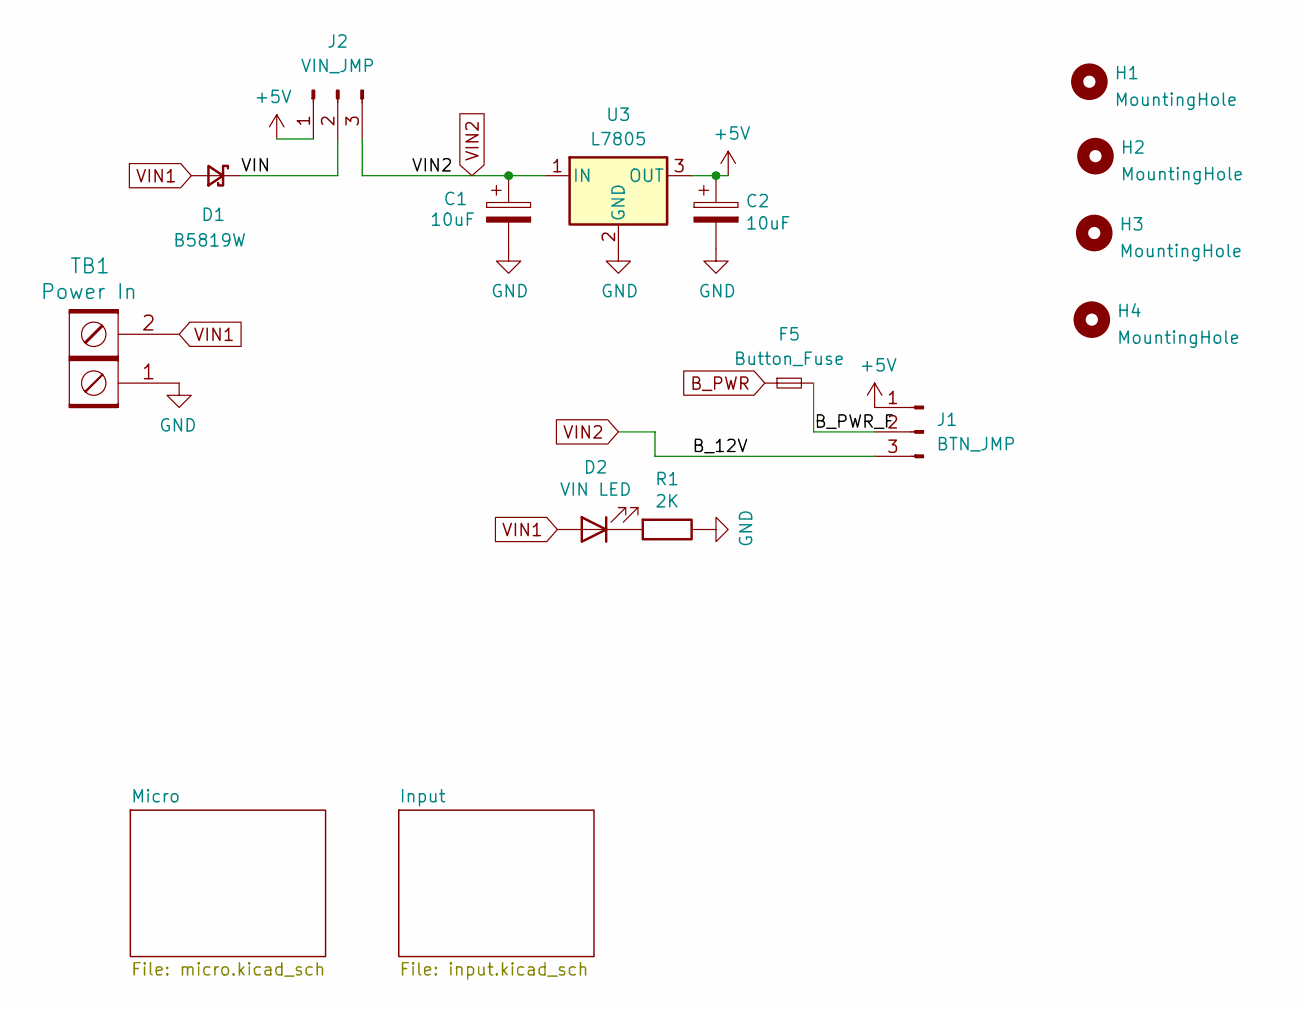
[picture p273: schematic Input_Pico.kicad_sch, Input Pico]

Parts:
C1, C2: 10uF; C_0805_2012Metric; MPN GRM21BR61E106KA73L; Digi-Key_PN 490-5523-1-ND
D1: B5819W; D_SOD-123; MPN B5819W-TP; LCSC_PN C8598
D2: VIN LED; LED_0603_1608Metric; MPN 150080RS75000; Digi-Key_PN 732-4984-1-ND
F5: Button_Fuse; Fuse_0805_2012Metric; LCSC C261938
H1, H2, H3, H4: MountingHole; MountingHole_3.7mm
J1: BTN_JMP; PinHeader_1x03_P2.54mm_Vertical
J2: VIN_JMP; PinHeader_1x03_P2.54mm_Vertical
R1: 2K; R_0603_1608Metric; MPN RC0603FR-071KL; Digi-Key_PN 311-1.00KHRCT-ND
TB1: Power In; TerminalBlock_Phoenix_MKDS-1,5-2-5.08_1x02_P5.08mm_Horizont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; MPN 4DB-P108-02; Digi-Key_PN A98472-ND
U3: L7805; TO-252-2; LCSC_PN C58069

Connections:
+5V: C2.1, J1.1, J2.1, U3.3 (OUT); also elsewhere on the board
/B_PWR_F: F5.2, J1.2
/VIN: D1.1 (K), J2.2
B_PWR: F5.1; also elsewhere on the board
GND: C1.2, C2.2, R1.1, TB1.1, U3.2 (GND); also elsewhere on the board
unnamed: D2.1 (K), R1.2
VIN1: D1.2 (A), D2.2 (A), TB1.2
VIN2: C1.1, J1.3, J2.3, U3.1 (IN)

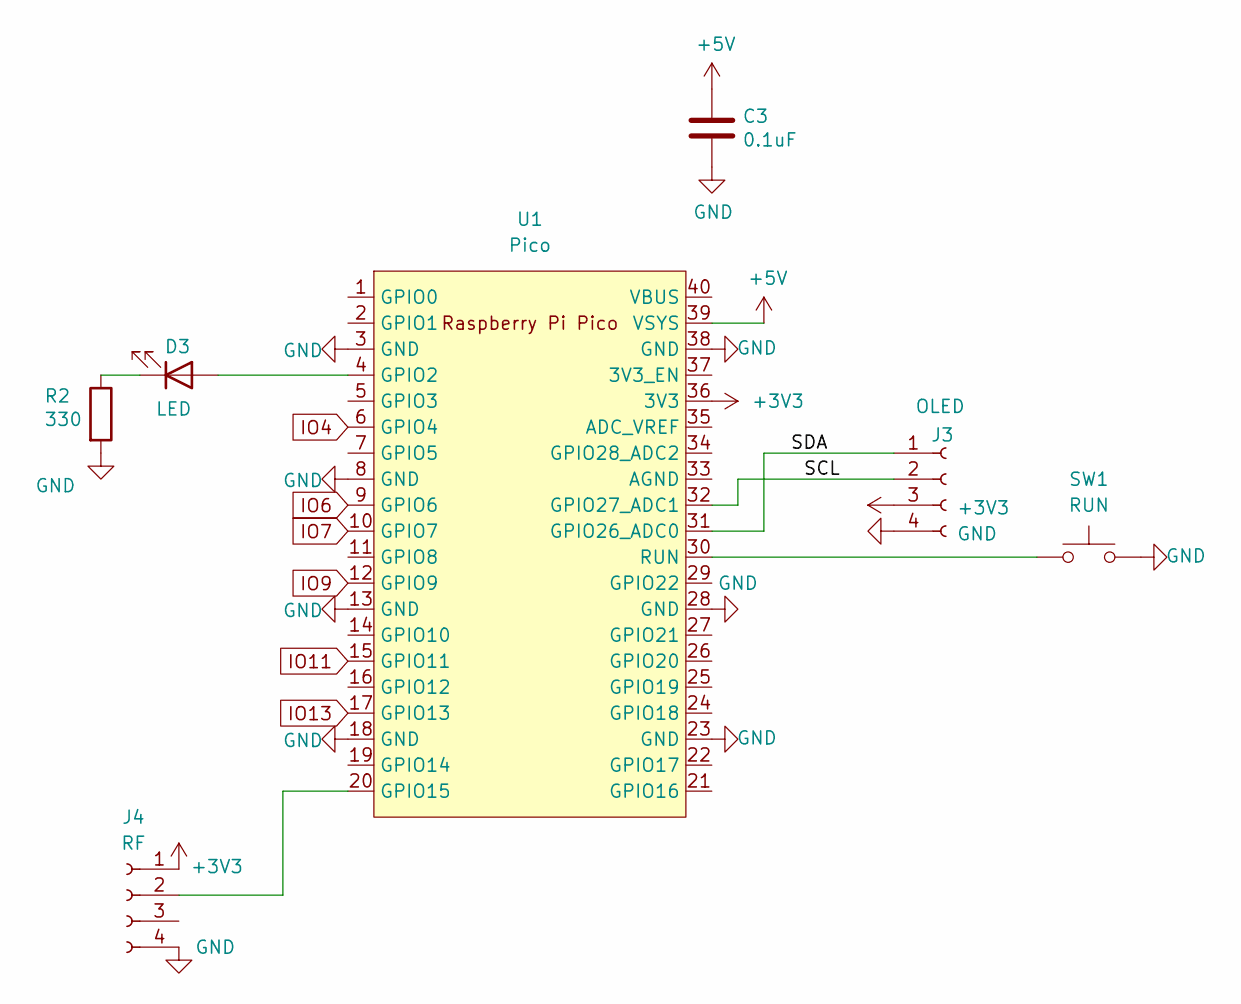
[picture p274: schematic micro.kicad_sch, Input Pico]

Parts:
C3: 0.1uF; C_0603_1608Metric; MPN CL10B104KB8NNWC; Digi-Key_PN 1276-1935-2-ND
D3: LED; LED_0603_1608Metric; MPN 150080RS75000; Digi-Key_PN 732-4984-1-ND
J3: OLED; OLED-SSD1306-128X64-I2C-THT; MPN PPTC041LFBN-RC; Digi-Key_PN S7002-ND
J4: RF; PinSocket_1x04_P2.54mm_Vertical
R2: 330; R_0603_1608Metric; MPN RMCF0603FT220R; Digi-Key_PN RMCF0603FT220RTR-ND
SW1: RUN; SW_PUSH_6mm; MPN PTS645SL50SMTR92 LFS; Digi-Key_PN CKN9088CT-ND
U1: Pico; RPi_Pico_W5500_SMD_TH

Connections:
+3V3: J3.3, J4.1, U1.36 (3V3); also elsewhere on the board
+5V: C3.1, U1.39 (VSYS); also elsewhere on the board
/Micro/SCL: J3.2, U1.32 (GPIO27_ADC1)
/Micro/SDA: J3.1, U1.31 (GPIO26_ADC0)
GND: C3.2, J3.4, J4.4, R2.2, SW1.2, U1.3 (GND), U1.8 (GND), U1.13 (GND), U1.18 (GND), U1.23 (GND), U1.28 (GND), U1.38 (GND); also elsewhere on the board
IO4: U1.6 (GPIO4); also elsewhere on the board
IO6: U1.9 (GPIO6); also elsewhere on the board
IO7: U1.10 (GPIO7); also elsewhere on the board
IO9: U1.12 (GPIO9); also elsewhere on the board
IO11: U1.15 (GPIO11); also elsewhere on the board
IO13: U1.17 (GPIO13); also elsewhere on the board
unnamed: D3.2 (A), U1.4 (GPIO2)
unnamed: D3.1 (K), R2.1
unnamed: J4.2, U1.20 (GPIO15)
unnamed: SW1.1, U1.30 (RUN)

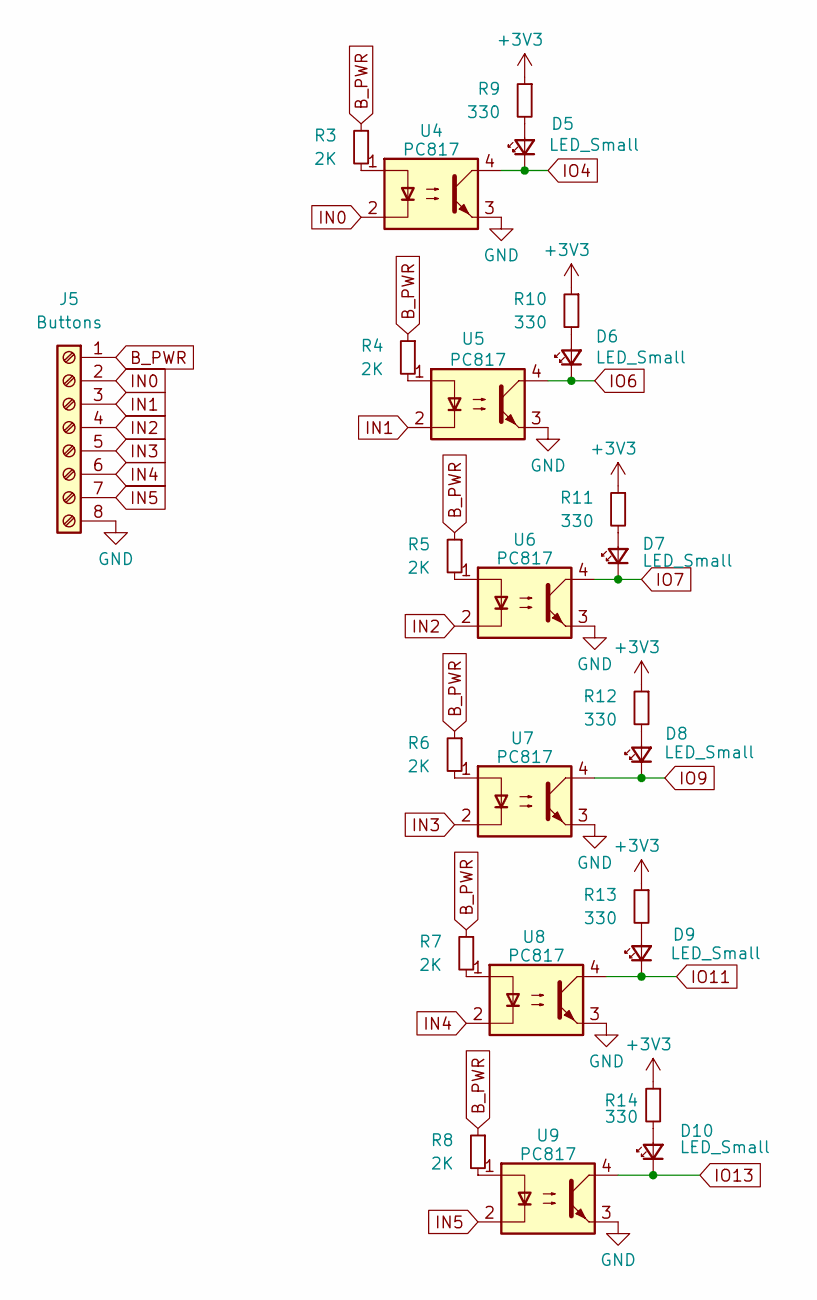
[picture p275: schematic input.kicad_sch, Input Pico]

Parts:
D5, D6, D7, D8, D9, D10: LED_Small; LED_0603_1608Metric; LCSC_PN C2286
J5: Buttons; PhoenixContact_MCV_1,5_8-G-5.08_1x08_P5.08mm_Vertical
R3, R4, R5, R6, R7, R8: 2K; R_0603_1608Metric; LCSC_PN C21190
R9, R10, R11, R12, R13, R14: 330; R_0603_1608Metric; LCSC_PN C22962
U4, U5, U6, U7, U8, U9: PC817; DIP-4_W7.62mm; LCSC_PN C5350

Connections:
+3V3: R9.1, R10.1, R11.1, R12.1, R13.1, R14.1; also elsewhere on the board
B_PWR: J5.1, R3.1, R4.1, R5.1, R6.1, R7.1, R8.1; also elsewhere on the board
GND: J5.8, U4.3, U5.3, U6.3, U7.3, U8.3, U9.3; also elsewhere on the board
IN0: J5.2, U4.2
IN1: J5.3, U5.2
IN2: J5.4, U6.2
IN3: J5.5, U7.2
IN4: J5.6, U8.2
IN5: J5.7, U9.2
IO4: D5.1 (K), U4.4; also elsewhere on the board
IO6: D6.1 (K), U5.4; also elsewhere on the board
IO7: D7.1 (K), U6.4; also elsewhere on the board
IO9: D8.1 (K), U7.4; also elsewhere on the board
IO11: D9.1 (K), U8.4; also elsewhere on the board
IO13: D10.1 (K), U9.4; also elsewhere on the board
unnamed: D5.2 (A), R9.2
unnamed: D6.2 (A), R10.2
unnamed: D7.2 (A), R11.2
unnamed: D8.2 (A), R12.2
unnamed: D9.2 (A), R13.2
unnamed: D10.2 (A), R14.2
unnamed: R3.2, U4.1
unnamed: R4.2, U5.1
unnamed: R5.2, U6.1
unnamed: R6.2, U7.1
unnamed: R7.2, U8.1
unnamed: R8.2, U9.1

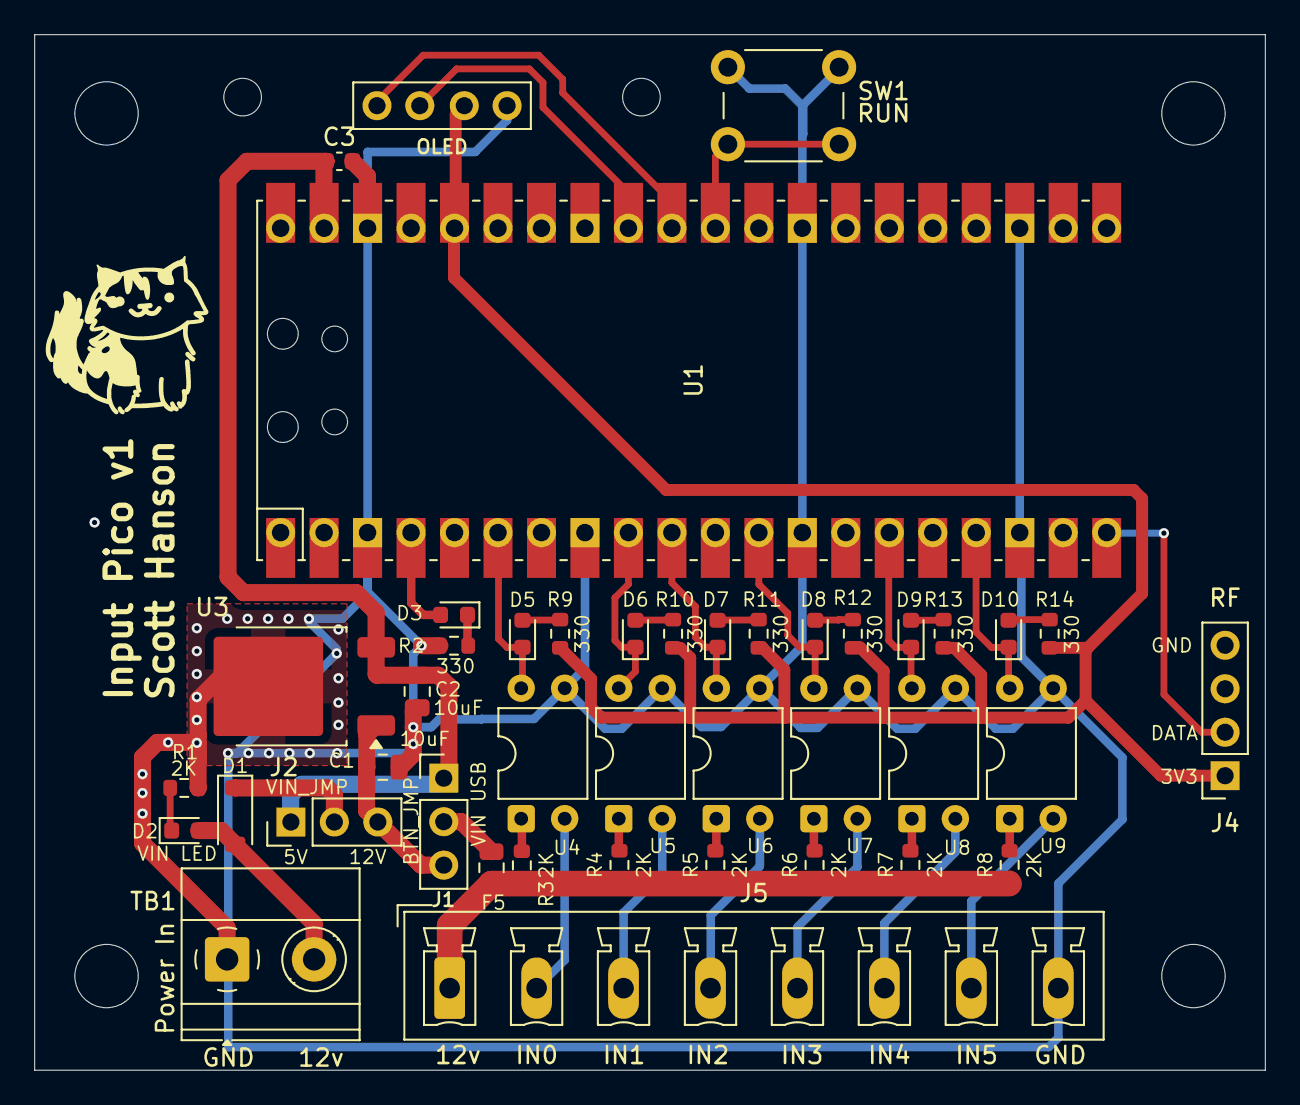
[picture p276: board Input_Pico.kicad_pcb from above]

Board: 2 copper layers, 71.9 x 60.5 mm, 46 parts (0 on the bottom side), 39 nets.
