computergeek1507/PB_16/Pi_Zero_W_2_SMD/Pi_Zero_W_2.kicad_pcb

## KiCad design Pi_Zero_W_2_SMD/Pi_Zero_W_2.kicad_pcb (2026-03-06)

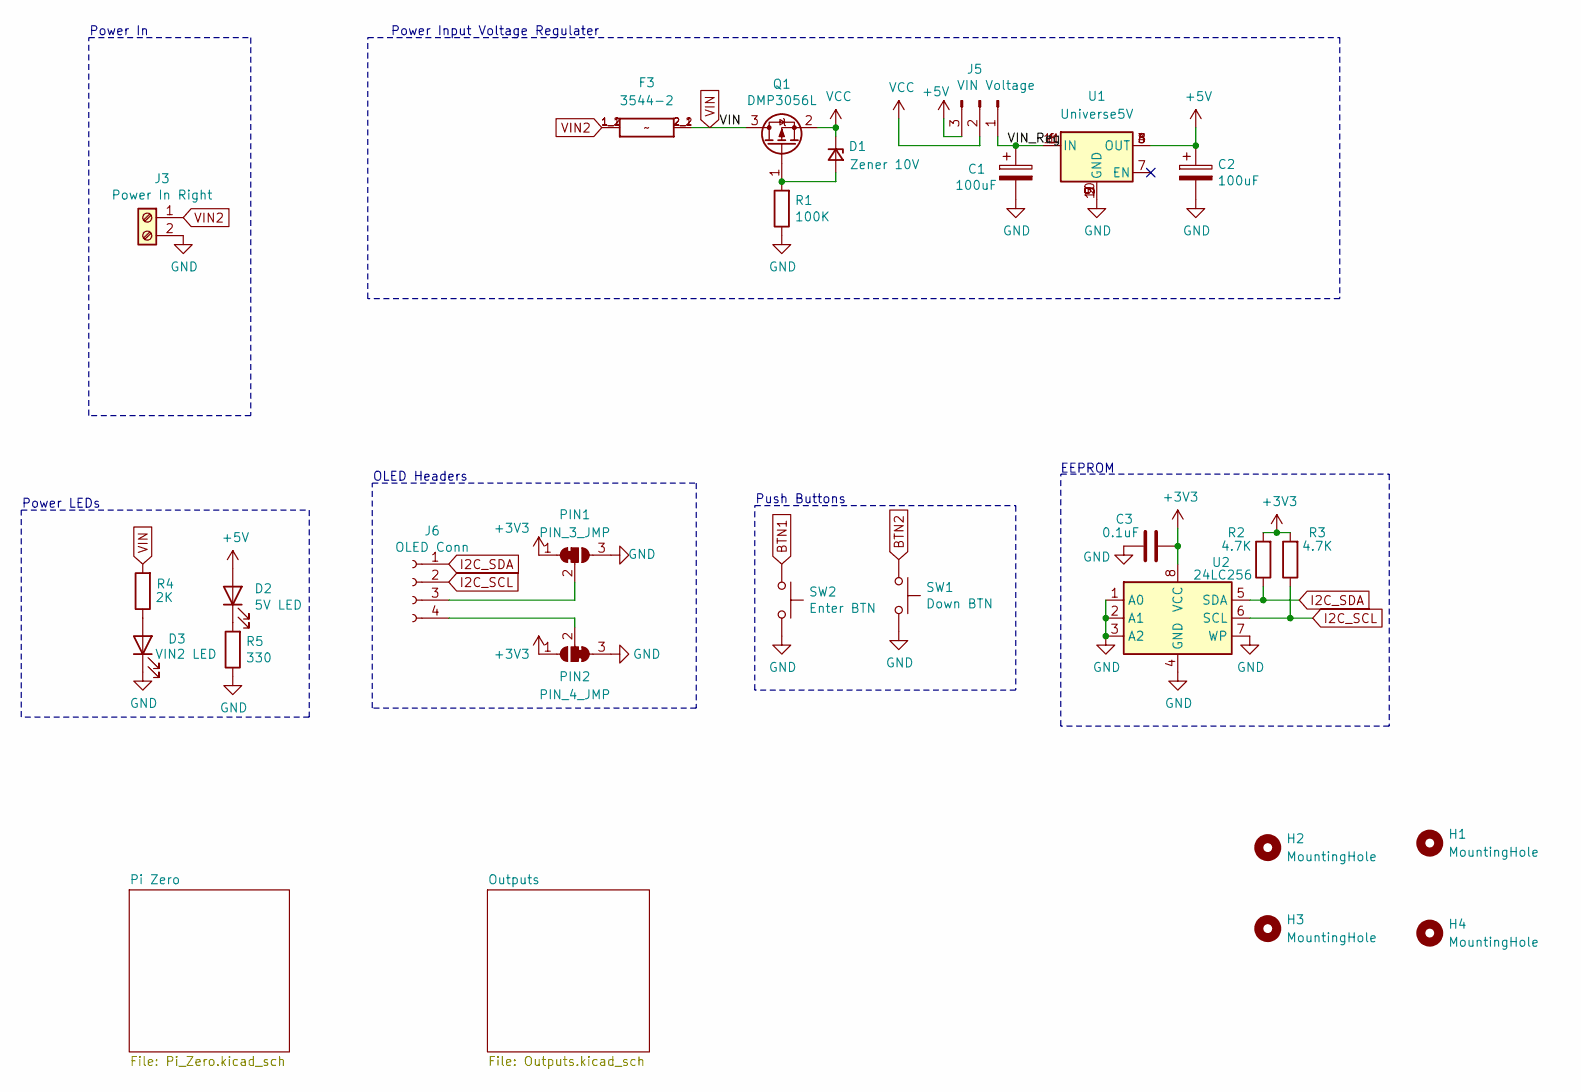
[picture p277: schematic Pi_Zero_W_2.kicad_sch, Pi Zero W 2]

Parts:
C1, C2: 100uF; CP_Elec_6.3x5.4_Nichicon; MPN UWX1C101MCL1GB; Digi-Key_PN 493-2105-1-ND
C3: 0.1uF; C_0603_1608Metric; MPN CL10B104KB8NNWC; Digi-Key_PN 1276-1935-2-ND
D1: Zener 10V; D_SOD-123; MPN MMSZ5240B-7-F; Digi-Key_PN MMSZ5240B-FDICT-ND
D2: 5V LED; LED_0603_1608Metric; MPN LTST-C190KRKT; Digi-Key_PN 160-1436-2-ND
D3: VIN2 LED; LED_0603_1608Metric; MPN LTST-C190KRKT; Digi-Key_PN 160-1436-2-ND
F3: 3544-2; FUSE_3544-2; MPN 3544-2; Digi-Key_PN 36-3544-2-ND
H1, H2, H3, H4: MountingHole; MountingHole_3.7mm
J3: Power In Right; BARRIER_BLOCK_1ROW_2POS_P8.26MM; LCSC C306200
J5: VIN Voltage; PinHeader_1x03_P2.54mm_Vertical; MPN 61300311121; Digi-Key_PN 732-5316-ND
J6: OLED Conn; PinSocket_1x04_P2.54mm_Vertical; MPN PPTC041LFBN-RC; Digi-Key_PN S7002-ND
PIN1: PIN_3_JMP; SolderJumper-3_P1mm_Bridged12
PIN2: PIN_4_JMP; SolderJumper-3_P1mm_Bridged23
Q1: DMP3056L; SOT-23; MPN DMP3056L-7; Digi-Key_PN DMP3056L-7DICT-ND
R1: 100K; R_0603_1608Metric; MPN RT0603BRD07100KL; Digi-Key_PN YAG1235CT-ND
R2, R3: 4.7K; R_0603_1608Metric; MPN RC0603JR-074K7L; Digi-Key_PN 311-4.7KGRCT-ND
R4: 2K; R_0603_1608Metric; LCSC C4190
R5: 330; R_0603_1608Metric; LCSC C23138
SW1: Down BTN; SW_Push_1P1T_NO_6x6mm_H9.5mm; MPN PTS645SL50SMTR92 LFS; Digi-Key_PN CKN9088CT-ND
SW2: Enter BTN; SW_Push_1P1T_NO_6x6mm_H9.5mm; MPN PTS645SL50SMTR92 LFS; Digi-Key_PN CKN9088CT-ND
U1: Universe5V; Universal_5V_Horizontal
U2: 24LC256; SOIC-8_3.9x4.9mm_P1.27mm; MPN 24LC256T-I/SN; Digi-Key_PN 24LC256T-I/SNCT-ND

Connections:
+3V3: C3.1, PIN1.1 (A), PIN2.1 (A), R2.2, R3.2, U2.8 (VCC); also elsewhere on the board
+5V: C2.1, D2.2 (A), J5.3, U1.3 (OUT), U1.4 (OUT), U1.8 (OUT); also elsewhere on the board
/VIN_Reg: C1.1, J5.1, U1.1 (IN), U1.6 (IN), U1.11 (IN)
BTN1: SW2.1; also elsewhere on the board
BTN2: SW1.1; also elsewhere on the board
GND: C1.2, C2.2, C3.2, D3.1 (K), J3.2, PIN1.3 (B), PIN2.3 (B), R1.1, R5.1, SW1.2, SW2.2, U1.2 (GND), U1.5 (GND), U1.9 (GND), U1.10 (GND), U2.1 (A0), U2.2 (A1), U2.3 (A2), U2.4 (GND), U2.7 (WP); also elsewhere on the board
I2C_SCL: J6.2, R3.1, U2.6 (SCL); also elsewhere on the board
I2C_SDA: J6.1, R2.1, U2.5 (SDA); also elsewhere on the board
unnamed: D1.2 (A), Q1.1 (G), R1.2
unnamed: D2.1 (K), R5.2
unnamed: D3.2 (A), R4.1
unnamed: J6.3, PIN1.2 (C)
unnamed: J6.4, PIN2.2 (C)
VCC: D1.1 (K), J5.2, Q1.2 (S)
VIN: F3.2_1 (2), F3.2_2 (2), Q1.3 (D), R4.2
VIN2: F3.1_1 (1), F3.1_2 (1), J3.1; also elsewhere on the board

Notes on the sheet:
Power LEDs
Power In
OLED Headers
Push Buttons
Power Input Voltage Regulater
EEPROM

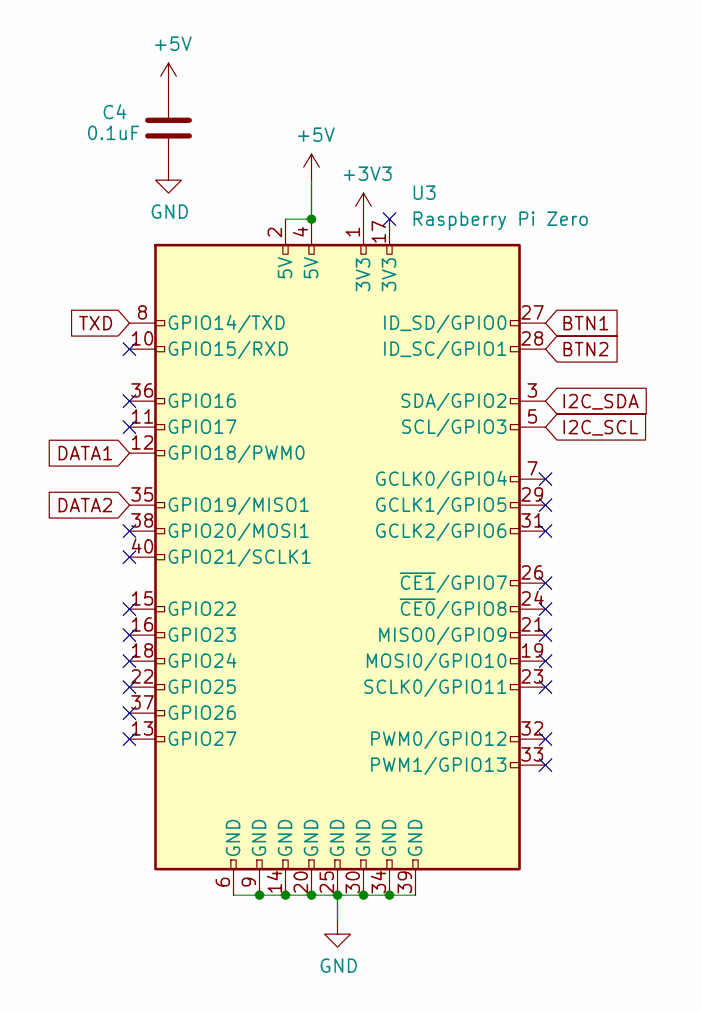
[picture p278: schematic Pi_Zero.kicad_sch, Pi Zero W 2]

Parts:
C4: 0.1uF; C_0603_1608Metric; MPN CL10B104KB8NNWC; Digi-Key_PN 1276-1935-2-ND
U3: Raspberry Pi Zero; Raspberry_Pi_Zero_Socketed_THT_FaceDown_MountingHoles

Connections:
+3V3: U3.1 (3V3); also elsewhere on the board
+5V: C4.1, U3.2 (5V), U3.4 (5V); also elsewhere on the board
BTN1: U3.27 (ID_SD/GPIO0); also elsewhere on the board
BTN2: U3.28 (ID_SC/GPIO1); also elsewhere on the board
DATA1: U3.12 (GPIO18/PWM0); also elsewhere on the board
DATA2: U3.35 (GPIO19/MISO1); also elsewhere on the board
GND: C4.2, U3.6 (GND), U3.9 (GND), U3.14 (GND), U3.20 (GND), U3.25 (GND), U3.30 (GND), U3.34 (GND), U3.39 (GND); also elsewhere on the board
I2C_SCL: U3.5 (SCL/GPIO3); also elsewhere on the board
I2C_SDA: U3.3 (SDA/GPIO2); also elsewhere on the board
TXD: U3.8 (GPIO14/TXD); also elsewhere on the board

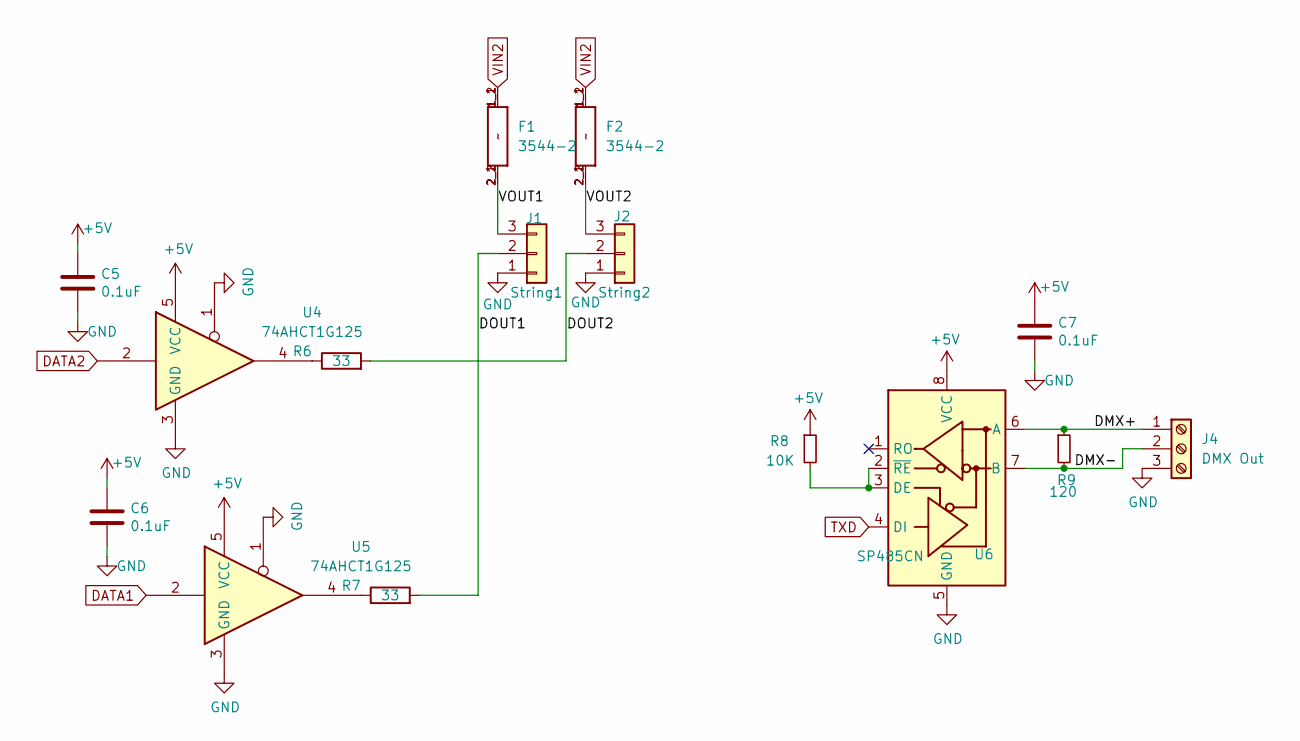
[picture p279: schematic Outputs.kicad_sch, Pi Zero W 2]

Parts:
C5, C6, C7: 0.1uF; C_0603_1608Metric; MPN CL10B104KB8NNWC; Digi-Key_PN 1276-1935-2-ND
F1, F2: 3544-2; FUSE_3544-2; MPN 3544-2; Digi-Key_PN 36-3544-2-ND
J1: String1; PhoenixContact_MCV_3.81mm_3.5mm_1x03_Vertical; MPN 1843619/OSTTJ0311530; Digi-Key_PN 277-5737-ND/ED10555-ND
J2: String2; PhoenixContact_MCV_3.81mm_3.5mm_1x03_Vertical; MPN 1843619/OSTTJ0311530; Digi-Key_PN 277-5737-ND/ED10555-ND
J4: DMX Out; TerminalBlock_Phoenix_MKDS-1,5-3-5.08_1x03_P5.08mm_Horizont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
R6, R7: 33; R_0603_1608Metric; MPN RC0603FR-0733RL; LCSC C23140
R8: 10K; R_0603_1608Metric; LCSC C25804
R9: 120; R_0603_1608Metric; LCSC C22790
U4, U5: 74AHCT1G125; TSOP-5_1.65x3.05mm_P0.95mm; LCSC C7484
U6: SP485CN; SOIC-8_3.9x4.9mm_P1.27mm; MPN SP485CN-L/TR; Digi-Key_PN 1016-1825-1-ND

Connections:
+5V: C5.1, C6.1, C7.1, R8.1, U4.5 (VCC), U5.5 (VCC), U6.8 (VCC); also elsewhere on the board
/Outputs/DMX+: J4.1, R9.1, U6.6 (A)
/Outputs/DMX-: J4.2, R9.2, U6.7 (B)
/Outputs/DOUT1: J1.2, R7.2
/Outputs/DOUT2: J2.2, R6.2
/Outputs/VOUT1: F1.2_1 (2), F1.2_2 (2), J1.3
/Outputs/VOUT2: F2.2_1 (2), F2.2_2 (2), J2.3
DATA1: U5.2; also elsewhere on the board
DATA2: U4.2; also elsewhere on the board
GND: C5.2, C6.2, C7.2, J1.1, J2.1, J4.3, U4.1, U4.3 (GND), U5.1, U5.3 (GND), U6.5 (GND); also elsewhere on the board
unnamed: R6.1, U4.4
unnamed: R7.1, U5.4
unnamed: R8.2, U6.2 (~RE), U6.3 (DE)
TXD: U6.4 (DI); also elsewhere on the board
VIN2: F1.1_1 (1), F1.1_2 (1), F2.1_1 (1), F2.1_2 (1); also elsewhere on the board
