computergeek1507/PB_16/Pi_Zero_W_2_SMD/Pi_Zero_W_2.kicad_pcb

## KiCad design Pi_Zero_W_2_SMD/Pi_Zero_W_2.kicad_pcb (continued)

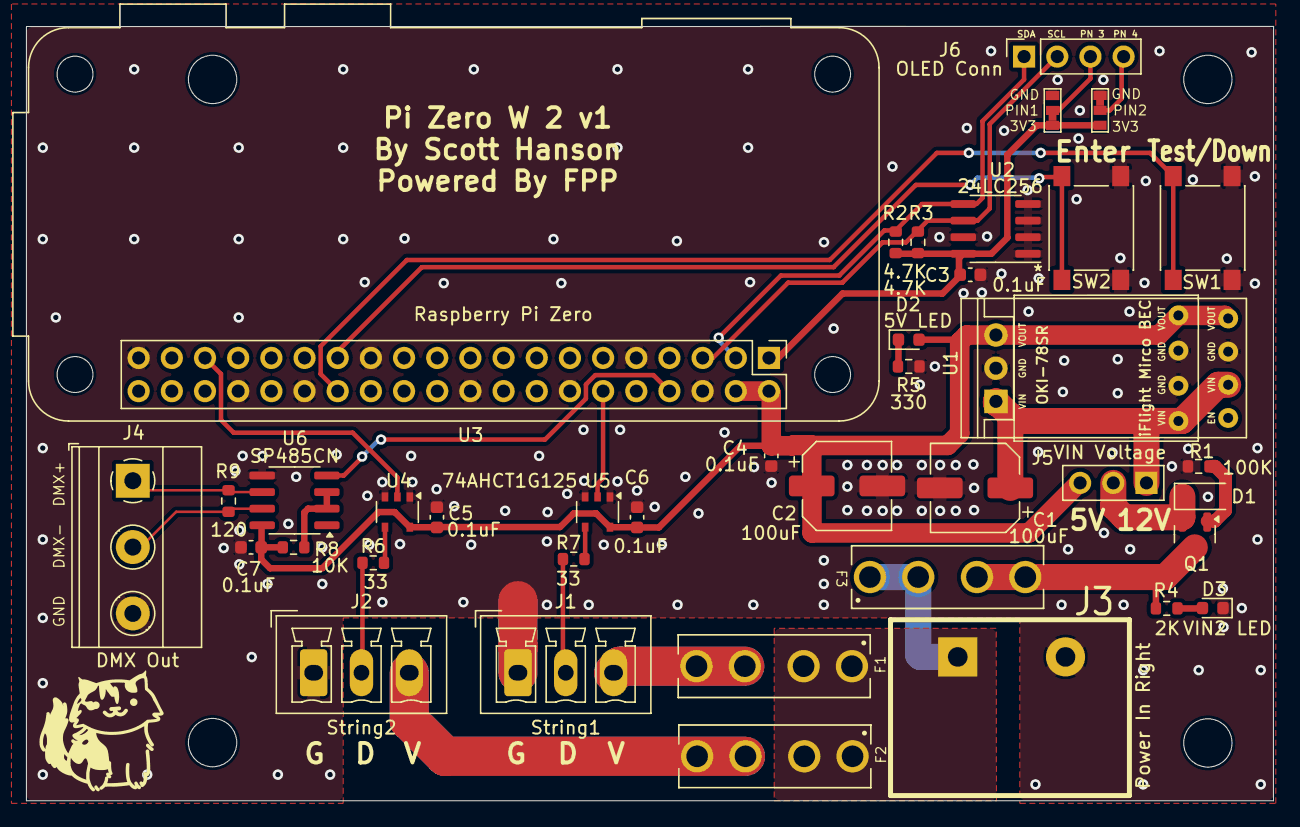
[picture p280: board Pi_Zero_W_2.kicad_pcb from above]

Board: 2 copper layers, 95.5 x 59.3 mm, 43 parts (1 on the bottom side), 28 nets.
