computergeek1507/PB_16/Quad_Diff_Out/Quad_Diff_Out.kicad_pcb

## KiCad design Quad_Diff_Out/Quad_Diff_Out.kicad_pcb (2026-03-06)

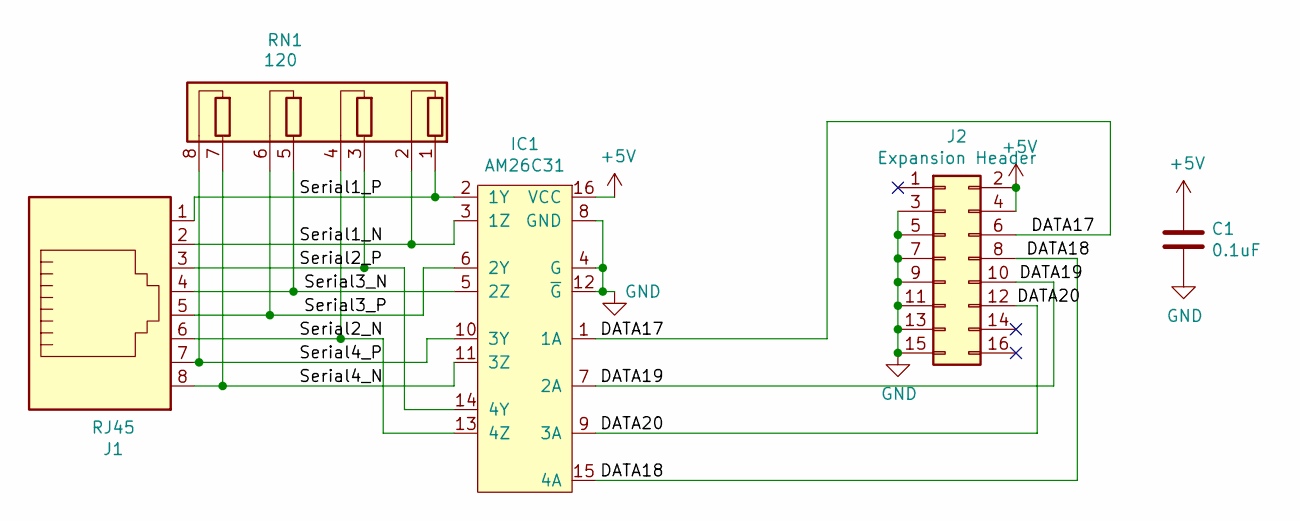
[picture p281: schematic Quad_Diff_Out.sch, Quad Diff]

Parts:
C1: 0.1uF; C_Rect_L7.0mm_W2.0mm_P5.00mm; Digikey PN 478-7336-1-ND
IC1: AM26C31; DIP-16_W7.62mm; Farnell 4975637
J1: RJ45; RJ45_Amphenol_54602-x08_Horizontal; Digikey PN AE10392-ND
J2: Expansion Header; PinSocket_2x08_P2.54mm_Vertical; Digikey PN S7111-ND
RN1: 120; R_Array_SIP8; Digikey PN 4608X-2-121LF-ND

Connections:
+5V: C1.1, IC1.16 (VCC), J2.2, J2.4
/DATA17: IC1.1 (1A), J2.6
/DATA18: IC1.15 (4A), J2.8
/DATA19: IC1.7 (2A), J2.10
/DATA20: IC1.9 (3A), J2.12
/Serial1_N: IC1.3 (1Z), J1.2, RN1.2 (R1.2)
/Serial1_P: IC1.2 (1Y), J1.1, RN1.1 (R1.1)
/Serial2_N: IC1.13 (4Z), J1.6, RN1.4 (R2.2)
/Serial2_P: IC1.14 (4Y), J1.3, RN1.3 (R2.1)
/Serial3_N: IC1.5 (2Z), J1.4, RN1.5 (R3.1)
/Serial3_P: IC1.6 (2Y), J1.5, RN1.6 (R3.2)
/Serial4_N: IC1.11 (3Z), J1.8, RN1.7 (R4.1)
/Serial4_P: IC1.10 (3Y), J1.7, RN1.8 (R4.2)
GND: C1.2, IC1.4 (G), IC1.8 (GND), IC1.12 (~G), J2.3, J2.5, J2.7, J2.9, J2.11, J2.13, J2.15

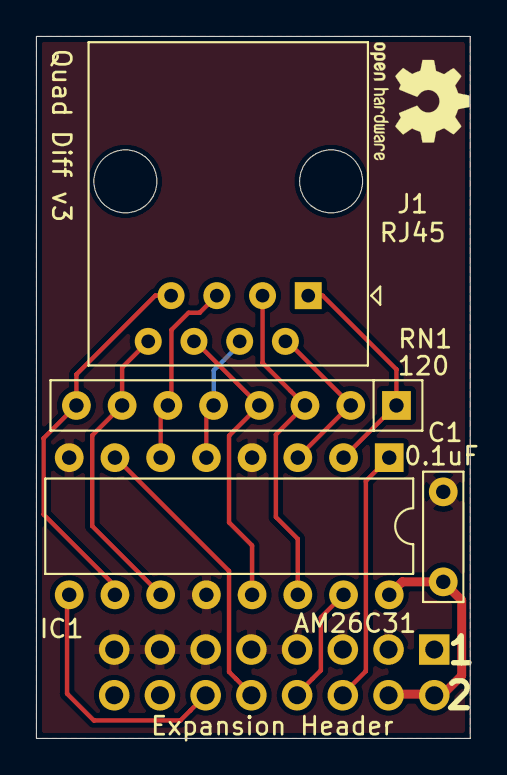
[picture p282: board Quad_Diff_Out.kicad_pcb from above]

Board: 2 copper layers, 24.1 x 39.0 mm, 5 parts (1 on the bottom side), 14 nets.
