computergeek1507/PB_16/PB_16_E682_Serial/PB_16.kicad_pcb

## KiCad design PB_16_E682_Serial/PB_16.kicad_pcb (2026-03-06)

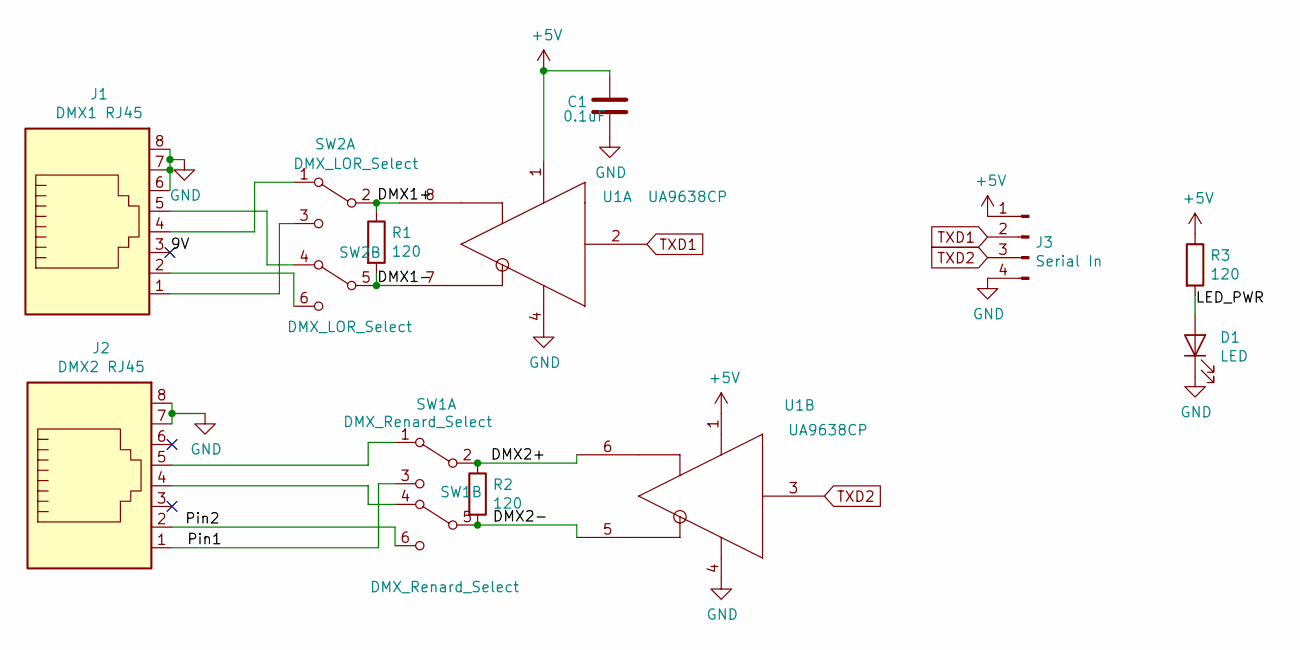
[picture p283: schematic PB_16.sch, PB16 E682 Serial]

Parts:
C1: 0.1uF; C_Rect_L7.0mm_W2.0mm_P5.00mm; MPN SR215C104KARTR1; Digi-Key_PN 478-7336-1-ND
D1: LED; LED_D3.0mm_Clear; MPN 151031VS06000; Digi-Key_PN 732-5008-ND
J1: DMX1 RJ45; RJ45_Amphenol_54602-x08_Horizontal; MPN A-2014-2-4-R; Digi-Key_PN AE10392-ND
J2: DMX2 RJ45; RJ45_Amphenol_54602-x08_Horizontal; MPN A-2014-2-4-R; Digi-Key_PN AE10392-ND
J3: Serial In; PinHeader_1x04_P2.54mm_Vertical; MPN 61300411121; Digi-Key_PN 732-5317-ND
R1, R2, R3: 120; R_Axial_DIN0207_L6.3mm_D2.5mm_P7.62mm_Horizontal; MPN CF14JT120R; Digi-Key_PN CF14JT120RCT-ND
SW1: DMX_Renard_Select; SW_CuK_JS202011CQN_DPDT_Straight; MPN JS202011CQN; Digi-Key_PN 401-2001-ND
SW2: DMX_LOR_Select; SW_CuK_JS202011CQN_DPDT_Straight; MPN JS202011CQN; Digi-Key_PN 401-2001-ND
U1: UA9638CP; DIP-8_W7.62mm; MPN UA9638CP; Digi-Key_PN 296-15059-5-ND

Connections:
+5V: C1.1, J3.1, R3.1, U1.1 (VCC)
/9V: J1.3
/DMX1+: R1.1, SW2.2 (B), U1.8 (OUTB)
/DMX1-: R1.2, SW2.5 (B), U1.7 (OUTA)
/DMX2+: R2.1, SW1.2 (B), U1.6 (OUTB)
/DMX2-: R2.2, SW1.5 (B), U1.5 (OUTA)
/LED_PWR: D1.2 (A), R3.2
/Pin1: J2.1, SW1.3 (C)
/Pin2: J2.2, SW1.6 (C)
GND: C1.2, D1.1 (K), J1.6, J1.7, J1.8, J2.7, J2.8, J3.4, U1.4 (GND)
unnamed: J1.1, SW2.3 (C)
unnamed: J1.2, SW2.6 (C)
unnamed: J1.4, SW2.1 (A)
unnamed: J1.5, SW2.4 (A)
unnamed: J2.4, SW1.4 (A)
unnamed: J2.5, SW1.1 (A)
TXD1: J3.2, U1.2 (IN)
TXD2: J3.3, U1.3 (IN)

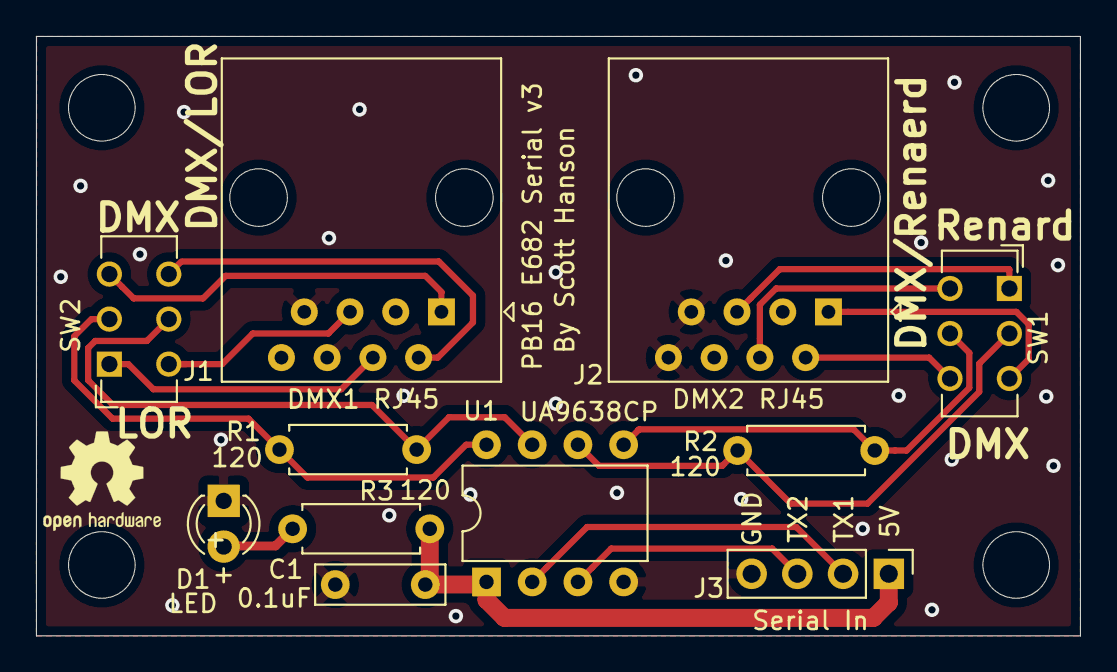
[picture p284: board PB_16_E682_Serial/PB_16.kicad_pcb from above]

Board: 2 copper layers, 58.0 x 33.3 mm, 11 parts (0 on the bottom side), 17 nets.
