computergeek1507/PB_16/Pi_Adapter/Pi_Adapter.kicad_pcb

## KiCad design Pi_Adapter/Pi_Adapter.kicad_pcb (2026-03-06)

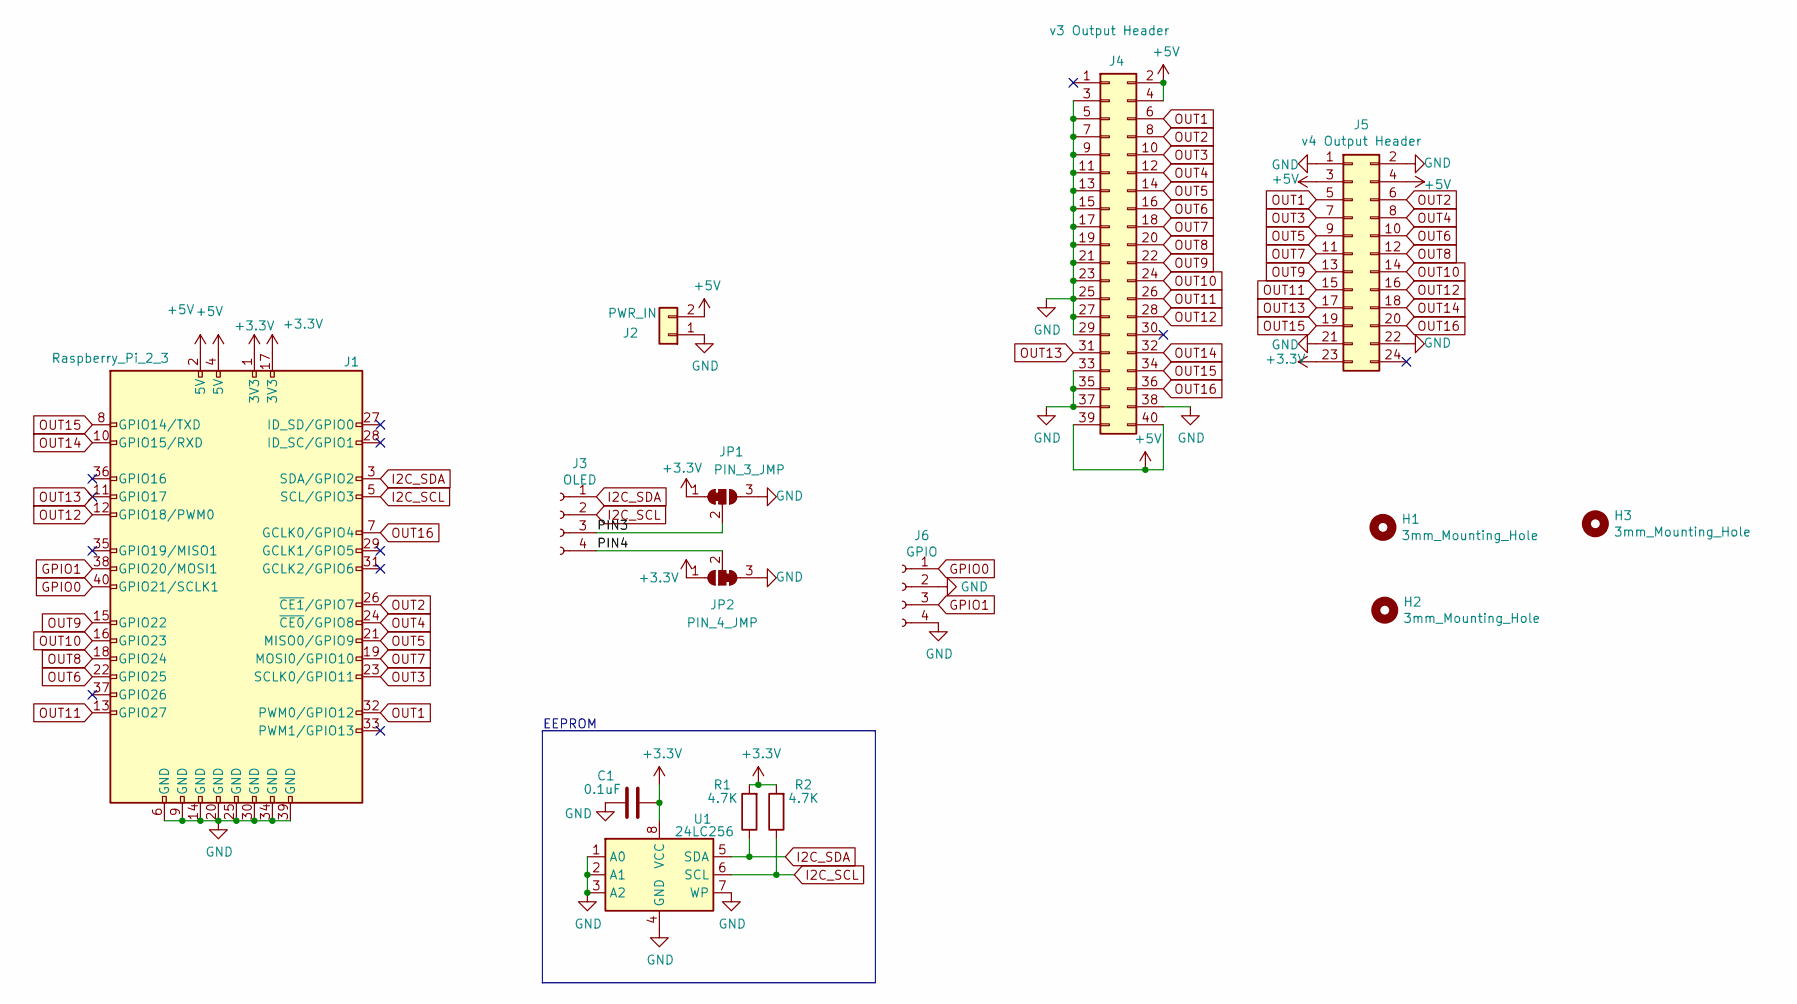
[picture p285: schematic Pi_Adapter.kicad_sch, Pi Expansion]

Parts:
C1: 0.1uF; C_0603_1608Metric_Pad1.08x0.95mm_HandSolder; MPN CL10B104KB8NNWC; Digi-Key_PN 1276-1935-2-ND
H1, H2, H3: 3mm_Mounting_Hole; MountingHole_3mm
J1: Raspberry_Pi_2_3; PinSocket_2x20_P2.54mm_Vertical; MPN PPPC202LFBN-RC; Digi-Key_PN S7123-ND
J2: PWR_IN; TerminalBlock_Phoenix_MKDS-1,5-2_1x02_P5.00mm_Horizontal; MPN ED2675-ND; Digi-Key_PN OSTT7020150
J3: OLED; PinSocket_1x04_P2.54mm_Vertical; MPN PPTC041LFBN-RC; Digi-Key_PN S7002-ND
J4: v3 Output Header; IDC-Header_2x20_P2.54mm_Vertical; MPN SBH11-PBPC-D20-ST-BK; Digi-Key_PN S9175-ND
J5: v4 Output Header; IDC-Header_2x12_P2.54mm_Vertical; MPN Z-S311024S1GK1A; Digi-Key_PN ED10525-ND
J6: GPIO; PinSocket_1x04_P2.54mm_Vertical; MPN PPTC041LFBN-RC; Digi-Key_PN S7002-ND
JP1: PIN_3_JMP; SolderJumper-3_P1mm_Bridged12
JP2: PIN_4_JMP; SolderJumper-3_P1mm_Bridged23
R1, R2: 4.7K; R_0603_1608Metric_Pad0.98x0.95mm_HandSolder; MPN RC0603JR-074K7L; Digi-Key_PN 311-4.7KGRCT-ND
U1: 24LC256; SOIC-8_3.9x4.9mm_P1.27mm; MPN 24LC256T-I/SN; Digi-Key_PN 24LC256T-I/SNCT-ND

Connections:
+3V3: C1.1, J1.1 (3V3), J1.17 (3V3), J5.23, JP1.1 (A), JP2.1 (A), R1.2, R2.2, U1.8 (VCC)
+5V: J1.2 (5V), J1.4 (5V), J2.2, J4.2, J4.4, J4.39, J4.40, J5.3, J5.4
/PIN3: J3.3, JP1.2 (C)
/PIN4: J3.4, JP2.2 (C)
GND: C1.2, J1.6 (GND), J1.9 (GND), J1.14 (GND), J1.20 (GND), J1.25 (GND), J1.30 (GND), J1.34 (GND), J1.39 (GND), J2.1, J4.3, J4.5, J4.7, J4.9, J4.11, J4.13, J4.15, J4.17, J4.19, J4.21, J4.23, J4.25, J4.27, J4.29, J4.33, J4.35, J4.37, J4.38, J5.1, J5.2, J5.21, J5.22, J6.2, J6.4, JP1.3 (B), JP2.3 (B), U1.1 (A0), U1.2 (A1), U1.3 (A2), U1.4 (GND), U1.7 (WP)
GPIO0: J1.40 (GPIO21/SCLK1), J6.1
GPIO1: J1.38 (GPIO20/MOSI1), J6.3
I2C_SCL: J1.5 (SCL/GPIO3), J3.2, R2.1, U1.6 (SCL)
I2C_SDA: J1.3 (SDA/GPIO2), J3.1, R1.1, U1.5 (SDA)
OUT1: J1.32 (PWM0/GPIO12), J4.6, J5.5
OUT2: J1.26 (~CE1/GPIO7), J4.8, J5.6
OUT3: J1.23 (SCLK0/GPIO11), J4.10, J5.7
OUT4: J1.24 (~CE0/GPIO8), J4.12, J5.8
OUT5: J1.21 (MISO0/GPIO9), J4.14, J5.9
OUT6: J1.22 (GPIO25), J4.16, J5.10
OUT7: J1.19 (MOSI0/GPIO10), J4.18, J5.11
OUT8: J1.18 (GPIO24), J4.20, J5.12
OUT9: J1.15 (GPIO22), J4.22, J5.13
OUT10: J1.16 (GPIO23), J4.24, J5.14
OUT11: J1.13 (GPIO27), J4.26, J5.15
OUT12: J1.12 (GPIO18/PWM0), J4.28, J5.16
OUT13: J1.11 (GPIO17), J4.31, J5.17
OUT14: J1.10 (GPIO15/RXD), J4.32, J5.18
OUT15: J1.8 (GPIO14/TXD), J4.34, J5.19
OUT16: J1.7 (GCLK0/GPIO4), J4.36, J5.20

Notes on the sheet:
EEPROM

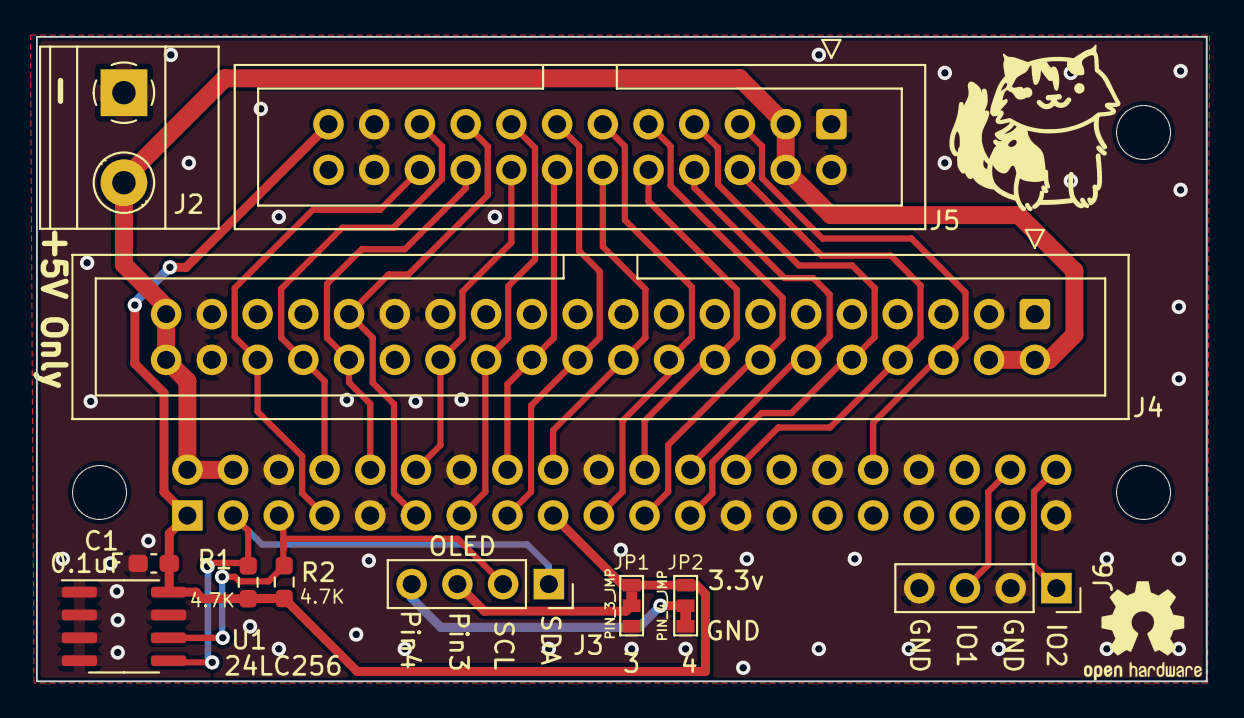
[picture p286: board Pi_Adapter.kicad_pcb from above]

Board: 2 copper layers, 65.0 x 35.8 mm, 15 parts (1 on the bottom side), 25 nets.
